acwright/6502/Software/Programs/VH Bricks/README.md

VH Bricks
=========

Displays brick pattern on VERA Layer 0 using the VERA Helper.

Inspired By / Modifed From: [https://www.8bitcoding.com/p/tiles-in-assembly-i-basics.html](https://www.8bitcoding.com/p/tiles-in-assembly-i-basics.html)

Install:

    brew install cc65

Build:

    make

View:

    make view
