acwright/6502/Software/Carts/SC Echo Flow Control/README.md

SC Echo Interrupt
=================

Serial Card echo example using interrupts.

Install:

    brew install cc65

Build:

    make

View:

    make view

Burn EEPROM:

    make eeprom
