acwright/6502/Software/Carts/IB SNES Transmit/README.md

IB SNES Transmit
================

Transmits raw SNES controller data from Input Board to Serial Card.

Adapted from: [https://www.pagetable.com/?p=1365](https://www.pagetable.com/?p=1365)

Install:

    brew install cc65

Build:

    make

View:

    make view

Burn EEPROM:

    make eeprom
