acwright/6502/Software/Carts/IB Mouse Transmit/README.md

IB Mouse Transmit
=================

Transmits raw PS/2 mouse data from Input Board to Serial Card.

Install:

    brew install cc65

Build:

    make

View:

    make view

Burn EEPROM:

    make eeprom
