acwright/6502/Software/Carts/IB Keyboard Transmit/README.md

IB Keyboard Transmit
====================

Transmits raw PS/2 keyboard scancodes from Input Board to Serial Card.

Install:

    brew install cc65

Build:

    make

View:

    make view

Burn EEPROM:

    make eeprom
