acwright/6502/Assets/Documents/Keypad Mapping/Keypad Mapping.pdf

## 6502 KeyPAD MAPPING

| PA4 | PA3 | PA2 | PA1 | PA0 | Key
$00 | 0 | 0 | 0 | 0 | 0 | ◀
$01 | 0 | 0 | 0 | 0 | 1 | 1
$02 | 0 | 0 | 0 | 1 | 0 | 2
$03 | O | 0 | 0 | 1 | 1 | 3
$04 | 0 | 0 | 1 | 0 | 0 | 4
$05 | 0 | 0 | 1 | 0 | 1 | 5
$06 | 0 | 0 | 1 | 1 | 0 | 6
$07 | 0 | 0 | 1 | 1 | 1 | 7
$08 | 0 | 1 | 0 | 0 | 0 | 8
$09 | 0 | 1 | 0 | 0 | 1 | 9
$0A | 0 | 1 | 0 | 1 | 0 | 0
$0B | 0 | 1 | 0 | 1 | 1 | ▶
$0C | 0 | 1 | 1 | 0 | 0 | F
$0D | 0 | 1 | 1 | 0 | 1 | E
$0E | 0 | 1 | 1 | 1 | 0 | D
$0F | 0 | 1 | 1 | 1 | 1 | C
$10 | 1 | 0 | 0 | 0 | 0 | Esc
$11 | 1 | 0 | 0 | 0 | 1 | Ins
$12 | 1 | 0 | 0 | 1 | 0 | pgup
$13 | 1 | 0 | 0 | 1 | 1 | A
$14 | 1 | 0 | 1 | 0 | 0 | ▲
$15 | 1 | 0 | 1 | 0 | 1 | Del
$16 | 1 | 0 | 1 | 1 | 0 | pgdn
$17 | 1 | 0 | 1 | 1 | 1 | B
