acwright/6502/Assets/Documents/Characters/Character Map.pdf

## 6502 CHARACTER MAP

| 0 | 1 | 2 | 3 | 4 | 5 | 6 | 7 | 8 | 9 | A | B | C | D | E | F

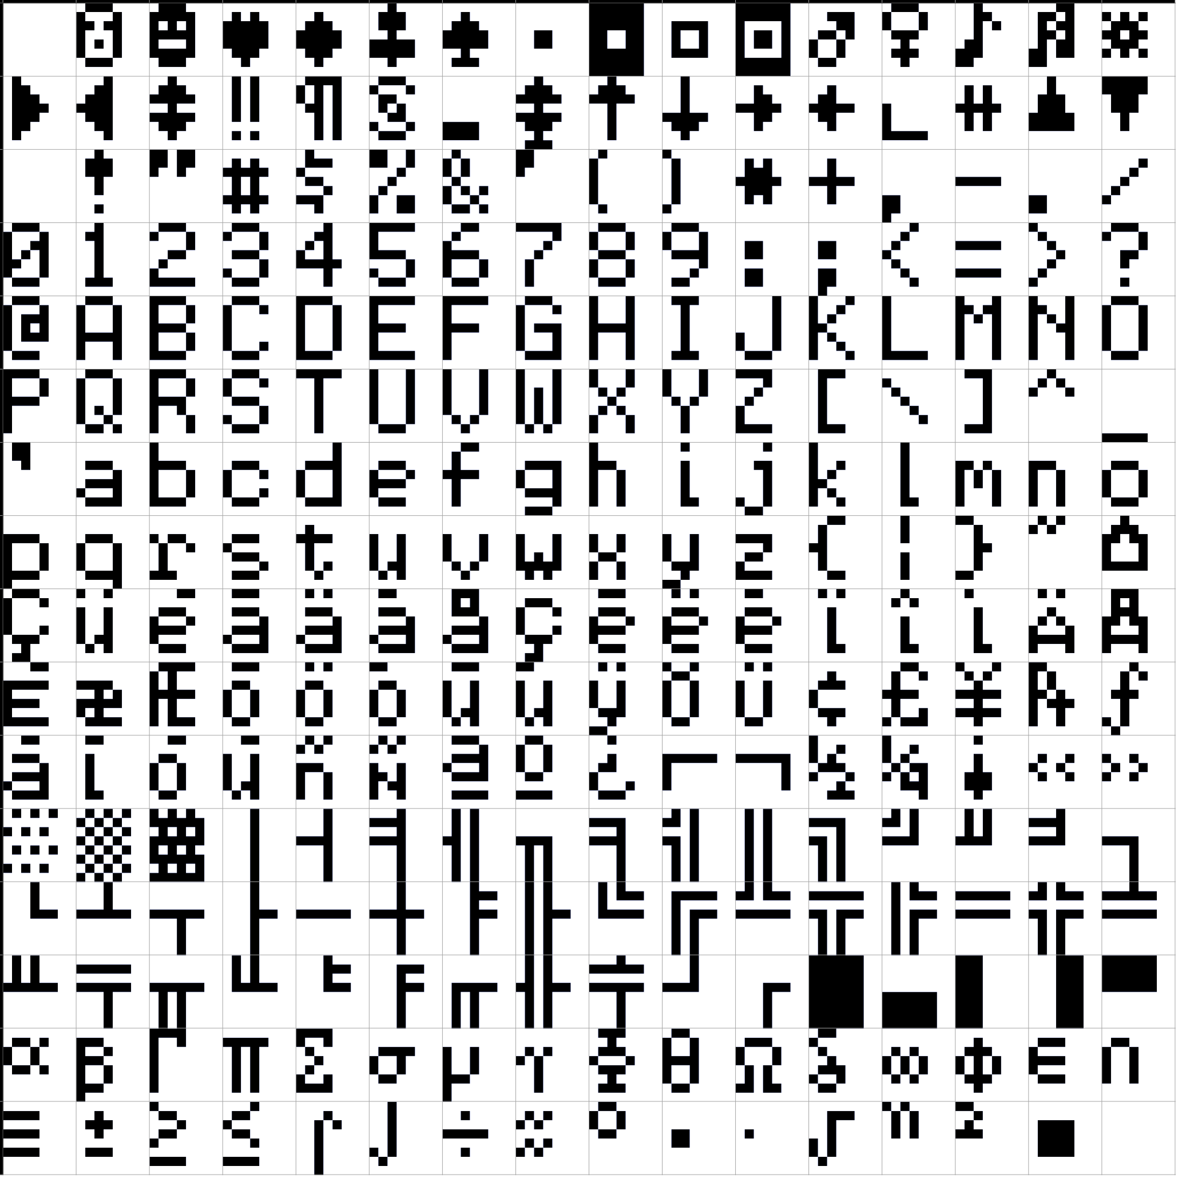
[picture p2: figure]

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
