acwright/6502/Assets/Documents/Characters/Character Set 4x.png

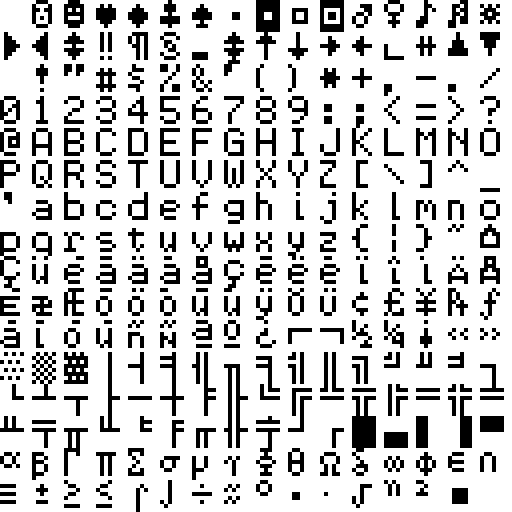
Assets/Documents/Characters/Character Set 4x.png
