acwright/6502/Assets/Documents/Connectors/Connectors.png

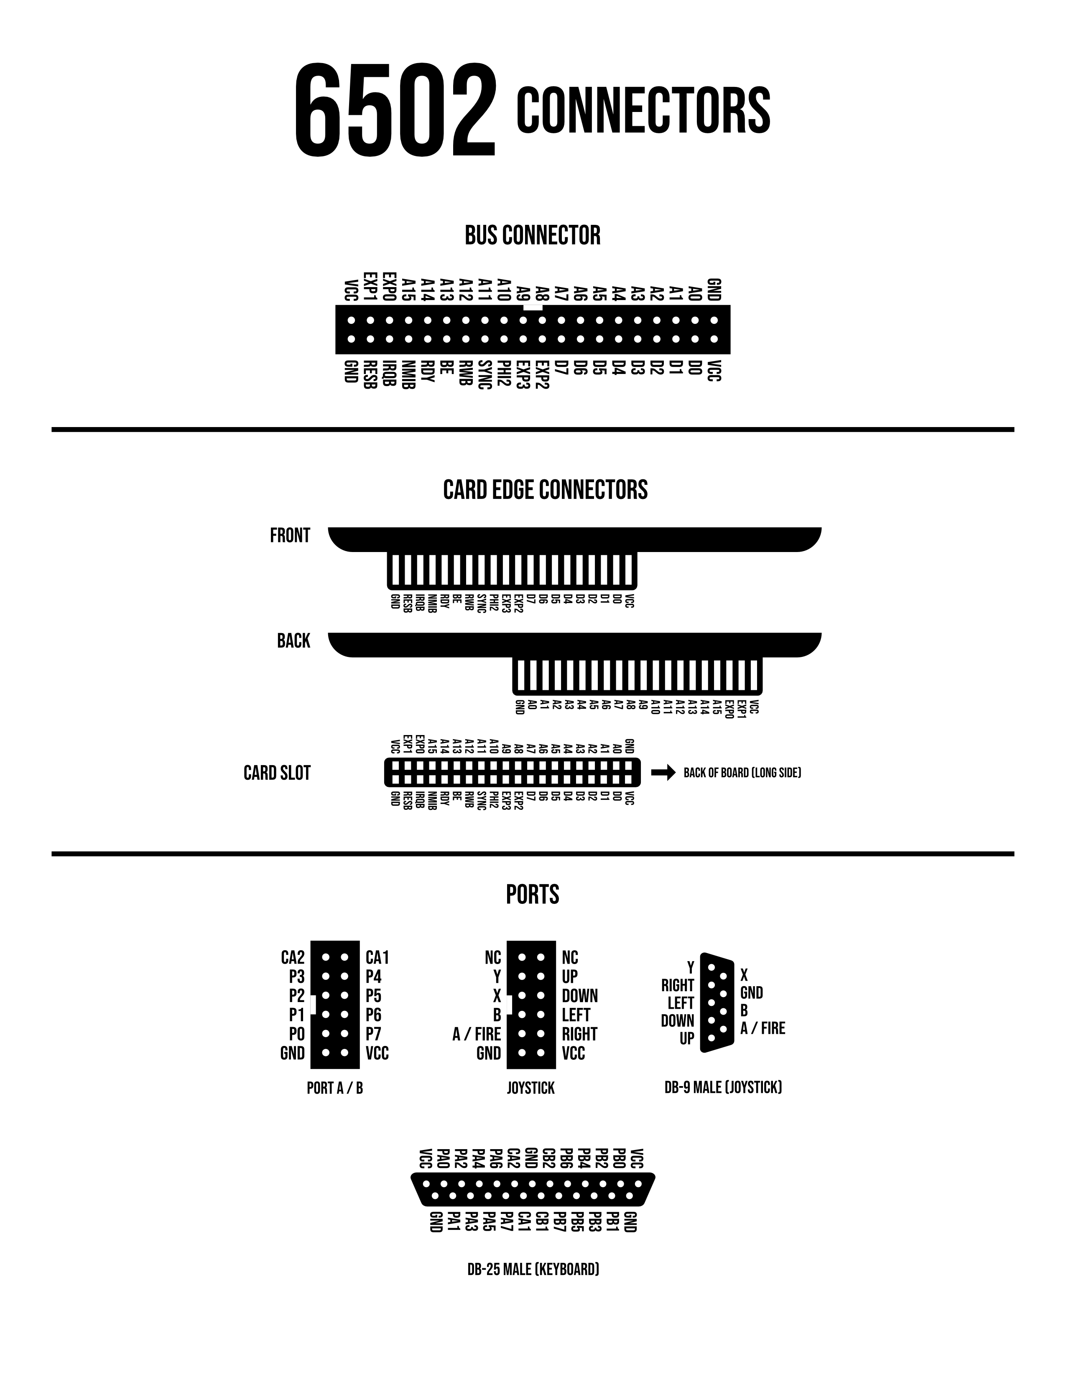
Assets/Documents/Connectors/Connectors.png
