acwright/6502/Assets/Documents/Keyboard Layout/Keyboard Layout.png

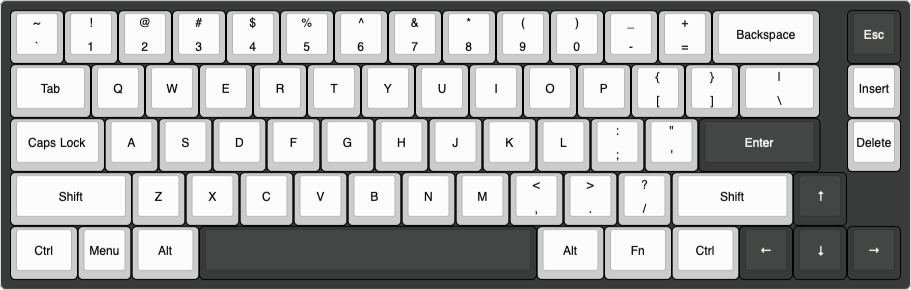
Assets/Documents/Keyboard Layout/Keyboard Layout.png
