acwright/6502/Assets/Documents/Keyboard Matrix/Keyboard Matrix.png

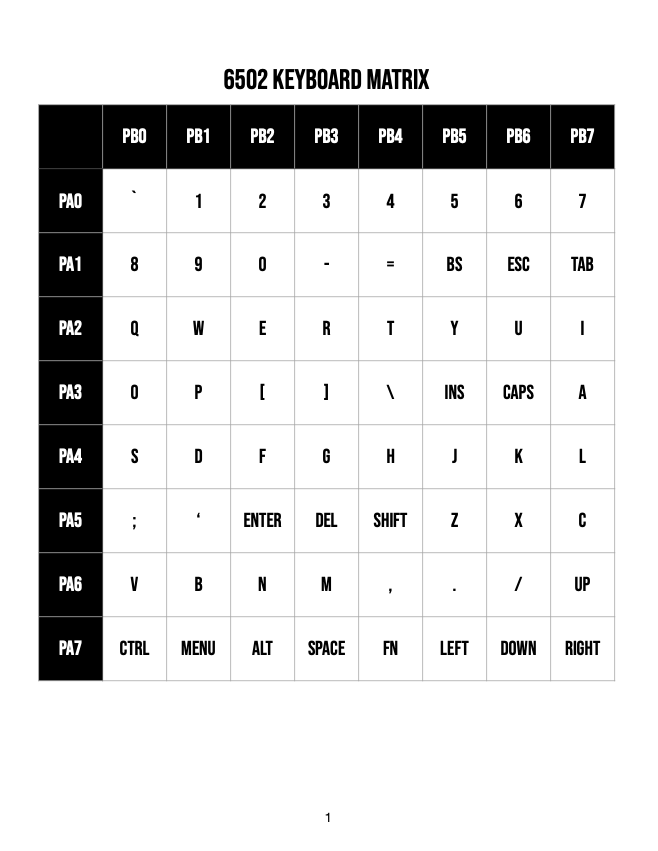
Assets/Documents/Keyboard Matrix/Keyboard Matrix.png
