acwright/6502/Assets/Documents/Keypad Mapping/Keypad Mapping.png

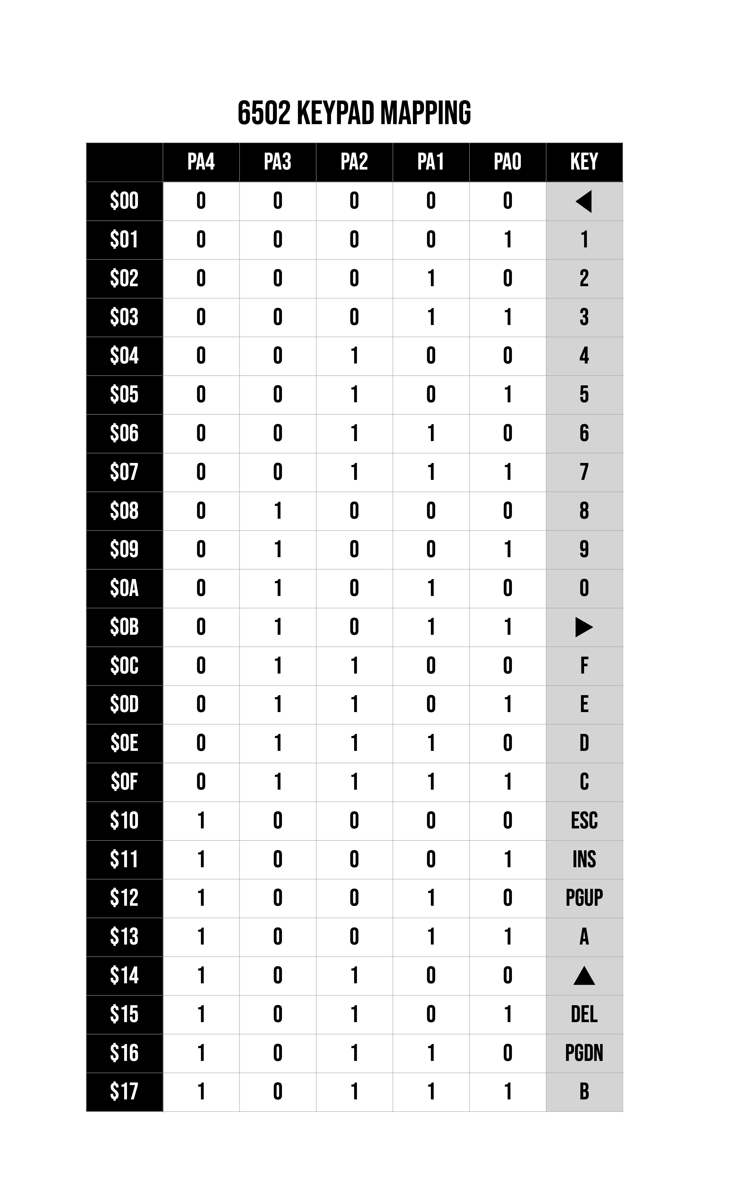
Assets/Documents/Keypad Mapping/Keypad Mapping.png
