acwright/6502/Assets/Documents/Memory Map/Memory Map.png

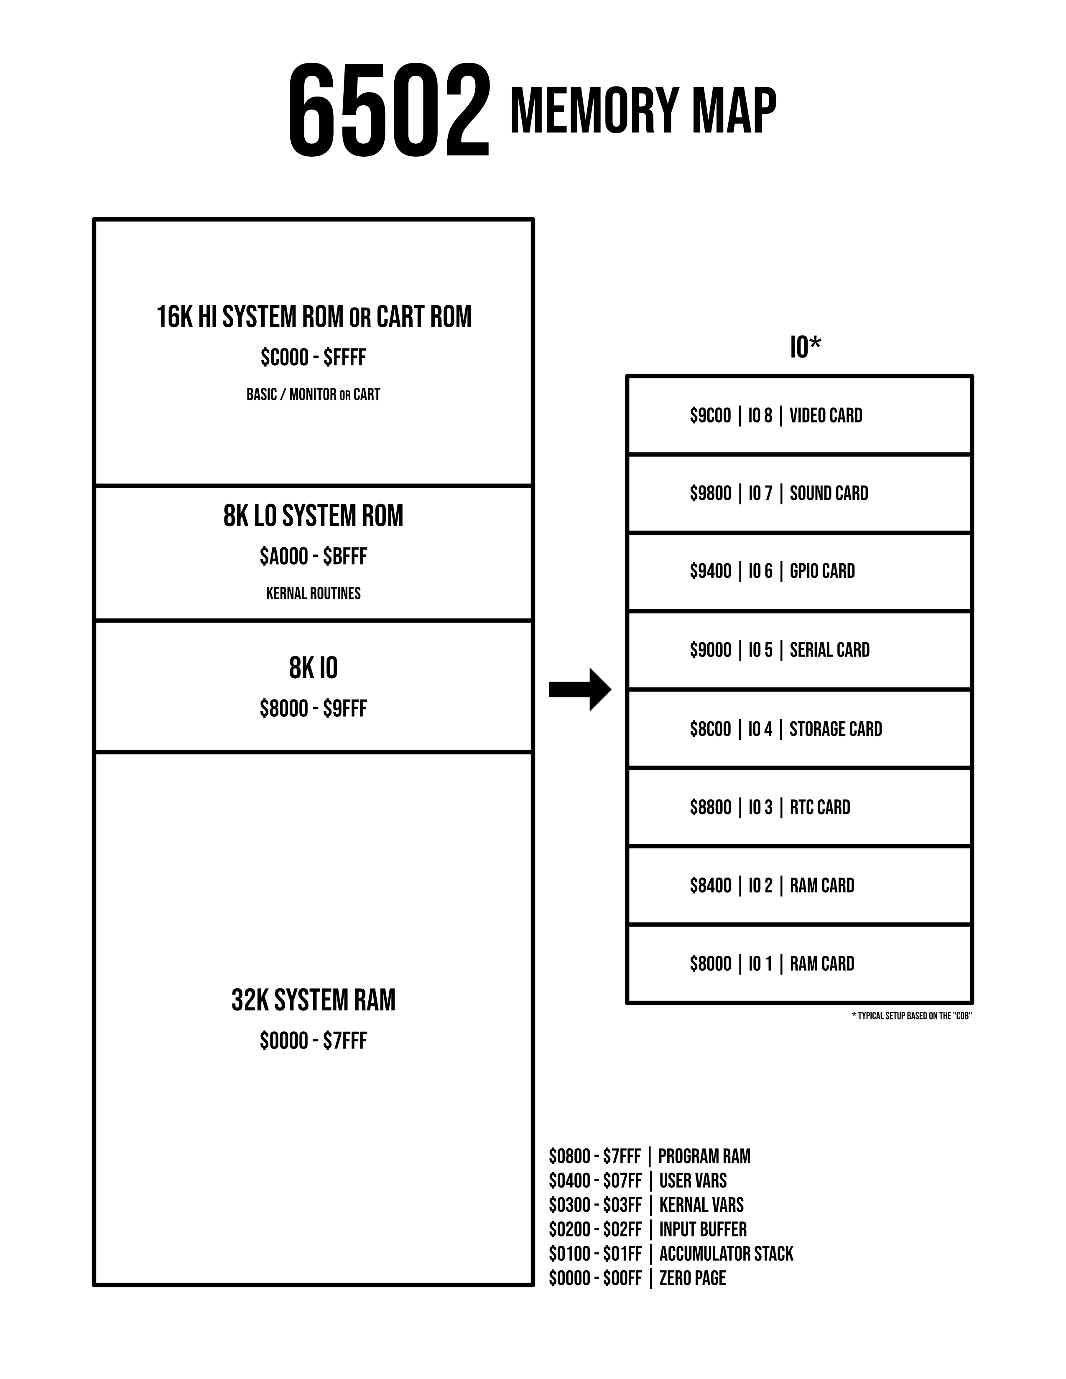
Assets/Documents/Memory Map/Memory Map.png
