acwright/6502/Assets/PCB Images/Clock Helper/Rev 1.0/Front.png

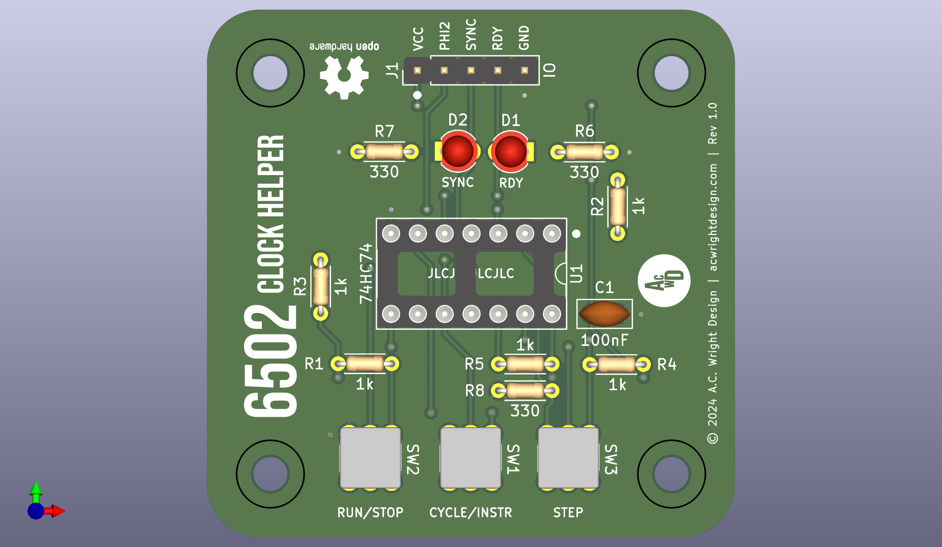
Assets/PCB Images/Clock Helper/Rev 1.0/Front.png
