acwright/6502/Assets/PCB Images/CPU Card/Rev 1.0/Front.png

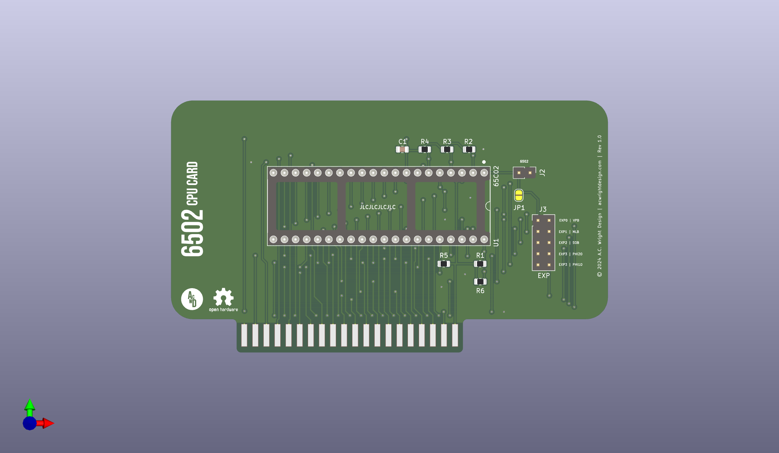
Assets/PCB Images/CPU Card/Rev 1.0/Front.png
