acwright/6502/Assets/PCB Images/DB25 Helper/Rev 1.0/Front.png

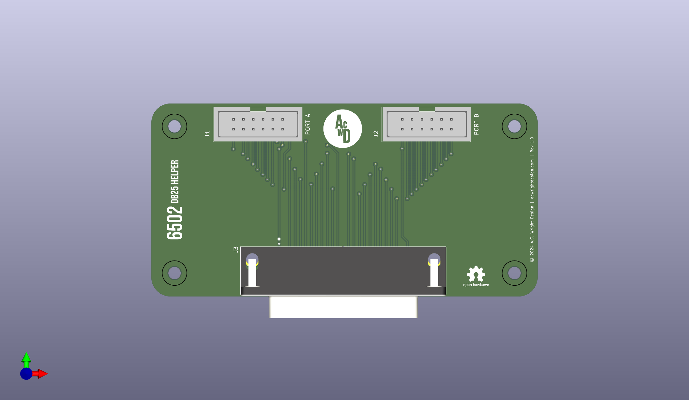
Assets/PCB Images/DB25 Helper/Rev 1.0/Front.png
