acwright/6502/Assets/PCB Images/Dev Output Board/Rev 1.0/Back.png

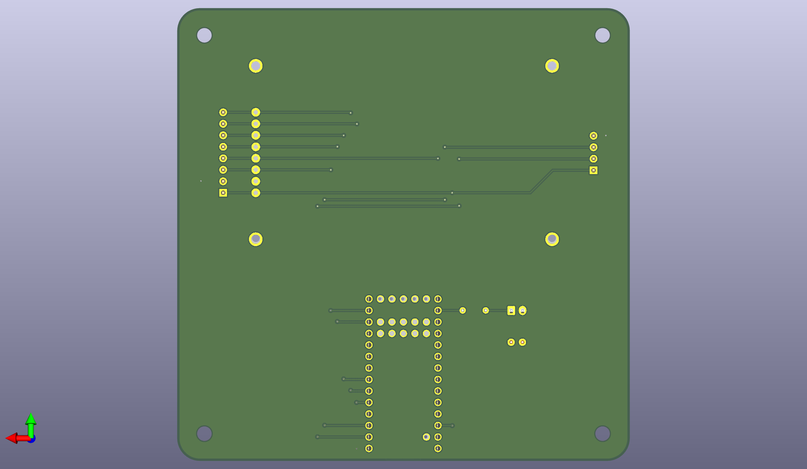
Assets/PCB Images/Dev Output Board/Rev 1.0/Back.png
