acwright/6502/Assets/PCB Images/GPIO Helper/Rev 1.0/Back.png

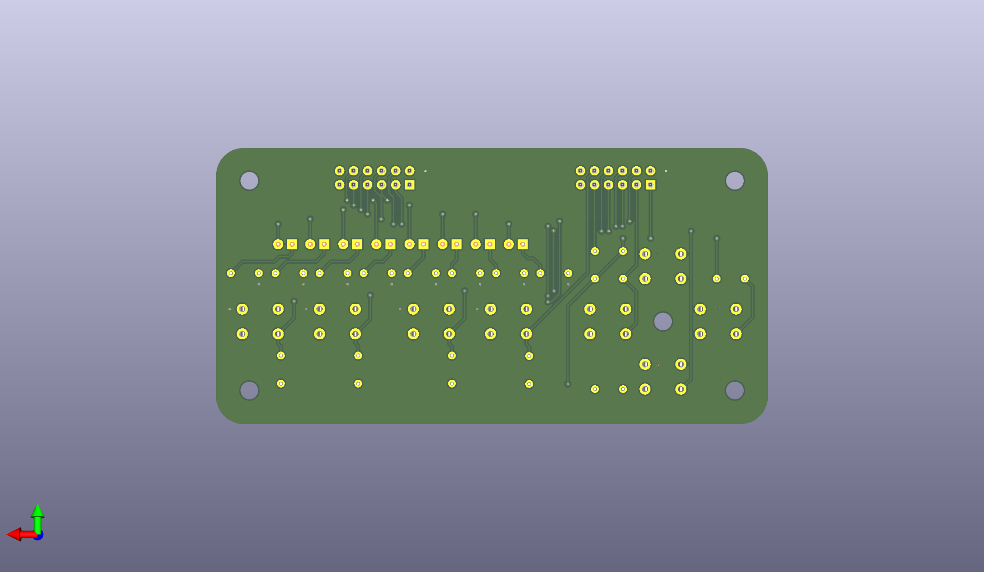
Assets/PCB Images/GPIO Helper/Rev 1.0/Back.png
