acwright/6502/Assets/PCB Images/Input Board/Rev 1.0/Front.png

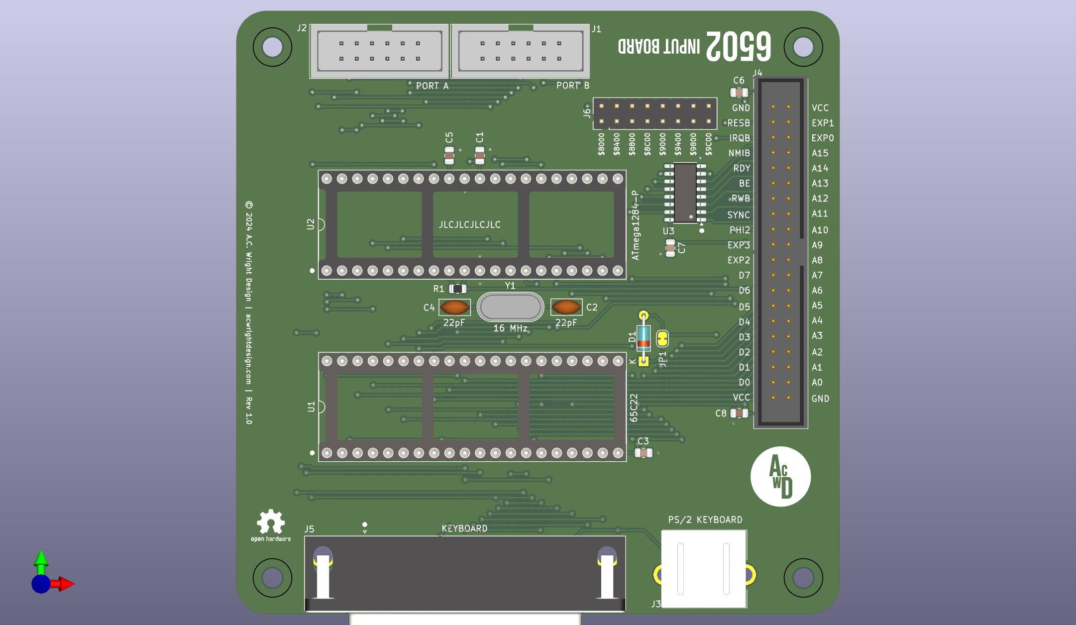
Assets/PCB Images/Input Board/Rev 1.0/Front.png
