acwright/6502/Assets/PCB Images/Joystick Helper/Rev 1.0/Back.png

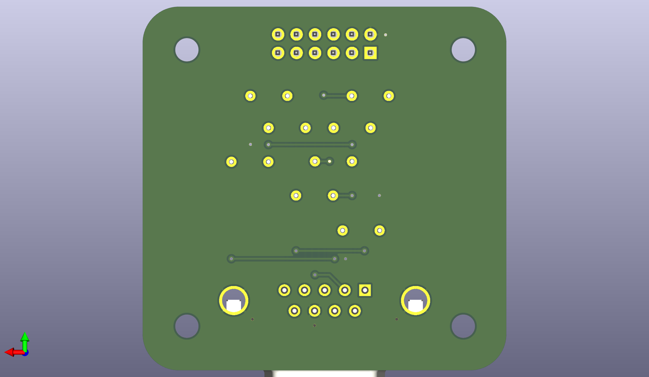
Assets/PCB Images/Joystick Helper/Rev 1.0/Back.png
