acwright/6502/Assets/PCB Images/Keyboard Encoder Helper/Rev 1.0/Back.png

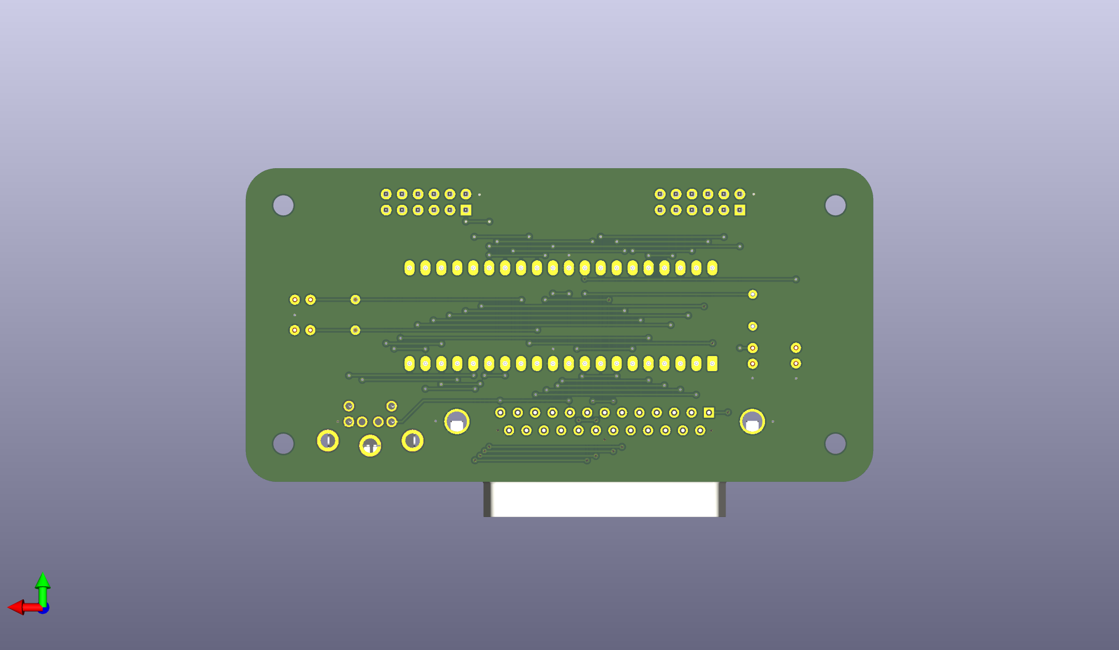
Assets/PCB Images/Keyboard Encoder Helper/Rev 1.0/Back.png
