acwright/6502/Assets/PCB Images/LCD Board/Rev 1.0/Back.png

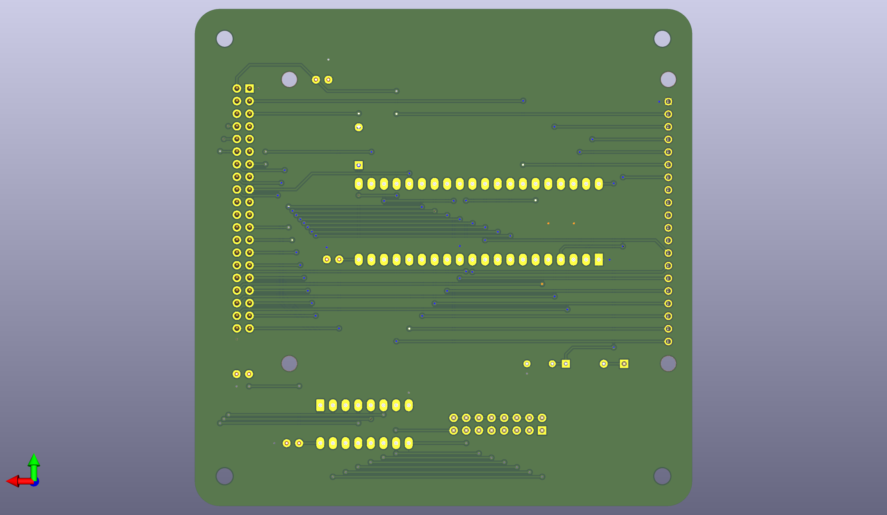
Assets/PCB Images/LCD Board/Rev 1.0/Back.png
