acwright/6502/Assets/PCB Images/Mega Helper/Rev 1.0/Front.png

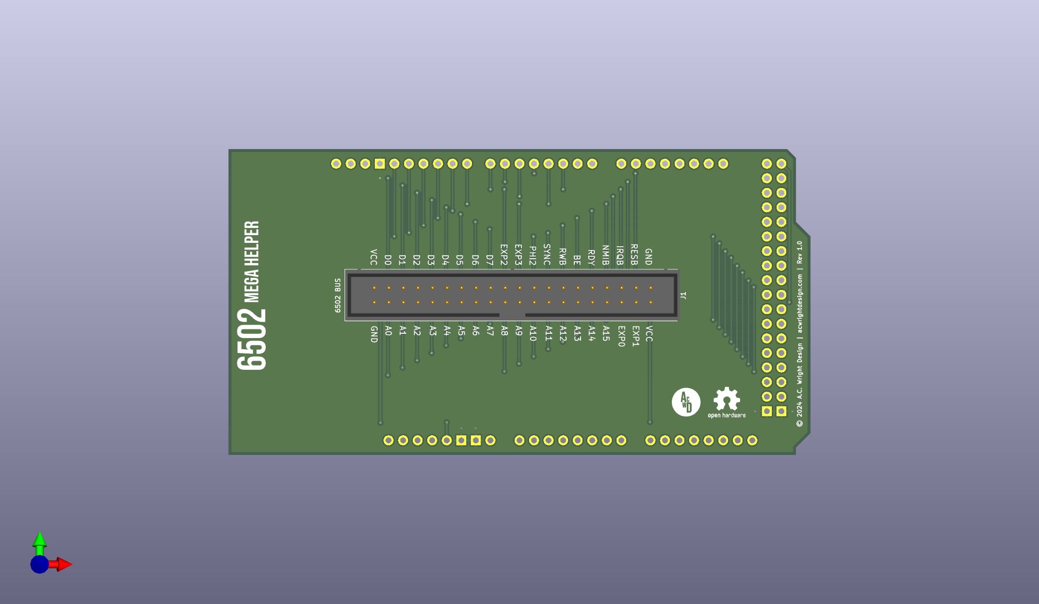
Assets/PCB Images/Mega Helper/Rev 1.0/Front.png
