acwright/6502/Assets/PCB Images/Output Board/Rev 1.0/Front.png

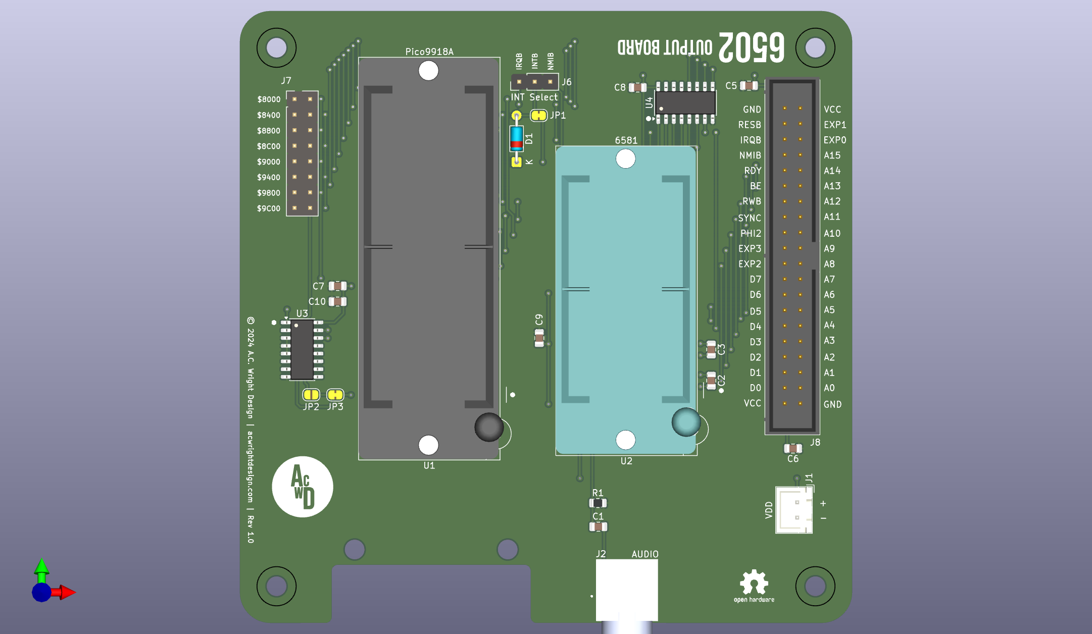
Assets/PCB Images/Output Board/Rev 1.0/Front.png
