acwright/6502/Assets/PCB Images/PS2 Helper/Rev 1.0/Back.png

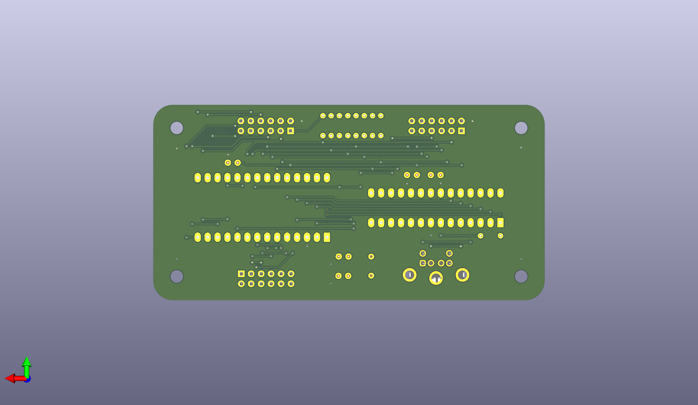
Assets/PCB Images/PS2 Helper/Rev 1.0/Back.png
