acwright/6502/Assets/PCB Images/ROM Cart/Rev 1.0a/Back.png

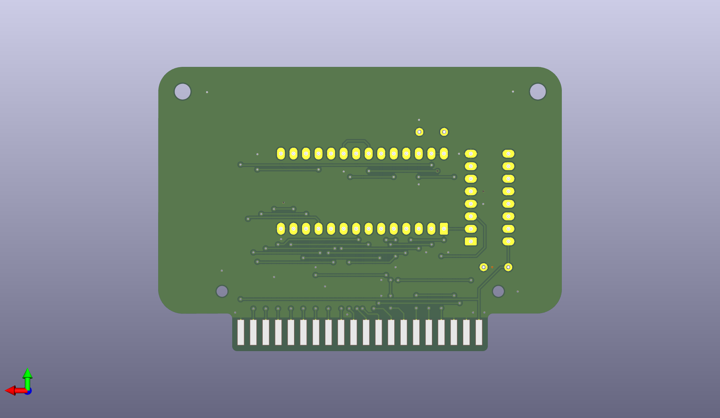
Assets/PCB Images/ROM Cart/Rev 1.0a/Back.png
