acwright/6502/Assets/PCB Images/ROM Cart/Rev 1.0a/Front.png

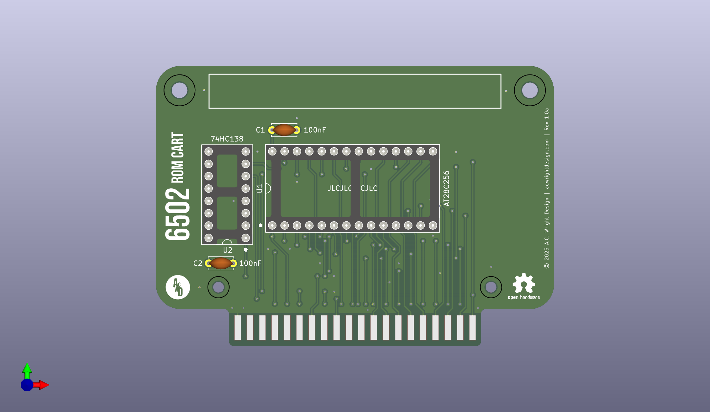
Assets/PCB Images/ROM Cart/Rev 1.0a/Front.png
