acwright/6502/Assets/PCB Images/Sound Card/Rev 1.0/Back.png

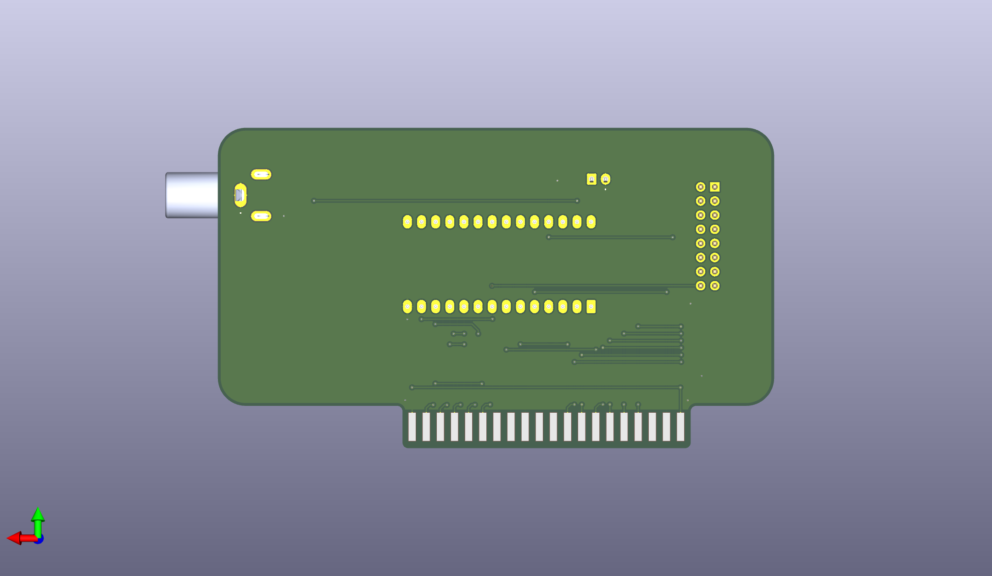
Assets/PCB Images/Sound Card/Rev 1.0/Back.png
