acwright/6502/Assets/PCB Images/Storage Card Pro/Rev 1.0/Back.png

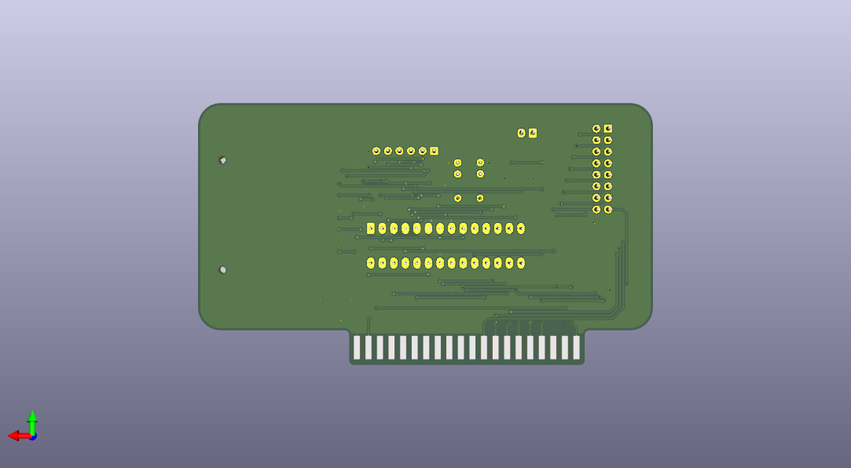
Assets/PCB Images/Storage Card Pro/Rev 1.0/Back.png
