acwright/6502/Assets/PCB Images/Storage Card Pro/Rev 1.0/Front.png

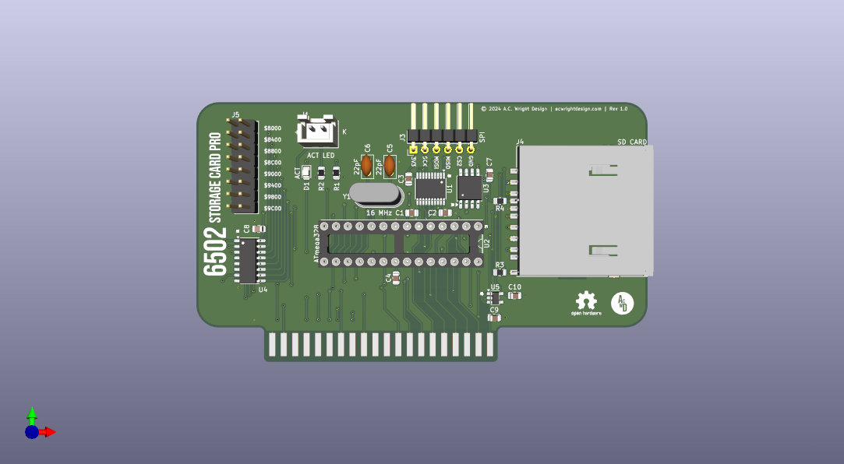
Assets/PCB Images/Storage Card Pro/Rev 1.0/Front.png
