acwright/6502/Assets/PCB Images/VERA Helper/Rev 1.0/Back.png

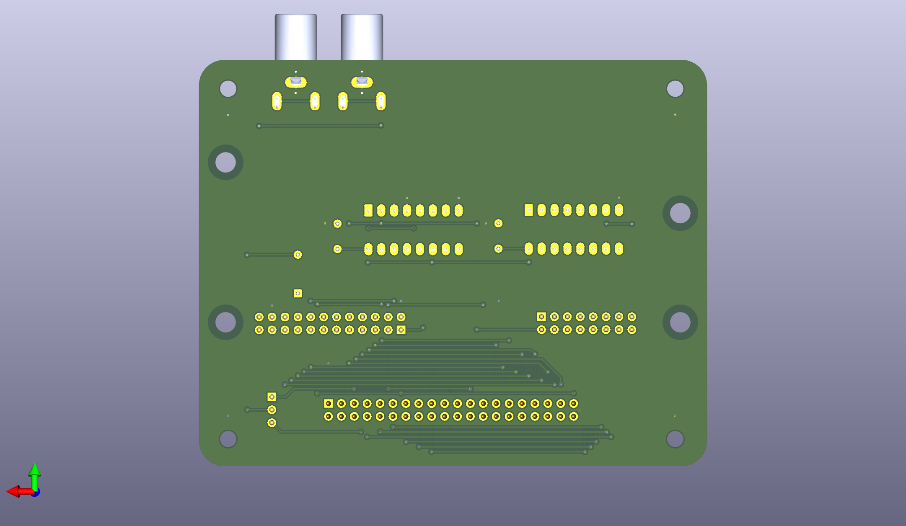
Assets/PCB Images/VERA Helper/Rev 1.0/Back.png
