acwright/6502/Assets/PCB Images/VGA Card/Rev 1.0/Back.png

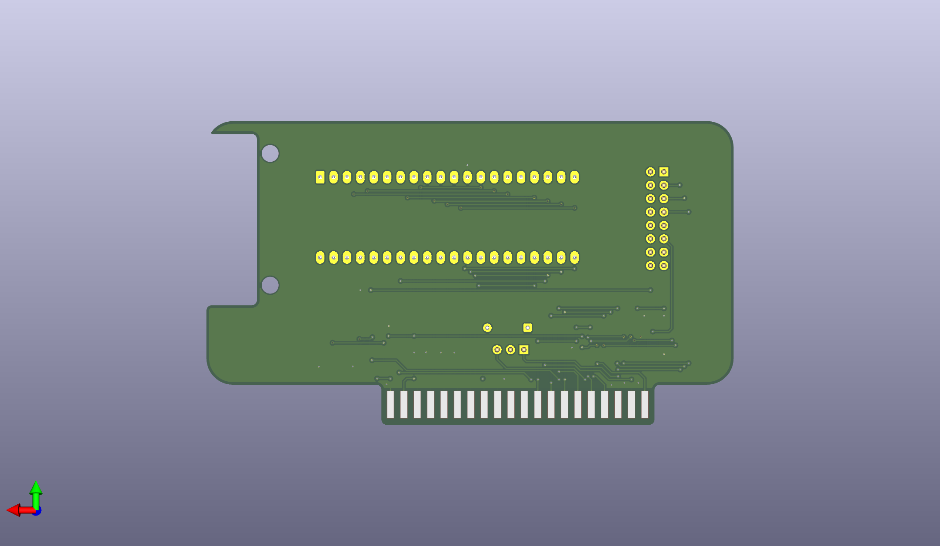
Assets/PCB Images/VGA Card/Rev 1.0/Back.png
