acwright/6502/Assets/PCB Images/Video Card Pro/Rev 1.0/Back.png

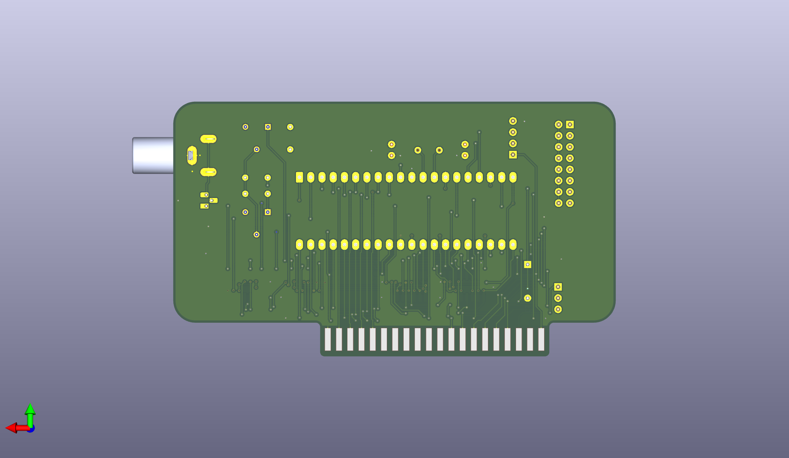
Assets/PCB Images/Video Card Pro/Rev 1.0/Back.png
