acwright/6502/CAD/Enclosures/Clock Helper/Clock Helper Enclosure.png

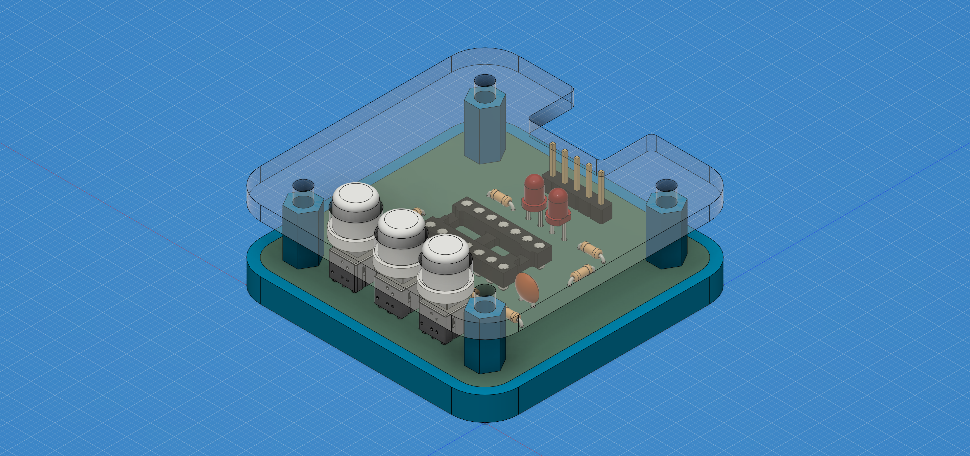
CAD/Enclosures/Clock Helper/Clock Helper Enclosure.png
