acwright/6502/CAD/Enclosures/DB25 Helper/DB25 Helper Enclosure.png

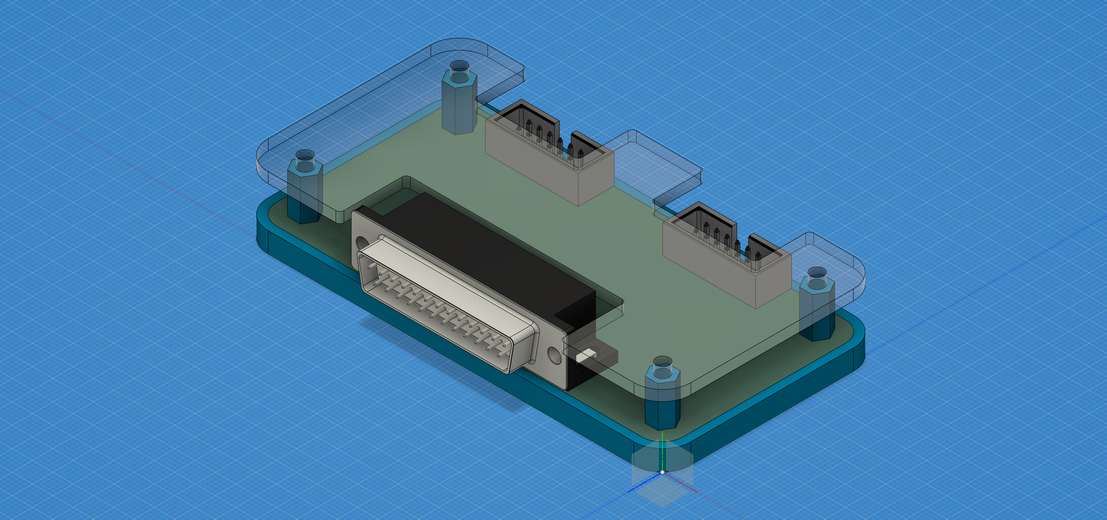
CAD/Enclosures/DB25 Helper/DB25 Helper Enclosure.png
