acwright/6502/CAD/Enclosures/GPIO Helper/GPIO Helper Enclosure.png

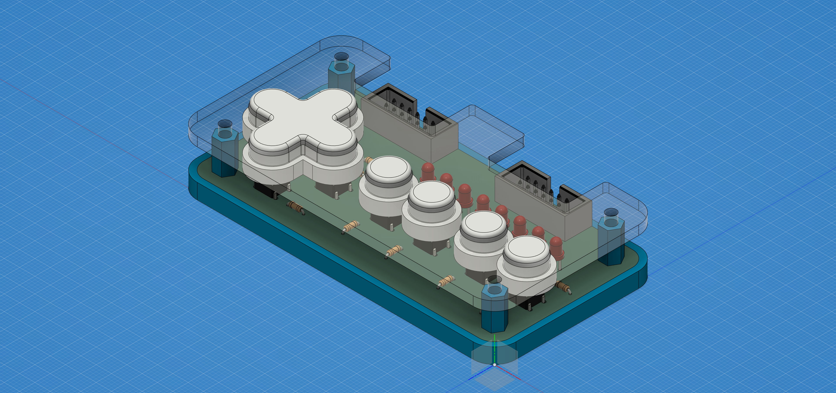
CAD/Enclosures/GPIO Helper/GPIO Helper Enclosure.png
