acwright/6502/CAD/Enclosures/Joystick Helper/Joystick Helper Enclosure.png

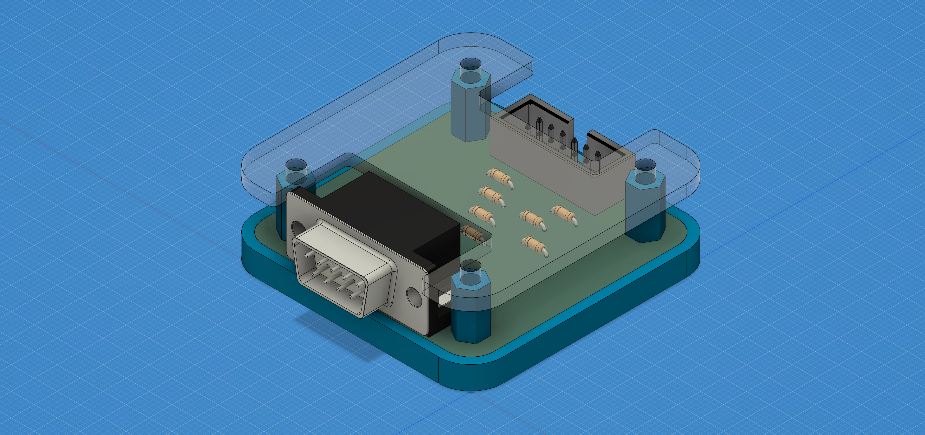
CAD/Enclosures/Joystick Helper/Joystick Helper Enclosure.png
