acwright/6502/CAD/Enclosures/Keyboard Helper/Keyboard Helper Enclosure.png

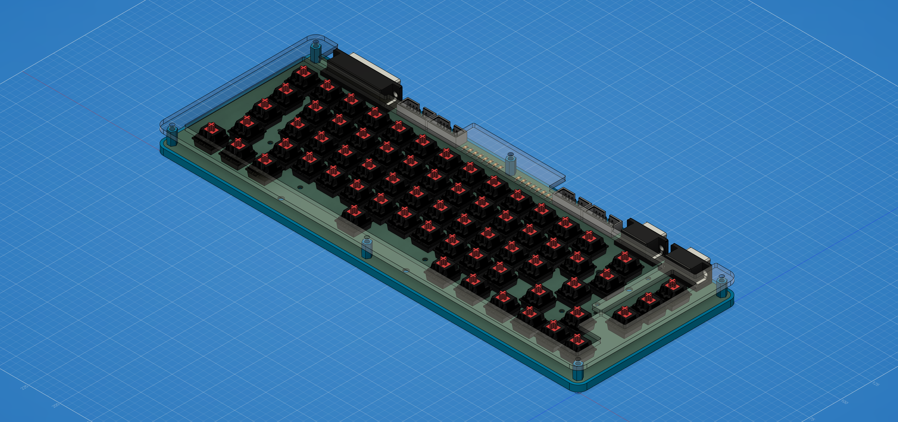
CAD/Enclosures/Keyboard Helper/Keyboard Helper Enclosure.png
