acwright/6502/CAD/Enclosures/Keypad Helper/Keypad Helper Enclosure.png

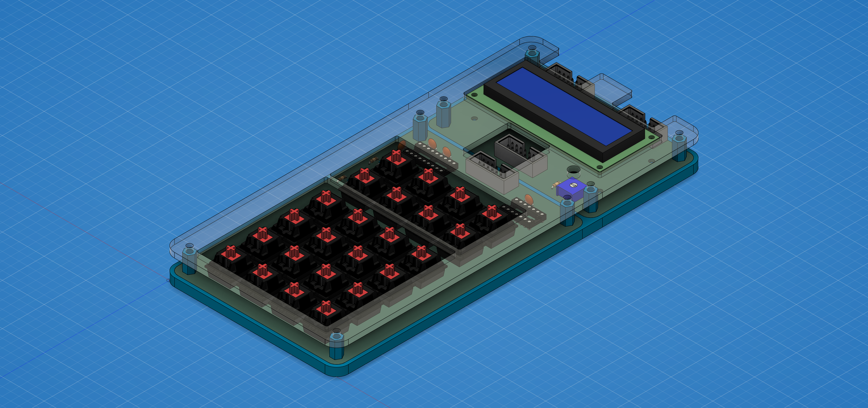
CAD/Enclosures/Keypad Helper/Keypad Helper Enclosure.png
