acwright/6502/CAD/Enclosures/PS2 Helper/PS2 Helper Enclosure.png

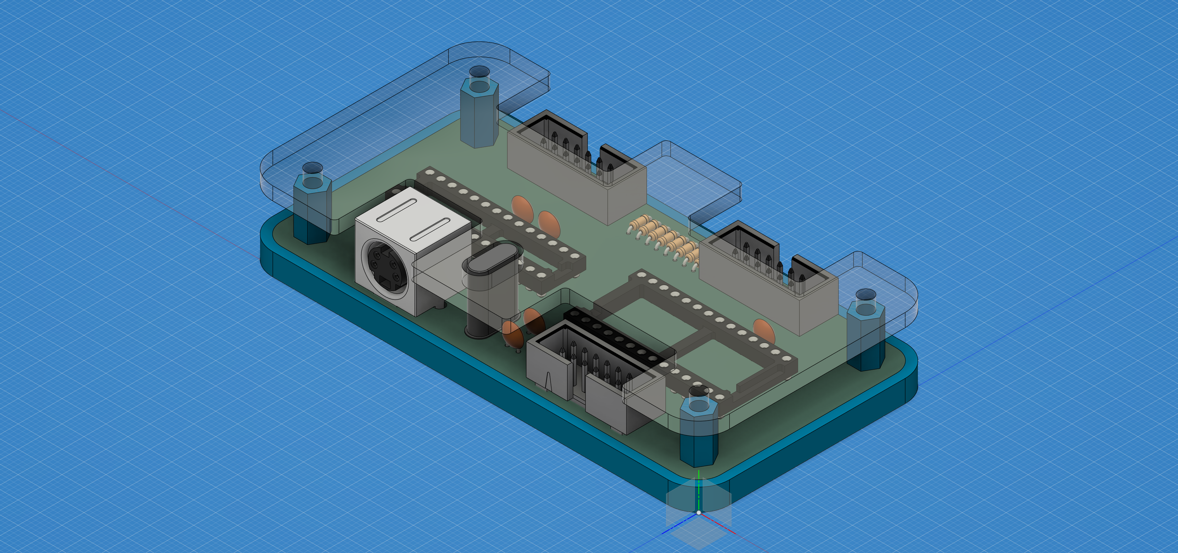
CAD/Enclosures/PS2 Helper/PS2 Helper Enclosure.png
