acwright/6502/Assets/PCB Models/Keyboard Encoder Helper/Rev 1.0/Keyboard Encoder Helper.step

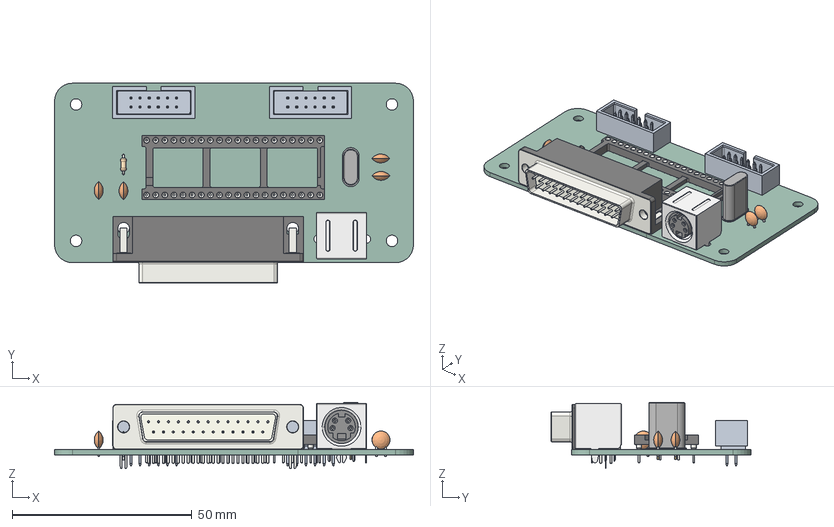
[picture p69: CAD file, 2026-01-31]
Assets/PCB Models/Keyboard Encoder Helper/Rev 1.0/Keyboard Encoder Helper.step
100.0 x 55.6 x 18.5 mm
R_Axial_DIN0204_L3.6mm_D1.6mm_P5.08mm_Horizontal
Crystal_HC49-U_Vertical
DIP-40_W15.24mm_Socket
C_Disc_D5.0mm_W2.5mm_P2.50mm x 4
DSUB-25_Pins_Horizontal_P2.77x2.84mm_EdgePinOffset7.70mm_Housed_ MountingHolesOffset9.12mm
KMDGX-6S-BS
Keyboard Encoder Helper_PCB
