acwright/6502/Assets/PCB Models/Keyboard Helper/Rev 1.0/Keyboard Helper.step

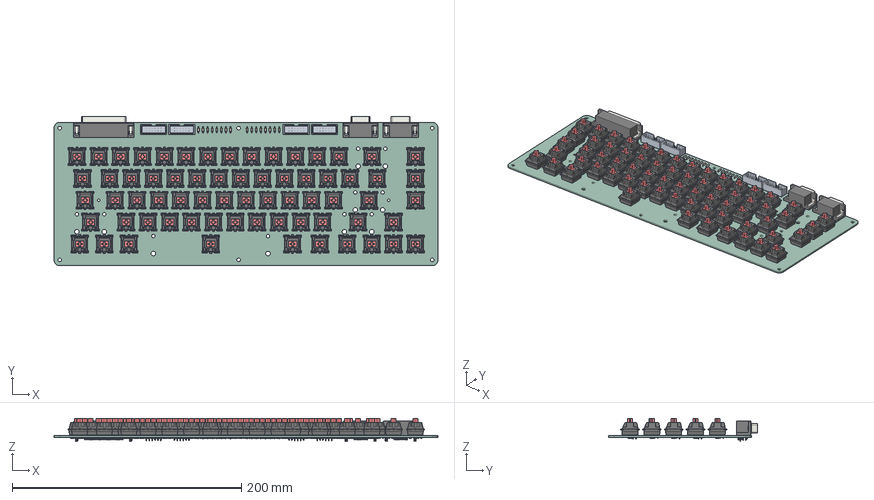
[picture p70: CAD file, 2025-10-27]
Assets/PCB Models/Keyboard Helper/Rev 1.0/Keyboard Helper.step
335.0 x 130.2 x 20.3 mm
R_Axial_DIN0204_L3.6mm_D1.6mm_P5.08mm_Horizontal x 16
DSUB-25_Pins_Horizontal_P2.77x2.84mm_EdgePinOffset7.70mm_Housed_ MountingHolesOffset9.12mm
DSUB-9_Pins_Horizontal_P2.77x2.84mm_EdgePinOffset7.70mm_Housed_ MountingHolesOffset9.12mm x 2
Keyboard Helper_PCB
