acwright/6502/Assets/PCB Models/Keypad Helper/Rev 1.0/Keypad Helper.step

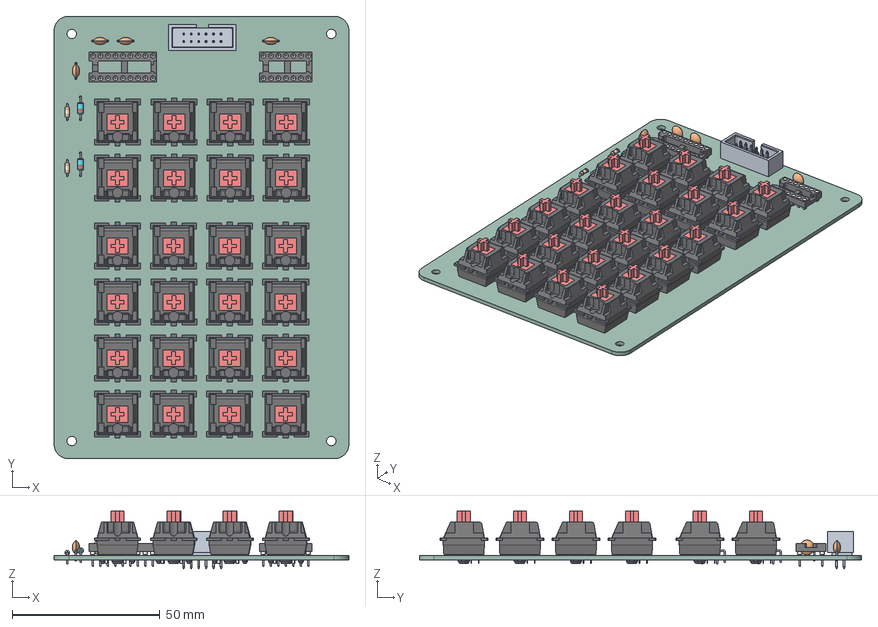
[picture p71: CAD file, 2025-09-09]
Assets/PCB Models/Keypad Helper/Rev 1.0/Keypad Helper.step
100.0 x 150.0 x 19.6 mm
DIP-14_W7.62mm_Socket
D_DO-35_SOD27_P7.62mm_Horizontal x 2
R_Axial_DIN0204_L3.6mm_D1.6mm_P5.08mm_Horizontal x 2
C_Disc_D5.0mm_W2.5mm_P5.00mm x 4
DIP-18_W7.62mm_Socket
Keypad Helper_PCB
