acwright/6502/Assets/PCB Models/Keypad LCD Helper/Rev 1.0/Keypad LCD Helper.step

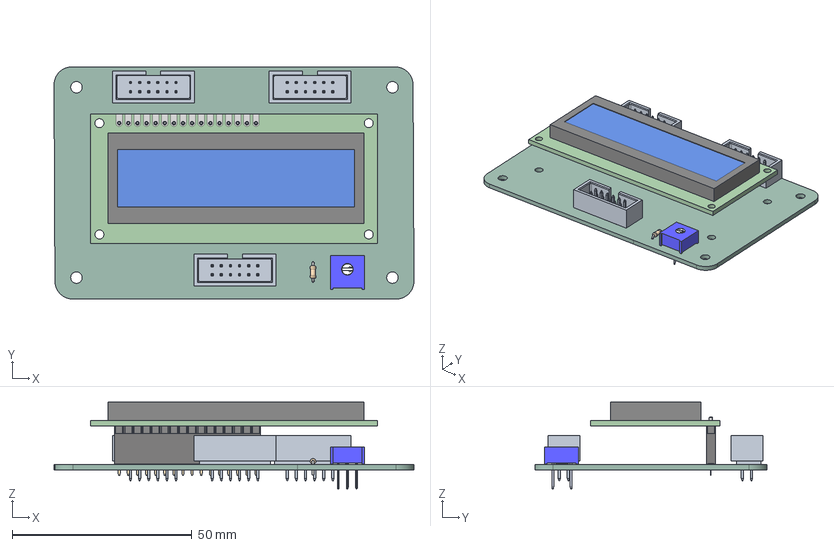
[picture p72: CAD file, 2025-10-06]
Assets/PCB Models/Keypad LCD Helper/Rev 1.0/Keypad LCD Helper.step
100.3 x 64.7 x 24.2 mm
lcd 16_2 HD44780
dupont_pin_16
PinSocket_1x16_P2.54mm_Vertical
R_Axial_DIN0204_L3.6mm_D1.6mm_P5.08mm_Horizontal
3386F-1-103LF
Keypad LCD Helper_PCB
