acwright/6502/Assets/PCB Models/Mega Helper/Rev 1.0/Mega Helper.step

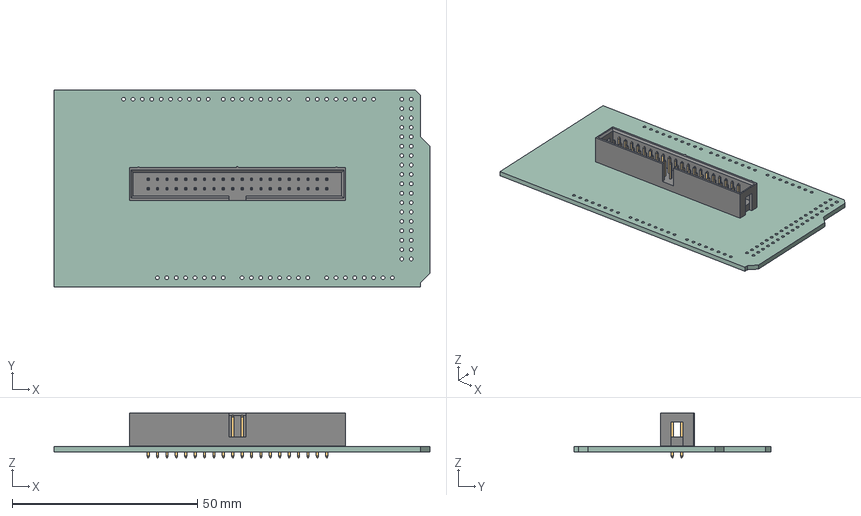
[picture p74: CAD file, 2026-01-11]
Assets/PCB Models/Mega Helper/Rev 1.0/Mega Helper.step
101.6 x 53.3 x 12.1 mm
6120xx21621_PIN x 40
Mega Helper_PCB
