acwright/6502/Assets/PCB Models/Output Board/Rev 1.0/Output Board.step

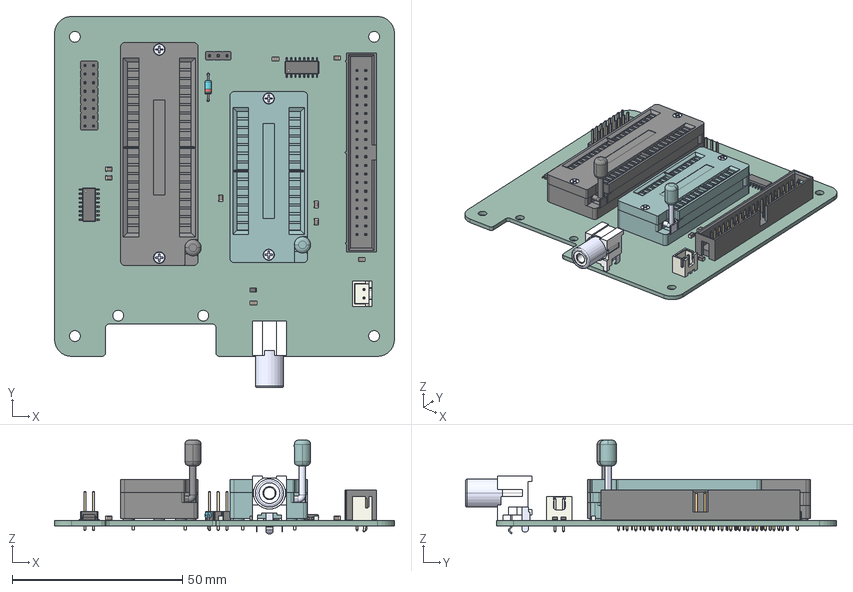
[picture p75: CAD file, 2026-01-14]
Assets/PCB Models/Output Board/Rev 1.0/Output Board.step
100.0 x 109.1 x 27.6 mm
C_0805_2012Metric x 9
SOIC-16_3.9x9.9mm_P1.27mm x 2
R_0805_2012Metric
JST_XH_B2B-XH-A_1x02_P2.50mm_Vertical
PJRAN1X1U04X-edit
PinHeader_1x03_P2.54mm_Vertical
240-1280-00-0602J
PinHeader_2x08_P2.54mm_Vertical
228-1277-00-0602J
6120xx21621_PIN x 40
D_DO-35_SOD27_P7.62mm_Horizontal
Output Board_PCB
