acwright/6502/Assets/PCB Models/RAM Card/Rev 1.0/RAM Card.step

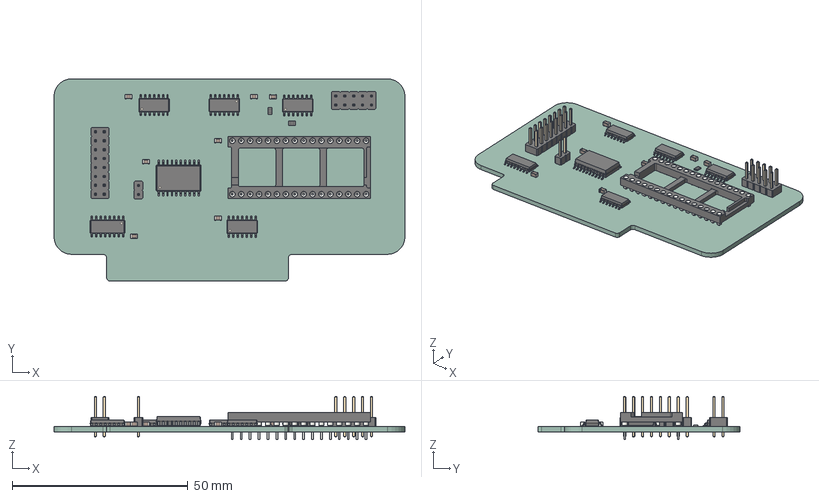
[picture p77: CAD file, 2025-10-28]
Assets/PCB Models/RAM Card/Rev 1.0/RAM Card.step
100.0 x 57.6 x 12.3 mm
C_0805_2012Metric x 7
SOIC-14_3.9x8.7mm_P1.27mm x 4
PinHeader_2x08_P2.54mm_Vertical
R_0805_2012Metric x 2
SOIC-20W_7.5x12.8mm_P1.27mm
DIP-32_W15.24mm_Socket
PinHeader_1x02_P2.54mm_Vertical
SOIC-16_3.9x9.9mm_P1.27mm
PinHeader_2x05_P2.54mm_Vertical
RAM Card_PCB
