acwright/6502/Assets/PCB Models/ROM Cart/Rev 0.0/ROM Cart.step

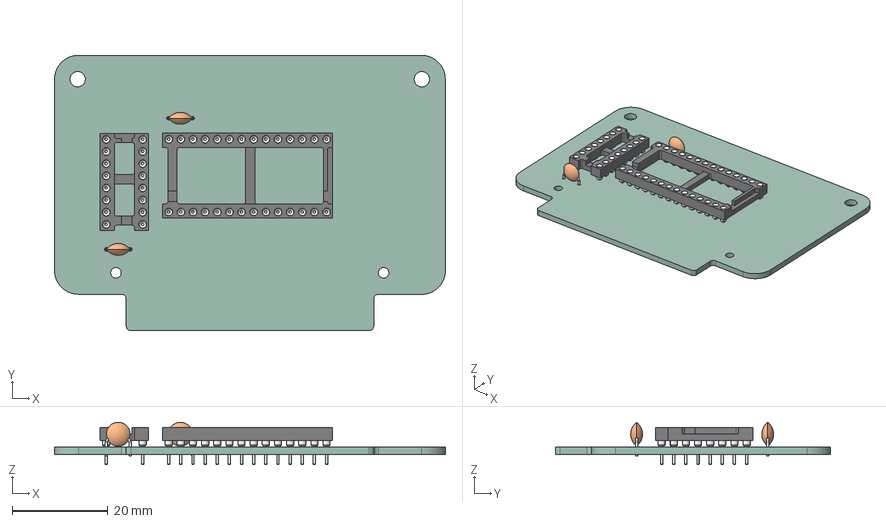
[picture p78: CAD file, 2025-09-26]
Assets/PCB Models/ROM Cart/Rev 0.0/ROM Cart.step
81.8 x 57.6 x 8.88 mm
DIP-16_W7.62mm_Socket
C_Disc_D5.0mm_W2.5mm_P5.00mm x 2
DIP-28_W15.24mm_Socket
ROM Cart_PCB
