acwright/6502/CAD/Bases/The COB/Button.3mf

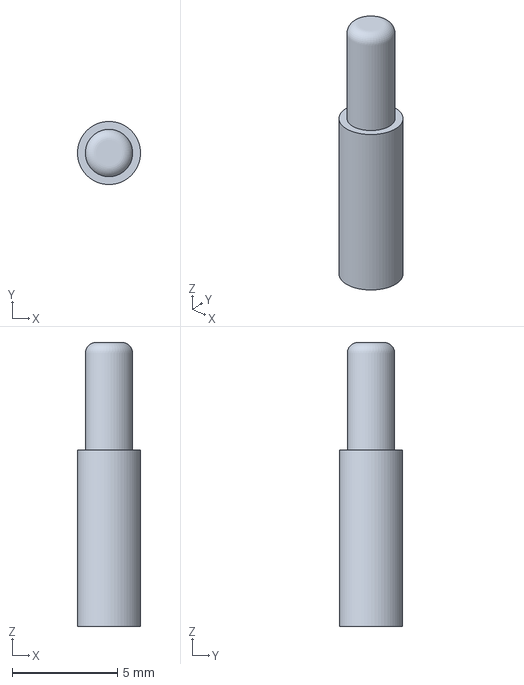
[picture p86: CAD file, 2026-02-03]
CAD/Bases/The COB/Button.3mf
3.00 x 3.00 x 13.5 mm
