acwright/6502/CAD/Bases/The DEV/Buttons.3mf

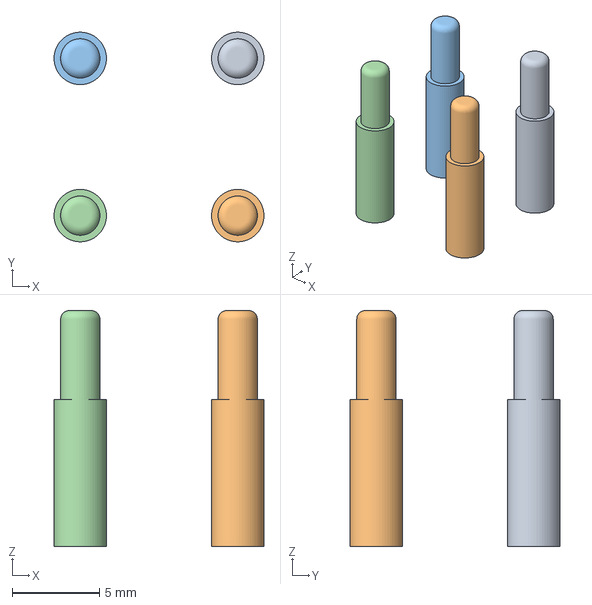
[picture p87: CAD file, 2026-02-03]
CAD/Bases/The DEV/Buttons.3mf
12.0 x 12.0 x 13.5 mm
