acwright/6502/CAD/Bases/The KIM/Hanger Retainer.stl

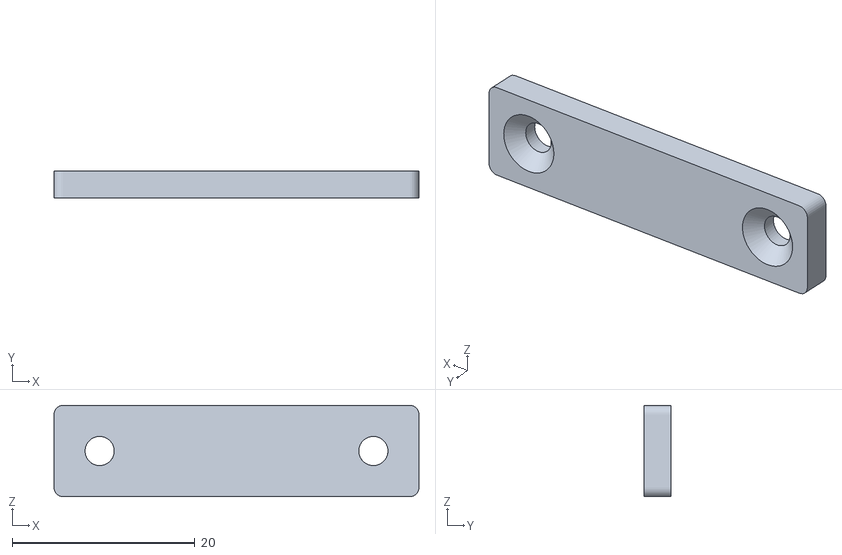
[picture p88: CAD file, 2026-02-03]
CAD/Bases/The KIM/Hanger Retainer.stl
40.0 x 3.00 x 10.0
