acwright/6502/CAD/Card/Card.stl

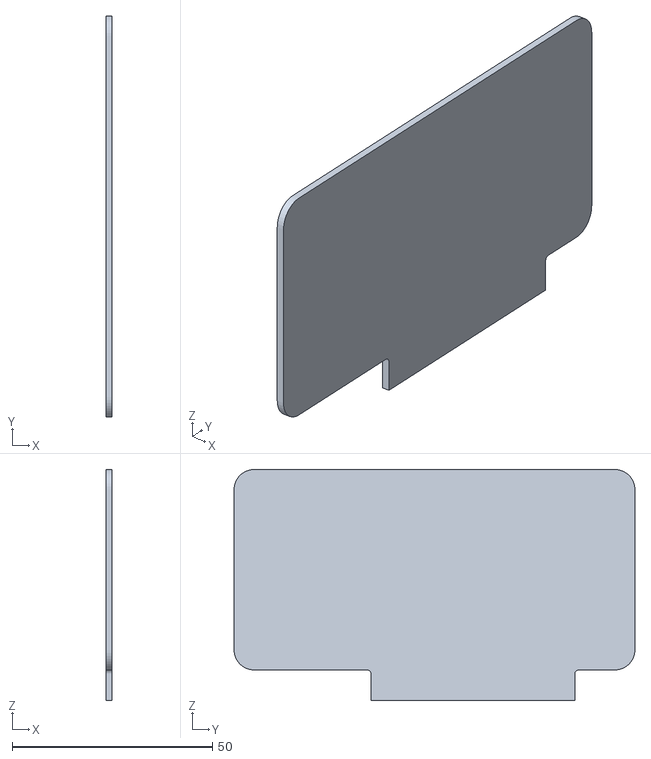
[picture p89: CAD file, 2021-03-25]
CAD/Card/Card.stl
1.60 x 100.0 x 57.6
