acwright/6502/CAD/Enclosures/Clock Helper/Base.3mf

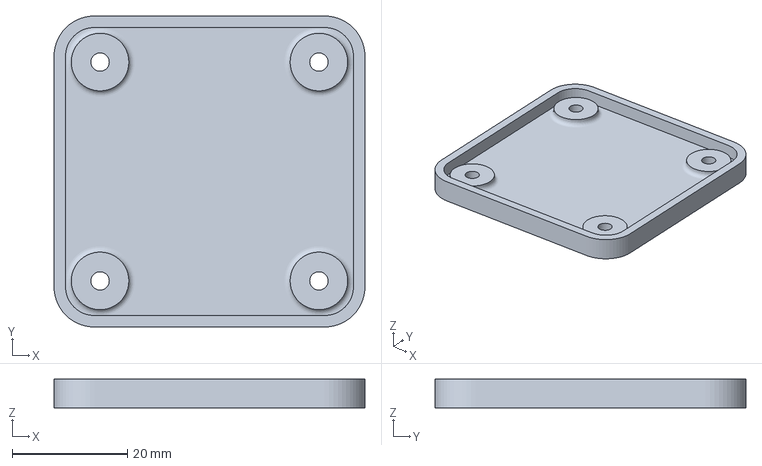
[picture p90: CAD file, 2026-02-07]
CAD/Enclosures/Clock Helper/Base.3mf
54.0 x 54.0 x 5.00 mm
