acwright/6502/CAD/Enclosures/DB25 Helper/Base.3mf

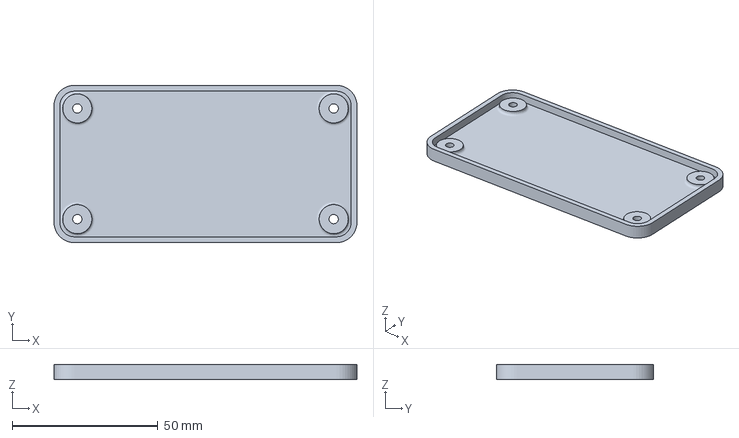
[picture p91: CAD file, 2026-02-07]
CAD/Enclosures/DB25 Helper/Base.3mf
104.0 x 54.0 x 5.00 mm
