acwright/6502/CAD/Enclosures/Keyboard Helper/Base Right.3mf

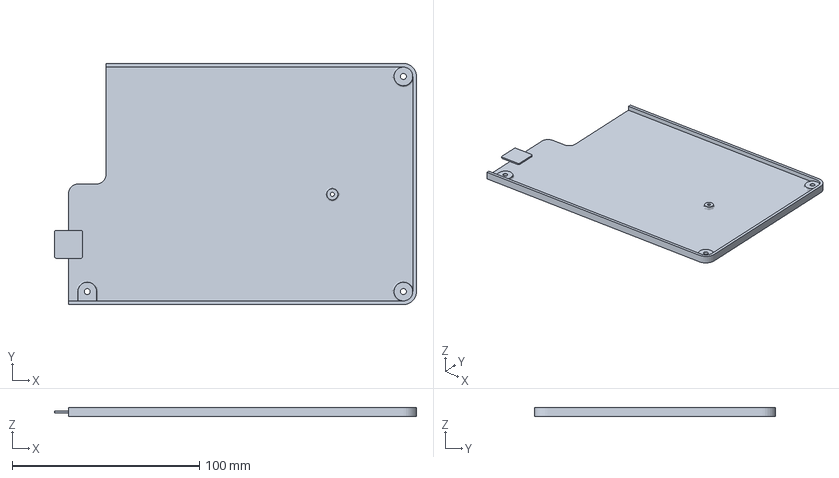
[picture p92: CAD file, 2026-01-03]
CAD/Enclosures/Keyboard Helper/Base Right.3mf
193.5 x 129.0 x 5.00 mm
