acwright/6502/CAD/Enclosures/Keypad Helper/Base.3mf

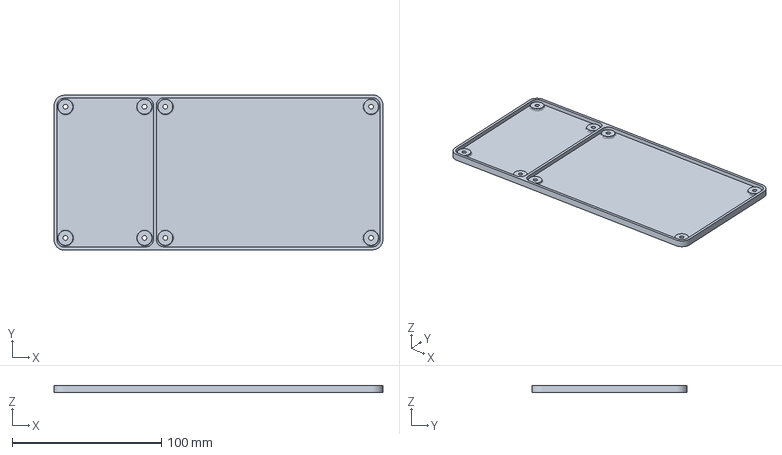
[picture p93: CAD file, 2025-10-03]
CAD/Enclosures/Keypad Helper/Base.3mf
220.7 x 104.3 x 5.00 mm
