acwright/6502/CAD/Bases/The COB/Center Support Retainer.stl

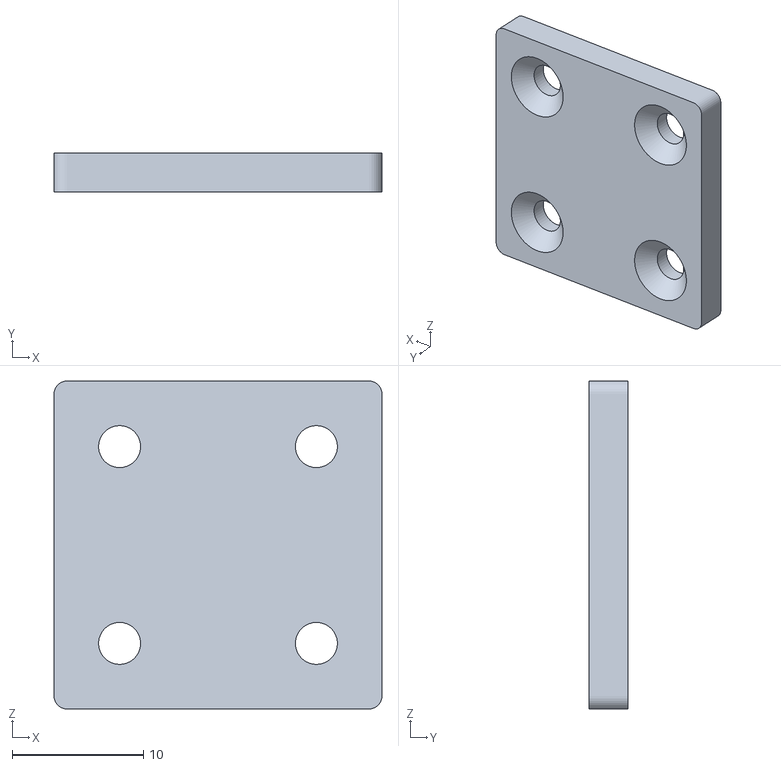
[picture p94: CAD file, 2026-01-31]
CAD/Bases/The COB/Center Support Retainer.stl
25.0 x 3.00 x 25.0
