acwright/6502/CAD/Bases/The KIM/The KIM.3mf

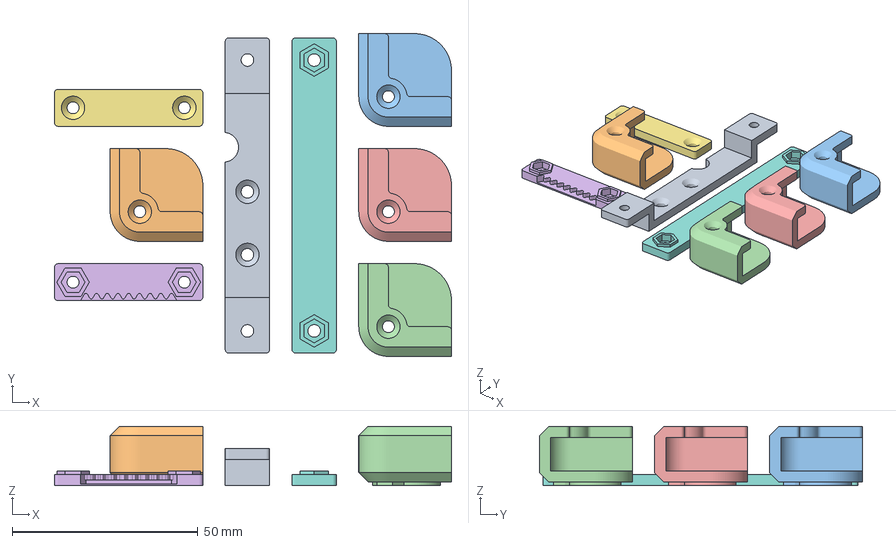
[picture p95: CAD file, 2026-02-03]
CAD/Bases/The KIM/The KIM.3mf
107.0 x 87.0 x 16.0 mm
Cable Bridge.stl
Corner.stl
Hanger.stl
Hanger Retainer.stl
Cable Bridge Retainer.stl
