acwright/6502/CAD/Bases/The VCS/Plate.stl

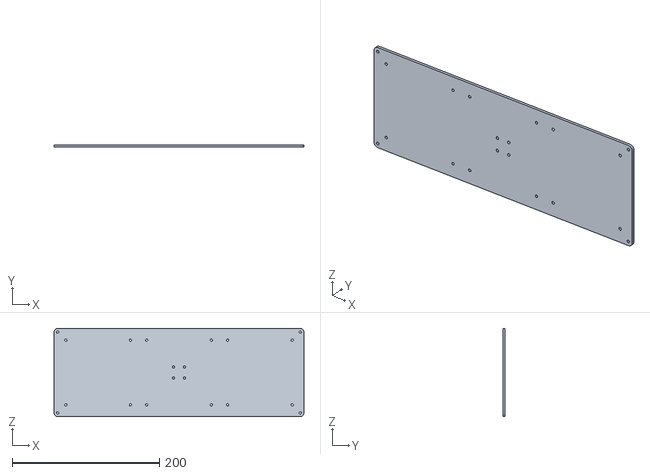
[picture p96: CAD file, 2026-01-31]
CAD/Bases/The VCS/Plate.stl
340.0 x 3.00 x 120.0
