acwright/6502/CAD/Enclosures/Clock Helper/Top.stl

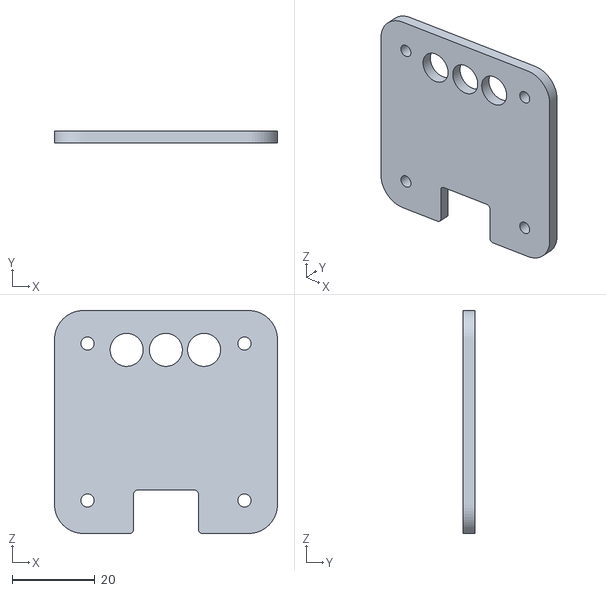
[picture p97: CAD file, 2026-02-07]
CAD/Enclosures/Clock Helper/Top.stl
54.0 x 3.00 x 54.0
