acwright/6502/CAD/Enclosures/DB25 Helper/Top.stl

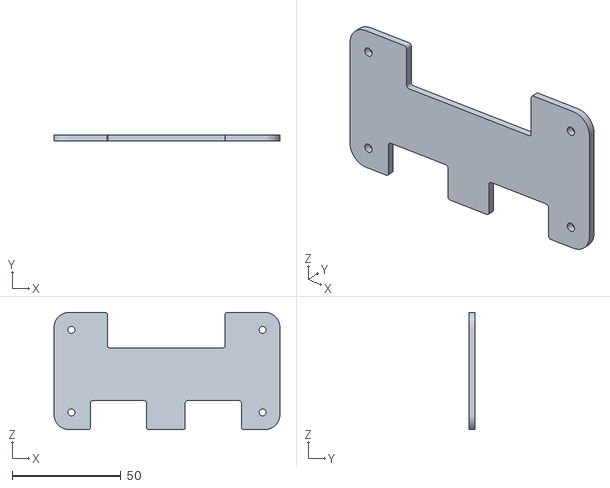
[picture p98: CAD file, 2026-02-07]
CAD/Enclosures/DB25 Helper/Top.stl
104.0 x 2.58 x 54.0
