acwright/6502/CAD/Enclosures/GPIO Helper/Top.stl

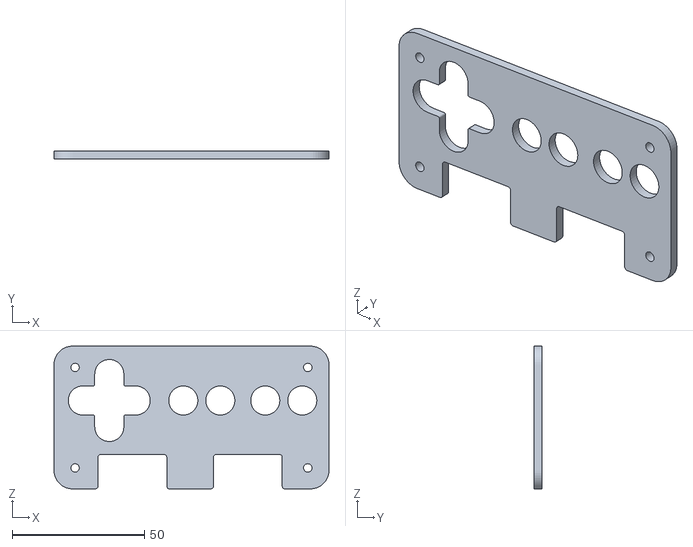
[picture p99: CAD file, 2026-02-07]
CAD/Enclosures/GPIO Helper/Top.stl
104.0 x 3.00 x 54.0
