acwright/6502/CAD/Enclosures/Joystick Helper/Top.stl

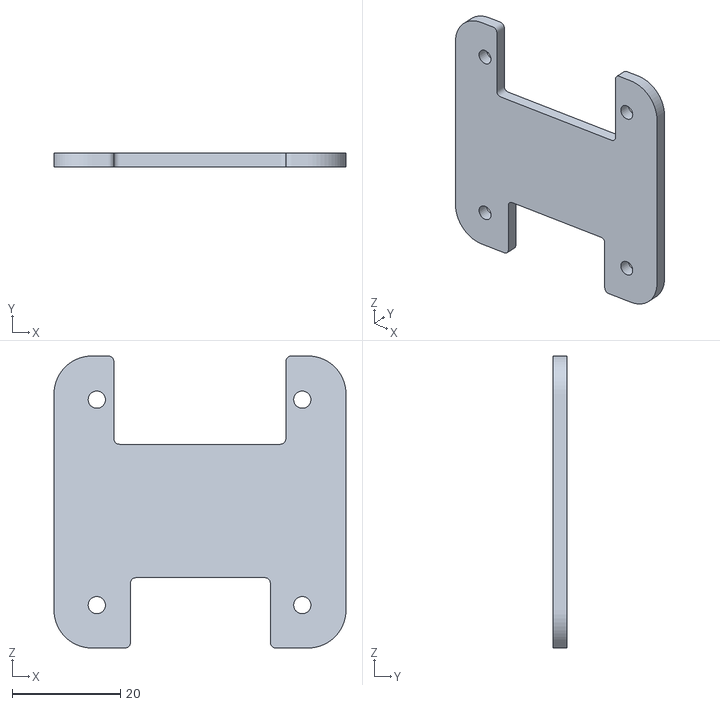
[picture p100: CAD file, 2026-02-07]
CAD/Enclosures/Joystick Helper/Top.stl
54.0 x 2.58 x 54.0
