acwright/6502/CAD/Enclosures/Keyboard Helper/Base Left.3mf

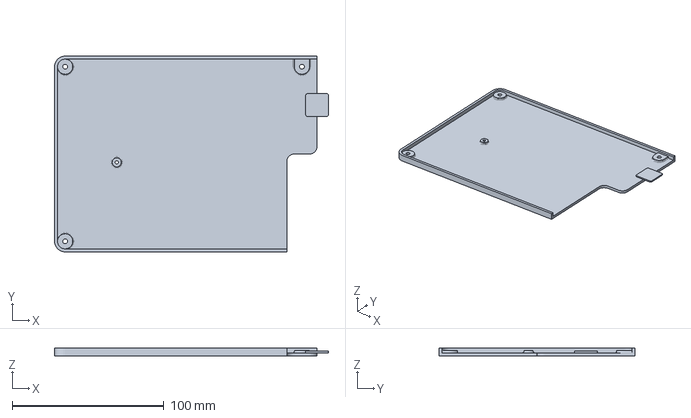
[picture p102: CAD file, 2026-01-03]
CAD/Enclosures/Keyboard Helper/Base Left.3mf
180.5 x 129.0 x 5.00 mm
