acwright/6502/CAD/Enclosures/Keypad Helper/Top.stl

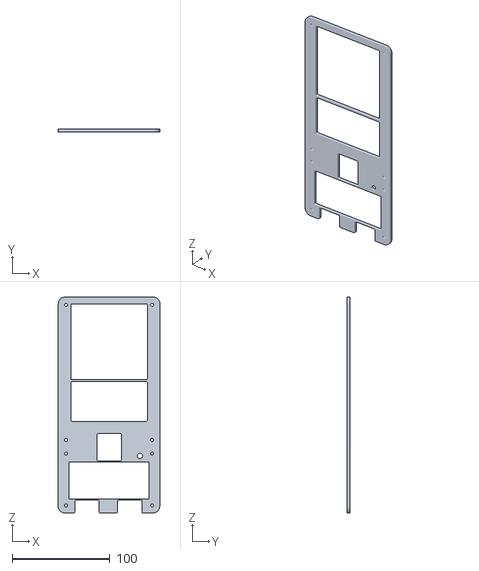
[picture p103: CAD file, 2025-10-03]
CAD/Enclosures/Keypad Helper/Top.stl
104.3 x 3.00 x 220.7
