acwright/6502/CAD/Enclosures/PS2 Helper/Top.stl

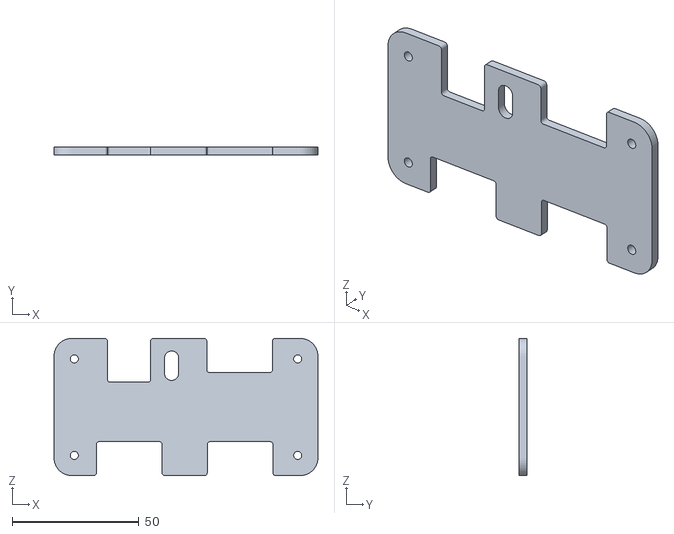
[picture p104: CAD file, 2026-02-07]
CAD/Enclosures/PS2 Helper/Top.stl
104.0 x 3.00 x 54.0
