acwright/6502/CAD/Bases/The COB/Center Support.3mf

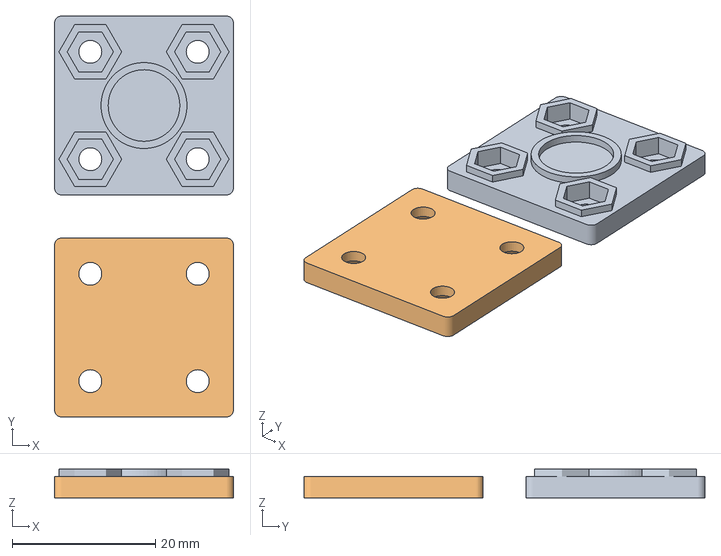
[picture p105: CAD file, 2026-01-31]
CAD/Bases/The COB/Center Support.3mf
25.0 x 56.0 x 4.00 mm
Center Support.stl
Center Support Retainer.stl
