acwright/6502/CAD/Bases/The DEV/Plate.stl

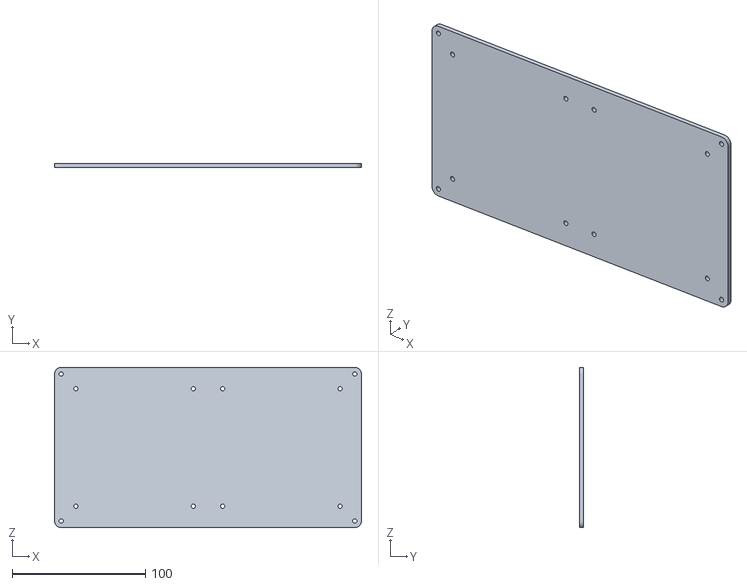
[picture p106: CAD file, 2026-01-31]
CAD/Bases/The DEV/Plate.stl
230.0 x 3.00 x 120.0
