acwright/6502/CAD/Enclosures/Clock Helper/Button.stl

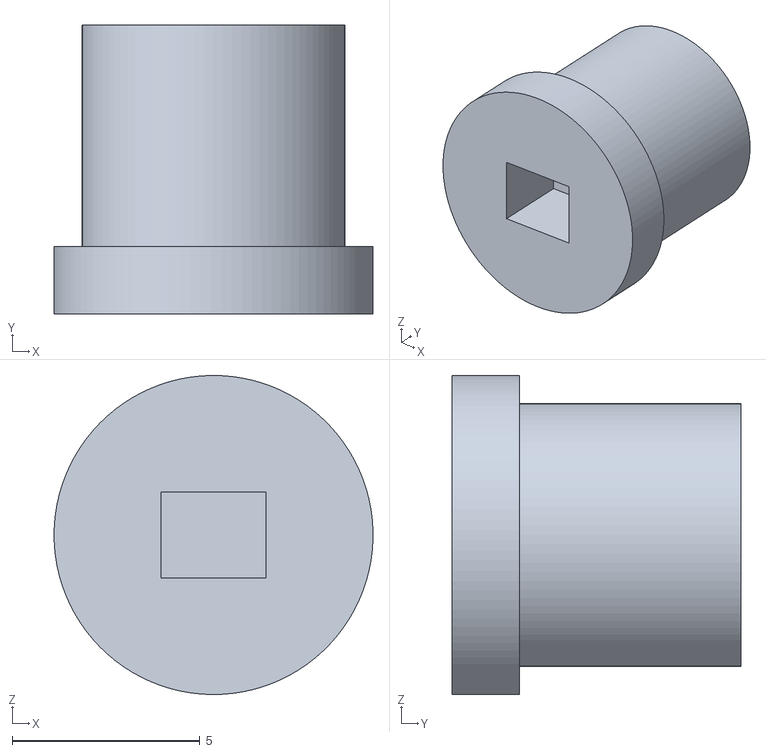
[picture p107: CAD file, 2025-12-29]
CAD/Enclosures/Clock Helper/Button.stl
8.50 x 7.70 x 8.50
