acwright/6502/CAD/Enclosures/GPIO Helper/D-Pad.stl

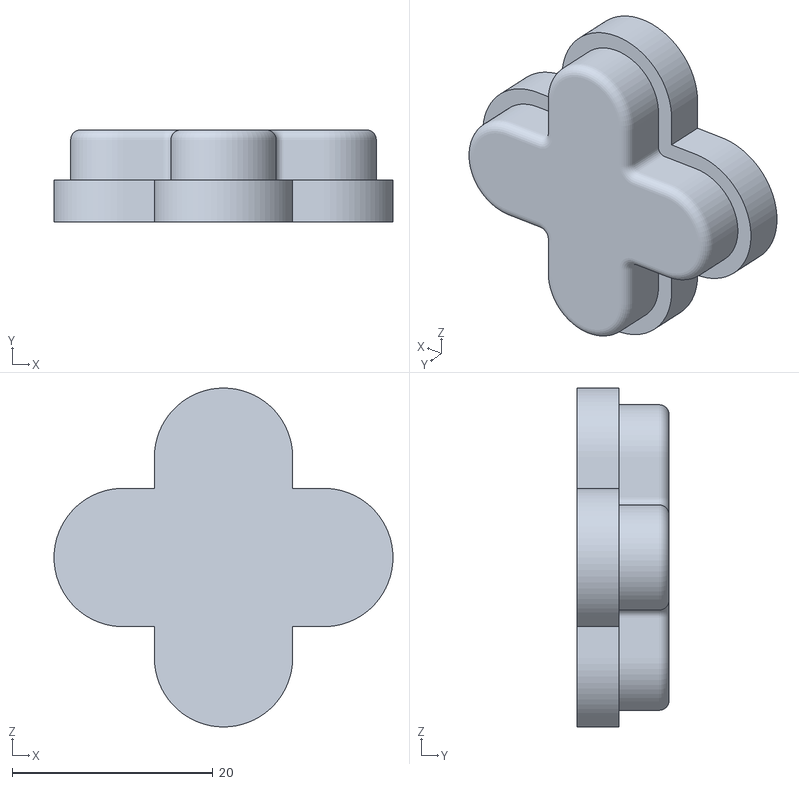
[picture p108: CAD file, 2025-10-14]
CAD/Enclosures/GPIO Helper/D-Pad.stl
33.8 x 9.20 x 33.8
