acwright/6502/CAD/Enclosures/Keyboard Helper/Top.stl

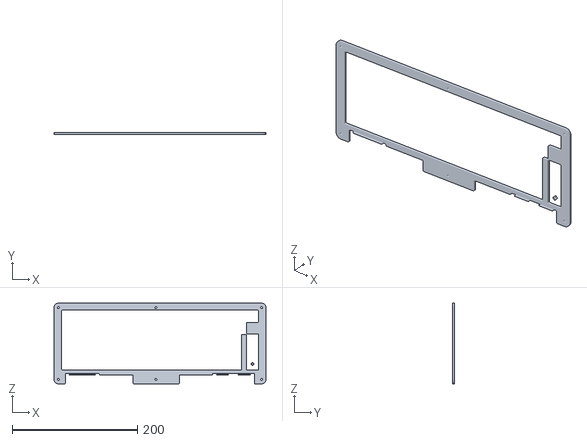
[picture p109: CAD file, 2025-12-29]
CAD/Enclosures/Keyboard Helper/Top.stl
339.0 x 3.00 x 129.0
