acwright/6502/CAD/Bases/The COB/Plate.stl

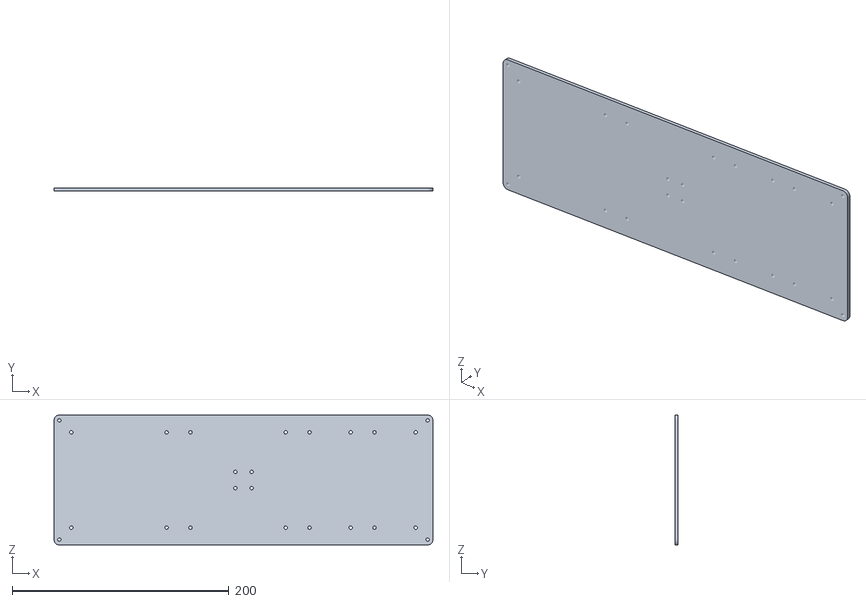
[picture p110: CAD file, 2026-01-31]
CAD/Bases/The COB/Plate.stl
350.0 x 3.00 x 120.0
