acwright/6502/CAD/Bases/The DEV/Corner.3mf

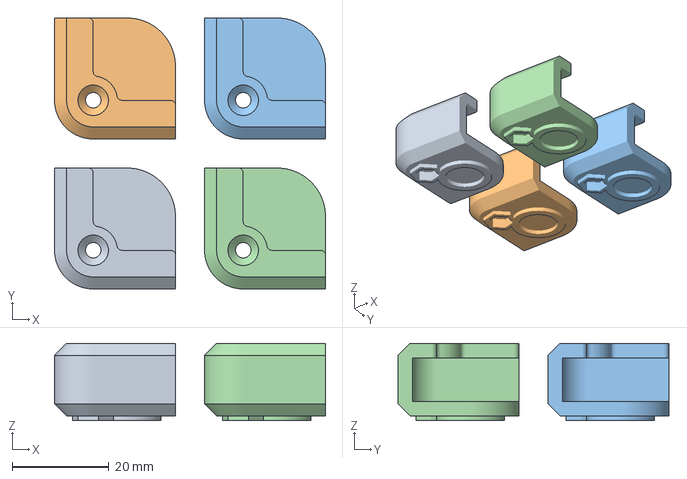
[picture p111: CAD file, 2026-01-31]
CAD/Bases/The DEV/Corner.3mf
56.0 x 56.0 x 16.0 mm
