acwright/6502/CAD/Bases/The KIM/Corner.stl

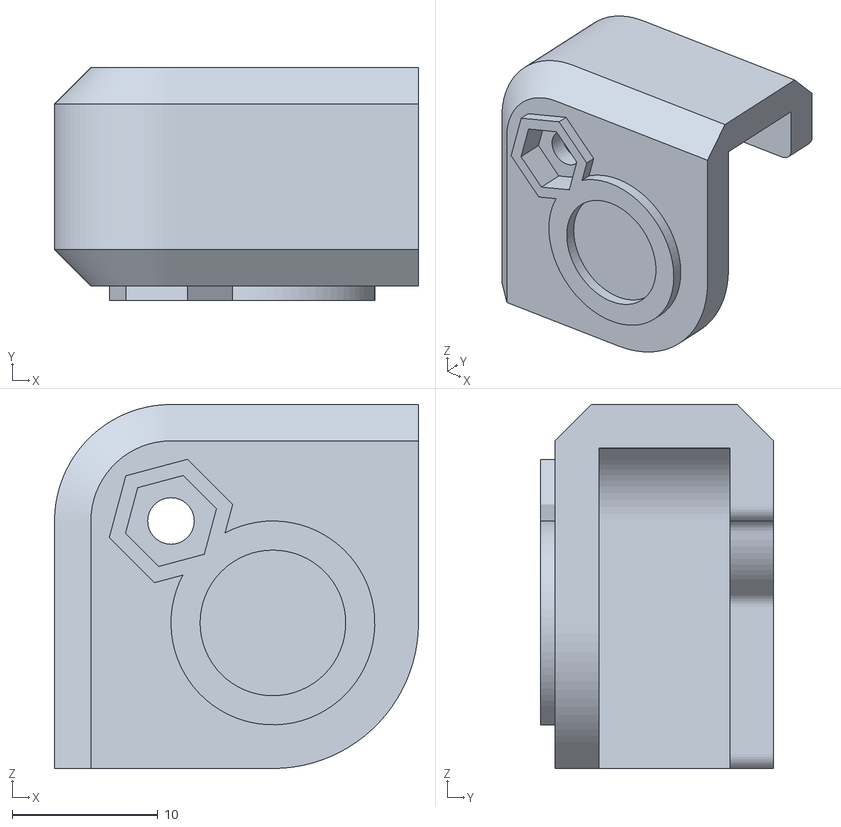
[picture p112: CAD file, 2026-01-31]
CAD/Bases/The KIM/Corner.stl
25.0 x 16.0 x 25.0
