acwright/6502/CAD/Enclosures/Clock Helper/Buttons.3mf

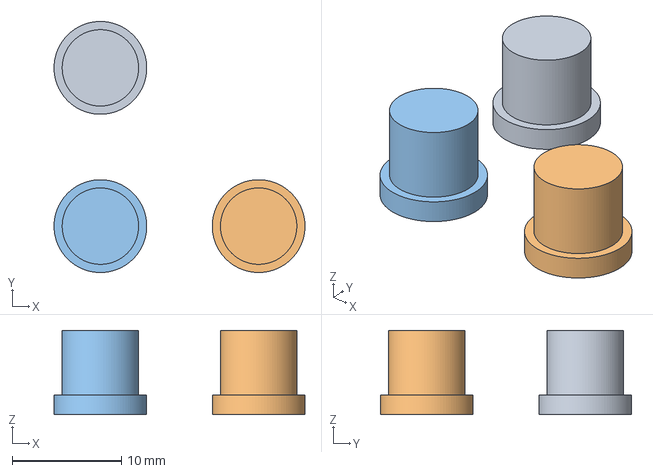
[picture p113: CAD file, 2025-12-29]
CAD/Enclosures/Clock Helper/Buttons.3mf
23.0 x 23.0 x 7.70 mm
