acwright/6502/CAD/Enclosures/GPIO Helper/Buttons.3mf

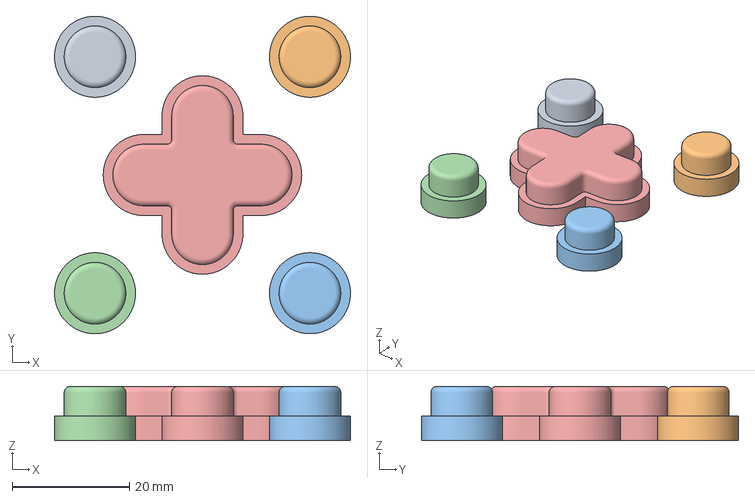
[picture p114: CAD file, 2025-10-14]
CAD/Enclosures/GPIO Helper/Buttons.3mf
50.4 x 54.0 x 9.20 mm
Button.stl
D-Pad.stl
