acwright/6502/CAD/Enclosures/Keyboard Helper/Base.stl

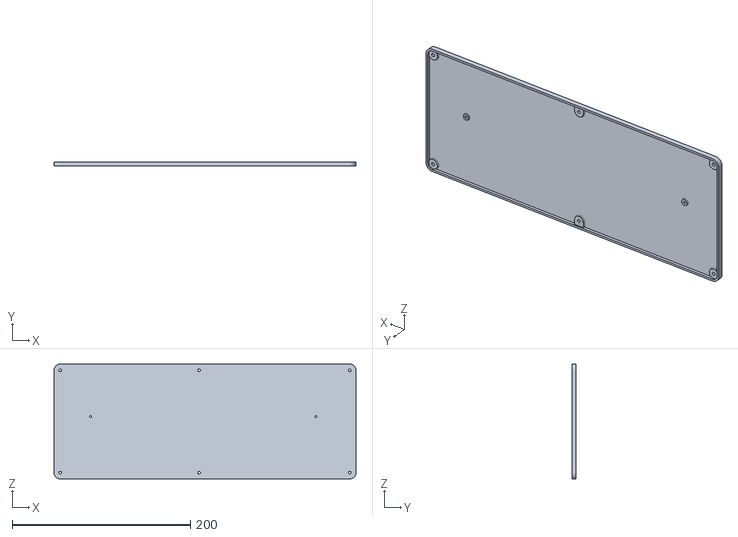
[picture p115: CAD file, 2025-12-29]
CAD/Enclosures/Keyboard Helper/Base.stl
339.0 x 5.00 x 129.0
