acwright/6502/CAD/Bases/The KIM/Keypad Helper Top.stl

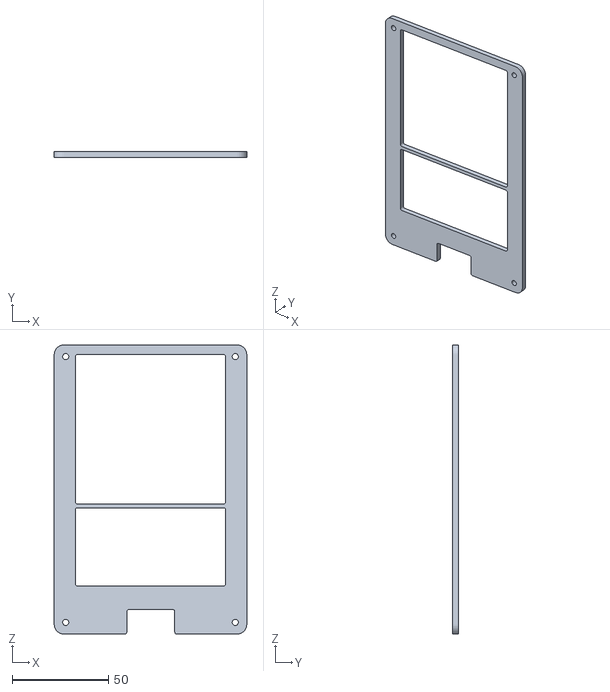
[picture p116: CAD file, 2026-01-31]
CAD/Bases/The KIM/Keypad Helper Top.stl
100.0 x 3.00 x 150.0
