acwright/6502/CAD/Enclosures/GPIO Helper/Button.stl

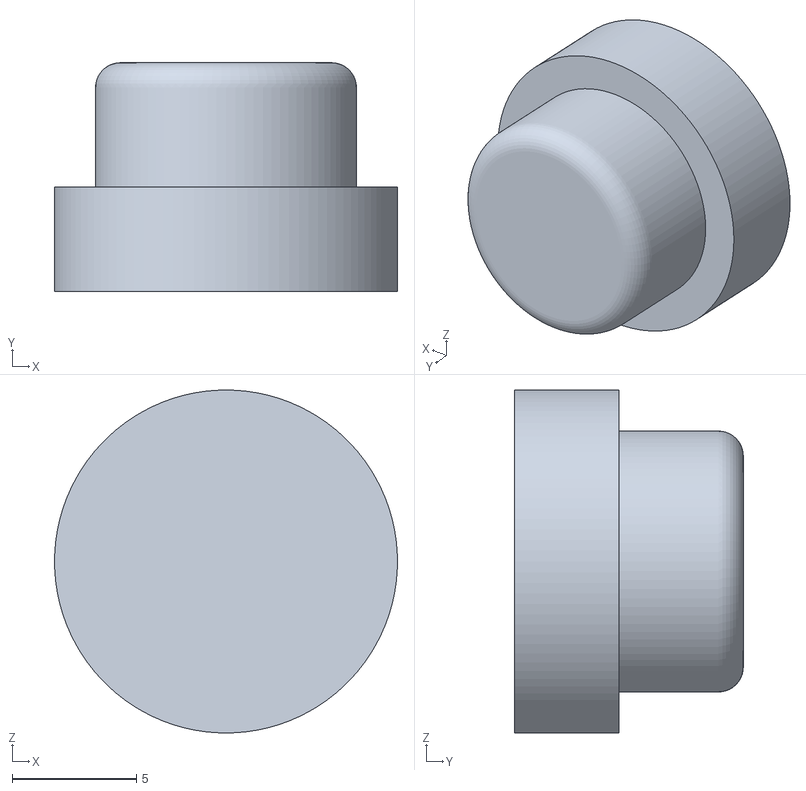
[picture p117: CAD file, 2025-10-03]
CAD/Enclosures/GPIO Helper/Button.stl
13.8 x 9.20 x 13.8
