acwright/6502/CAD/Bases/The KIM/Plate.stl

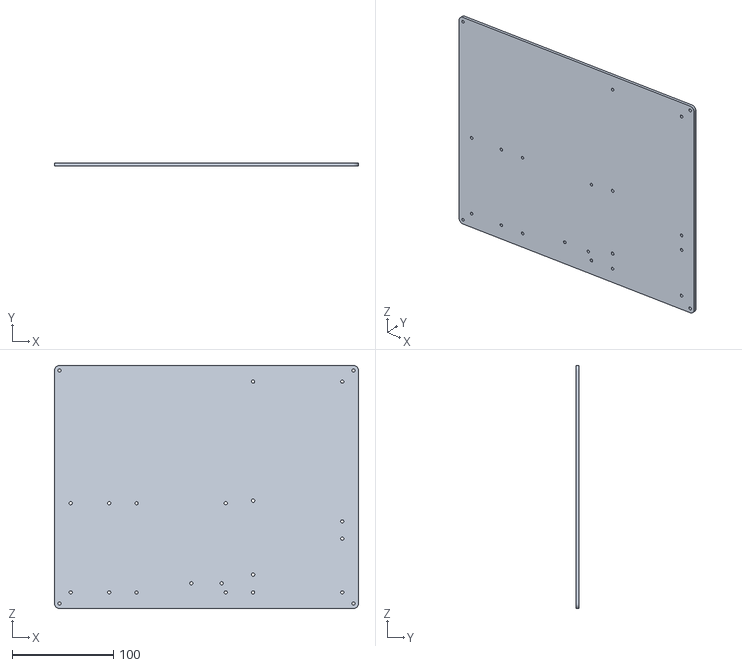
[picture p118: CAD file, 2026-01-31]
CAD/Bases/The KIM/Plate.stl
300.0 x 3.00 x 240.0
