acwright/6502/CAD/Bases/The KIM/Cable Bridge Retainer.stl

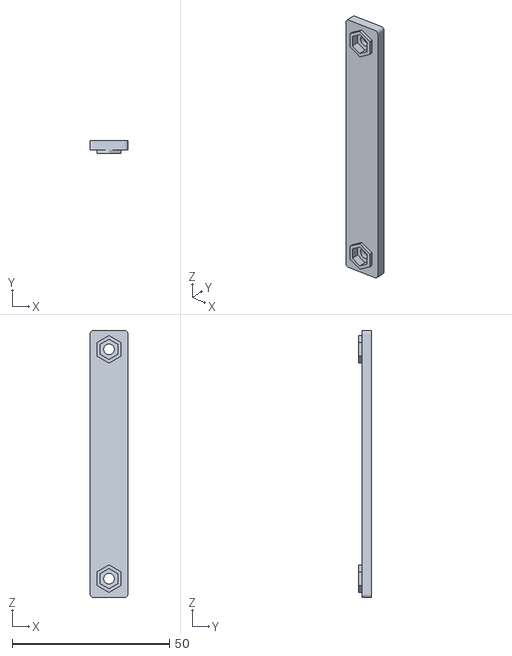
[picture p119: CAD file, 2026-01-31]
CAD/Bases/The KIM/Cable Bridge Retainer.stl
12.0 x 4.00 x 85.0
