acwright/6502/CAD/Bases/The KIM/Keypad LCD Helper Top.stl

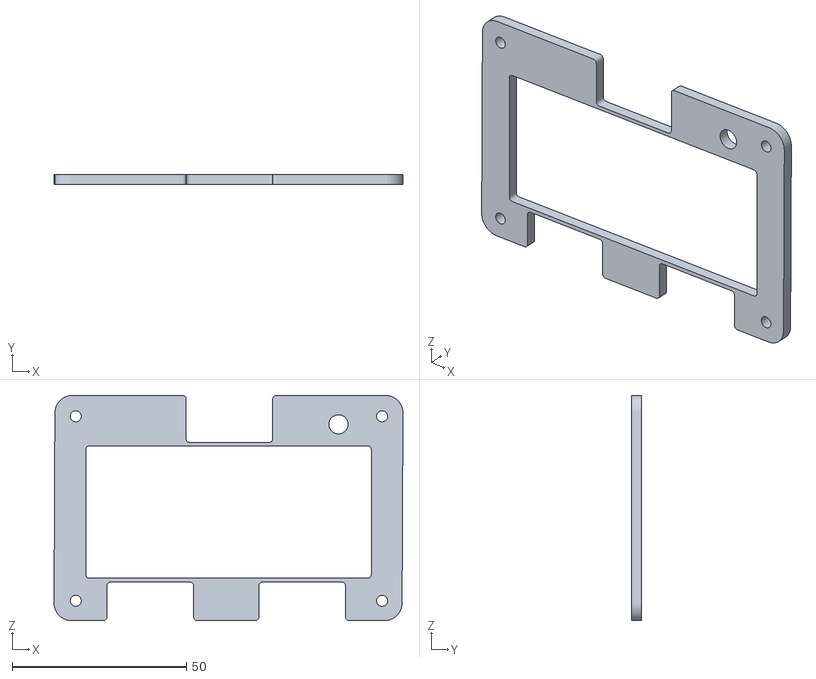
[picture p120: CAD file, 2026-01-31]
CAD/Bases/The KIM/Keypad LCD Helper Top.stl
100.3 x 3.00 x 64.7
