acwright/6502/CAD/Bases/The KIM/Cable Bridge.stl

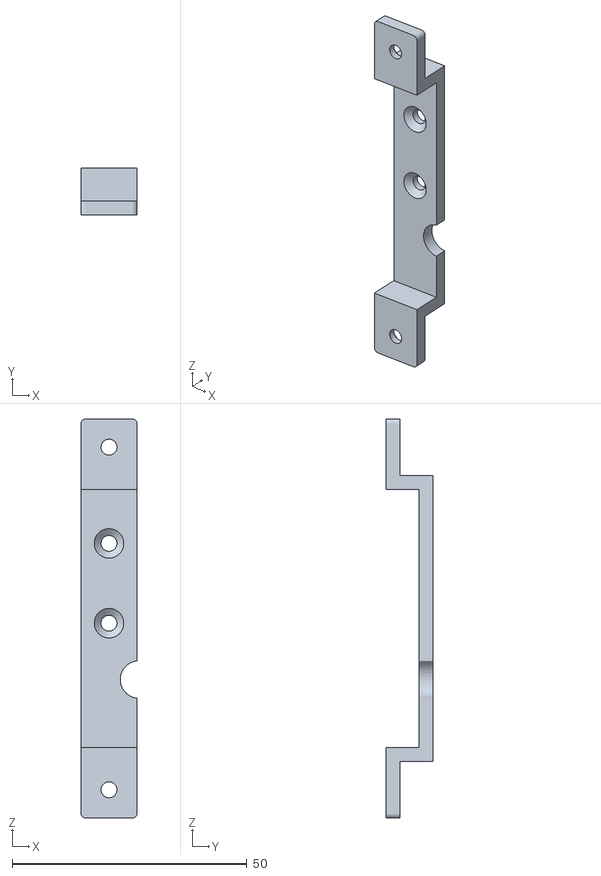
[picture p121: CAD file, 2026-01-30]
CAD/Bases/The KIM/Cable Bridge.stl
12.0 x 10.0 x 85.0
