acwright/6502/Schematics/Output Board/Rev 1.0/Output Board.pdf

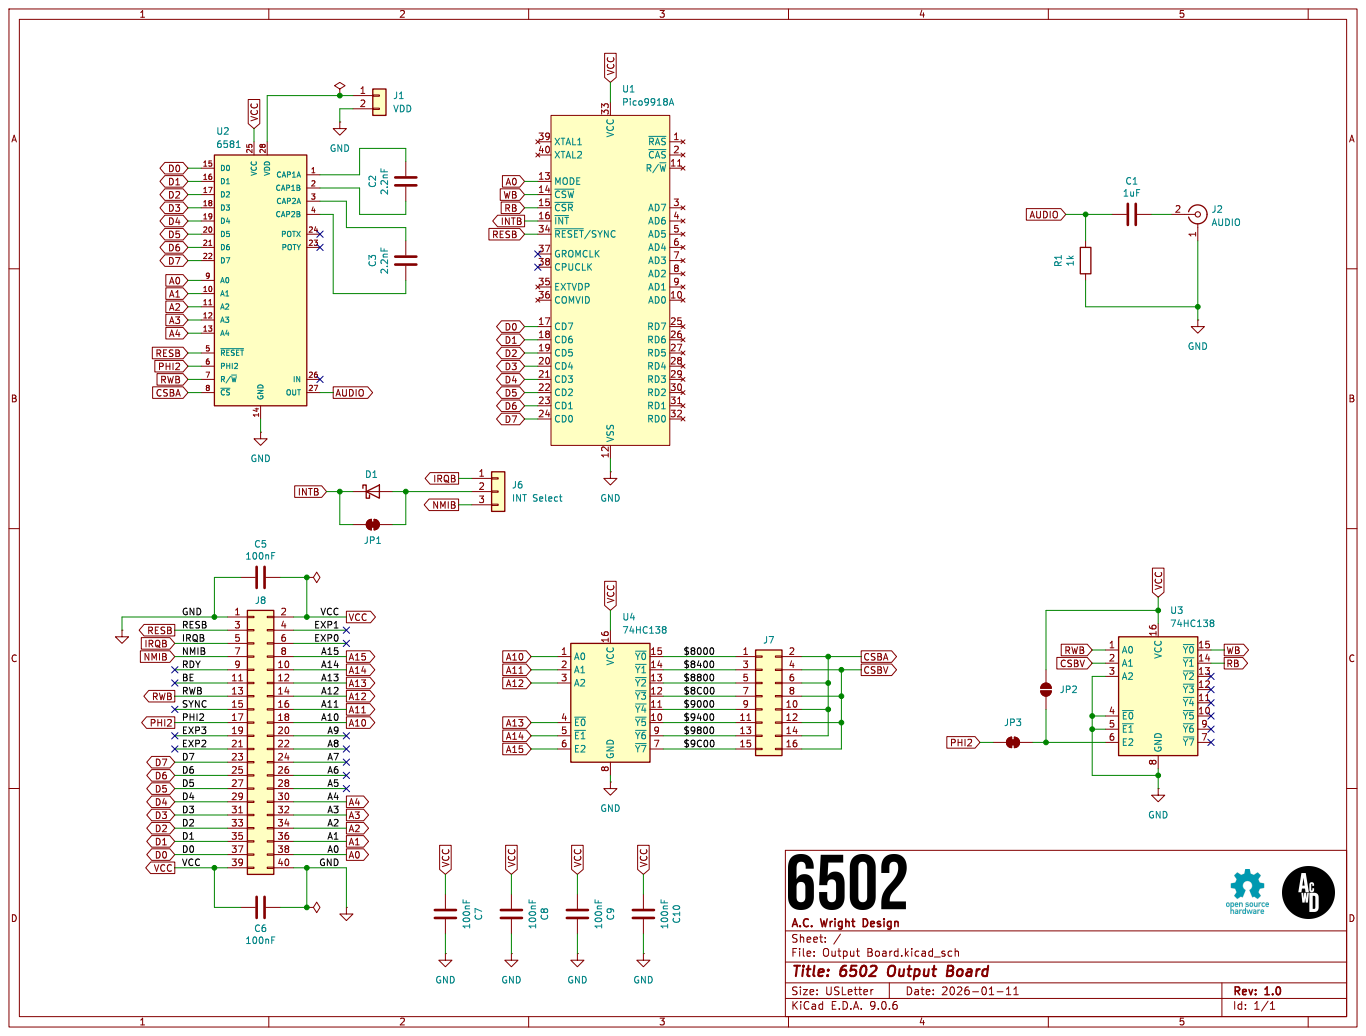
[picture p126: page 1]

Id: 1/1 Title: 6502 Output Board
