acwright/6502/Schematics/LCD Board/Rev 1.0/LCD Board.pdf

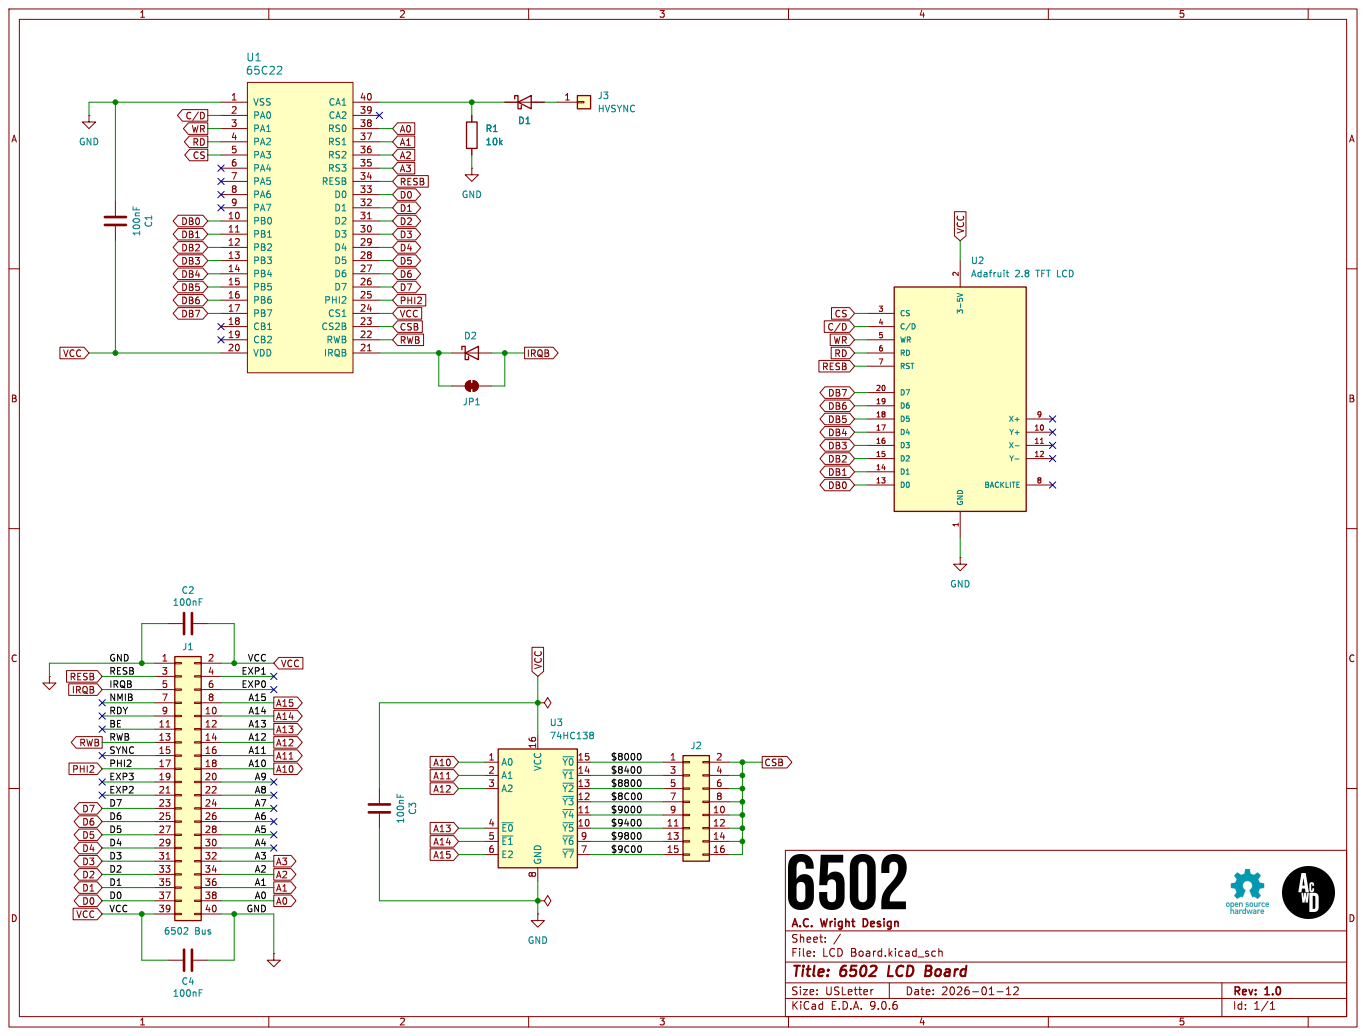
[picture p127: page 1]

Id: 1/1 Title: 6502 LCD Board
