acwright/6502/Schematics/Dev Board/Rev 1.0/Dev Board.pdf

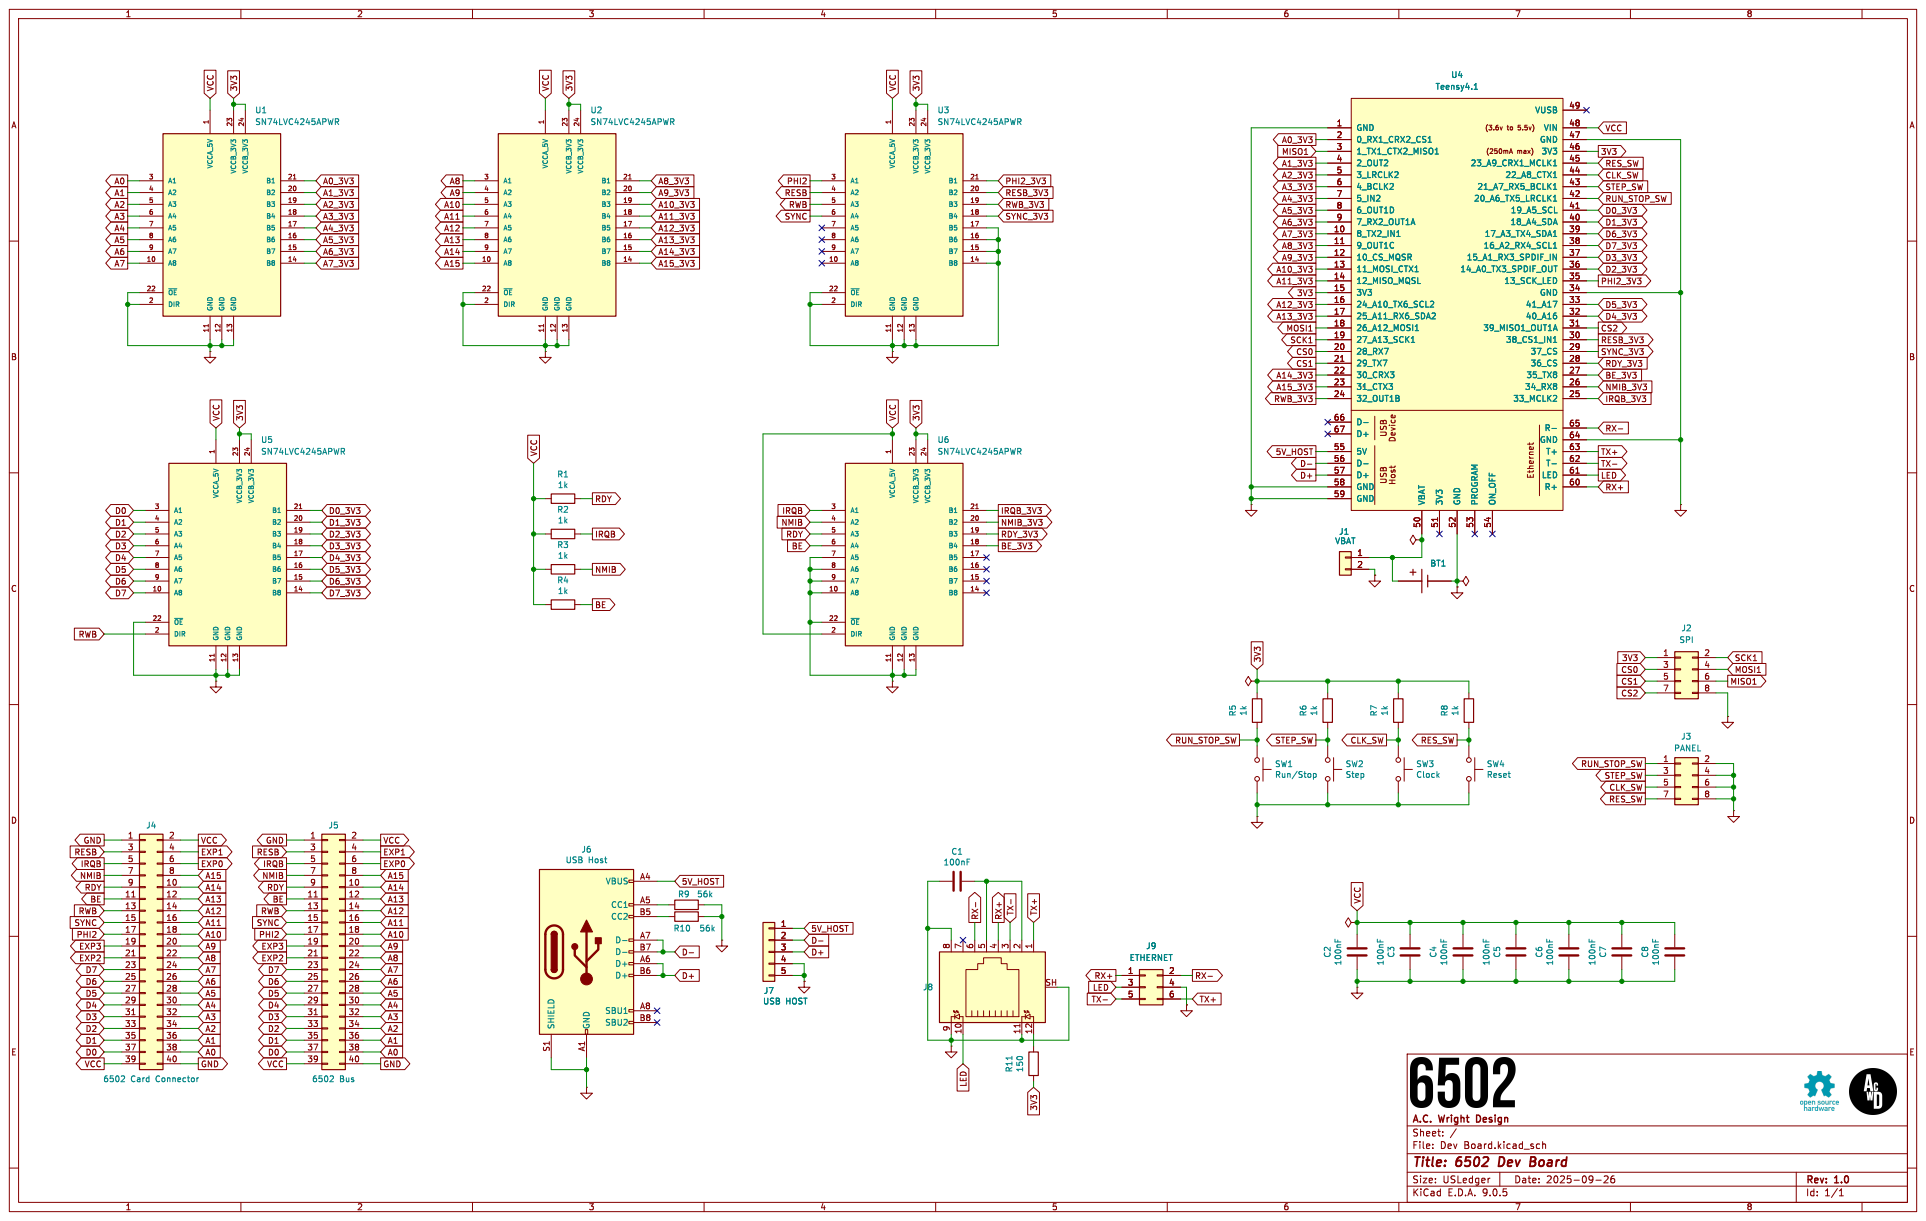
[picture p128: page 1]

RX+ TX+ TX- LED

Id: 1/1 Title: 6502 Dev Board
