acwright/6502/Schematics/Prototype Card/Rev 1.0/Prototype Card.pdf

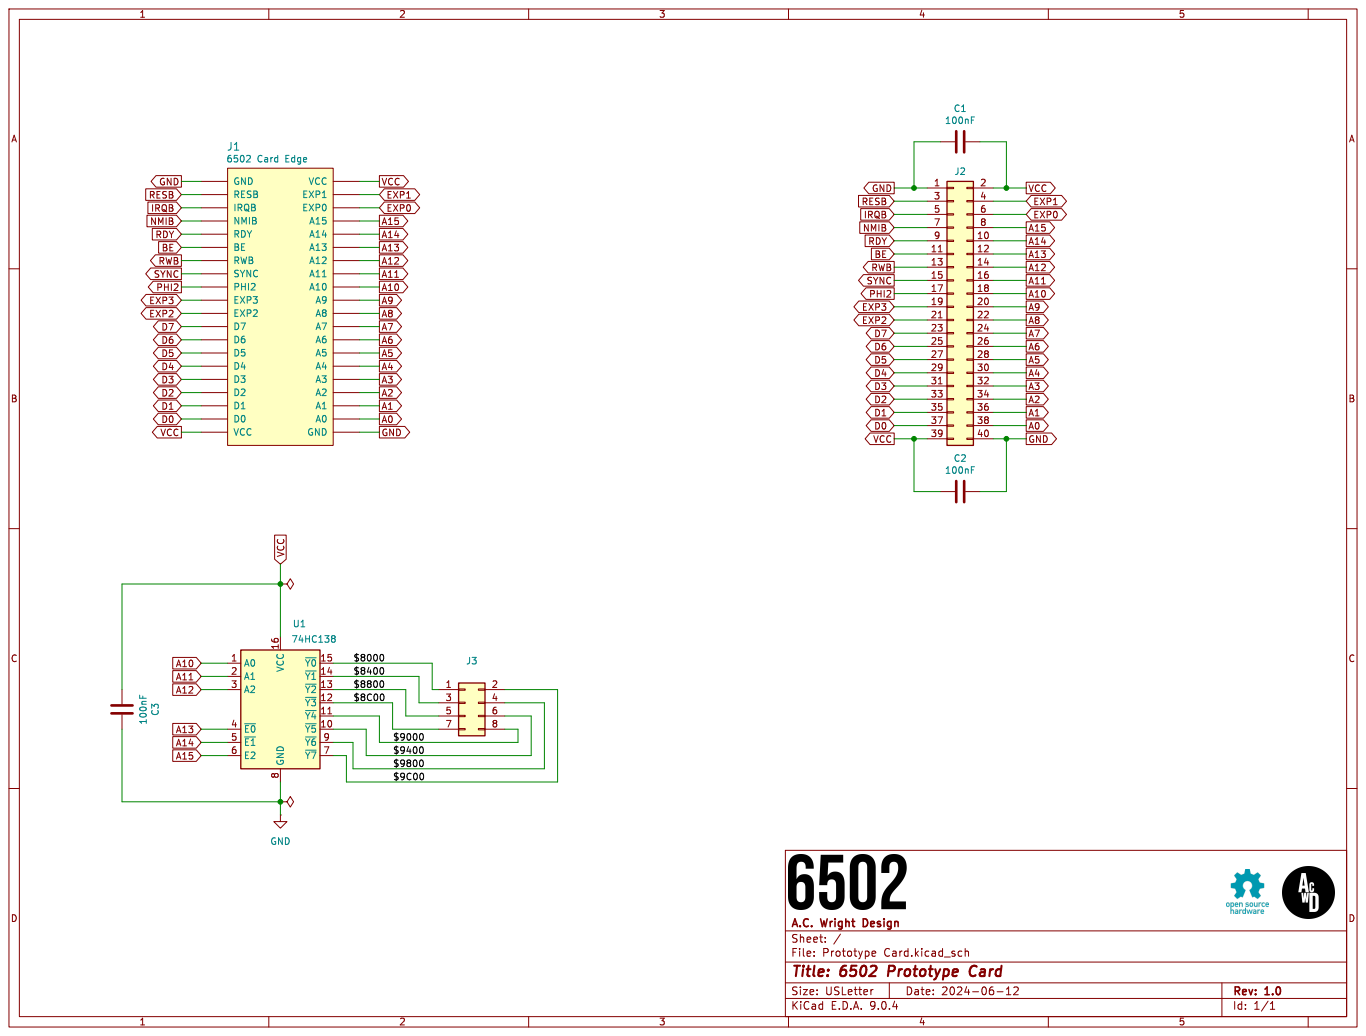
[picture p129: page 1]

Id: 1/1 Title: 6502 Prototype Card
