acwright/6502/Assets/Documents/Connectors/Connectors.pdf

# BUS CONNECTOR

# CONNECTORS

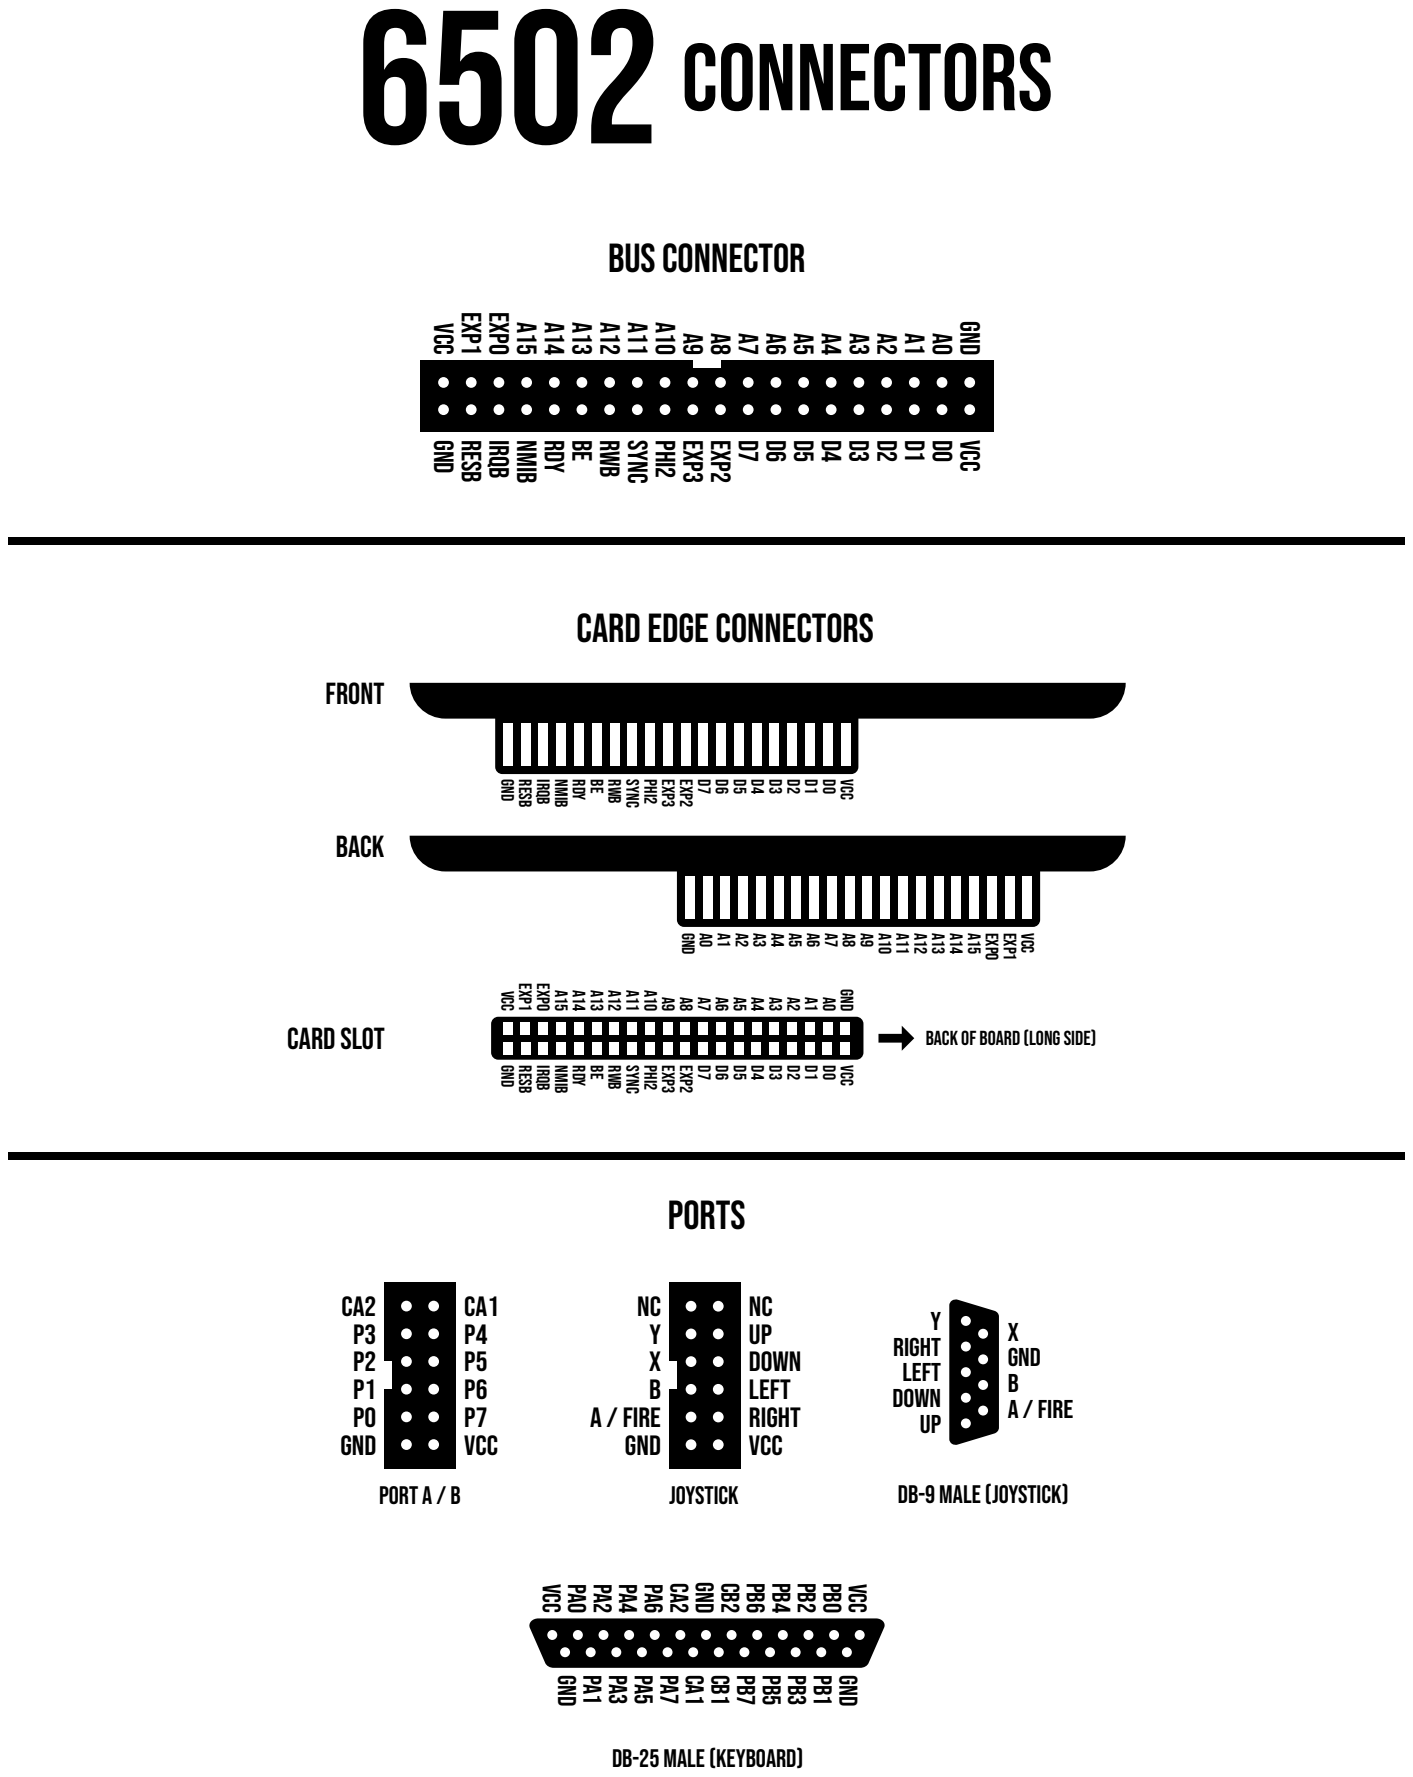
[picture p130: page 1]
VCC; GND CB2; PB0 VCC; GND; x gnd b a / fire; y right left down UP; CA1 P4 P5 P6 P7 VCC; CA2 P3 P2 p1 p0 gnd; PORT A / B; NC UP DOWN LEFT RIGHT VCC; NC Y X B A / FIRE gnd; JOYSTICK; PORTS gnd a0a1a2; exp0; exp1; vcc; BACK; gnd; resb; irqb; nmib; rdy; rwb; sync; phi2; exp3; exp2; FRONT; VCC GND; EXP1; EXP0; CARD slot

CARD EDGE CONNECTORS

BACK OF BOARD (LONG SIDE)

DB-9 MALE (JOYSTICK)

DB-25 MALE (KEYBOARD)
