acwright/6502/Schematics/CPU Card Pro/Rev 1.0/CPU Card Pro.pdf

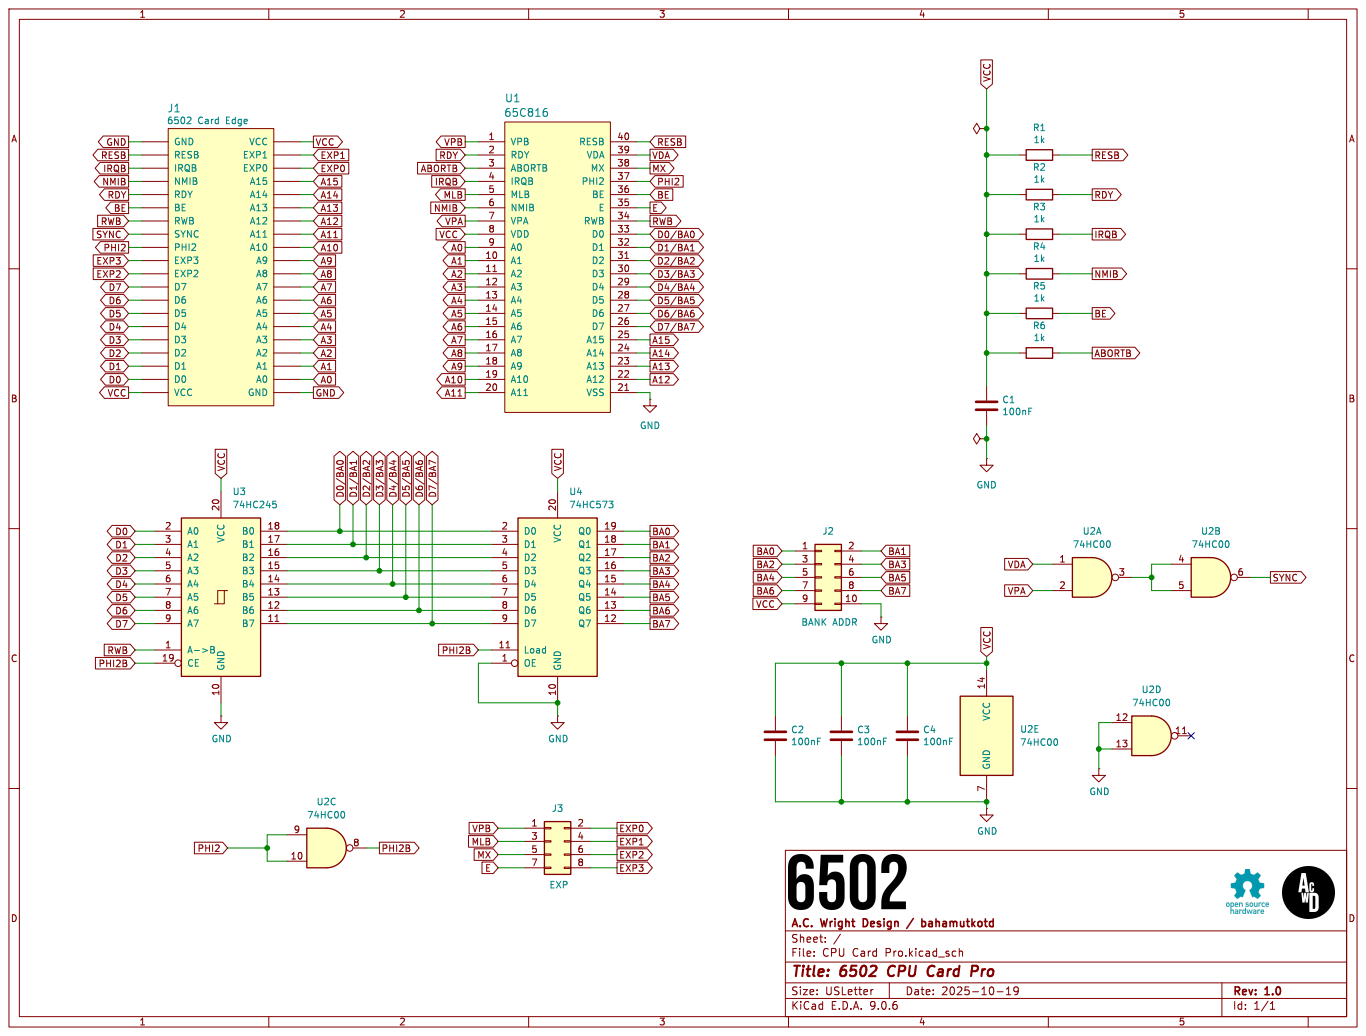
[picture p139: page 1]

IRQB RDY NMIB RESB

Id: 1/1 Title: 6502 CPU Card Pro
