acwright/6502/Schematics/CPU Card/Rev 1.0/CPU Card.pdf

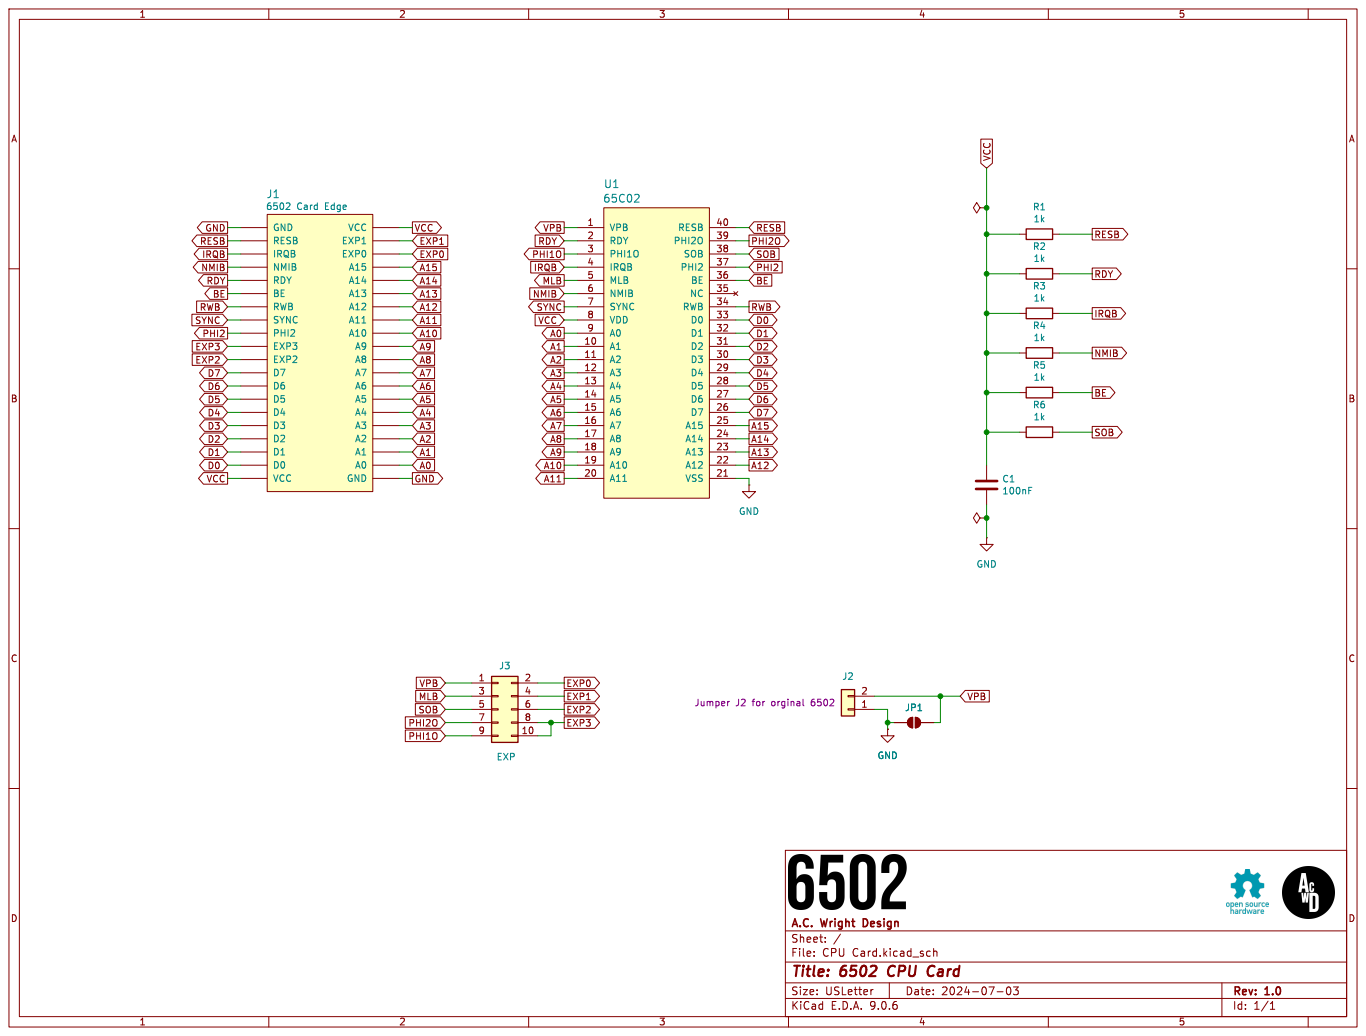
[picture p140: page 1]

Id: 1/1 Title: 6502 CPU Card
