acwright/6502/Schematics/Sound Card/Rev 1.0/Sound Card.pdf

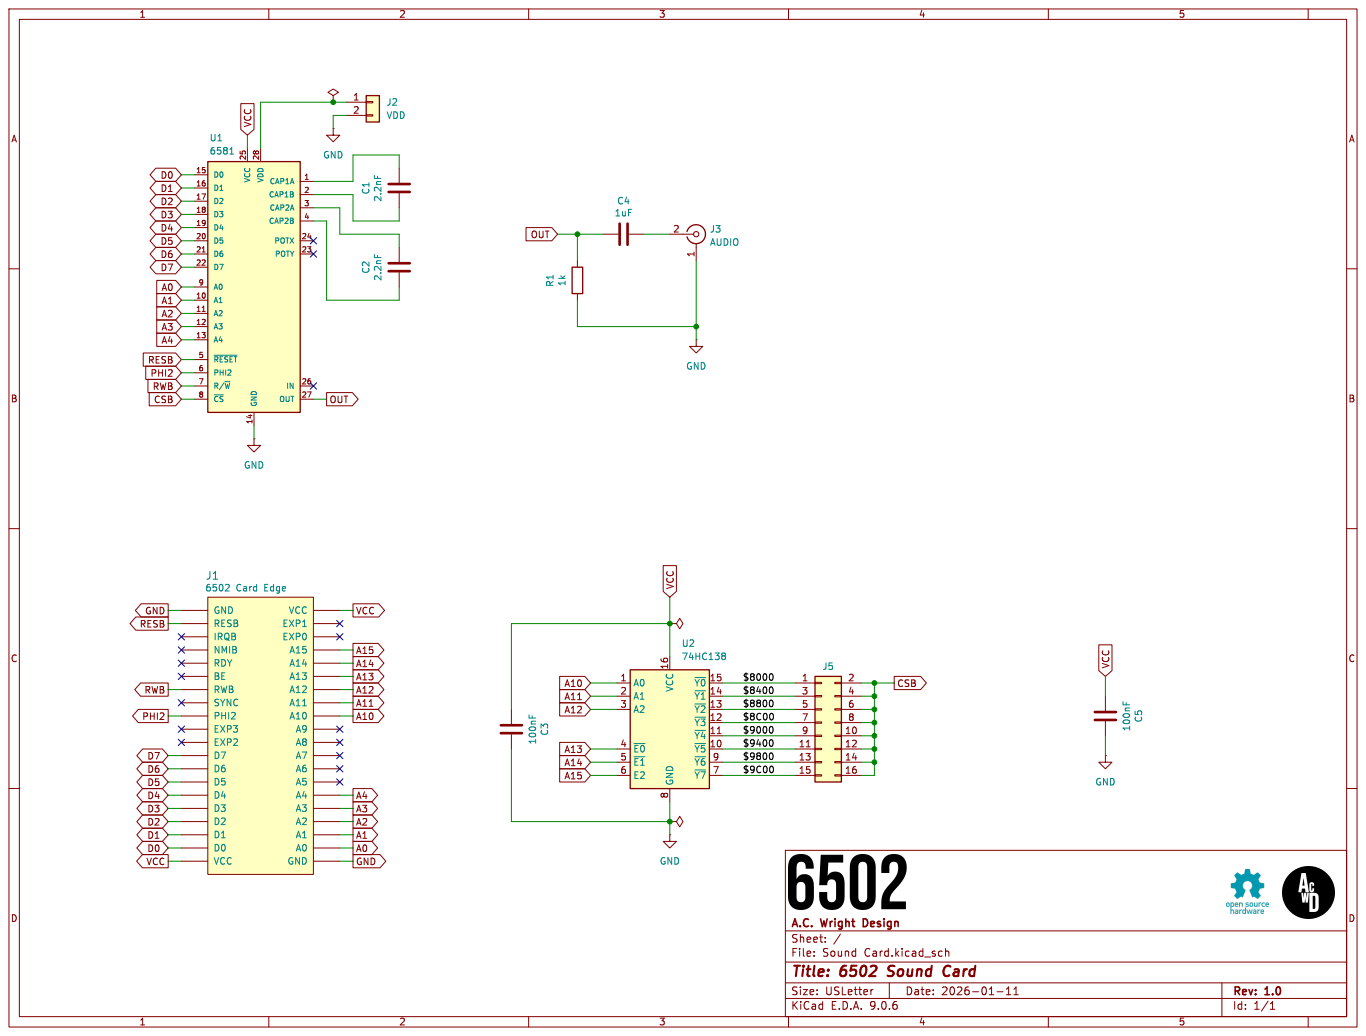
[picture p141: page 1]

Id: 1/1 Title: 6502 Sound Card
