acwright/6502/Schematics/Mega Helper/Rev 1.0/Mega Helper.pdf

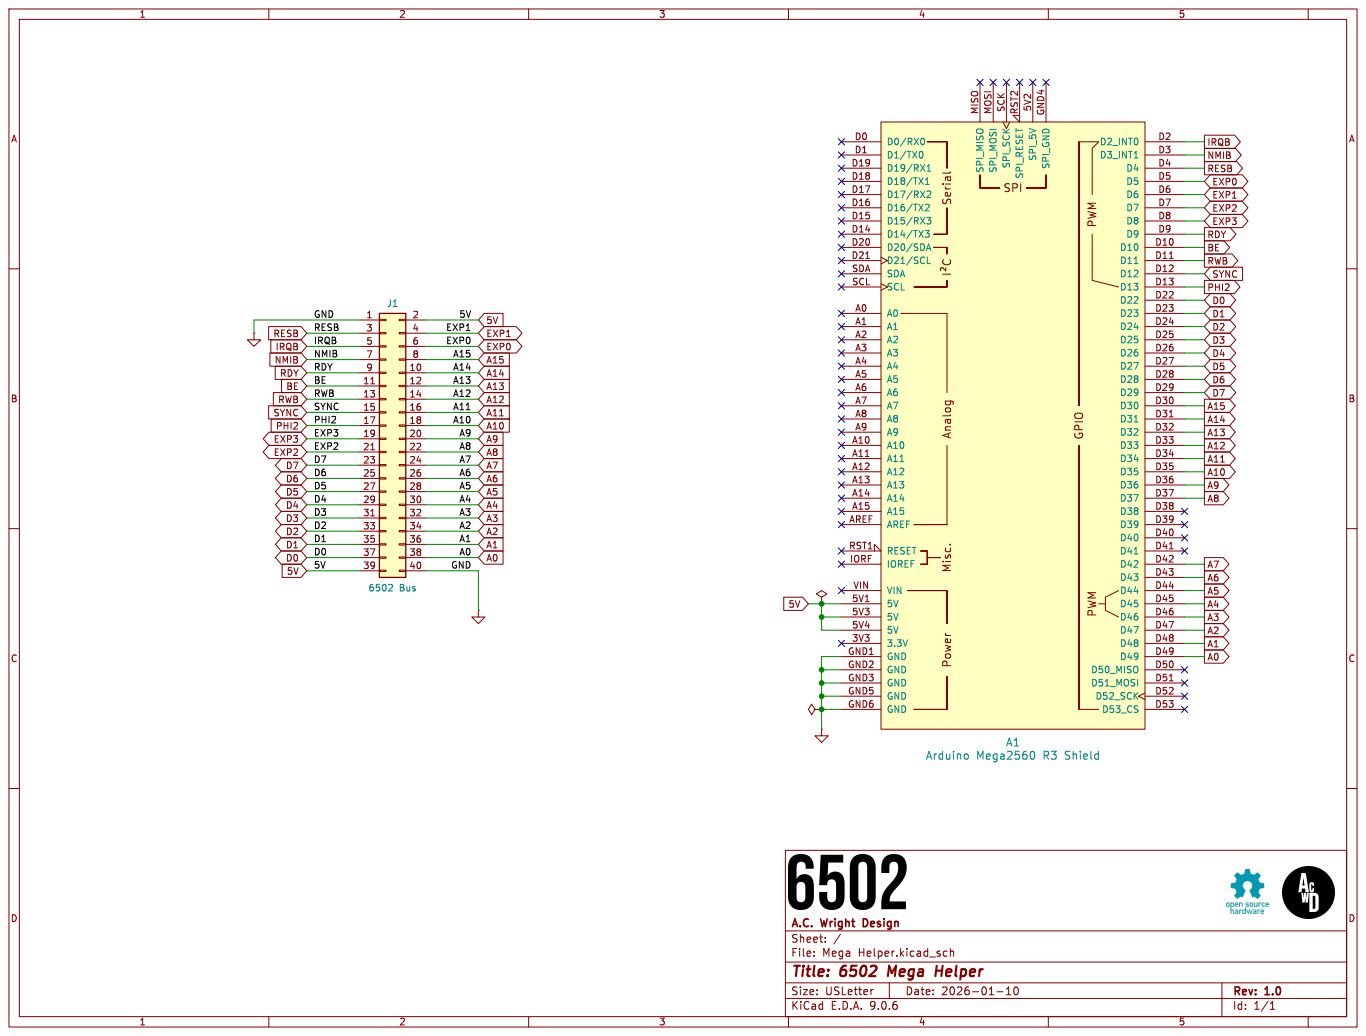
[picture p142: page 1]
