acwright/6502/Schematics/Video Card Pro/Rev 1.0/Video Card Pro.pdf

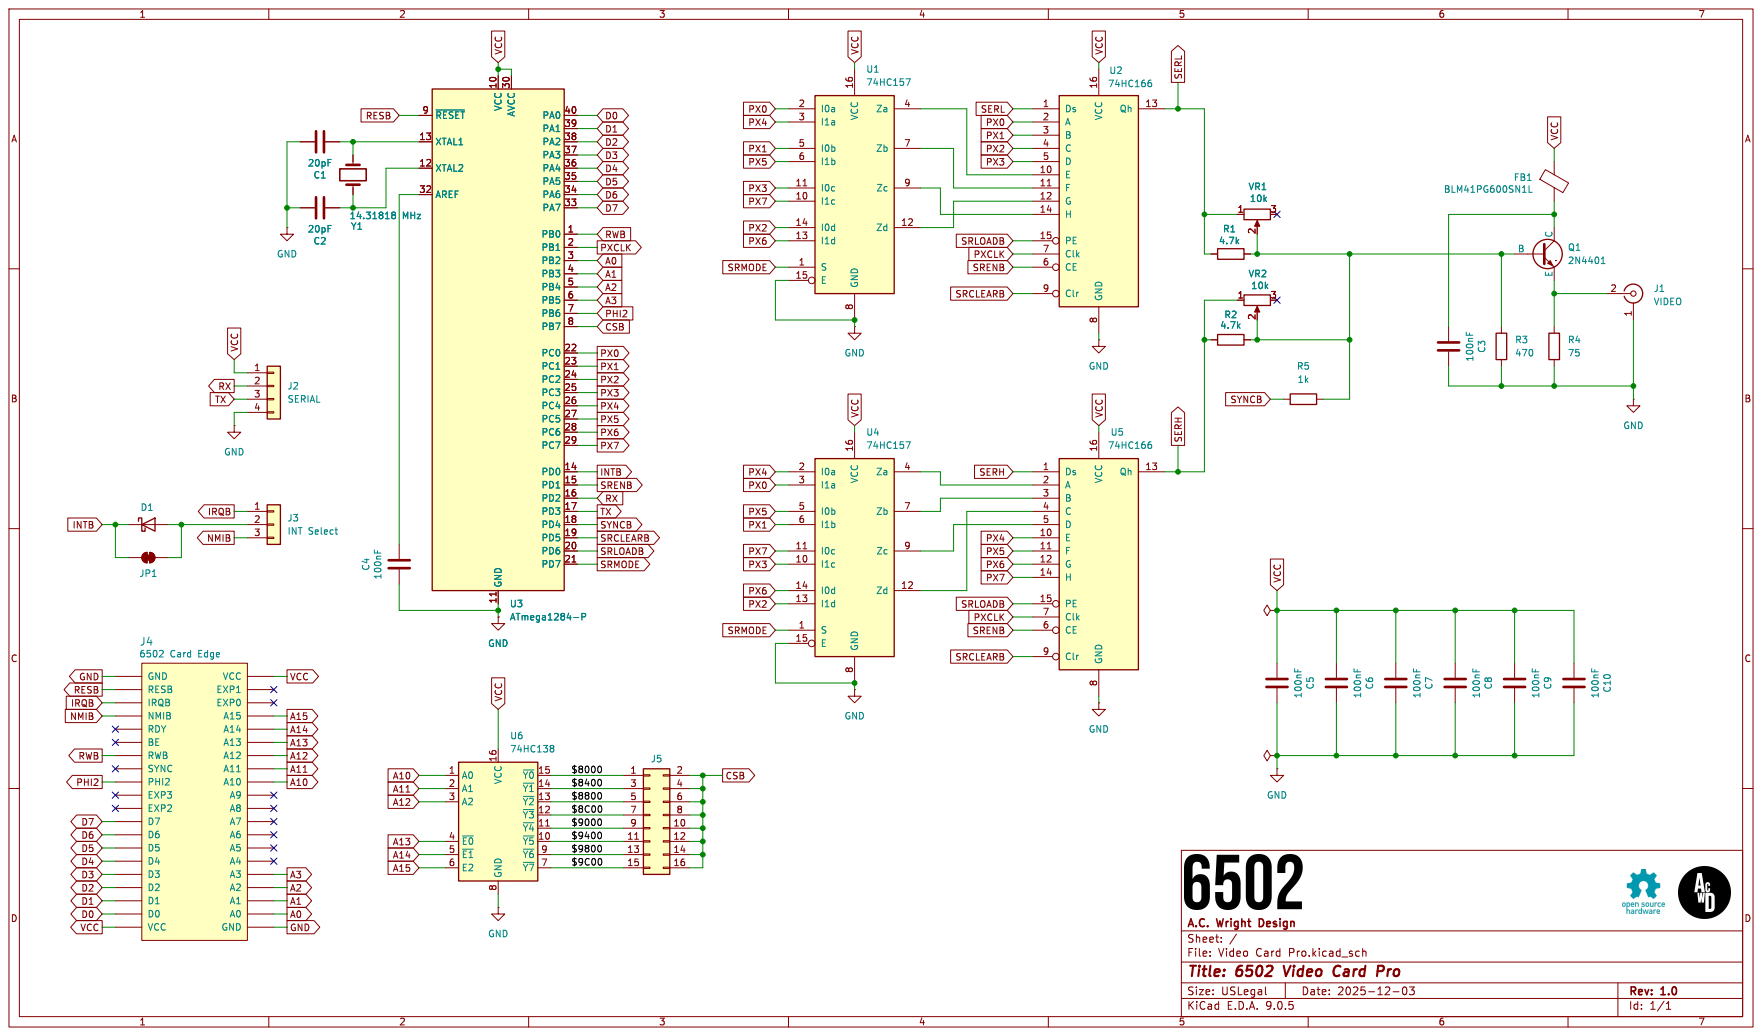
[picture p143: page 1]

Id: 1/1 Title: 6502 Video Card Pro
