acwright/6502/Schematics/Backplane Helper/Rev 1.0/Backplane Helper.pdf

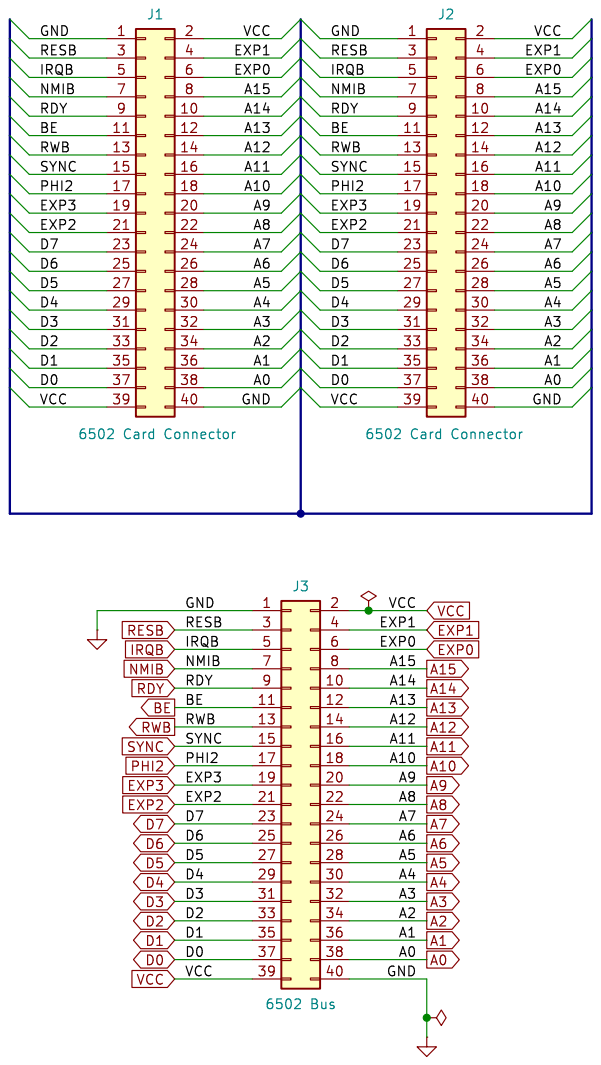
[picture p144: page 1]
