acwright/6502/Schematics/Clock Helper/Rev 1.0/Clock Helper.pdf

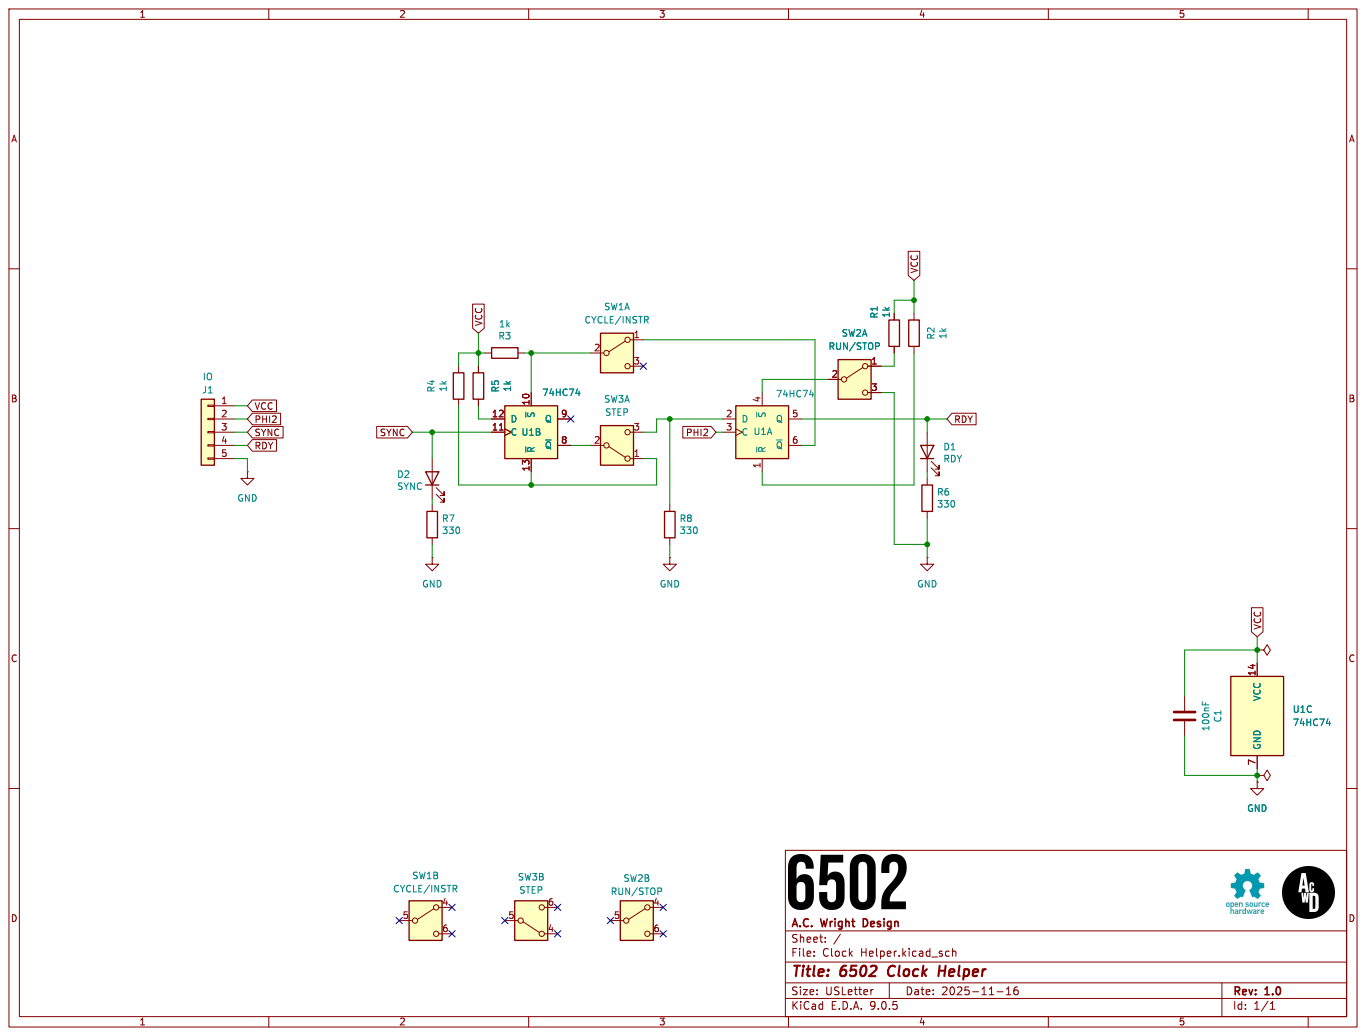
[picture p145: page 1]
