acwright/6502/Schematics/DB25 Helper/Rev 1.0/DB25 Helper.pdf

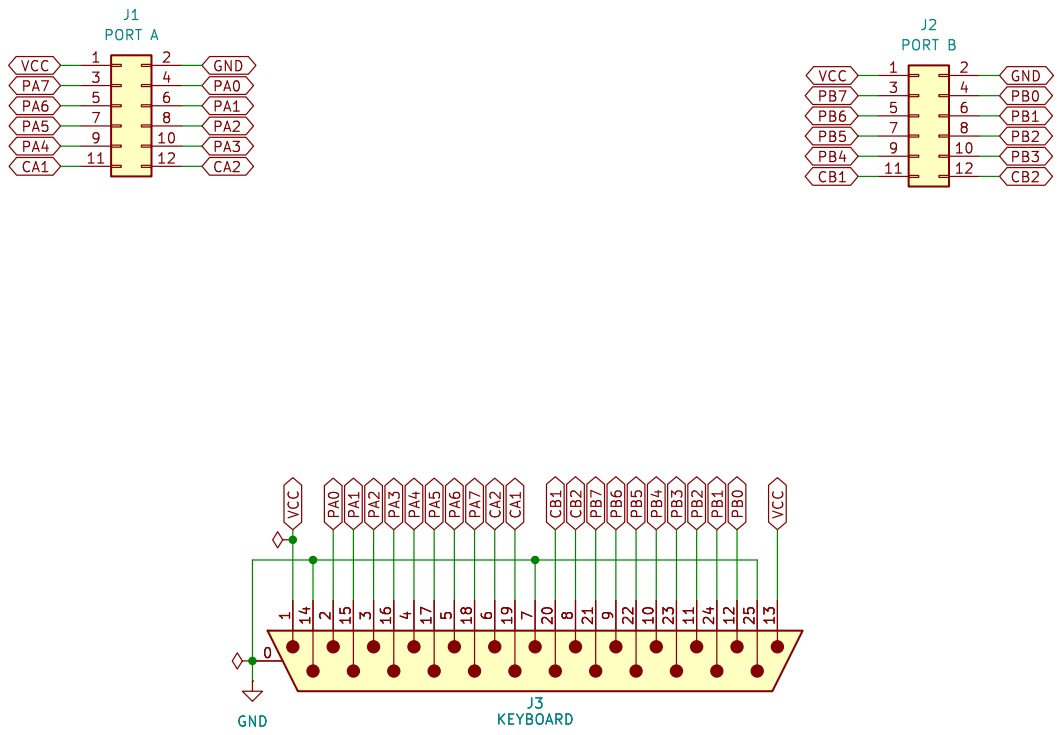
[picture p146: page 1]
