acwright/6502/Schematics/VERA Helper/Rev 1.0/VERA Helper.pdf

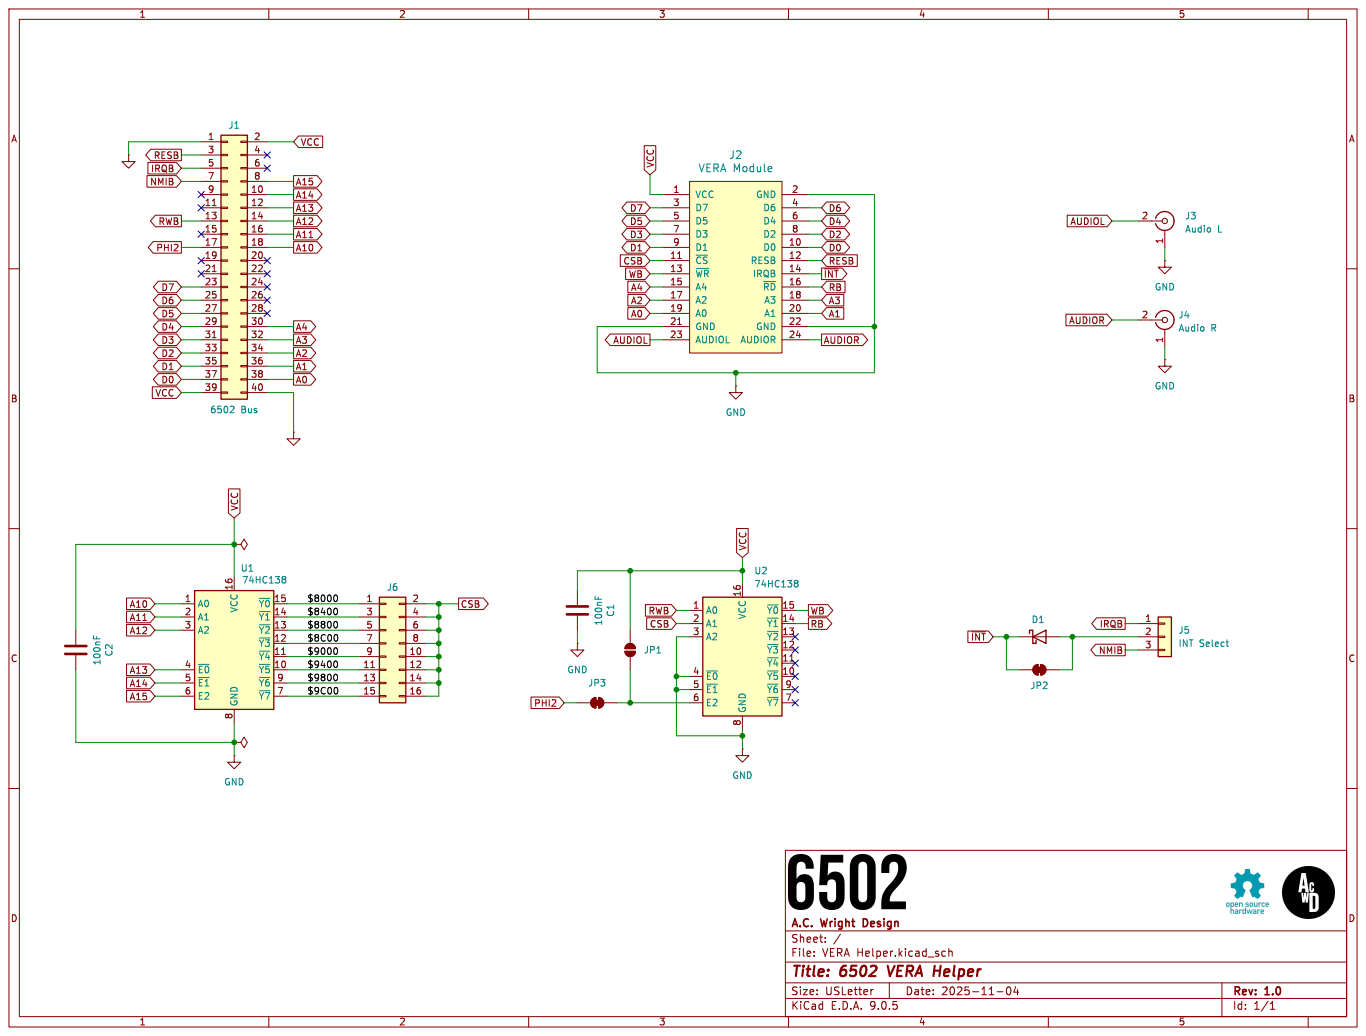
[picture p147: page 1]
