acwright/6502/Schematics/RAM Card/Rev 1.0/RAM Card.pdf

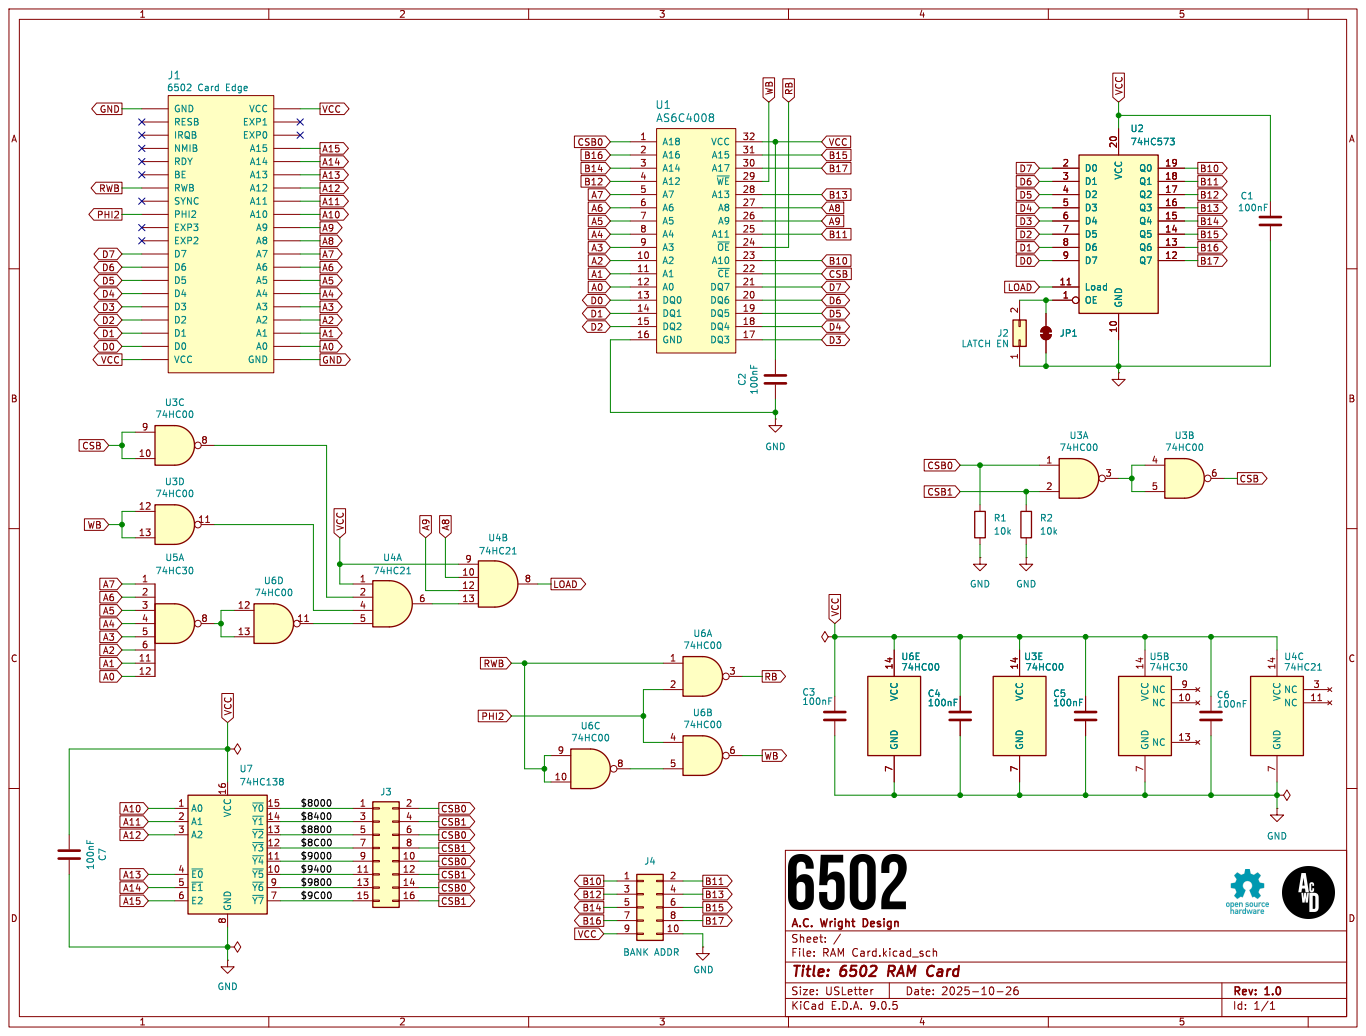
[picture p148: page 1]

Id: 1/1 Title: 6502 RAM Card
