acwright/6502/Schematics/Keyboard Helper/Rev 1.0/Keyboard Helper.pdf

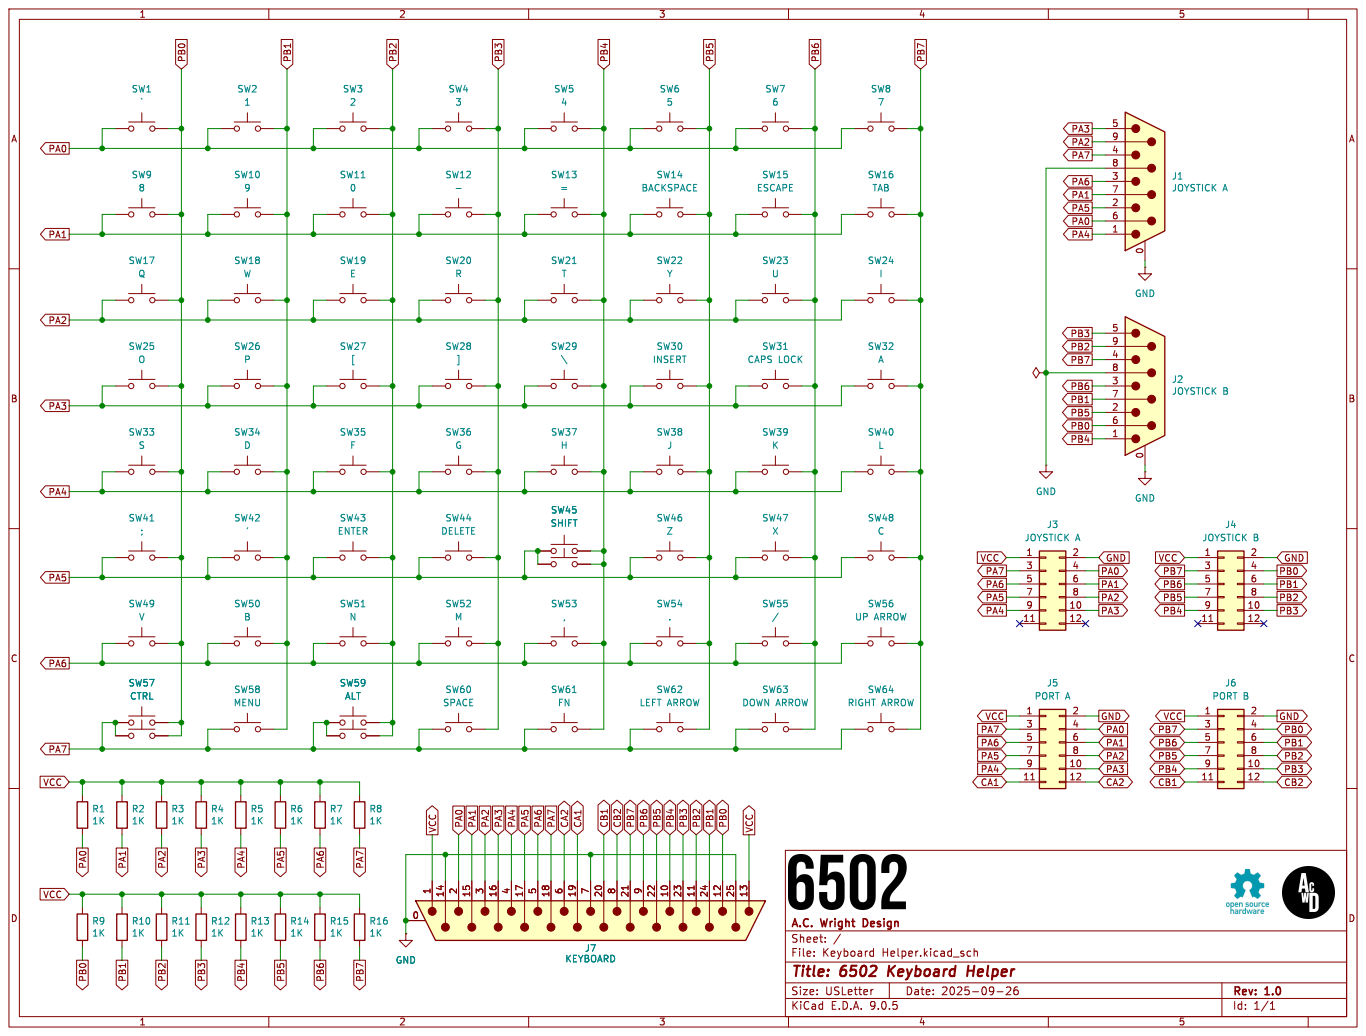
[picture p149: page 1]
