acwright/6502/Schematics/Joystick Helper/Rev 1.0/Joystick Helper.pdf

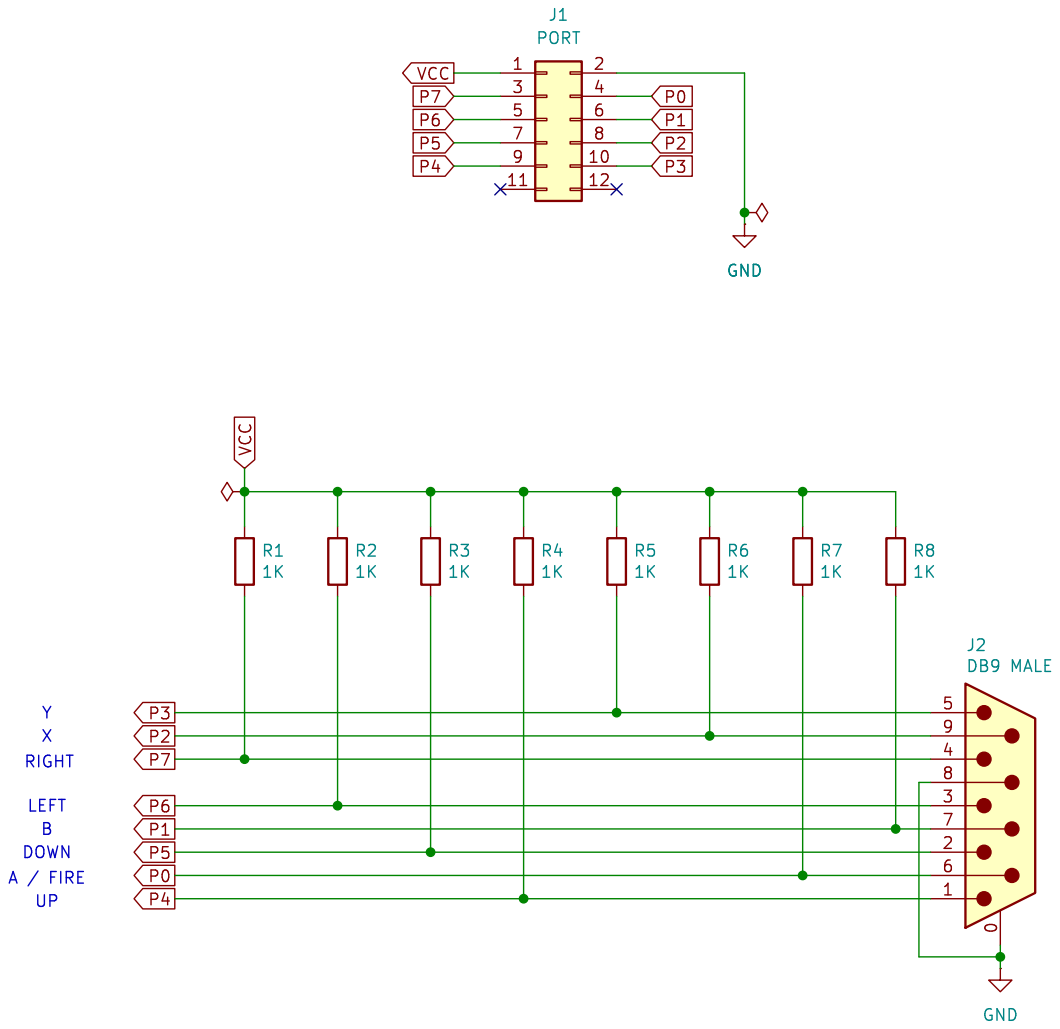
[picture p150: page 1]
