acwright/6502/Schematics/Serial Card Pro/Rev 1.0/Serial Card Pro.pdf

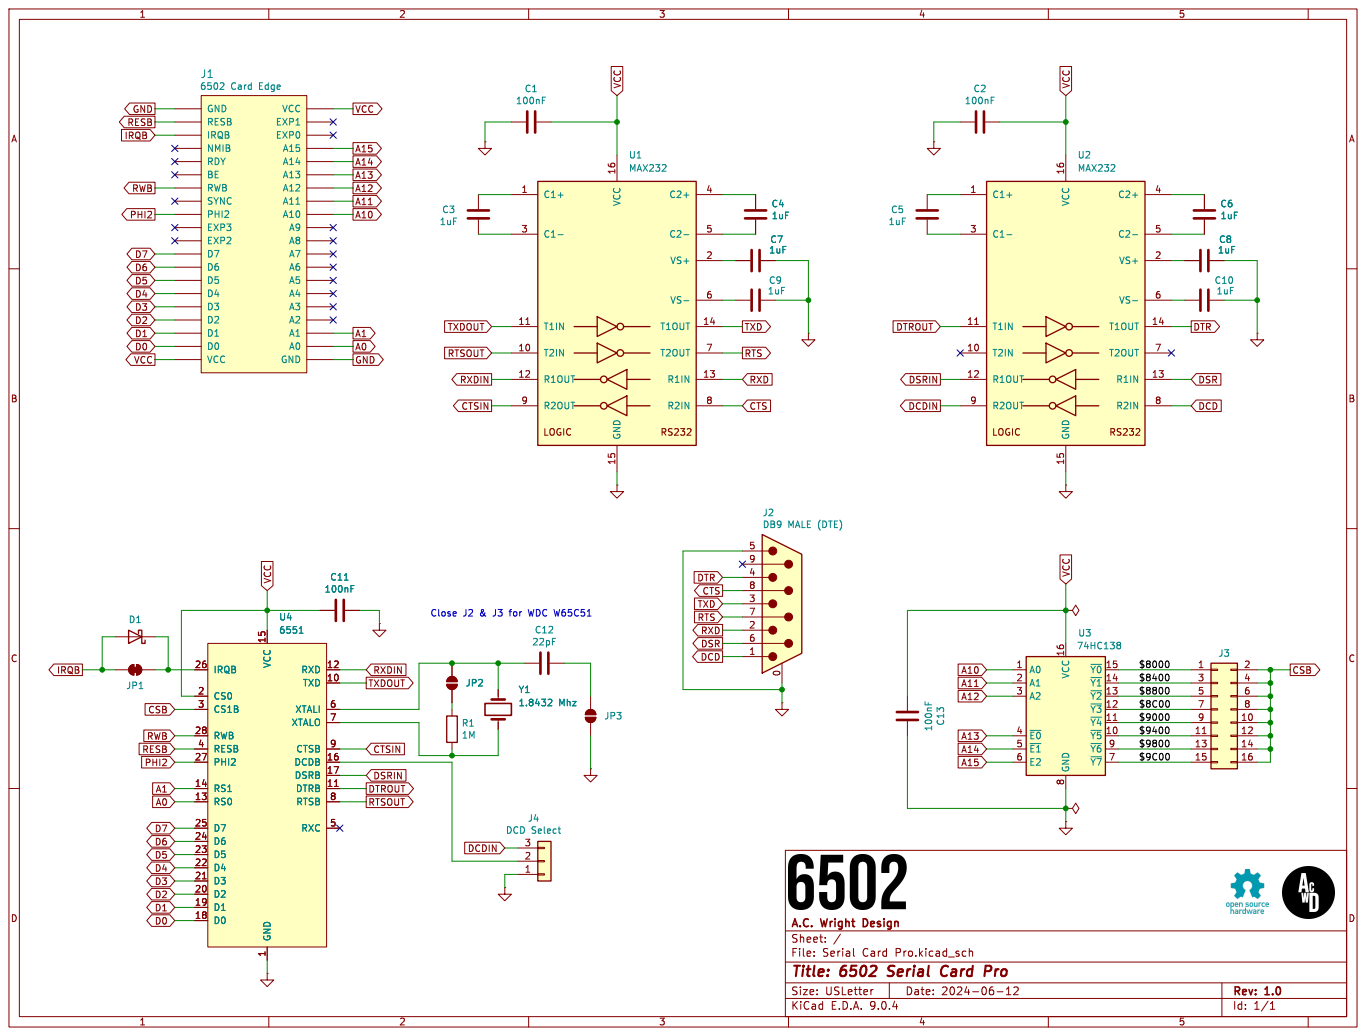
[picture p151: page 1]

1 RXD 12 TXD 10 XTALI 6 XTALO 7 CTSB 9 DCDB 16 DSRB 17 DTRB 11 RTSB 8 RXC 5 U4

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

Id: 1/1 Title: 6502 Serial Card Pro
