acwright/6502/Schematics/Serial Card/Rev 1.0/Serial Card.pdf

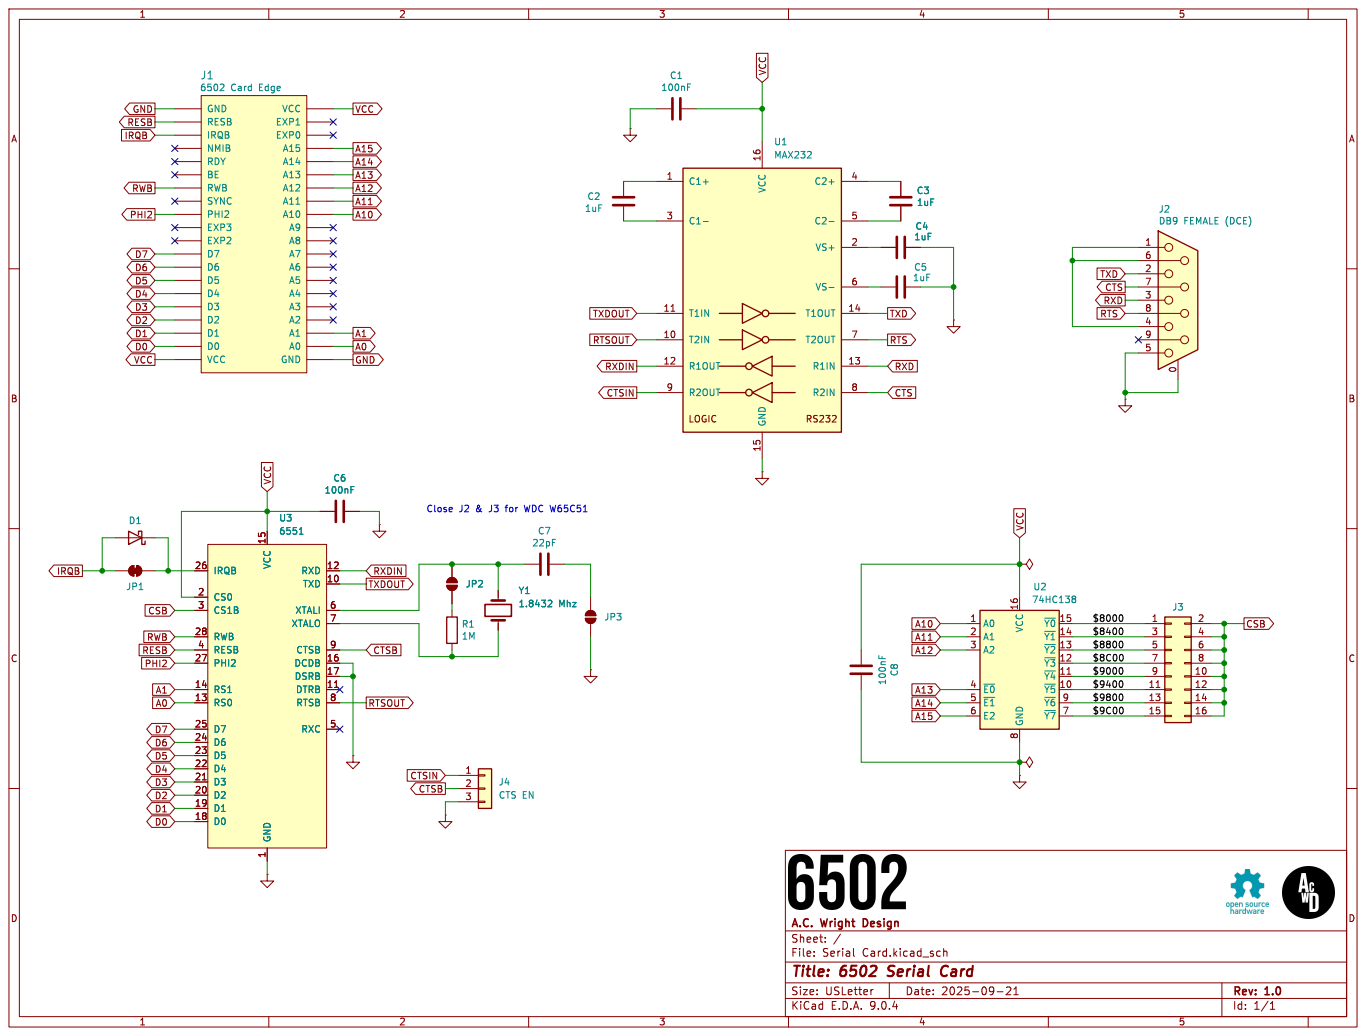
[picture p152: page 1]

CSB CTS RTS RXD

Id: 1/1 Title: 6502 Serial Card
