acwright/6502/Schematics/Keypad LCD Helper/Rev 1.0/Keypad LCD Helper.pdf

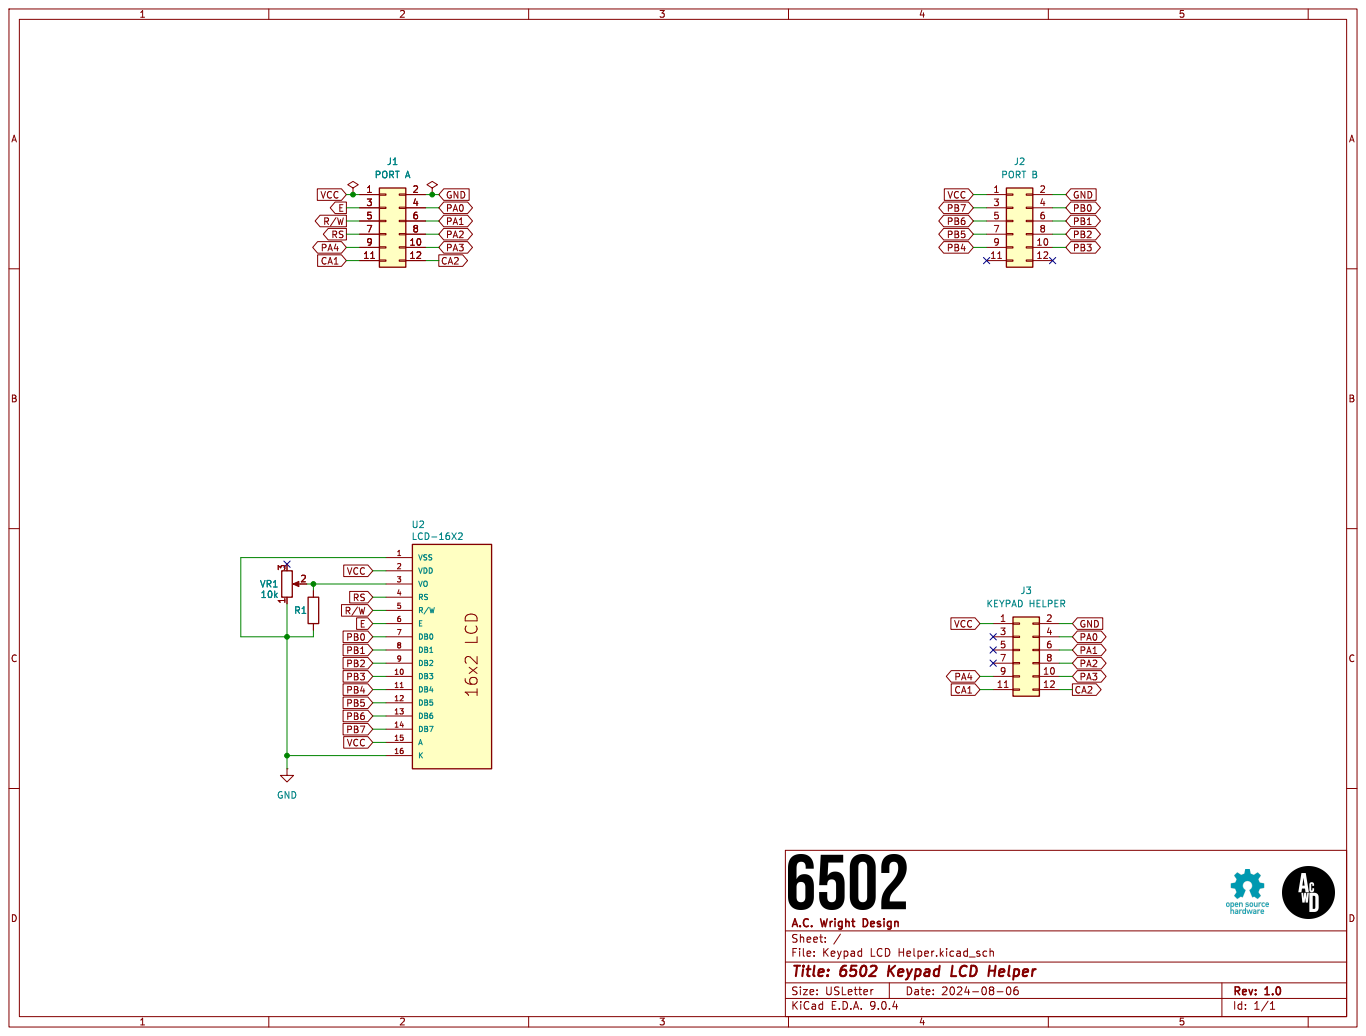
[picture p153: page 1]
