acwright/6502/Schematics/PS2 Helper/Rev 1.0/PS2 Helper.pdf

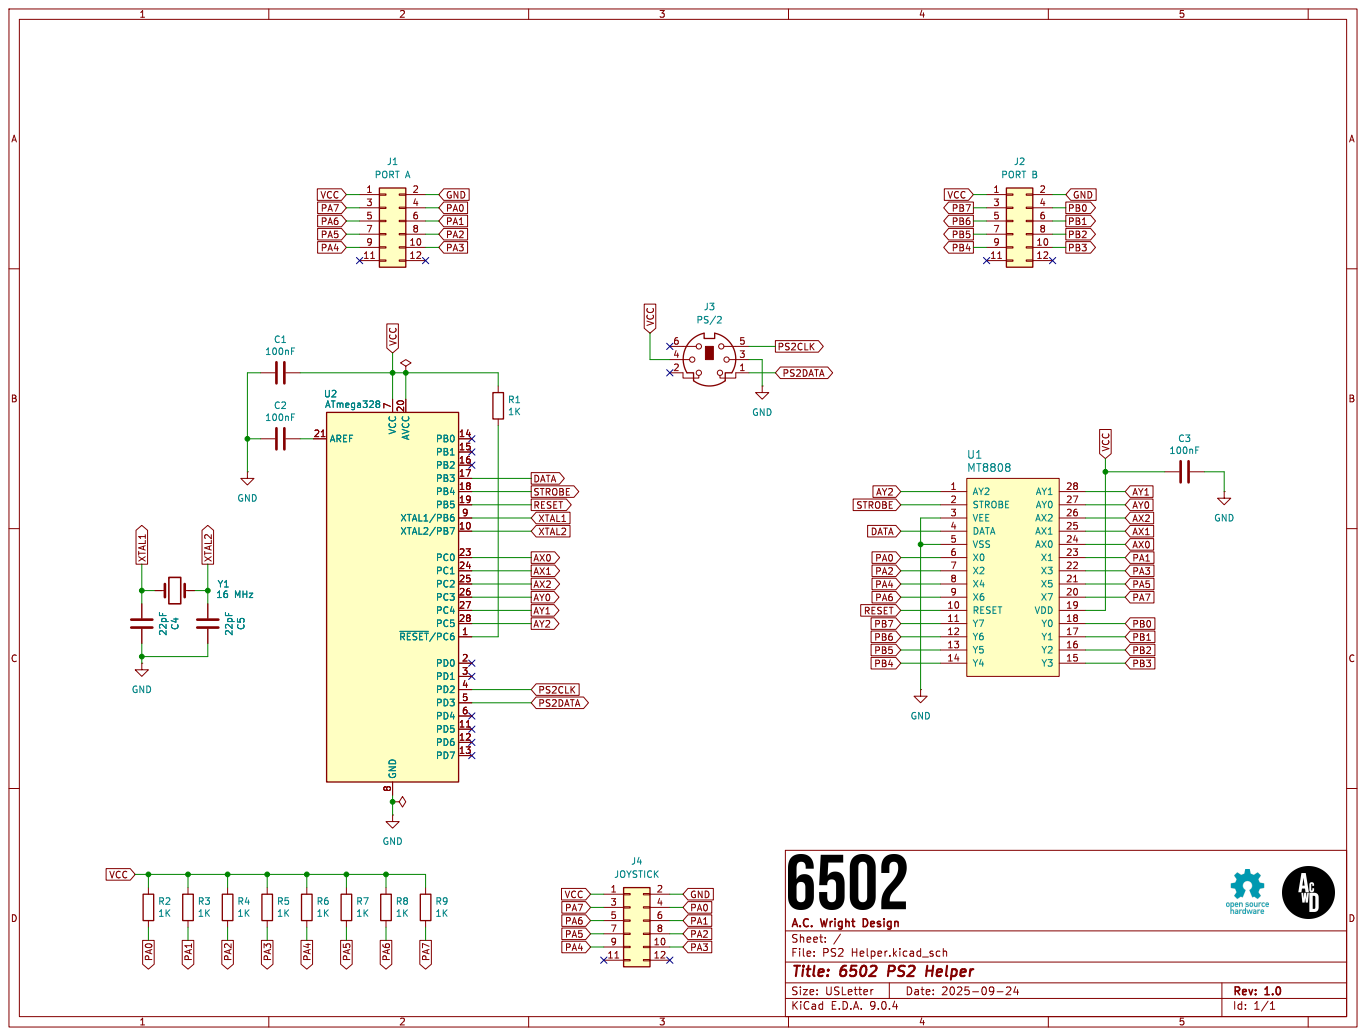
[picture p154: page 1]
