acwright/6502/Schematics/Backplane Pro/Rev 1.0/Backplane Pro.pdf

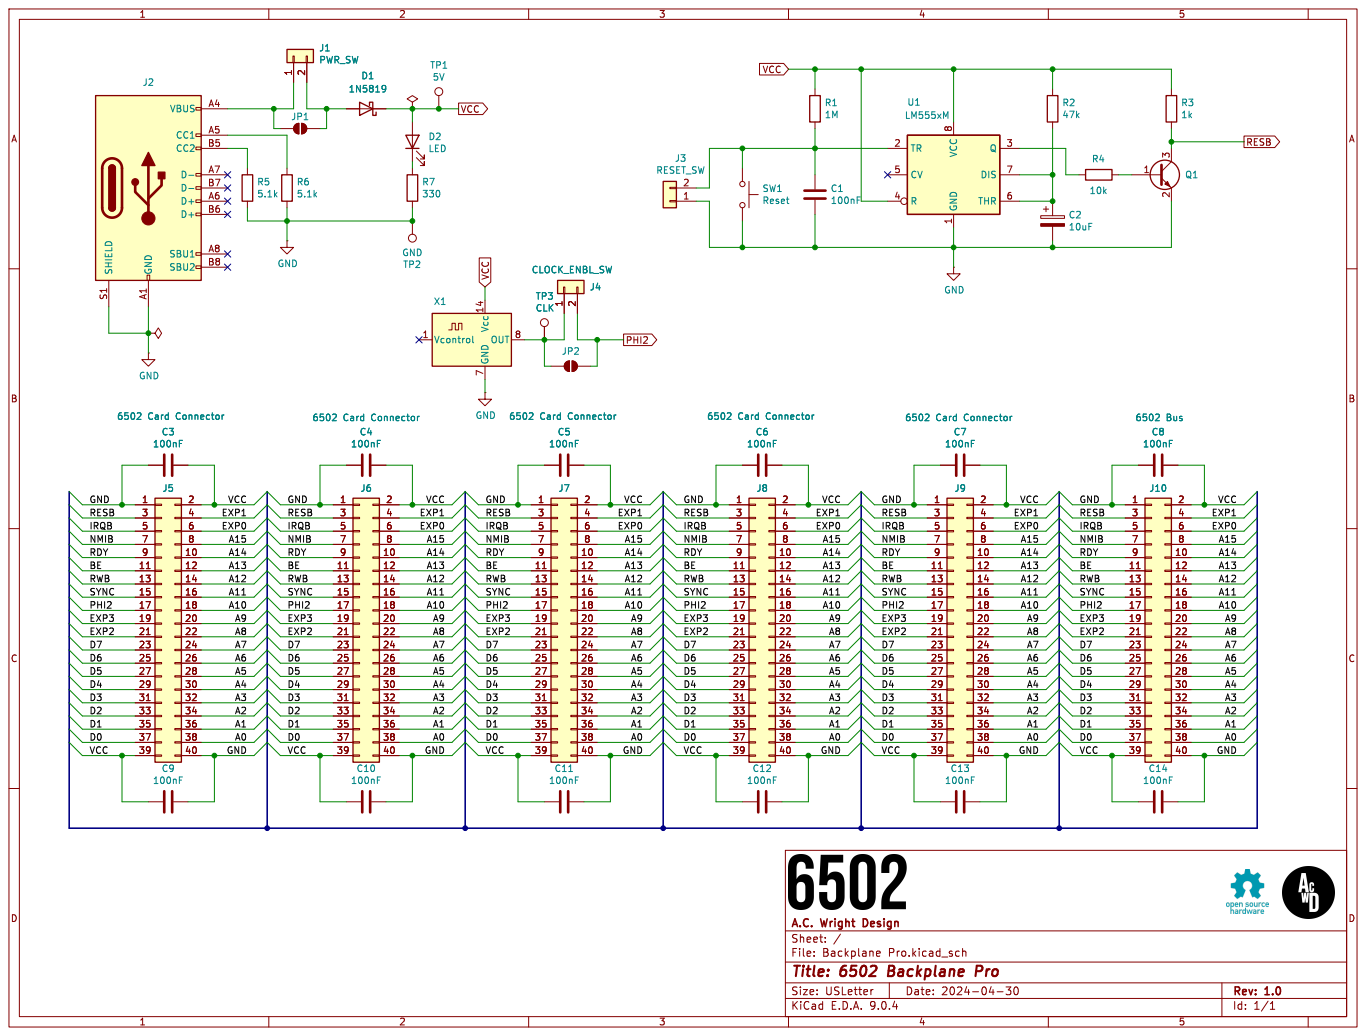
[picture p155: page 1]

Id: 1/1 Title: 6502 Backplane Pro
