acwright/6502/Schematics/Backplane/Rev 1.0/Backplane.pdf

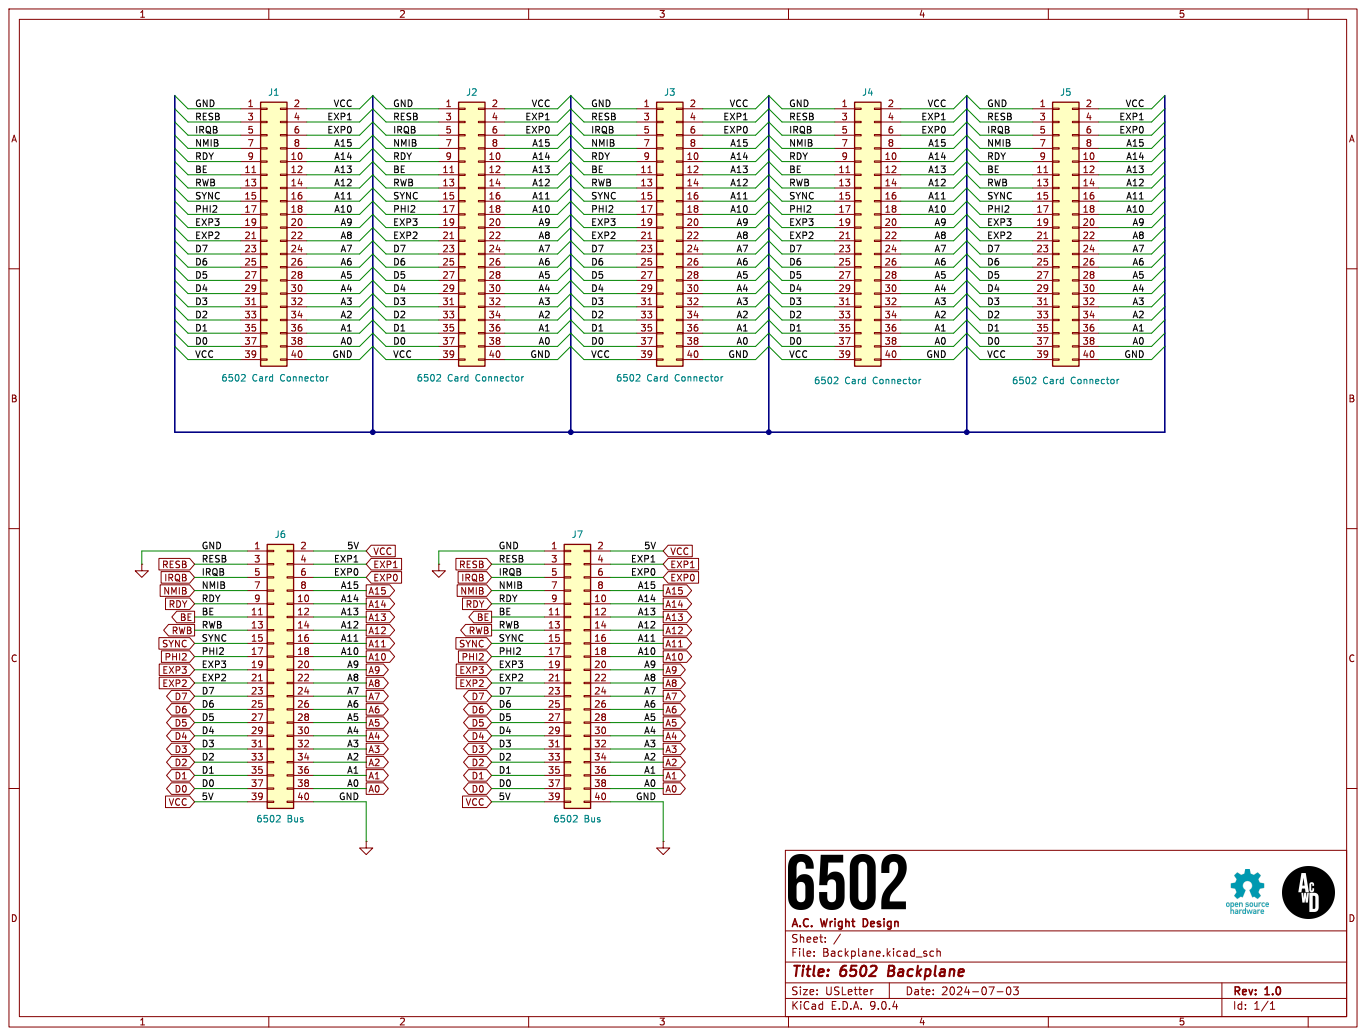
[picture p156: page 1]
