acwright/6502/Schematics/GPIO Helper/Rev 1.0/GPIO Helper.pdf

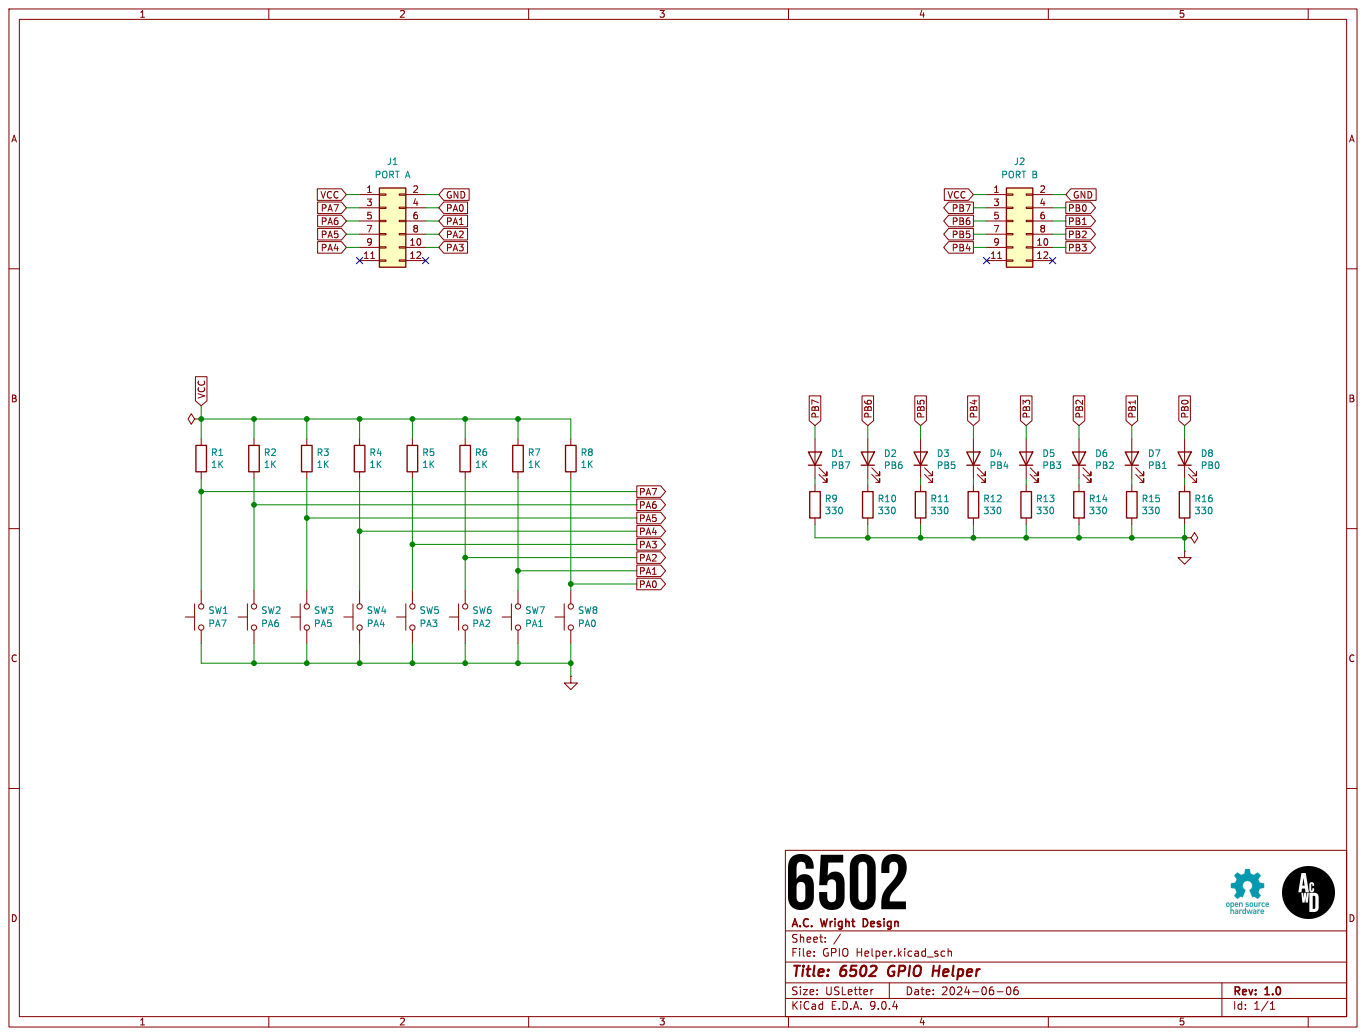
[picture p157: page 1]
