acwright/6502/Schematics/Storage Card/Rev 1.0/Storage Card.pdf

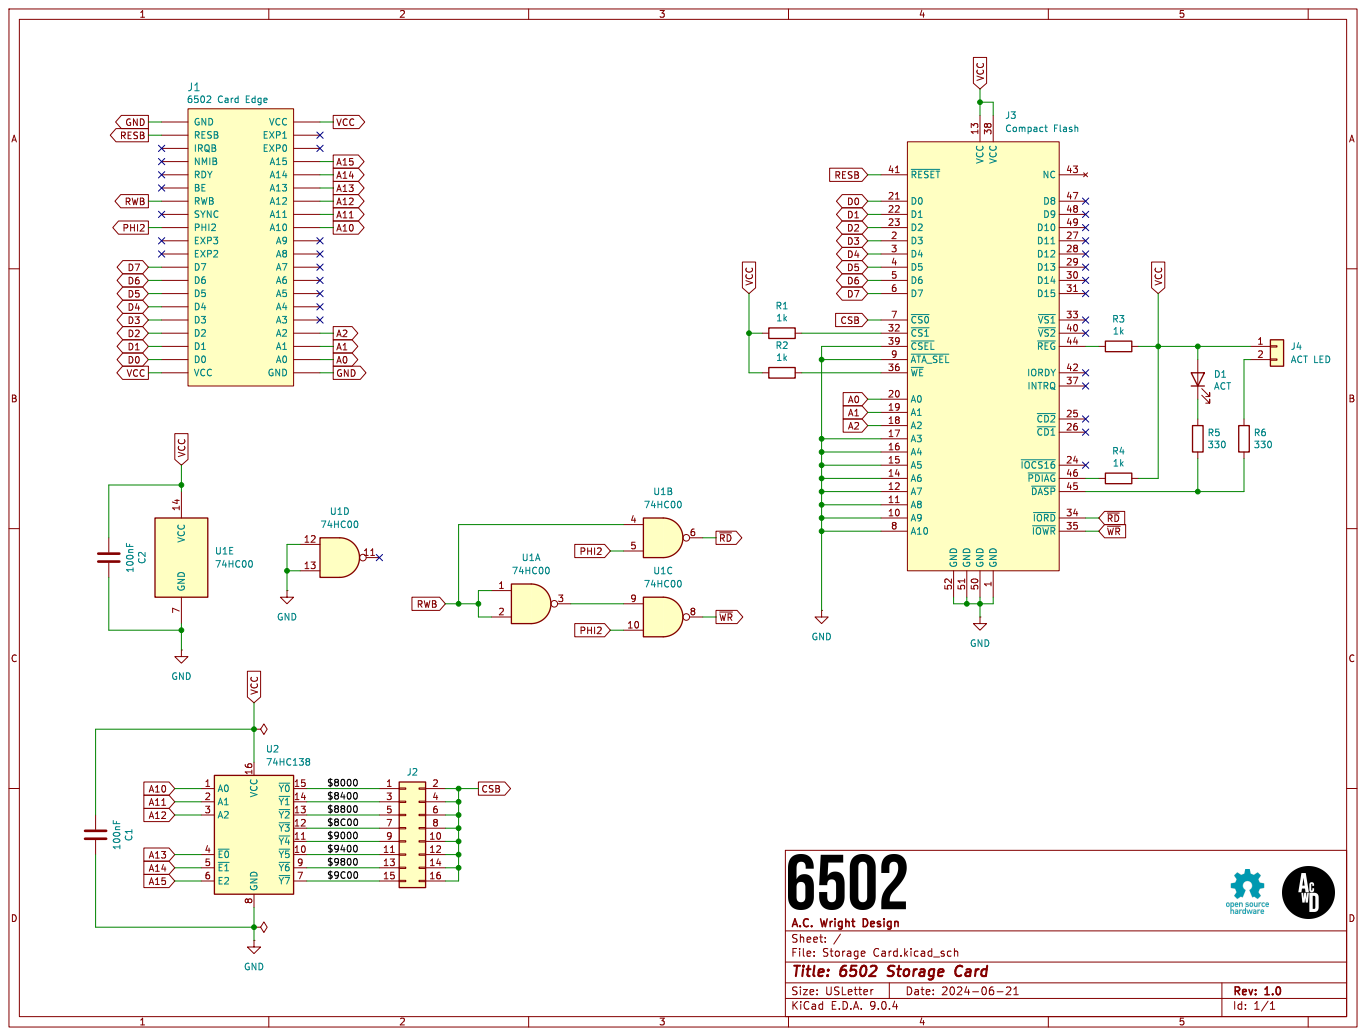
[picture p158: page 1]

Id: 1/1 Title: 6502 Storage Card
