acwright/6502/Schematics/RTC Card/Rev 1.0/RTC Card.pdf

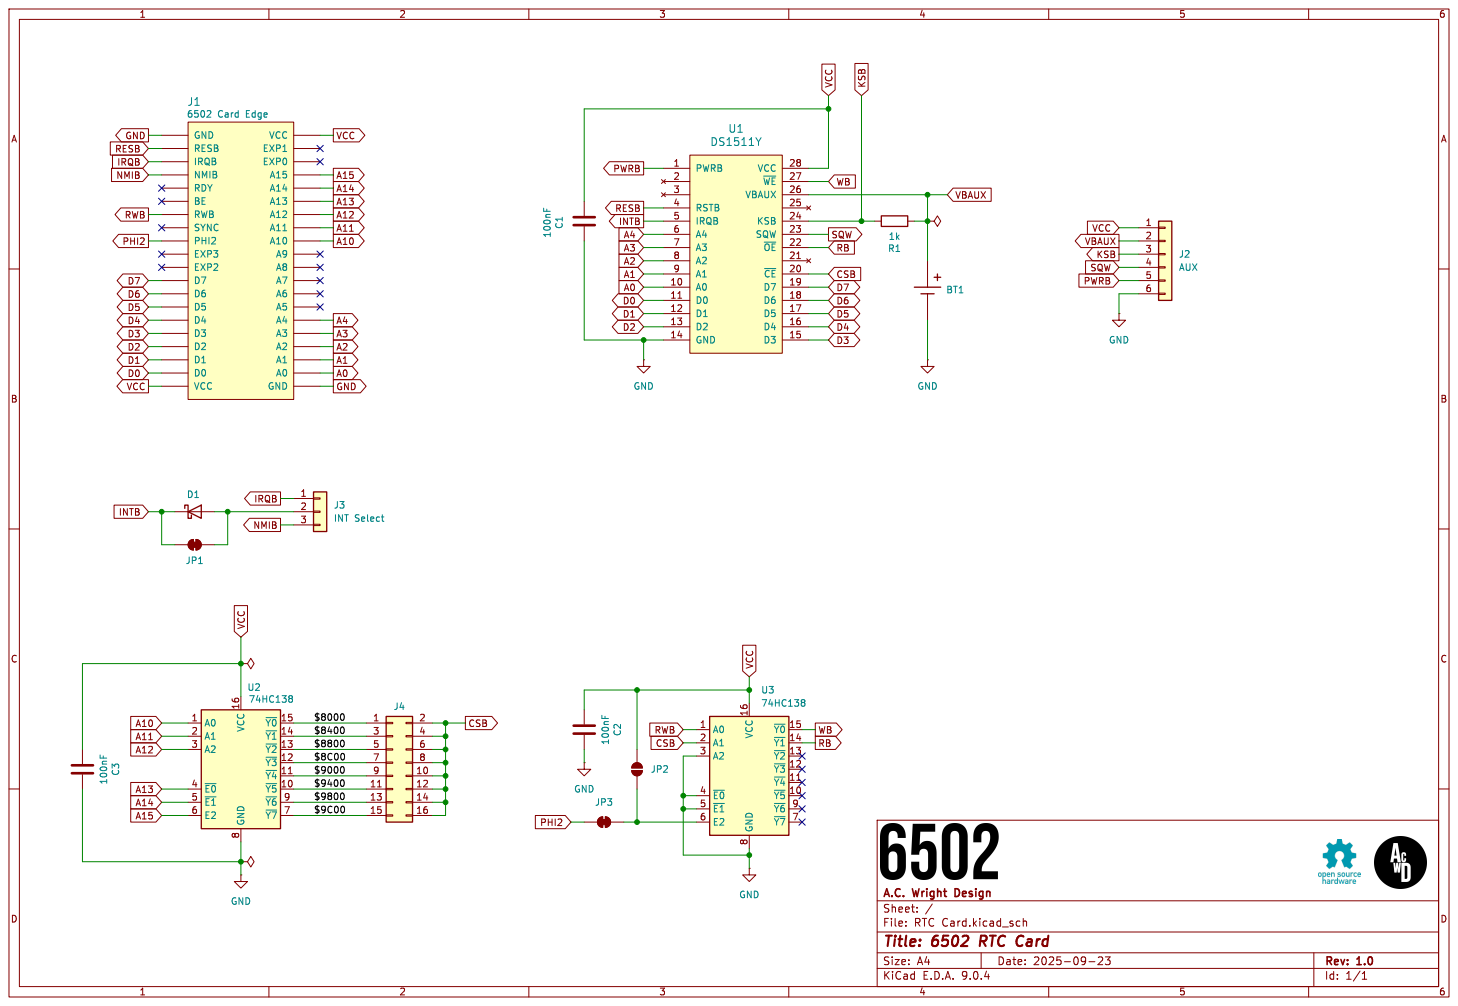
[picture p159: page 1]

Id: 1/1 Title: 6502 RTC Card
