acwright/6502/Schematics/GPIO Breadboard Helper/Rev 1.0/GPIO Breadboard Helper.pdf

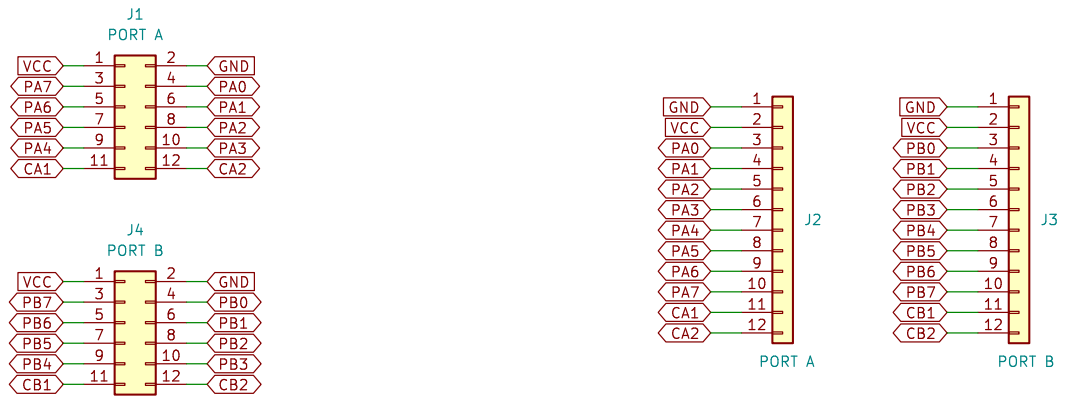
[picture p160: page 1]
