acwright/6502/Schematics/GPIO Card/Rev 1.0/GPIO Card.pdf

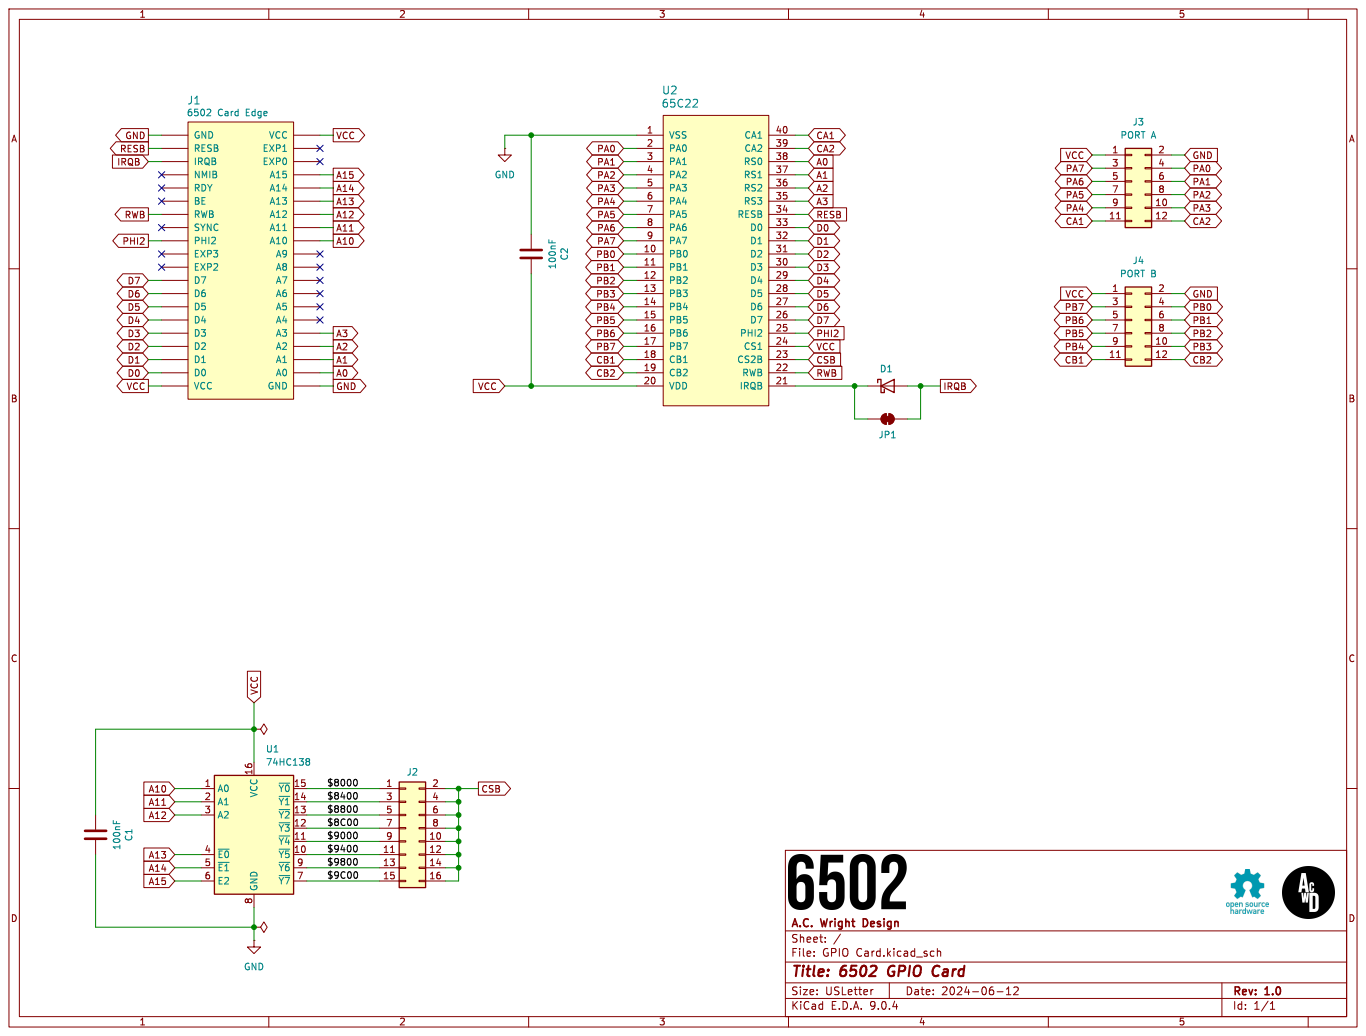
[picture p161: page 1]

Id: 1/1 Title: 6502 GPIO Card
