acwright/6502/Schematics/LCD Card/Rev 1.0/LCD Card.pdf

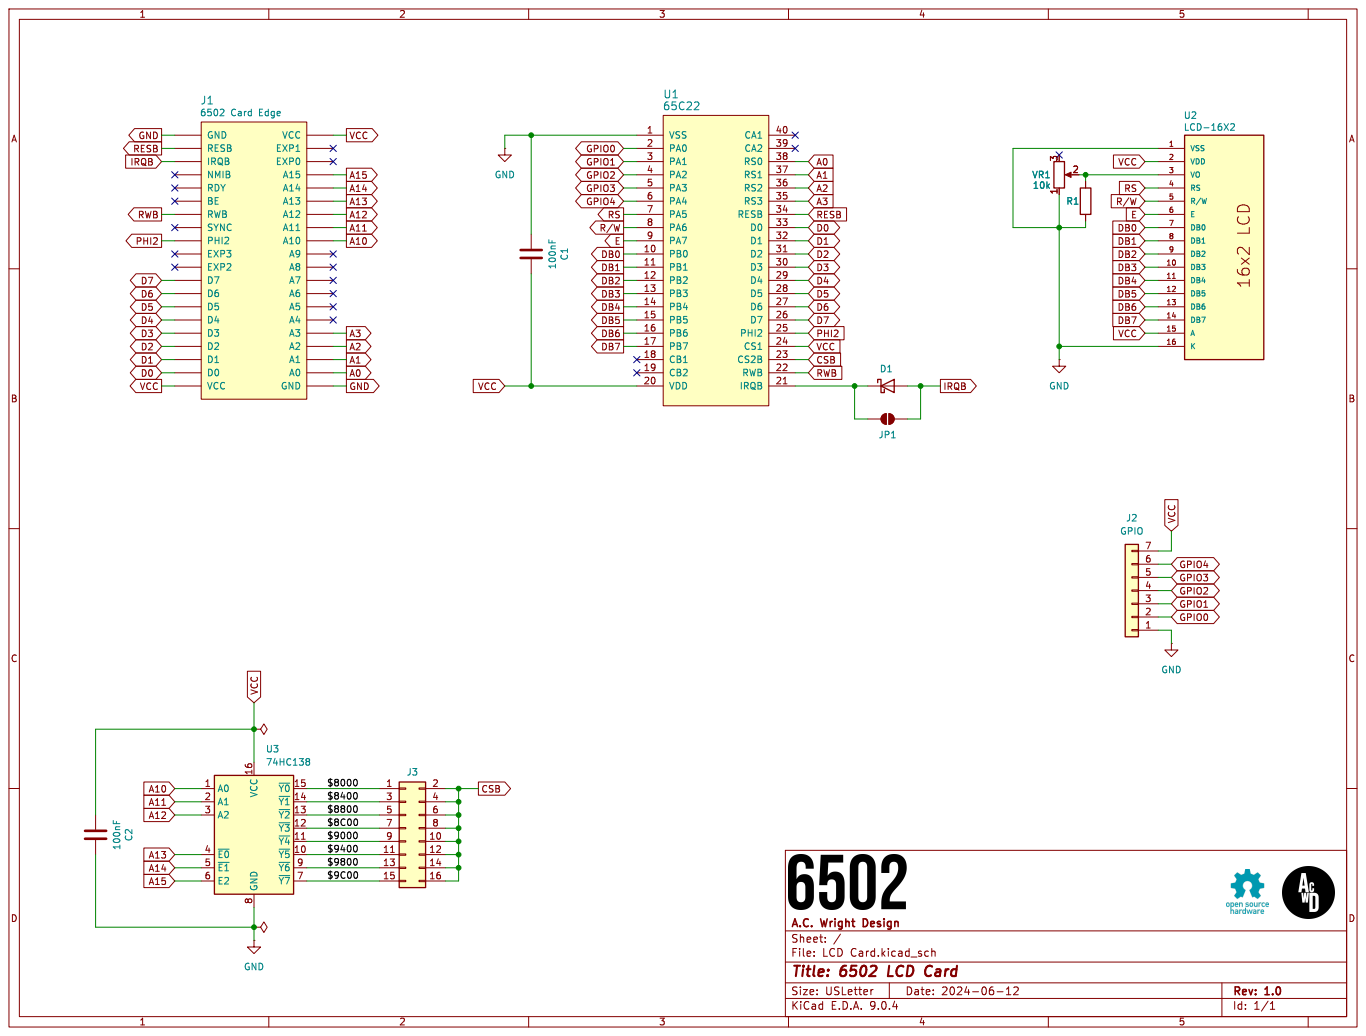
[picture p162: page 1]

Id: 1/1 Title: 6502 LCD Card
