acwright/6502/Schematics/Memory Card/Rev 1.0/Memory Card.pdf

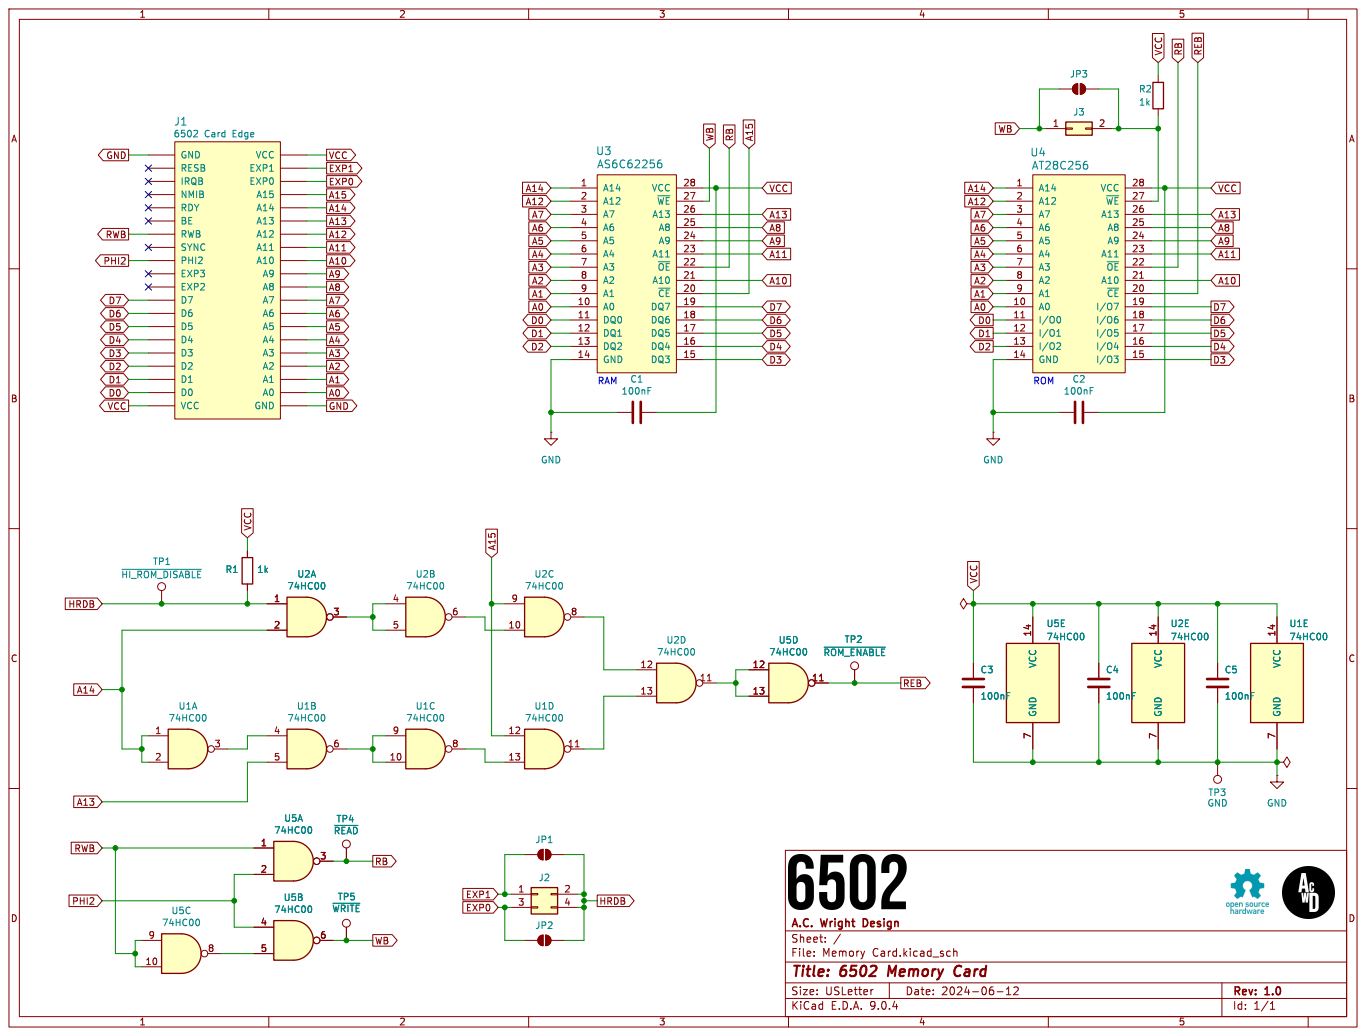
[picture p163: page 1]

Id: 1/1 Title: 6502 Memory Card
