acwright/6502/Schematics/Blinkenlights Card/Rev 1.0/Blinkenlights Card.pdf

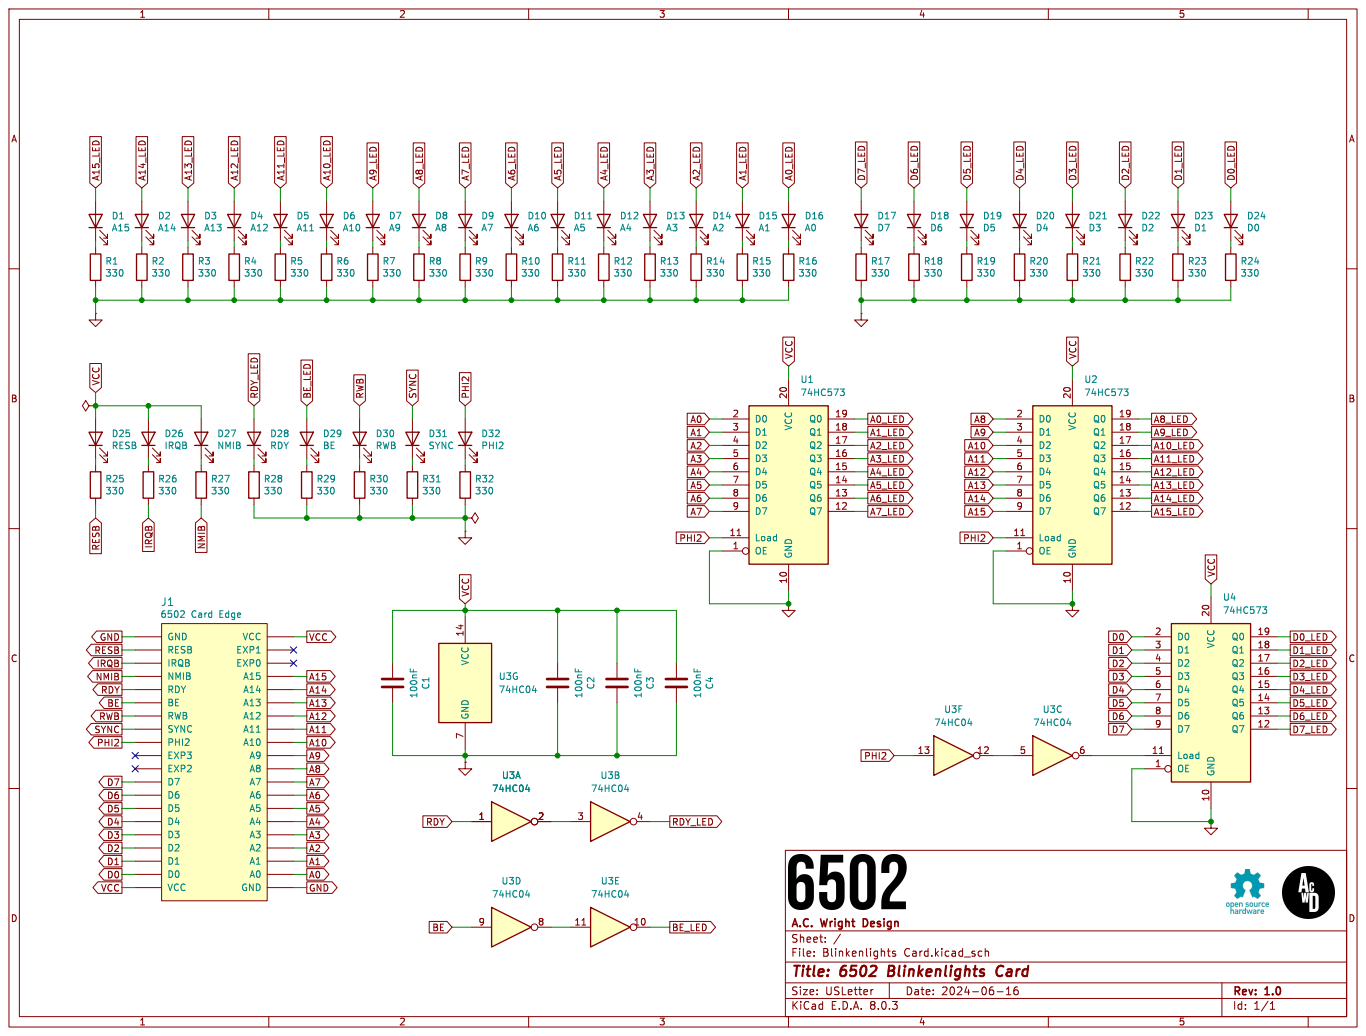
[picture p164: page 1]
