acwright/6502/Schematics/Breadboard Helper/Rev 1.0/Breadboard Helper.pdf

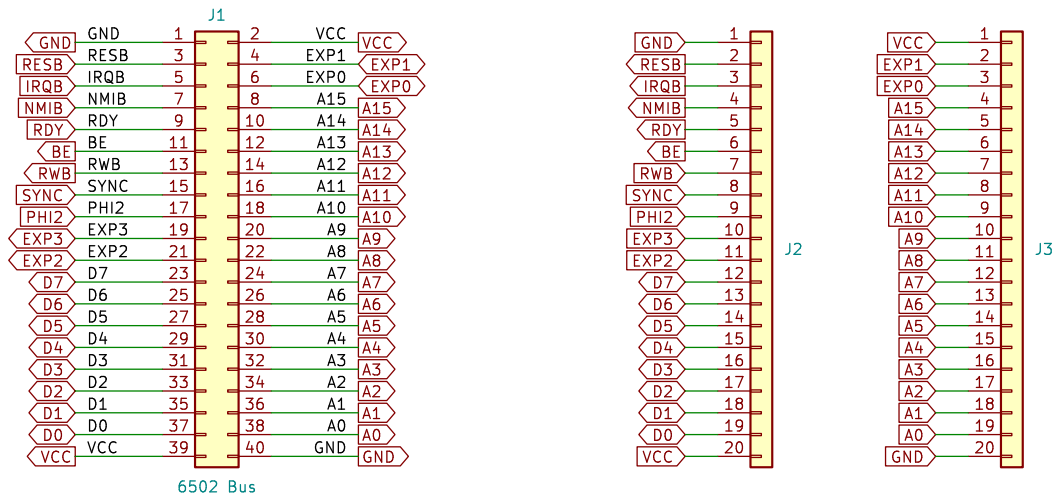
[picture p165: page 1]
