acwright/6502/Hardware/Keyboard Encoder Helper/Rev 1.0/Keyboard Encoder Helper.kicad_pcb

## KiCad design Hardware/Keyboard Encoder Helper/Rev 1.0/Keyboard Encoder Helper.kicad_pcb (2026-01-31)

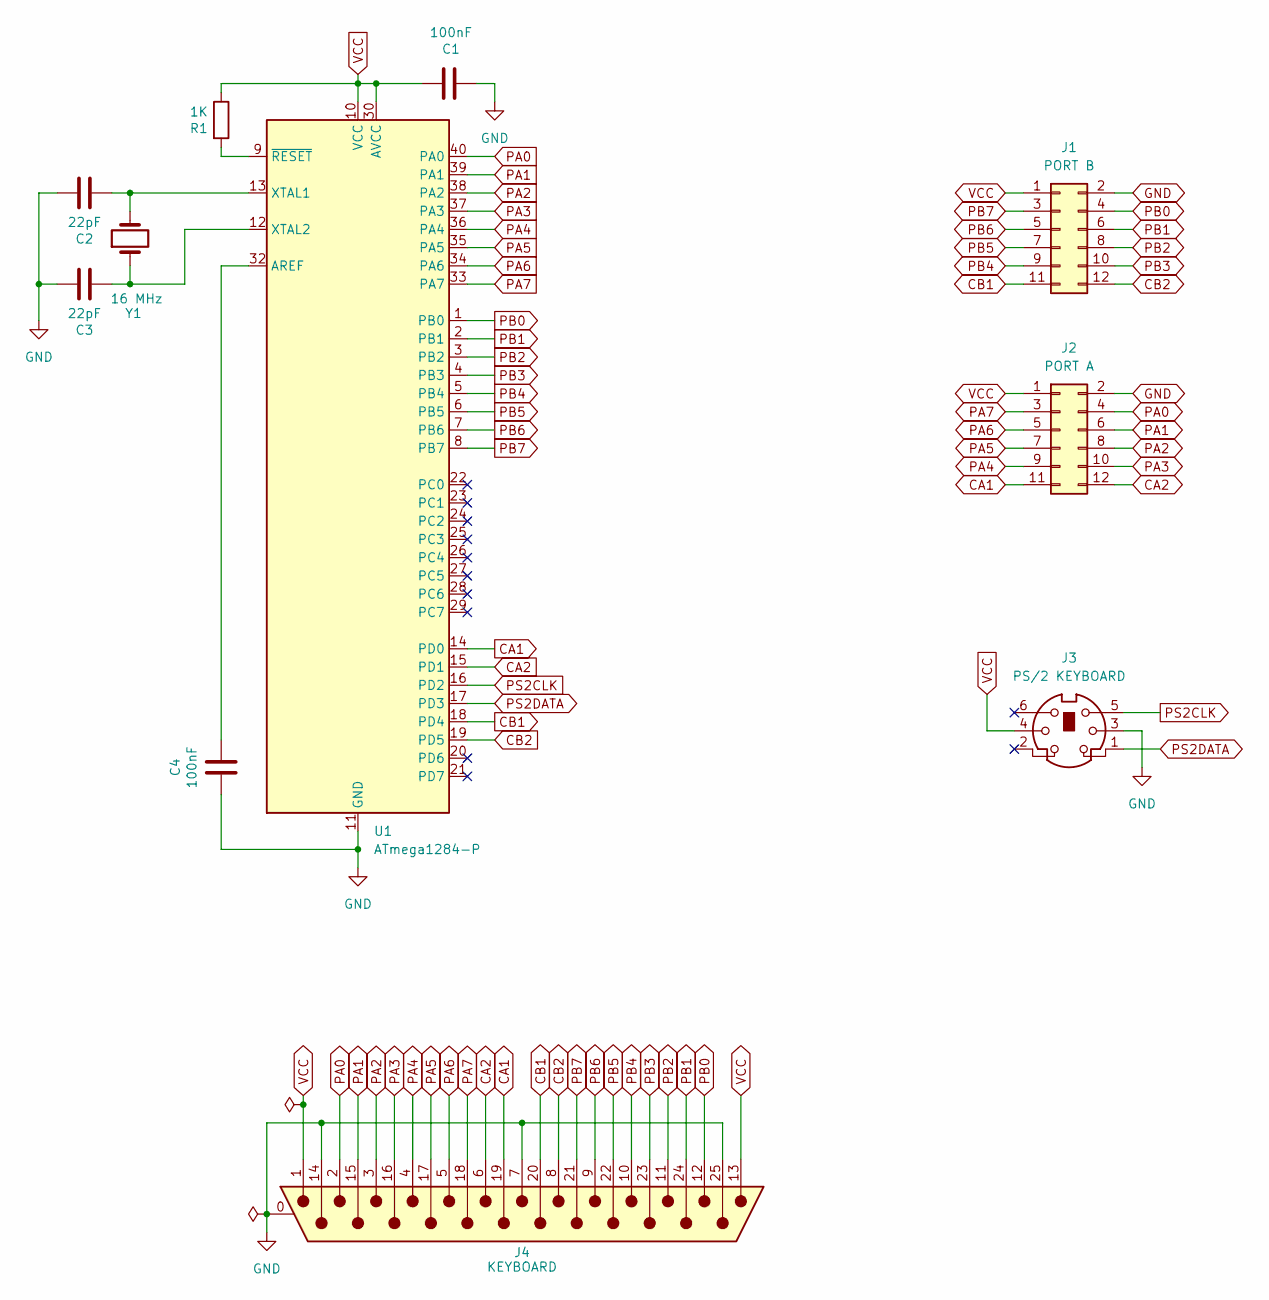
[picture p184: schematic Keyboard Encoder Helper.kicad_sch, 6502 Keyboard Encoder Helper]

Parts:
C1, C4: 100nF; C_Disc_D5.0mm_W2.5mm_P2.50mm; LCSC C107114
C2, C3: 22pF; C_Disc_D5.0mm_W2.5mm_P2.50mm; LCSC C107114
J1: PORT B; 6502 GPIO Connector
J2: PORT A; 6502 GPIO Connector
J3: PS/2 KEYBOARD; KMDGX-6S-BS
J4: KEYBOARD; DSUB-25_Pins_Horizontal_P2.77x2.84mm_EdgePinOffset7.70mm_Ho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; MPN D25P33E4GX00LF; Digikey 609-1505-ND
R1: 1K; R_Axial_DIN0204_L3.6mm_D1.6mm_P5.08mm_Horizontal
U1: ATmega1284-P; DIP-40_W15.24mm_Socket_LongPads
Y1: 16 MHz; Crystal_HC49-U_Vertical; Digikey 3155-16M20P2/49US-ND

Connections:
CA1: J2.11, J4.19, U1.14 (PD0)
CA2: J2.12, J4.6, U1.15 (PD1)
CB1: J1.11, J4.20, U1.18 (PD4)
CB2: J1.12, J4.8, U1.19 (PD5)
GND: C1.1, C2.2, C3.2, C4.1, J1.2, J2.2, J3.3, J4.0 (PAD), J4.7, J4.14, J4.25, U1.11 (GND), U1.31 (GND)
unnamed: C4.2, U1.32 (AREF)
unnamed: C2.1, U1.13 (XTAL1), Y1.2
unnamed: C3.1, U1.12 (XTAL2), Y1.1
unnamed: R1.2, U1.9 (~RESET)
PA0: J2.4, J4.2, U1.40 (PA0)
PA1: J2.6, J4.15, U1.39 (PA1)
PA2: J2.8, J4.3, U1.38 (PA2)
PA3: J2.10, J4.16, U1.37 (PA3)
PA4: J2.9, J4.4, U1.36 (PA4)
PA5: J2.7, J4.17, U1.35 (PA5)
PA6: J2.5, J4.5, U1.34 (PA6)
PA7: J2.3, J4.18, U1.33 (PA7)
PB0: J1.4, J4.12, U1.1 (PB0)
PB1: J1.6, J4.24, U1.2 (PB1)
PB2: J1.8, J4.11, U1.3 (PB2)
PB3: J1.10, J4.23, U1.4 (PB3)
PB4: J1.9, J4.10, U1.5 (PB4)
PB5: J1.7, J4.22, U1.6 (PB5)
PB6: J1.5, J4.9, U1.7 (PB6)
PB7: J1.3, J4.21, U1.8 (PB7)
PS2CLK: J3.5, U1.16 (PD2)
PS2DATA: J3.1, U1.17 (PD3)
VCC: C1.2, J1.1, J2.1, J3.4, J4.1, J4.13, R1.1, U1.10 (VCC), U1.30 (AVCC)

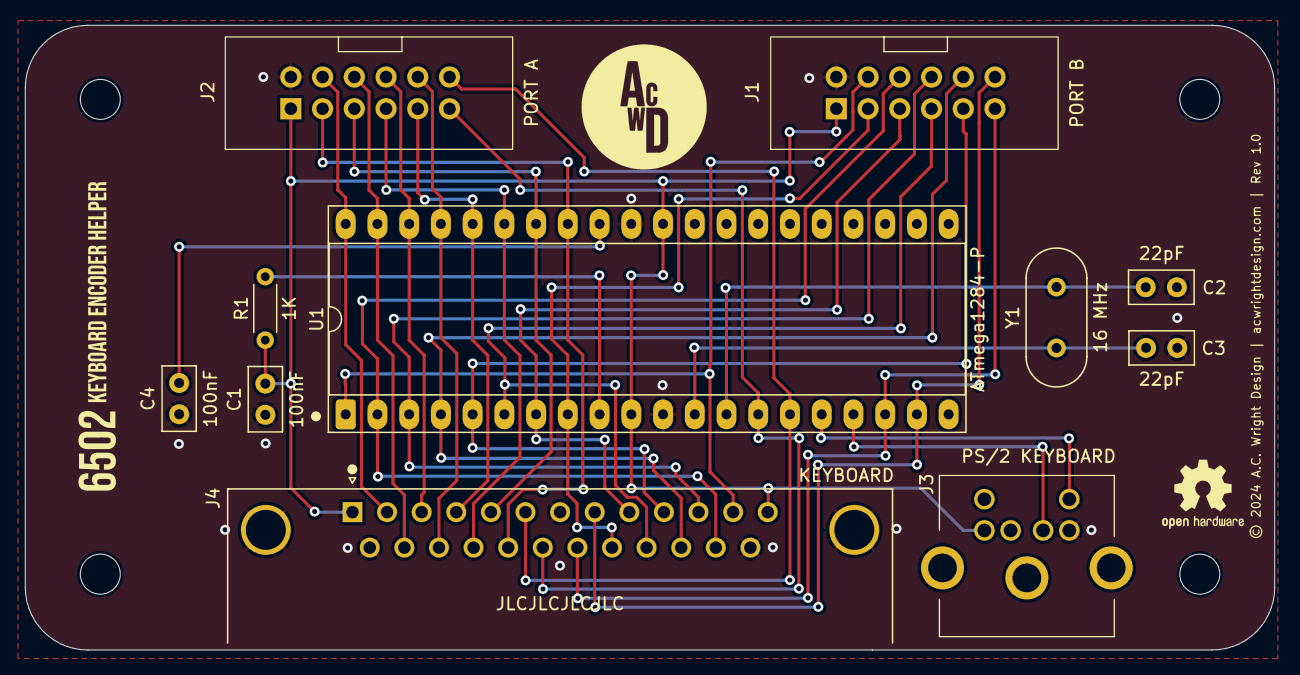
[picture p185: board Keyboard Encoder Helper.kicad_pcb from above]

Board: 2 copper layers, 100.0 x 50.0 mm, 15 parts (0 on the bottom side), 28 nets.

Other parts of the board:
H1, H2, H3, H4: MountingHole; MountingHole_3.2mm_M3
