acwright/6502/Hardware/Joystick Helper/Rev 1.0/Joystick Helper.kicad_pcb

## KiCad design Hardware/Joystick Helper/Rev 1.0/Joystick Helper.kicad_pcb (2026-01-31)

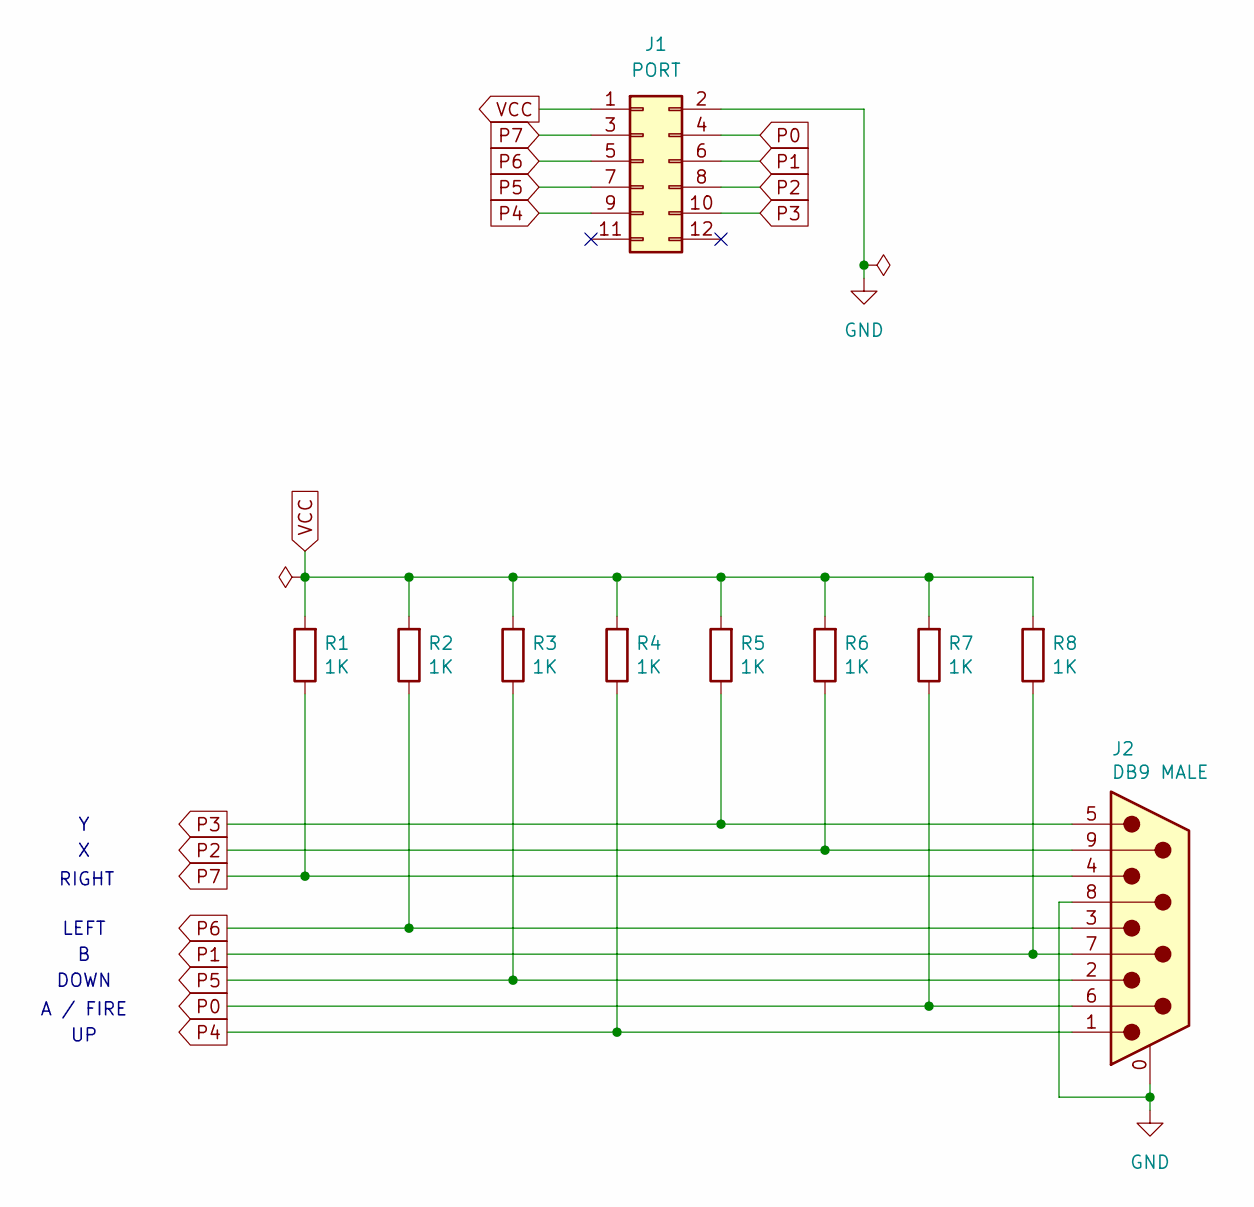
[picture p186: schematic Joystick Helper.kicad_sch, 6502 Joystick Helper]

Parts:
J1: PORT; 6502 GPIO Connector
J2: DB9 MALE; DSUB-9_Pins_Horizontal_P2.77x2.84mm_EdgePinOffset7.70mm_Hou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; MPN D09P33E4GX00LF; Digikey 609-1481-ND
R1, R2, R3, R4, R5, R6, R7, R8: 1K; R_Axial_DIN0204_L3.6mm_D1.6mm_P5.08mm_Horizontal

Connections:
GND: J1.2, J2.0 (PAD), J2.8
P0: J1.4, J2.6, R7.1
P1: J1.6, J2.7, R8.1
P2: J1.8, J2.9, R6.1
P3: J1.10, J2.5, R5.1
P4: J1.9, J2.1, R4.1
P5: J1.7, J2.2, R3.1
P6: J1.5, J2.3, R2.1
P7: J1.3, J2.4, R1.1
VCC: J1.1, R1.2, R2.2, R3.2, R4.2, R5.2, R6.2, R7.2, R8.2

Notes on the sheet:
LEFT
DOWN
RIGHT
A / FIRE

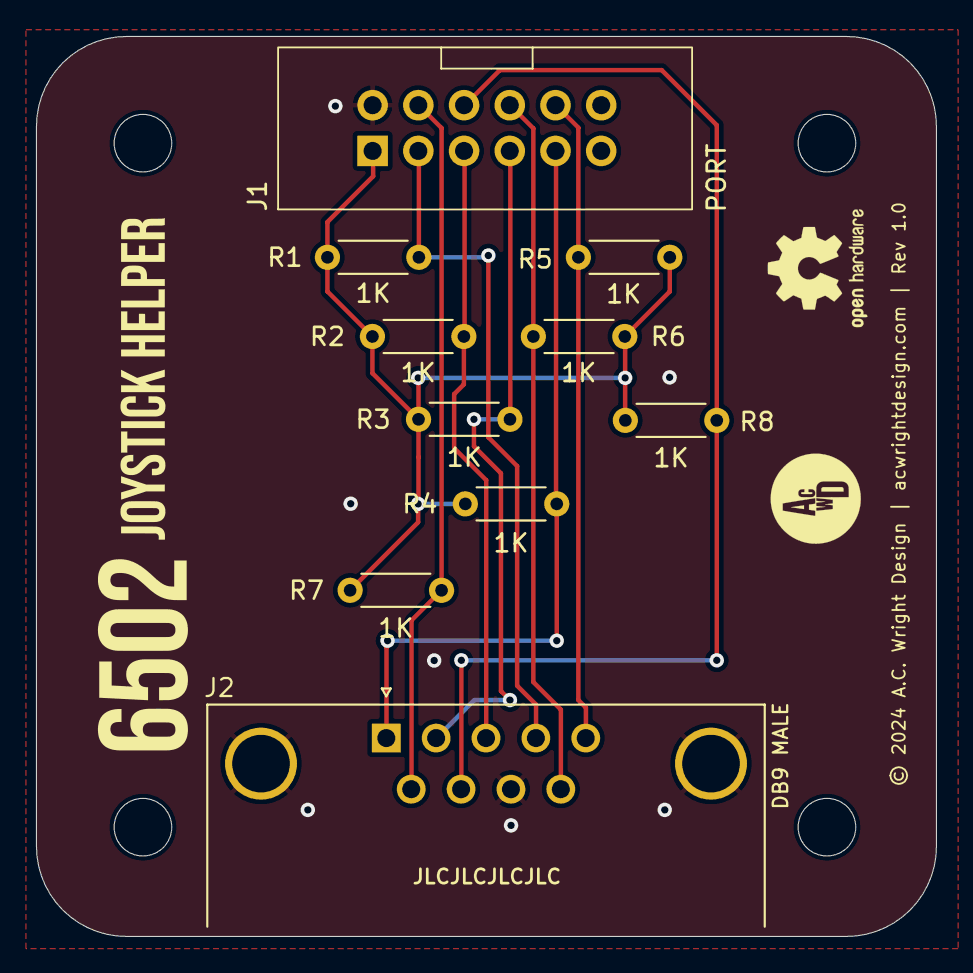
[picture p187: board Joystick Helper.kicad_pcb from above]

Board: 2 copper layers, 50.0 x 50.0 mm, 14 parts (0 on the bottom side), 10 nets.

Other parts of the board:
H1, H2, H3, H4: MountingHole; MountingHole_3.2mm_M3
