acwright/6502/Hardware/PS2 Helper/Rev 1.0/PS2 Helper.kicad_pcb

## KiCad design Hardware/PS2 Helper/Rev 1.0/PS2 Helper.kicad_pcb (2026-01-31)

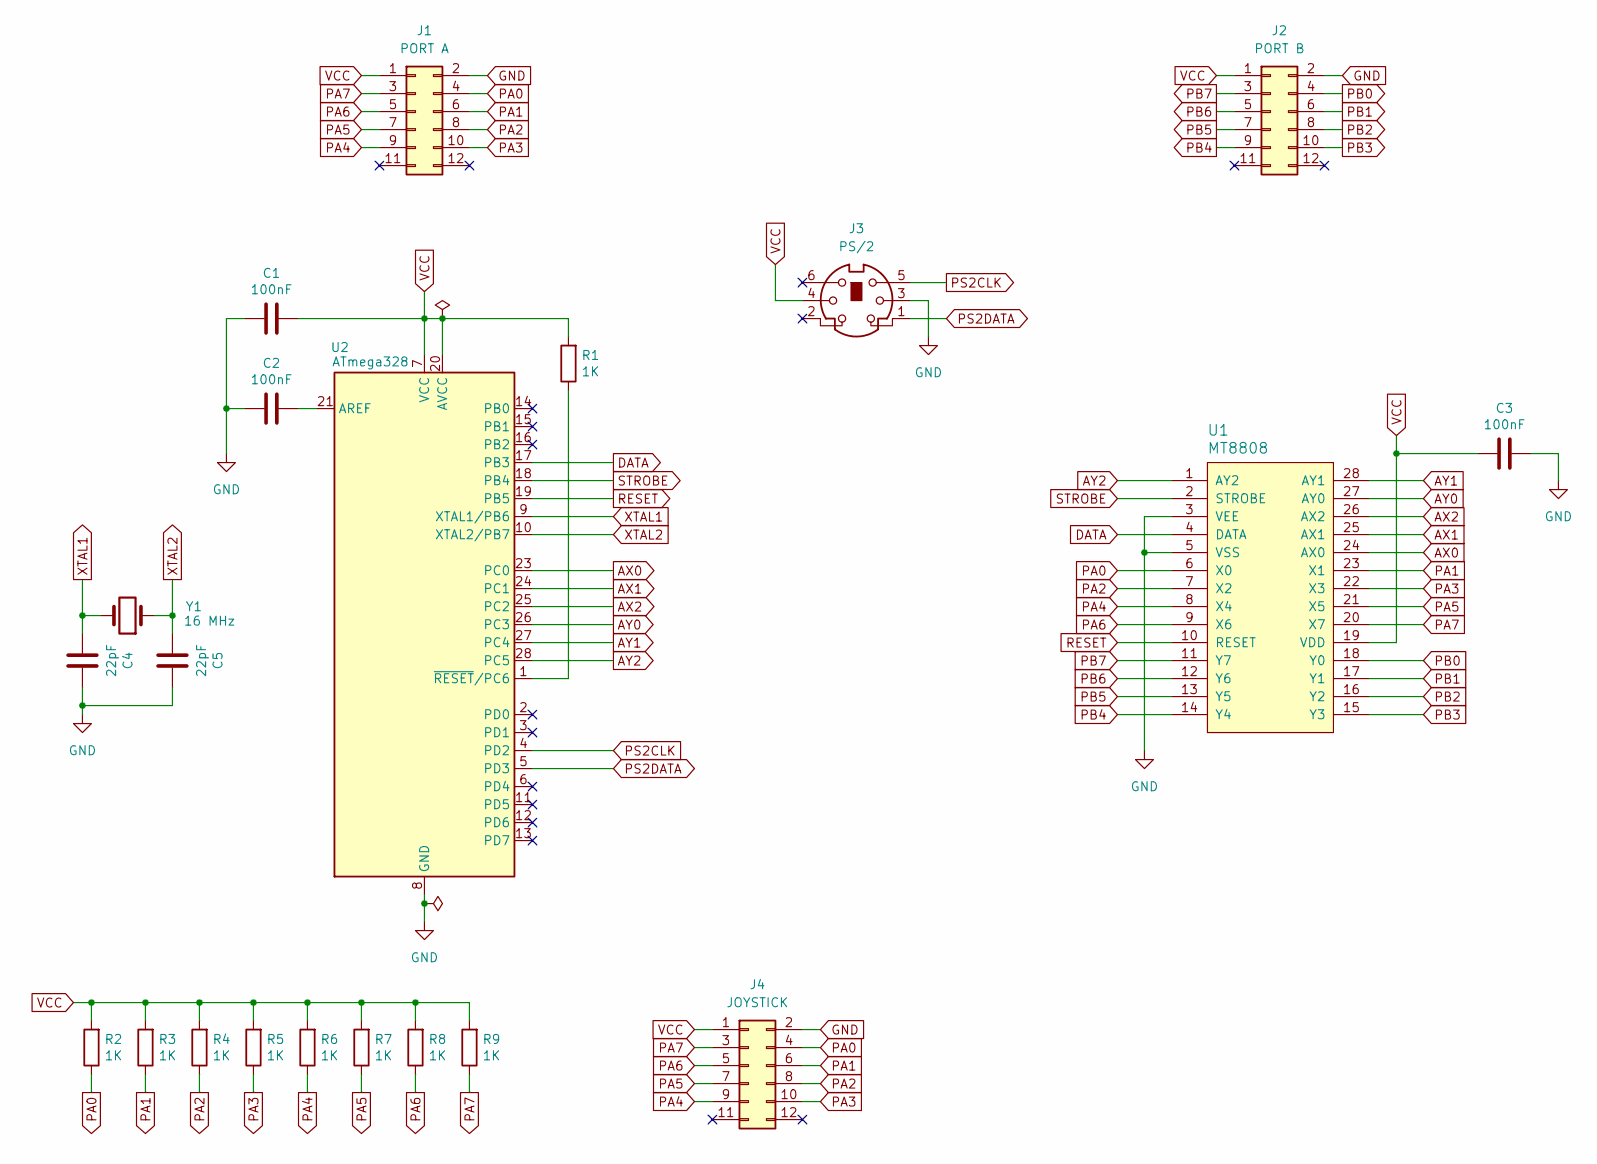
[picture p188: schematic PS2 Helper.kicad_sch, 6502 PS2 Helper]

Parts:
C1, C2, C3: 100nF; C_Disc_D5.0mm_W2.5mm_P2.50mm; LCSC C107114
C4, C5: 22pF; C_Disc_D5.0mm_W2.5mm_P2.50mm; LCSC C107114
J1: PORT A; 6502 GPIO Connector
J2: PORT B; 6502 GPIO Connector
J3: PS/2; KMDGX-6S-BS
J4: JOYSTICK; 6502 GPIO Connector
R1, R2, R3, R4, R5, R6, R7, R8, R9: 1K; R_Axial_DIN0204_L3.6mm_D1.6mm_P5.08mm_Horizontal
U1: MT8808; DIP-28_W15.24mm_Socket_LongPads
U2: ATmega328; DIP-28_W7.62mm_Socket_LongPads
Y1: 16 MHz; Crystal_HC49-U_Vertical; Digikey 3155-16M20P2/49US-ND

Connections:
AX0: U1.24 (AX0), U2.23 (PC0)
AX1: U1.25 (AX1), U2.24 (PC1)
AX2: U1.26 (AX2), U2.25 (PC2)
AY0: U1.27 (AY0), U2.26 (PC3)
AY1: U1.28 (AY1), U2.27 (PC4)
AY2: U1.1 (AY2), U2.28 (PC5)
DATA: U1.4 (DATA), U2.17 (PB3)
GND: C1.1, C2.1, C3.2, C4.2, C5.2, J1.2, J2.2, J3.3, J4.2, U1.3 (VEE), U1.5 (VSS), U2.8 (GND), U2.22 (GND)
unnamed: C2.2, U2.21 (AREF)
unnamed: R1.1, U2.1 (~RESET/PC6)
PA0: J1.4, J4.4, R2.1, U1.6 (X0)
PA1: J1.6, J4.6, R3.1, U1.23 (X1)
PA2: J1.8, J4.8, R4.1, U1.7 (X2)
PA3: J1.10, J4.10, R5.1, U1.22 (X3)
PA4: J1.9, J4.9, R6.1, U1.8 (X4)
PA5: J1.7, J4.7, R7.1, U1.21 (X5)
PA6: J1.5, J4.5, R8.1, U1.9 (X6)
PA7: J1.3, J4.3, R9.1, U1.20 (X7)
PB0: J2.4, U1.18 (Y0)
PB1: J2.6, U1.17 (Y1)
PB2: J2.8, U1.16 (Y2)
PB3: J2.10, U1.15 (Y3)
PB4: J2.9, U1.14 (Y4)
PB5: J2.7, U1.13 (Y5)
PB6: J2.5, U1.12 (Y6)
PB7: J2.3, U1.11 (Y7)
PS2CLK: J3.5, U2.4 (PD2)
PS2DATA: J3.1, U2.5 (PD3)
RESET: U1.10 (RESET), U2.19 (PB5)
STROBE: U1.2 (STROBE), U2.18 (PB4)
VCC: C1.2, C3.1, J1.1, J2.1, J3.4, J4.1, R1.2, R2.2, R3.2, R4.2, R5.2, R6.2, R7.2, R8.2, R9.2, U1.19 (VDD), U2.7 (VCC), U2.20 (AVCC)
XTAL1: C4.1, U2.9 (XTAL1/PB6), Y1.2
XTAL2: C5.1, U2.10 (XTAL2/PB7), Y1.1

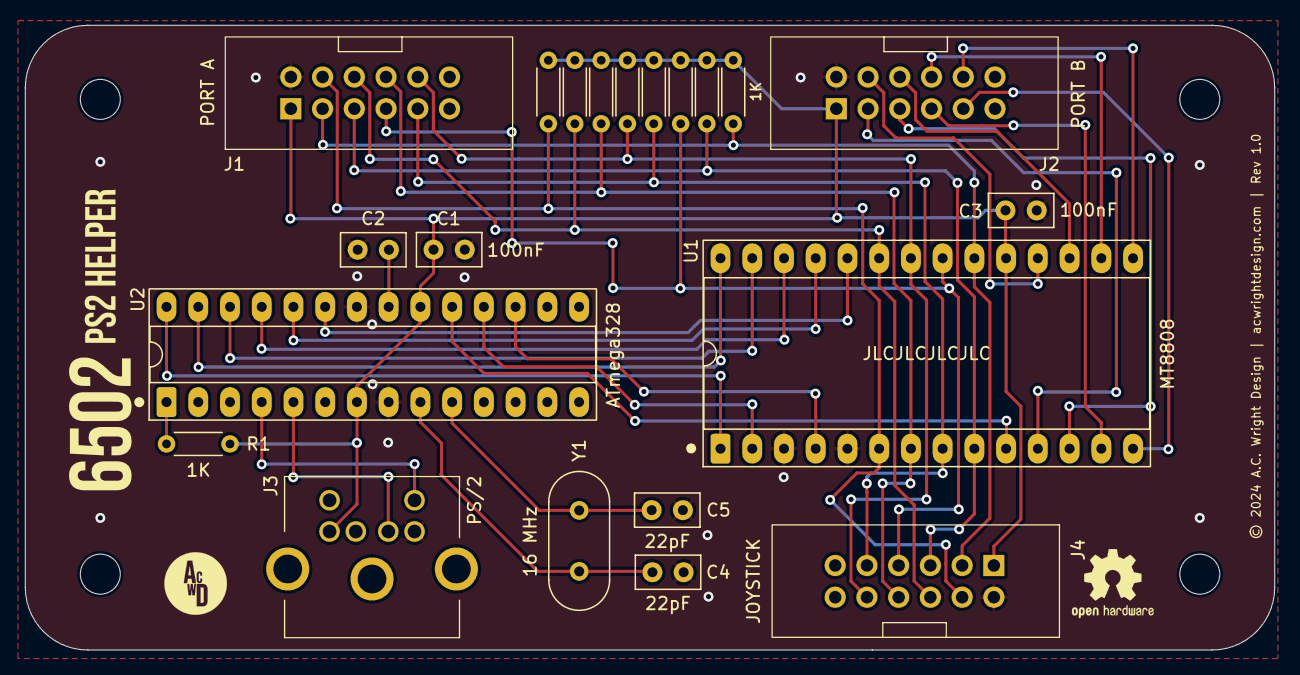
[picture p189: board PS2 Helper.kicad_pcb from above]

Board: 2 copper layers, 100.0 x 50.0 mm, 25 parts (0 on the bottom side), 33 nets.

Other parts of the board:
H1, H2, H3, H4: MountingHole; MountingHole_3.2mm_M3
