acwright/6502/Hardware/Output Board/Rev 1.0/Output Board.kicad_pcb

## KiCad design Hardware/Output Board/Rev 1.0/Output Board.kicad_pcb (2026-01-15)

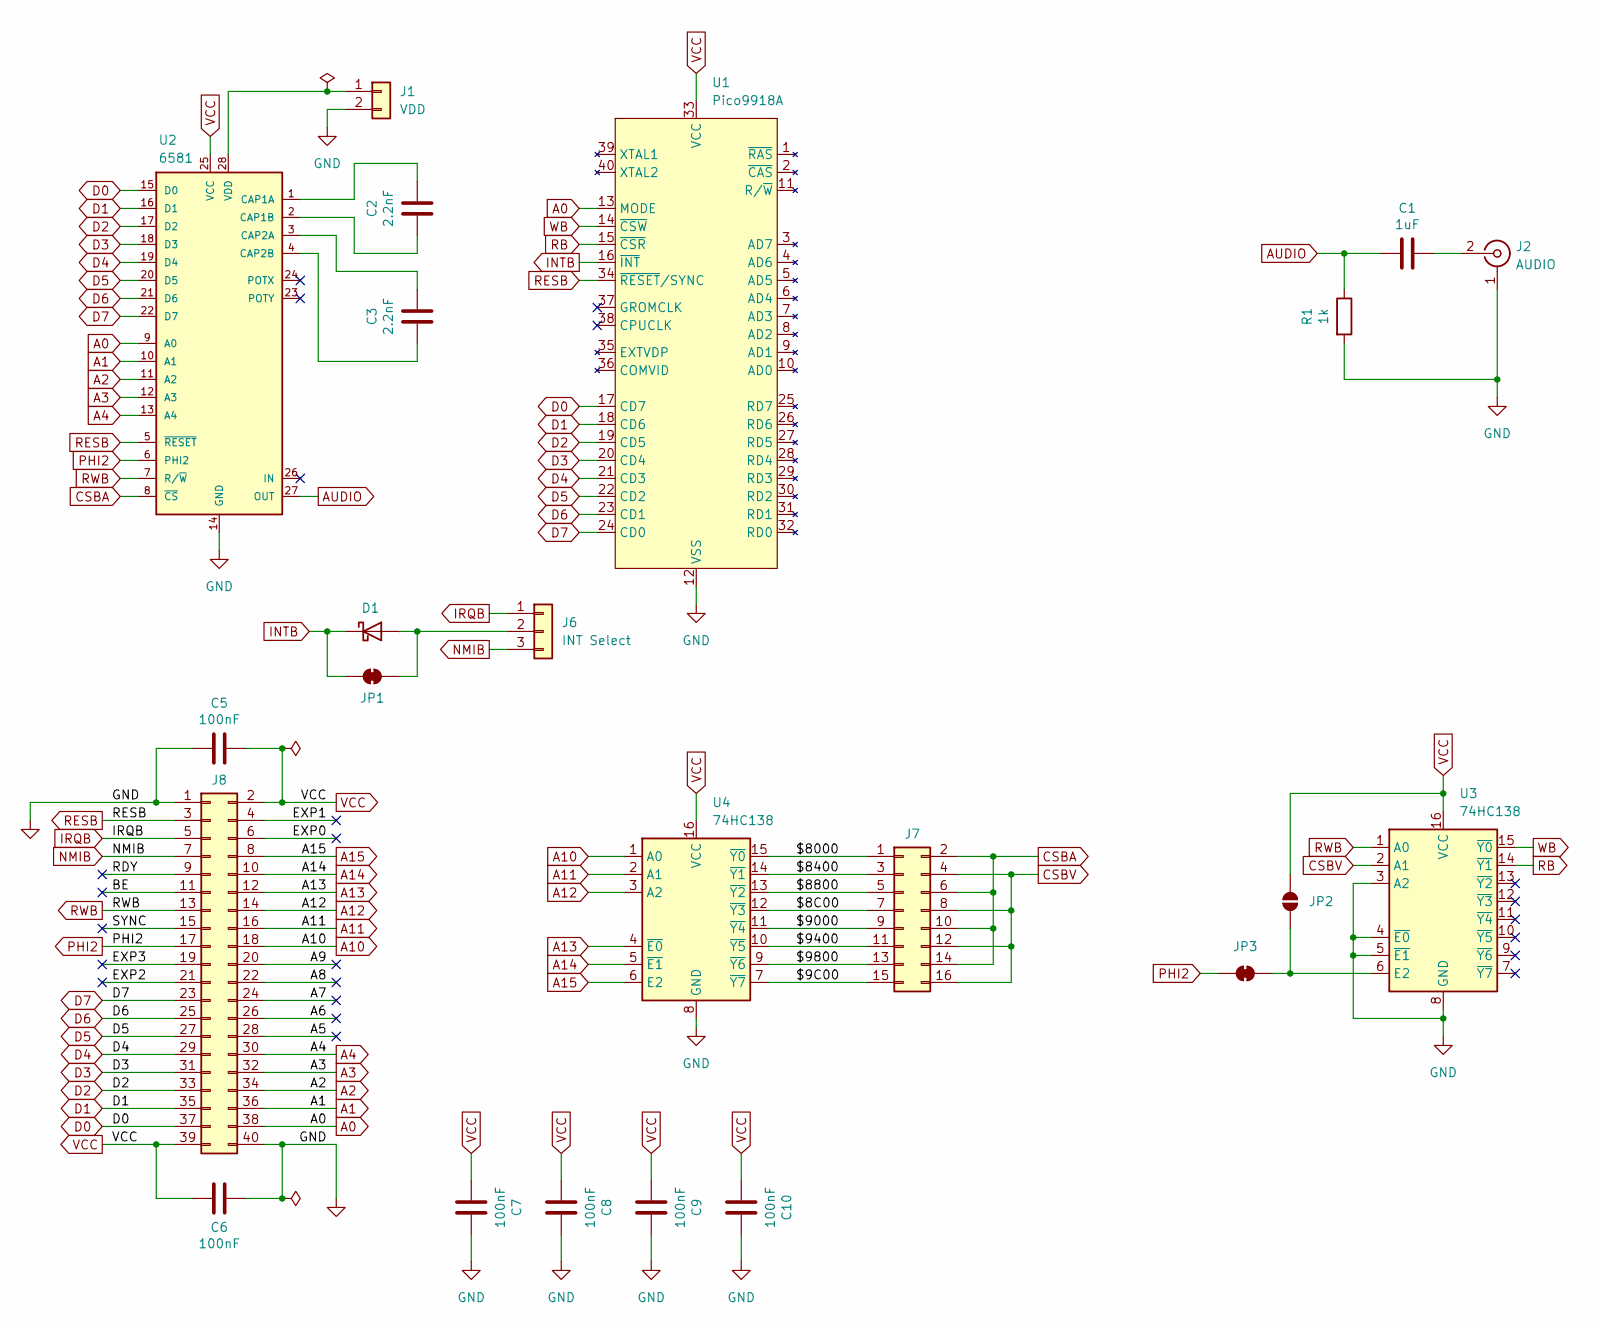
[picture p194: schematic Output Board.kicad_sch, 6502 Output Board]

Parts:
C1: 1uF; C_0805_2012Metric; LCSC C28323
C2, C3: 2.2nF; C_0805_2012Metric; LCSC C28260
C5, C6, C7, C8, C9, C10: 100nF; C_0805_2012Metric; LCSC C49678
D1: D_Schottky; D_DO-35_SOD27_P7.62mm_Horizontal
J1: VDD; JST_XH_B2B-XH-A_1x02_P2.50mm_Vertical
J2: AUDIO; SWITCHCRAFT_PJRAN1X1U02X
J6: INT Select; PinHeader_1x03_P2.54mm_Vertical
J7: Conn_02x08_Odd_Even; PinHeader_2x08_P2.54mm_Vertical
J8: 6502 Bus; 6502 Bus Connector
JP1, JP3: SolderJumper_2_Bridged; SolderJumper-2_P1.3mm_Bridged_RoundedPad1.0x1.5mm
JP2: SolderJumper_2_Open; SolderJumper-2_P1.3mm_Open_RoundedPad1.0x1.5mm
R1: 1k; R_0805_2012Metric; LCSC C17513
U1: Pico9918A; DIP-40_W15.24mm_LongPads
U2: 6581; DIP_Socket-28_W11.9mm_W12.7mm_W15.24mm_W17.78mm_W18.5mm_3M_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
U3, U4: 74HC138; SOIC-16_3.9x9.9mm_P1.27mm; LCSC C5602

Connections:
/$8C00: J7.7, U4.12 (~Y3)
/$9C00: J7.15, U4.7 (~Y7)
/$8000: J7.1, U4.15 (~Y0)
/$8400: J7.3, U4.14 (~Y1)
/$8800: J7.5, U4.13 (~Y2)
/$9000: J7.9, U4.11 (~Y4)
/$9400: J7.11, U4.10 (~Y5)
/$9800: J7.13, U4.9 (~Y6)
/A5: J8.28
/A6: J8.26
/A7: J8.24
/A8: J8.22
/A9: J8.20
/BE: J8.11
/EXP0: J8.6
/EXP1: J8.4
/EXP2: J8.21
/EXP3: J8.19
/RDY: J8.9
/SYNC: J8.15
A0: J8.38, U1.13 (MODE), U2.9 (A0)
A1: J8.36, U2.10 (A1)
A2: J8.34, U2.11 (A2)
A3: J8.32, U2.12 (A3)
A4: J8.30, U2.13 (A4)
A10: J8.18, U4.1 (A0)
A11: J8.16, U4.2 (A1)
A12: J8.14, U4.3 (A2)
A13: J8.12, U4.4 (~E0)
A14: J8.10, U4.5 (~E1)
A15: J8.8, U4.6 (E2)
AUDIO: C1.1, R1.1, U2.27 (OUT)
CSBA: J7.2, J7.6, J7.10, J7.14, U2.8 (~CS)
CSBV: J7.4, J7.8, J7.12, J7.16, U3.2 (A1)
D0: J8.37, U1.17 (CD7), U2.15 (D0)
D1: J8.35, U1.18 (CD6), U2.16 (D1)
D2: J8.33, U1.19 (CD5), U2.17 (D2)
D3: J8.31, U1.20 (CD4), U2.18 (D3)
D4: J8.29, U1.21 (CD3), U2.19 (D4)
D5: J8.27, U1.22 (CD2), U2.20 (D5)
D6: J8.25, U1.23 (CD1), U2.21 (D6)
D7: J8.23, U1.24 (CD0), U2.22 (D7)
GND: C5.2, C6.1, C7.2, C8.2, C9.2, C10.2, J1.2, J2.1 (Ext), J8.1, J8.40, R1.2, U1.12 (VSS), U2.14 (GND), U3.3 (A2), U3.4 (~E0), U3.5 (~E1), U3.8 (GND), U4.8 (GND)
INTB: D1.1 (K), JP1.1 (A), U1.16 (~INT)
IRQB: J6.1, J8.5
NMIB: J6.3, J8.7
unnamed: D1.2 (A), J6.2, JP1.2 (B)
unnamed: J1.1, U2.28 (VDD)
unnamed: C1.2, J2.2 (In)
unnamed: JP2.2 (B), JP3.1 (A), U3.6 (E2)
unnamed: C2.2, U2.1 (CAP1A)
unnamed: C2.1, U2.2 (CAP1B)
unnamed: C3.2, U2.3 (CAP2A)
unnamed: C3.1, U2.4 (CAP2B)
PHI2: J8.17, JP3.2 (B), U2.6 (PHI2)
RB: U1.15 (~CSR), U3.14 (~Y1)
RESB: J8.3, U1.34 (~RESET/SYNC), U2.5 (~RESET)
RWB: J8.13, U2.7 (R/~W), U3.1 (A0)
VCC: C5.1, C6.2, C7.1, C8.1, C9.1, C10.1, J8.2, J8.39, JP2.1 (A), U1.33 (VCC), U2.25 (VCC), U3.16 (VCC), U4.16 (VCC)
WB: U1.14 (~CSW), U3.15 (~Y0)

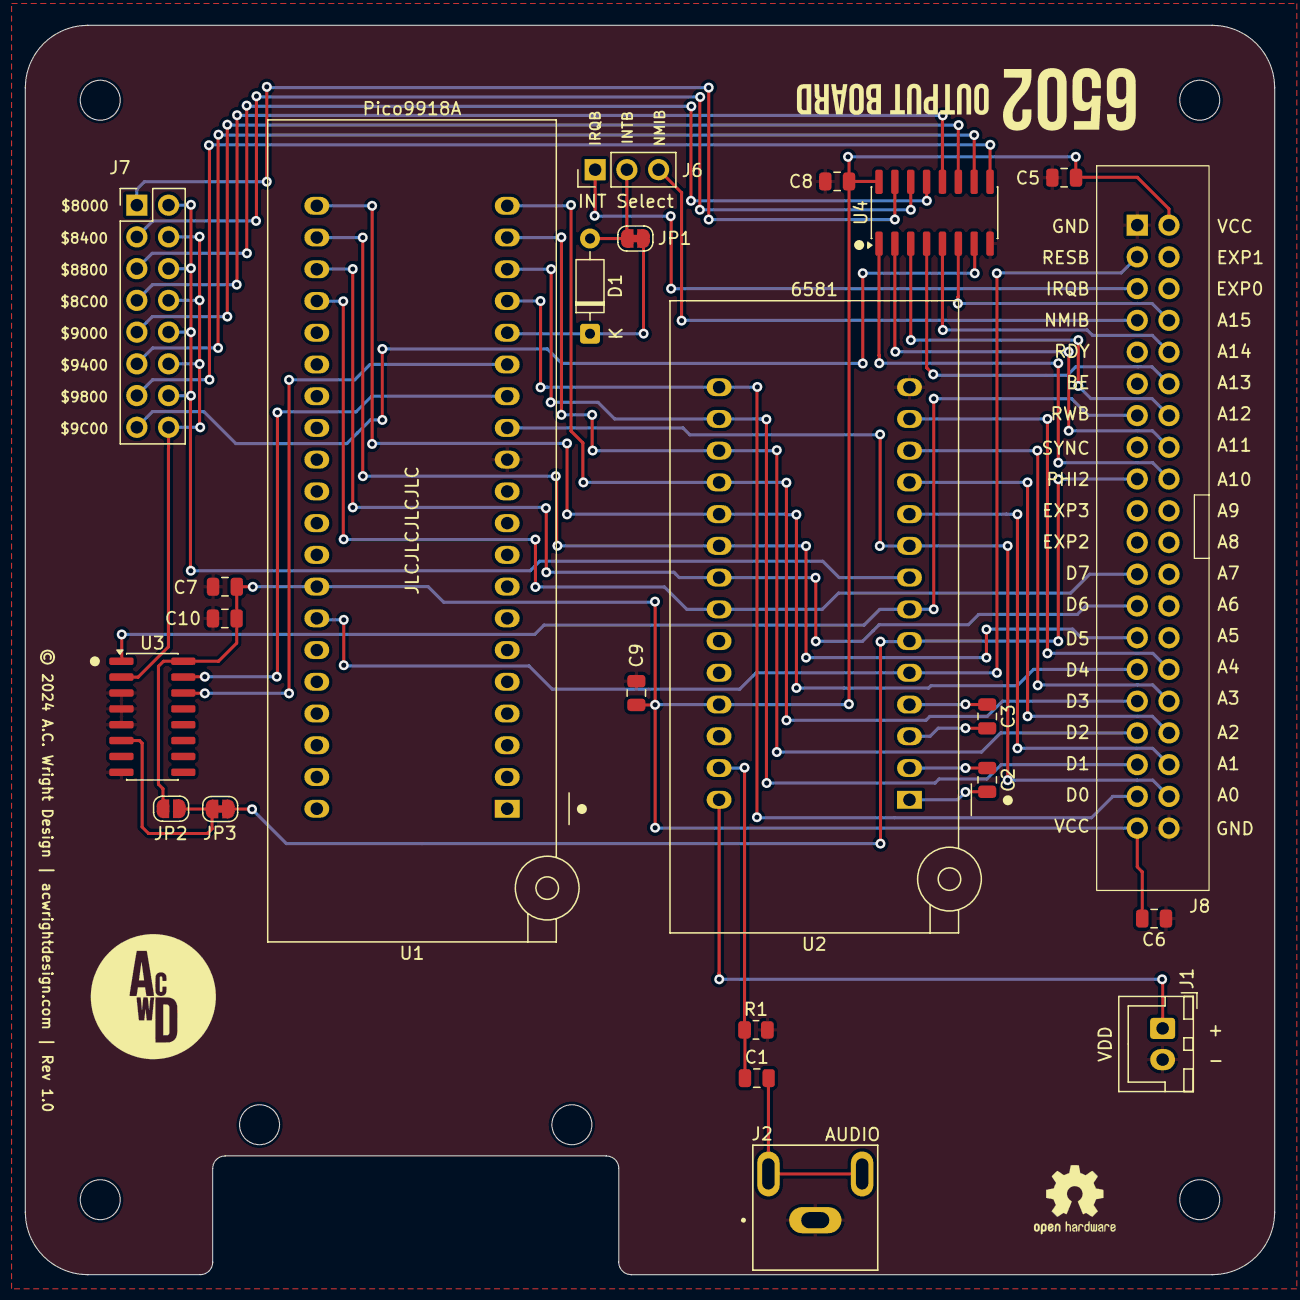
[picture p195: board Output Board.kicad_pcb from above]

Board: 2 copper layers, 100.0 x 100.0 mm, 27 parts (0 on the bottom side), 48 nets.

Other parts of the board:
H1, H2, H3, H4: MountingHole; MountingHole_3.2mm_M3
