acwright/6502/Hardware/CPU Card/Rev 1.0/CPU Card.kicad_pcb

## KiCad design Hardware/CPU Card/Rev 1.0/CPU Card.kicad_pcb (2026-01-14)

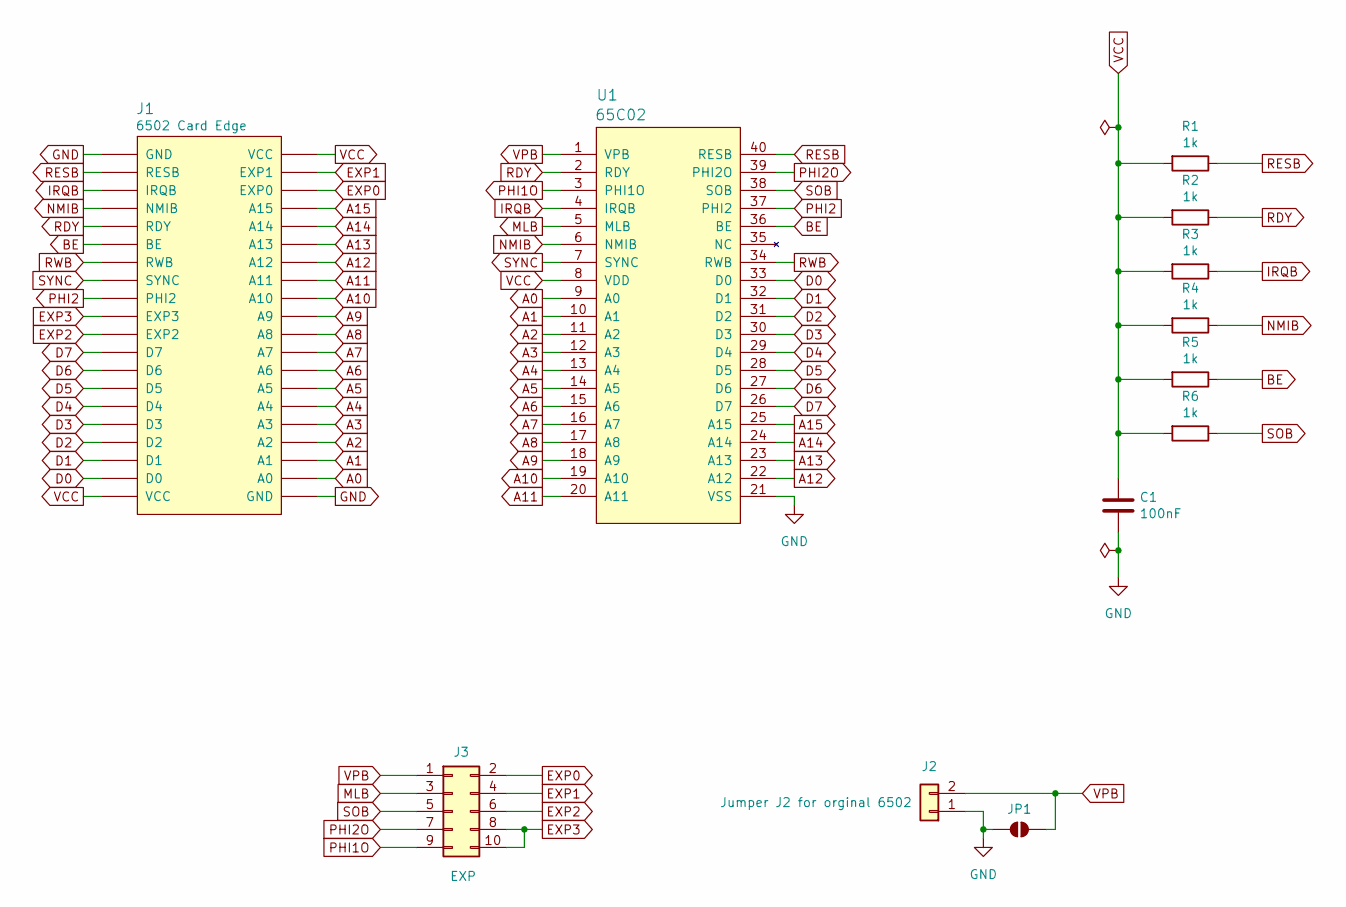
[picture p196: schematic CPU Card.kicad_sch, 6502 CPU Card]

Parts:
C1: 100nF; C_0805_2012Metric; LCSC C49678
J1: 6502 Card Edge
J2: Conn_01x02; PinHeader_1x02_P2.54mm_Vertical
J3: EXP; PinHeader_2x05_P2.54mm_Vertical
JP1: SolderJumper_2_Open; SolderJumper-2_P1.3mm_Open_RoundedPad1.0x1.5mm
R1, R2, R3, R4, R5, R6: 1k; R_0805_2012Metric; LCSC C17513
U1: 65C02; DIP-40_W15.24mm_Socket_LongPads

Connections:
A0: J1.A0, U1.9 (A0)
A1: J1.A1, U1.10 (A1)
A2: J1.A2, U1.11 (A2)
A3: J1.A3, U1.12 (A3)
A4: J1.A4, U1.13 (A4)
A5: J1.A5, U1.14 (A5)
A6: J1.A6, U1.15 (A6)
A7: J1.A7, U1.16 (A7)
A8: J1.A8, U1.17 (A8)
A9: J1.A9, U1.18 (A9)
A10: J1.A10, U1.19 (A10)
A11: J1.A11, U1.20 (A11)
A12: J1.A12, U1.22 (A12)
A13: J1.A13, U1.23 (A13)
A14: J1.A14, U1.24 (A14)
A15: J1.A15, U1.25 (A15)
BE: J1.BE, R5.1, U1.36 (BE)
D0: J1.D0, U1.33 (D0)
D1: J1.D1, U1.32 (D1)
D2: J1.D2, U1.31 (D2)
D3: J1.D3, U1.30 (D3)
D4: J1.D4, U1.29 (D4)
D5: J1.D5, U1.28 (D5)
D6: J1.D6, U1.27 (D6)
D7: J1.D7, U1.26 (D7)
EXP0: J1.EXP0, J3.2
EXP1: J1.EXP1, J3.4
EXP2: J1.EXP2, J3.6
EXP3: J1.EXP3, J3.8, J3.10
GND: C1.2, J1.GND, J2.1, JP1.1 (A), U1.21 (VSS)
IRQB: J1.IRQB, R3.1, U1.4 (IRQB)
MLB: J3.3, U1.5 (MLB)
NMIB: J1.NMIB, R4.1, U1.6 (NMIB)
PHI1O: J3.9, U1.3 (PHI1O)
PHI2: J1.PHI2, U1.37 (PHI2)
PHI2O: J3.7, U1.39 (PHI2O)
RDY: J1.RDY, R2.1, U1.2 (RDY)
RESB: J1.RESB, R1.1, U1.40 (RESB)
RWB: J1.RWB, U1.34 (RWB)
SOB: J3.5, R6.1, U1.38 (SOB)
SYNC: J1.SYNC, U1.7 (SYNC)
VCC: C1.1, J1.VCC, R1.2, R2.2, R3.2, R4.2, R5.2, R6.2, U1.8 (VDD)
VPB: J2.2, J3.1, JP1.2 (B), U1.1 (VPB)

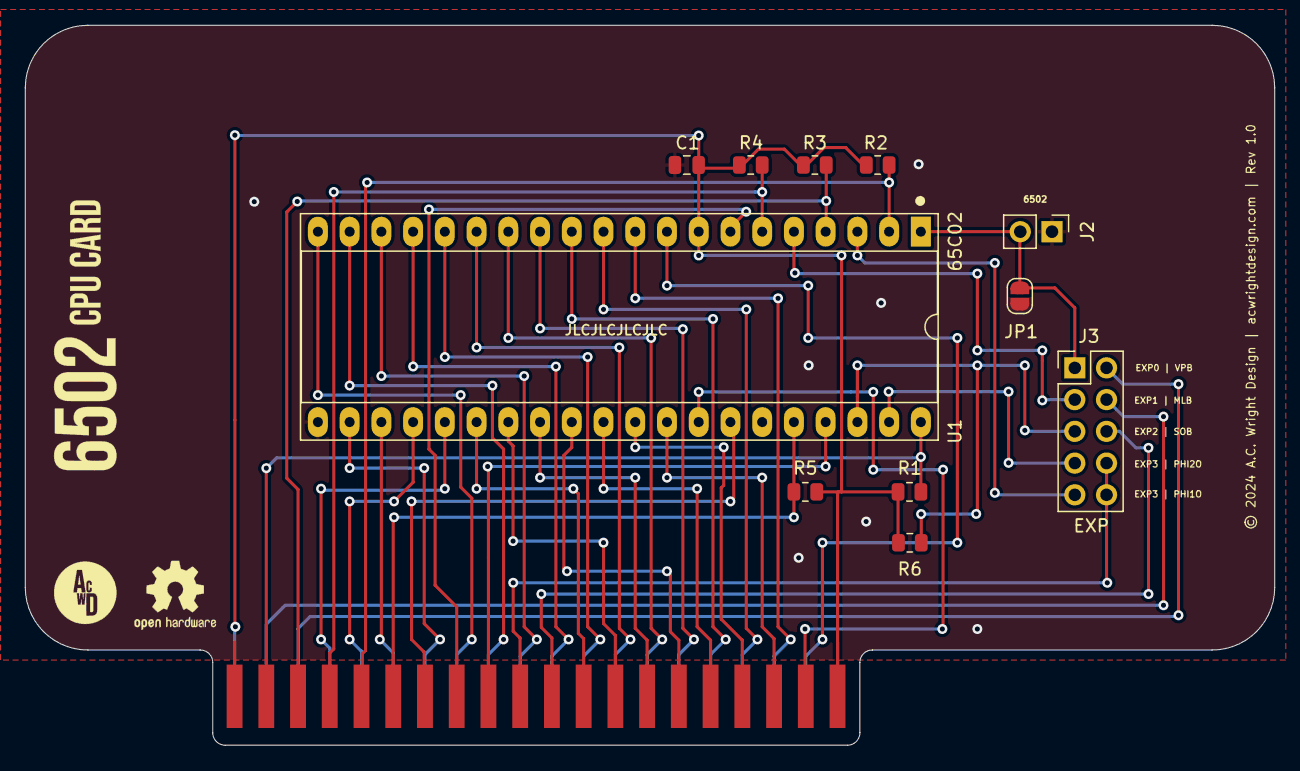
[picture p197: board CPU Card.kicad_pcb from above]

Board: 2 copper layers, 100.0 x 57.6 mm, 12 parts (0 on the bottom side), 43 nets.
