acwright/6502/Hardware/LCD Board/Rev 1.0/LCD Board.kicad_pcb

## KiCad design Hardware/LCD Board/Rev 1.0/LCD Board.kicad_pcb (2026-01-13)

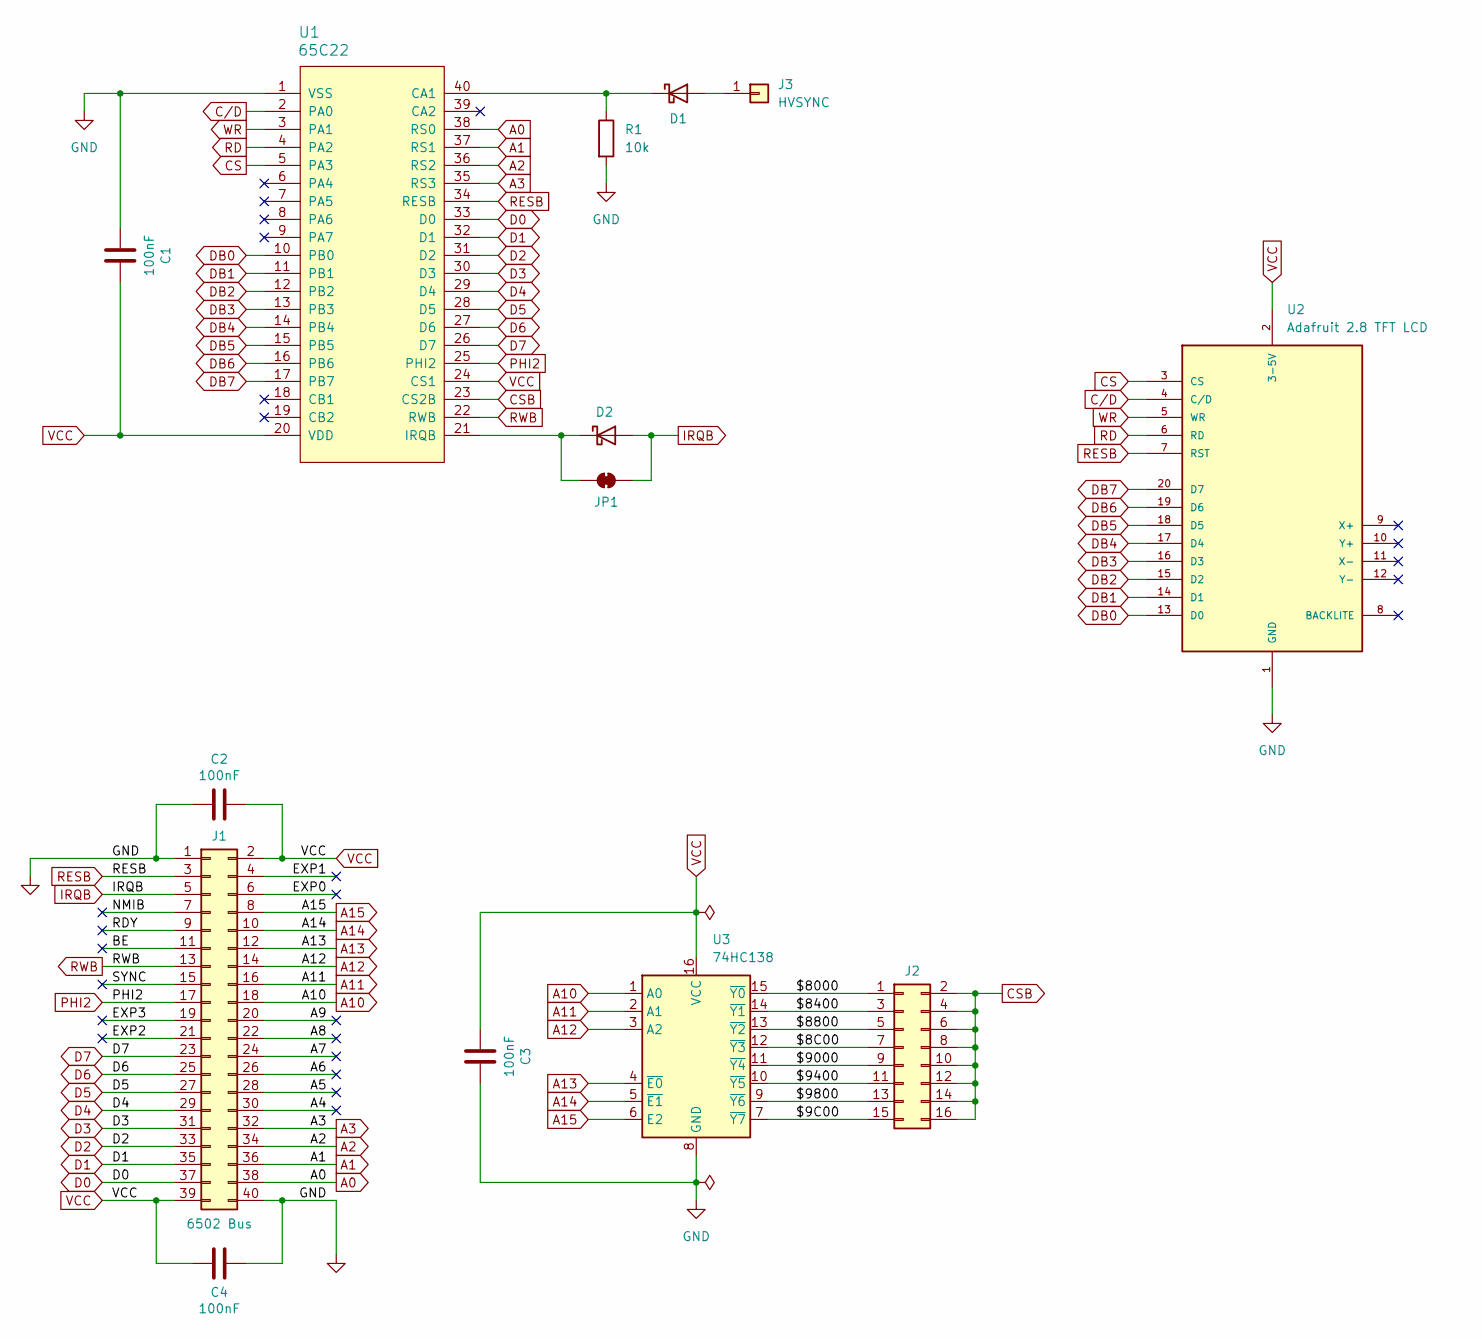
[picture p198: schematic LCD Board.kicad_sch, 6502 LCD Board]

Parts:
C1, C2, C3, C4: 100nF; C_Disc_D5.0mm_W2.5mm_P2.50mm
D1, D2: D_Schottky; D_DO-35_SOD27_P7.62mm_Horizontal
J1: 6502 Bus; 6502 Bus Connector
J2: Conn_02x08_Odd_Even; PinHeader_2x08_P2.54mm_Vertical
J3: HVSYNC; PinHeader_1x01_P2.54mm_Vertical
JP1: SolderJumper_2_Bridged; SolderJumper-2_P1.3mm_Bridged_RoundedPad1.0x1.5mm
R1: 10k; R_Axial_DIN0204_L3.6mm_D1.6mm_P5.08mm_Horizontal
U1: 65C22; DIP-40_W15.24mm_Socket_LongPads
U2: Adafruit 2.8 TFT LCD; PARTREV 2025-02-10
U3: 74HC138; DIP-16_W7.62mm_Socket_LongPads

Connections:
/$8C00: J2.7, U3.12 (~Y3)
/$9C00: J2.15, U3.7 (~Y7)
/$8000: J2.1, U3.15 (~Y0)
/$8400: J2.3, U3.14 (~Y1)
/$8800: J2.5, U3.13 (~Y2)
/$9000: J2.9, U3.11 (~Y4)
/$9400: J2.11, U3.10 (~Y5)
/$9800: J2.13, U3.9 (~Y6)
/A4: J1.30
/A5: J1.28
/A6: J1.26
/A7: J1.24
/A8: J1.22
/A9: J1.20
/BE: J1.11
/EXP0: J1.6
/EXP1: J1.4
/EXP2: J1.21
/EXP3: J1.19
/NMIB: J1.7
/RDY: J1.9
/SYNC: J1.15
A0: J1.38, U1.38 (RS0)
A1: J1.36, U1.37 (RS1)
A2: J1.34, U1.36 (RS2)
A3: J1.32, U1.35 (RS3)
A10: J1.18, U3.1 (A0)
A11: J1.16, U3.2 (A1)
A12: J1.14, U3.3 (A2)
A13: J1.12, U3.4 (~E0)
A14: J1.10, U3.5 (~E1)
A15: J1.8, U3.6 (E2)
CS: U1.5 (PA3), U2.3 (CS)
CSB: J2.2, J2.4, J2.6, J2.8, J2.10, J2.12, J2.14, J2.16, U1.23 (CS2B)
C/D: U1.2 (PA0), U2.4 (C/D)
D0: J1.37, U1.33 (D0)
D1: J1.35, U1.32 (D1)
D2: J1.33, U1.31 (D2)
D3: J1.31, U1.30 (D3)
D4: J1.29, U1.29 (D4)
D5: J1.27, U1.28 (D5)
D6: J1.25, U1.27 (D6)
D7: J1.23, U1.26 (D7)
DB0: U1.10 (PB0), U2.13 (D0)
DB1: U1.11 (PB1), U2.14 (D1)
DB2: U1.12 (PB2), U2.15 (D2)
DB3: U1.13 (PB3), U2.16 (D3)
DB4: U1.14 (PB4), U2.17 (D4)
DB5: U1.15 (PB5), U2.18 (D5)
DB6: U1.16 (PB6), U2.19 (D6)
DB7: U1.17 (PB7), U2.20 (D7)
GND: C1.1, C2.2, C3.2, C4.1, J1.1, J1.40, R1.2, U1.1 (VSS), U2.1 (GND), U3.8 (GND)
IRQB: D2.2 (A), J1.5, JP1.2 (B)
unnamed: D1.2 (A), J3.1
unnamed: D1.1 (K), R1.1, U1.40 (CA1)
unnamed: D2.1 (K), JP1.1 (A), U1.21 (IRQB)
PHI2: J1.17, U1.25 (PHI2)
RD: U1.4 (PA2), U2.6 (RD)
RESB: J1.3, U1.34 (RESB), U2.7 (RST)
RWB: J1.13, U1.22 (RWB)
VCC: C1.2, C2.1, C3.1, C4.2, J1.2, J1.39, U1.20 (VDD), U1.24 (CS1), U2.2 (3-5V), U3.16 (VCC)
WR: U1.3 (PA1), U2.5 (WR)
