acwright/6502/Hardware/LCD Board/Rev 1.0/LCD Board.kicad_pcb

## KiCad design Hardware/LCD Board/Rev 1.0/LCD Board.kicad_pcb (continued)

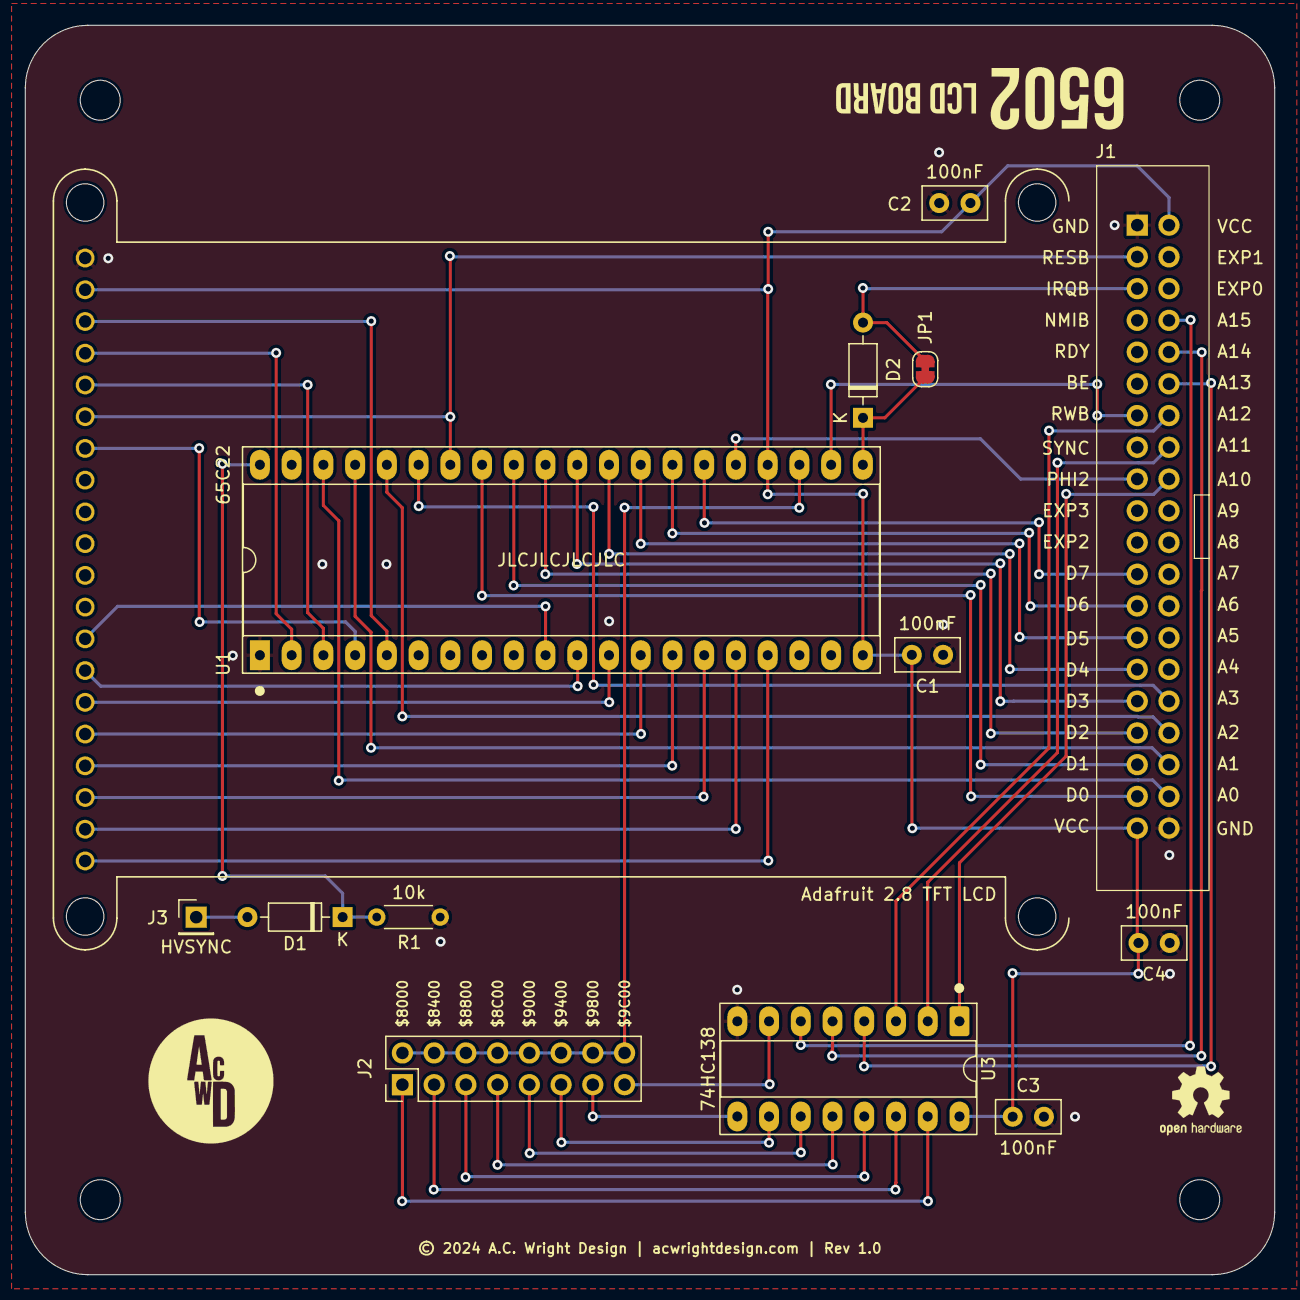
[picture p199: board LCD Board.kicad_pcb from above]

Board: 2 copper layers, 100.0 x 100.0 mm, 18 parts (0 on the bottom side), 48 nets.

Other parts of the board:
H1, H2, H3, H4: MountingHole; MountingHole_3.2mm_M3
