acwright/6502/Hardware/Storage Card Pro/Rev 1.0/Storage Card Pro.kicad_pcb

## KiCad design Hardware/Storage Card Pro/Rev 1.0/Storage Card Pro.kicad_pcb (2025-12-12)

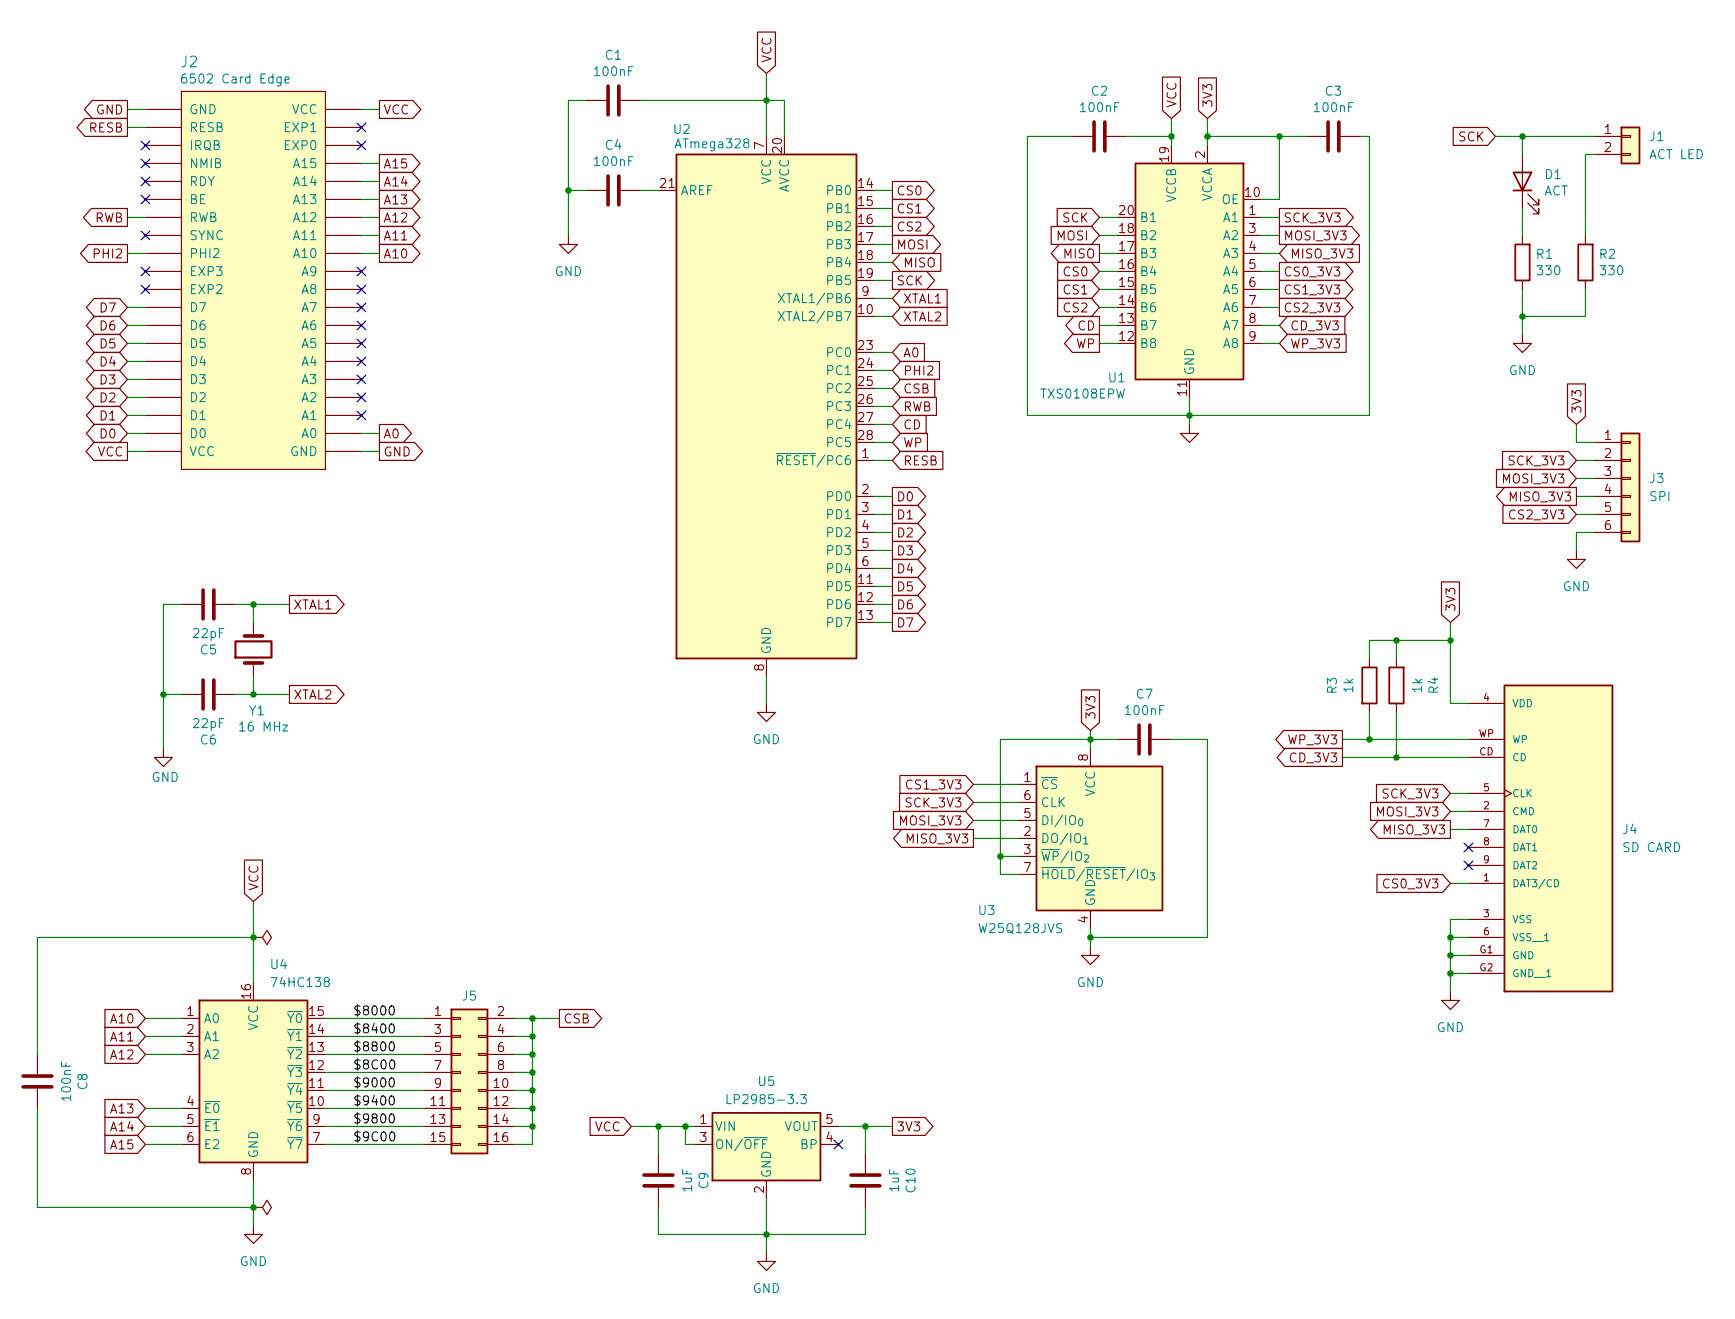
[picture p200: schematic Storage Card Pro.kicad_sch, 6502 Storage Card Pro]

Parts:
C1, C2, C3, C7, C8: 100nF; C_0805_2012Metric; LCSC C49678
C4: 100nF; C_0805_2012Metric
C5, C6: 22pF; C_Disc_D5.0mm_W2.5mm_P2.50mm; LCSC C107114
C9, C10: 1uF; C_0805_2012Metric; LCSC C28323
D1: ACT; LED_0805_2012Metric; LCSC C2297
J1: ACT LED; JST_XH_B2B-XH-A_1x02_P2.50mm_Vertical
J2: 6502 Card Edge
J3: SPI; PinHeader_1x06_P2.54mm_Horizontal
J4: SD CARD; 10067847-001RLF; PARTREV K; LCSC C569097
J5: Conn_02x08_Odd_Even; PinHeader_2x08_P2.54mm_Vertical
R1, R2: 330; R_0805_2012Metric; LCSC C17630
R3, R4: 1k; R_0805_2012Metric; LCSC C17513
U1: TXS0108EPW; TSSOP-20_4.4x6.5mm_P0.65mm; LCSC C17206
U2: ATmega328; DIP-28_W7.62mm_Socket_LongPads
U3: W25Q128JVS; SOIC-8_5.3x5.3mm_P1.27mm; LCSC C97521
U4: 74HC138; SOIC-16_3.9x9.9mm_P1.27mm; LCSC C5602
U5: LP2985-3.3; SOT-23-5; LCSC C95414
Y1: 16 MHz; Crystal_HC49-U_Vertical; Digikey 3155-16M20P2/49US-ND

Connections:
3V3: C3.1, C7.1, C10.1, J3.1, J4.4 (VDD), R3.1, R4.2, U1.2 (VCCA), U1.10 (OE), U3.3 (~WP/IO_{2}), U3.7 (~HOLD/~RESET/IO_{3}), U3.8 (VCC), U5.5 (VOUT)
/$8C00: J5.7, U4.12 (~Y3)
/$9C00: J5.15, U4.7 (~Y7)
/$8000: J5.1, U4.15 (~Y0)
/$8400: J5.3, U4.14 (~Y1)
/$8800: J5.5, U4.13 (~Y2)
/$9000: J5.9, U4.11 (~Y4)
/$9400: J5.11, U4.10 (~Y5)
/$9800: J5.13, U4.9 (~Y6)
A0: J2.A0, U2.23 (PC0)
A10: J2.A10, U4.1 (A0)
A11: J2.A11, U4.2 (A1)
A12: J2.A12, U4.3 (A2)
A13: J2.A13, U4.4 (~E0)
A14: J2.A14, U4.5 (~E1)
A15: J2.A15, U4.6 (E2)
CD: U1.13 (B7), U2.27 (PC4)
CD_3V3: J4.CD, R4.1, U1.8 (A7)
CS0: U1.16 (B4), U2.14 (PB0)
CS0_3V3: J4.1 (DAT3/CD), U1.5 (A4)
CS1: U1.15 (B5), U2.15 (PB1)
CS1_3V3: U1.6 (A5), U3.1 (~CS)
CS2: U1.14 (B6), U2.16 (PB2)
CS2_3V3: J3.5, U1.7 (A6)
CSB: J5.2, J5.4, J5.6, J5.8, J5.10, J5.12, J5.14, J5.16, U2.25 (PC2)
D0: J2.D0, U2.2 (PD0)
D1: J2.D1, U2.3 (PD1)
D2: J2.D2, U2.4 (PD2)
D3: J2.D3, U2.5 (PD3)
D4: J2.D4, U2.6 (PD4)
D5: J2.D5, U2.11 (PD5)
D6: J2.D6, U2.12 (PD6)
D7: J2.D7, U2.13 (PD7)
GND: C1.1, C2.1, C3.2, C4.1, C5.2, C6.2, C7.2, C8.2, C9.2, C10.2, J2.GND, J3.6, J4.3 (VSS), J4.6 (VSS__1), J4.G1 (GND), J4.G2 (GND__1), R1.1, R2.1, U1.11 (GND), U2.8 (GND), U2.22 (GND), U3.4 (GND), U4.8 (GND), U5.2 (GND)
MISO: U1.17 (B3), U2.18 (PB4)
MISO_3V3: J3.4, J4.7 (DAT0), U1.4 (A3), U3.2 (DO/IO_{1})
MOSI: U1.18 (B2), U2.17 (PB3)
MOSI_3V3: J3.3, J4.2 (CMD), U1.3 (A2), U3.5 (DI/IO_{0})
unnamed: D1.1 (K), R1.2
unnamed: J1.2, R2.2
unnamed: C4.2, U2.21 (AREF)
PHI2: J2.PHI2, U2.24 (PC1)
RESB: J2.RESB, U2.1 (~RESET/PC6)
RWB: J2.RWB, U2.26 (PC3)
SCK: D1.2 (A), J1.1, U1.20 (B1), U2.19 (PB5)
SCK_3V3: J3.2, J4.5 (CLK), U1.1 (A1), U3.6 (CLK)
VCC: C1.2, C2.2, C8.1, C9.1, J2.VCC, U1.19 (VCCB), U2.7 (VCC), U2.20 (AVCC), U4.16 (VCC), U5.1 (VIN), U5.3 (ON/~OFF)
WP: U1.12 (B8), U2.28 (PC5)
WP_3V3: J4.WP, R3.2, U1.9 (A8)
XTAL1: C5.1, U2.9 (XTAL1/PB6), Y1.2
XTAL2: C6.1, U2.10 (XTAL2/PB7), Y1.1

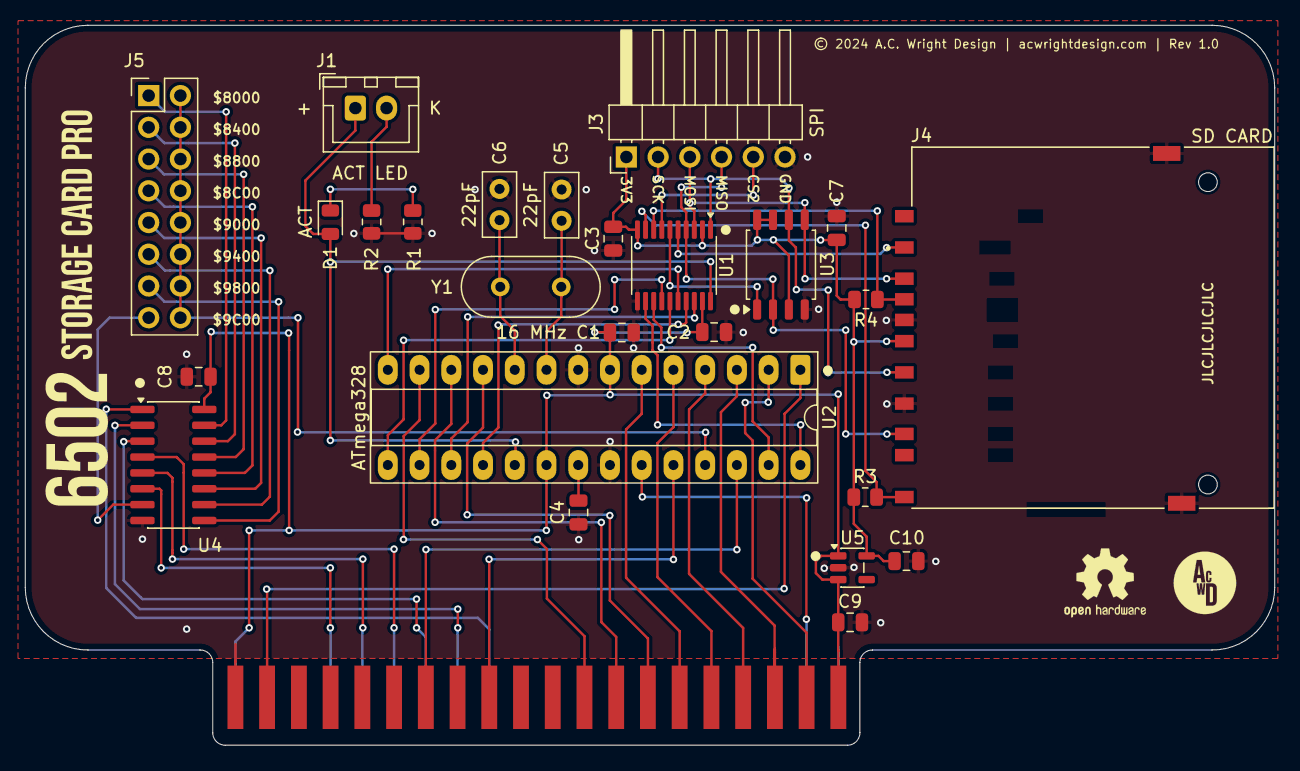
[picture p201: board Storage Card Pro.kicad_pcb from above]

Board: 2 copper layers, 100.0 x 57.6 mm, 26 parts (0 on the bottom side), 51 nets.
