acwright/6502/Hardware/Video Card Pro/Rev 1.0/Video Card Pro.kicad_pcb

## KiCad design Hardware/Video Card Pro/Rev 1.0/Video Card Pro.kicad_pcb (2025-12-09)

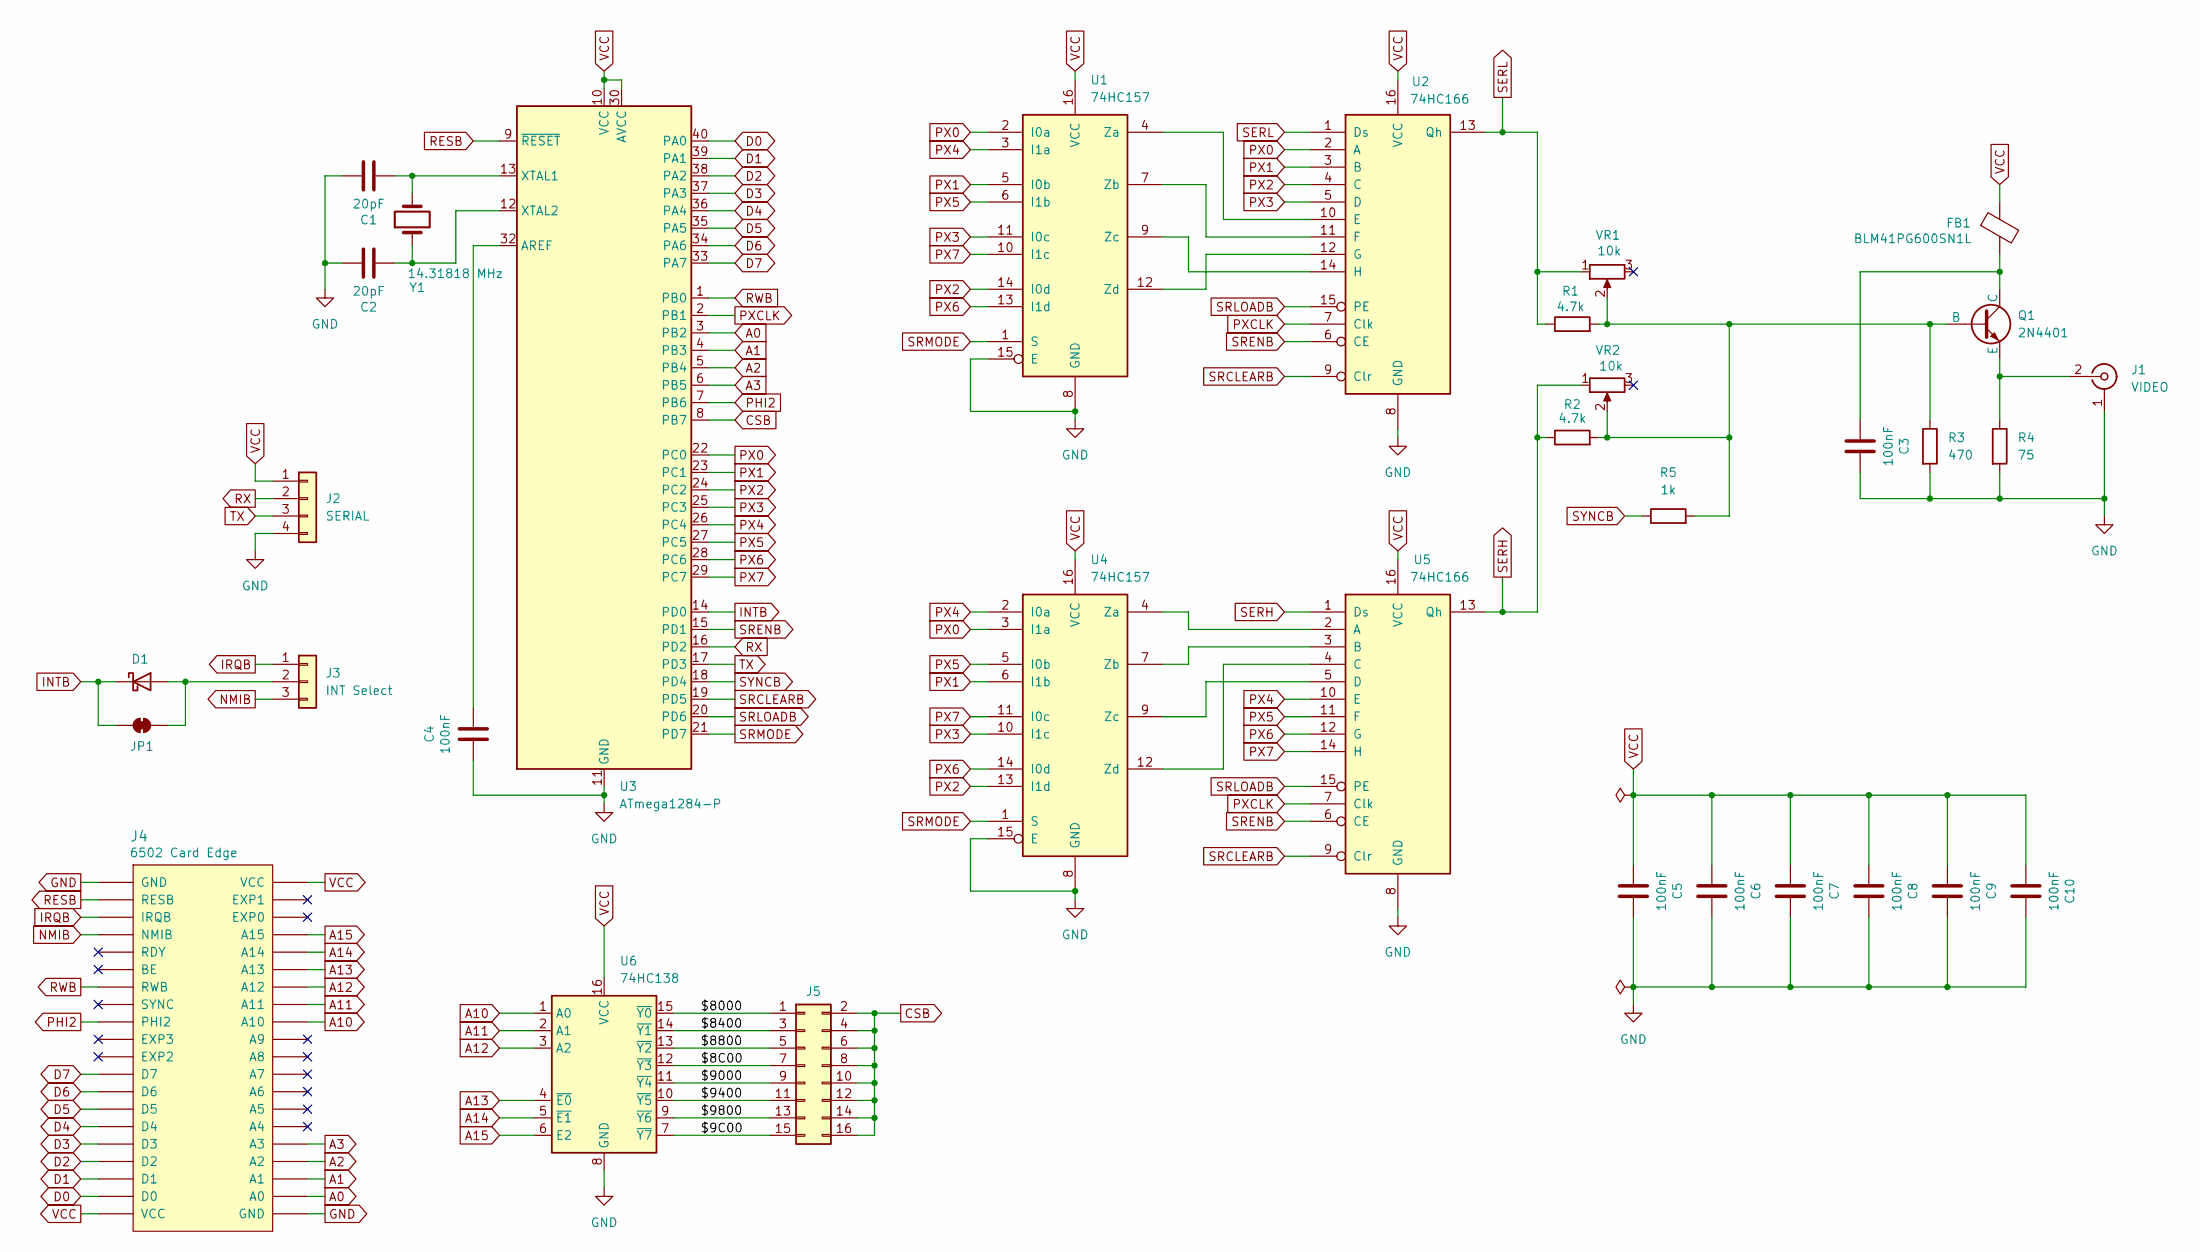
[picture p202: schematic Video Card Pro.kicad_sch, 6502 Video Card Pro]

Parts:
C1, C2: 20pF; C_Disc_D5.0mm_W2.5mm_P2.50mm; LCSC C105173
C3, C4, C5, C6, C7, C8, C9, C10: 100nF; C_0805_2012Metric; LCSC C49678
D1: D_Schottky; D_DO-35_SOD27_P7.62mm_Horizontal
FB1: BLM41PG600SN1L; L_1806_4516Metric; LCSC C85844
J1: VIDEO; SWITCHCRAFT_PJRAN1X1U04X
J2: SERIAL; PinHeader_1x04_P2.54mm_Vertical
J3: INT Select; PinHeader_1x03_P2.54mm_Vertical
J4: 6502 Card Edge
J5: Conn_02x08_Odd_Even; PinHeader_2x08_P2.54mm_Vertical
JP1: SolderJumper_2_Bridged; SolderJumper-2_P1.3mm_Bridged_RoundedPad1.0x1.5mm
Q1: 2N4401; TO-92_HandSolder
R1, R2: 4.7k; R_Axial_DIN0204_L3.6mm_D1.6mm_P5.08mm_Horizontal
R3: 470; R_0805_2012Metric; LCSC C17710
R4: 75; R_0805_2012Metric; LCSC C17820
R5: 1k; R_Axial_DIN0204_L3.6mm_D1.6mm_P5.08mm_Horizontal
U1, U4: 74HC157; SOIC-16_3.9x9.9mm_P1.27mm; LCSC C6823
U2, U5: 74HC166; SOIC-16_3.9x9.9mm_P1.27mm; LCSC C473363
U3: ATmega1284-P; DIP-40_W15.24mm_Socket_LongPads
U6: 74HC138; SOIC-16_3.9x9.9mm_P1.27mm; LCSC C5602
VR1, VR2: 10k; 3386F-1-103LF
Y1: 14.31818 MHz; Crystal_HC49-U_Vertical; Mouser 774-MP107-E

Connections:
/$8C00: J5.7, U6.12 (~Y3)
/$9C00: J5.15, U6.7 (~Y7)
/$8000: J5.1, U6.15 (~Y0)
/$8400: J5.3, U6.14 (~Y1)
/$8800: J5.5, U6.13 (~Y2)
/$9000: J5.9, U6.11 (~Y4)
/$9400: J5.11, U6.10 (~Y5)
/$9800: J5.13, U6.9 (~Y6)
A0: J4.A0, U3.3 (PB2)
A1: J4.A1, U3.4 (PB3)
A2: J4.A2, U3.5 (PB4)
A3: J4.A3, U3.6 (PB5)
A10: J4.A10, U6.1 (A0)
A11: J4.A11, U6.2 (A1)
A12: J4.A12, U6.3 (A2)
A13: J4.A13, U6.4 (~E0)
A14: J4.A14, U6.5 (~E1)
A15: J4.A15, U6.6 (E2)
CSB: J5.2, J5.4, J5.6, J5.8, J5.10, J5.12, J5.14, J5.16, U3.8 (PB7)
D0: J4.D0, U3.40 (PA0)
D1: J4.D1, U3.39 (PA1)
D2: J4.D2, U3.38 (PA2)
D3: J4.D3, U3.37 (PA3)
D4: J4.D4, U3.36 (PA4)
D5: J4.D5, U3.35 (PA5)
D6: J4.D6, U3.34 (PA6)
D7: J4.D7, U3.33 (PA7)
GND: C1.2, C2.2, C3.2, C4.1, C5.2, C6.2, C7.2, C8.2, C9.2, C10.2, J1.1 (Ext), J2.4, J4.GND, R3.2, R4.2, U1.8 (GND), U1.15 (E), U2.8 (GND), U3.11 (GND), U3.31 (GND), U4.8 (GND), U4.15 (E), U5.8 (GND), U6.8 (GND)
INTB: D1.1 (K), JP1.1 (A), U3.14 (PD0)
IRQB: J3.1, J4.IRQB
NMIB: J3.3, J4.NMIB
unnamed: D1.2 (A), J3.2, JP1.2 (B)
unnamed: J1.2 (In), Q1.3 (E), R4.1
unnamed: Q1.2 (B), R1.2, R2.2, R3.1, R5.2, VR1.2, VR2.2
unnamed: C3.1, FB1.2, Q1.1 (C)
unnamed: U1.4 (Za), U2.10 (E)
unnamed: U1.7 (Zb), U2.11 (F)
unnamed: U1.9 (Zc), U2.14 (H)
unnamed: U1.12 (Zd), U2.12 (G)
unnamed: C4.2, U3.32 (AREF)
unnamed: C1.1, U3.13 (XTAL1), Y1.2
unnamed: C2.1, U3.12 (XTAL2), Y1.1
unnamed: U4.4 (Za), U5.2 (A)
unnamed: U4.7 (Zb), U5.3 (B)
unnamed: U4.9 (Zc), U5.5 (D)
unnamed: U4.12 (Zd), U5.4 (C)
PHI2: J4.PHI2, U3.7 (PB6)
PX0: U1.2 (I0a), U2.2 (A), U3.22 (PC0), U4.3 (I1a)
PX1: U1.5 (I0b), U2.3 (B), U3.23 (PC1), U4.6 (I1b)
PX2: U1.14 (I0d), U2.4 (C), U3.24 (PC2), U4.13 (I1d)
PX3: U1.11 (I0c), U2.5 (D), U3.25 (PC3), U4.10 (I1c)
PX4: U1.3 (I1a), U3.26 (PC4), U4.2 (I0a), U5.10 (E)
PX5: U1.6 (I1b), U3.27 (PC5), U4.5 (I0b), U5.11 (F)
PX6: U1.13 (I1d), U3.28 (PC6), U4.14 (I0d), U5.12 (G)
PX7: U1.10 (I1c), U3.29 (PC7), U4.11 (I0c), U5.14 (H)
PXCLK: U2.7 (Clk), U3.2 (PB1), U5.7 (Clk)
RESB: J4.RESB, U3.9 (~RESET)
RWB: J4.RWB, U3.1 (PB0)
RX: J2.2, U3.16 (PD2)
SERH: R2.1, U5.1 (Ds), U5.13 (Qh), VR2.1
SERL: R1.1, U2.1 (Ds), U2.13 (Qh), VR1.1
SRCLEARB: U2.9 (Clr), U3.19 (PD5), U5.9 (Clr)
SRENB: U2.6 (CE), U3.15 (PD1), U5.6 (CE)
SRLOADB: U2.15 (PE), U3.20 (PD6), U5.15 (PE)
SRMODE: U1.1 (S), U3.21 (PD7), U4.1 (S)
SYNCB: R5.1, U3.18 (PD4)
TX: J2.3, U3.17 (PD3)
VCC: C5.1, C6.1, C7.1, C8.1, C9.1, C10.1, FB1.1, J2.1, J4.VCC, U1.16 (VCC), U2.16 (VCC), U3.10 (VCC), U3.30 (AVCC), U4.16 (VCC), U5.16 (VCC), U6.16 (VCC)

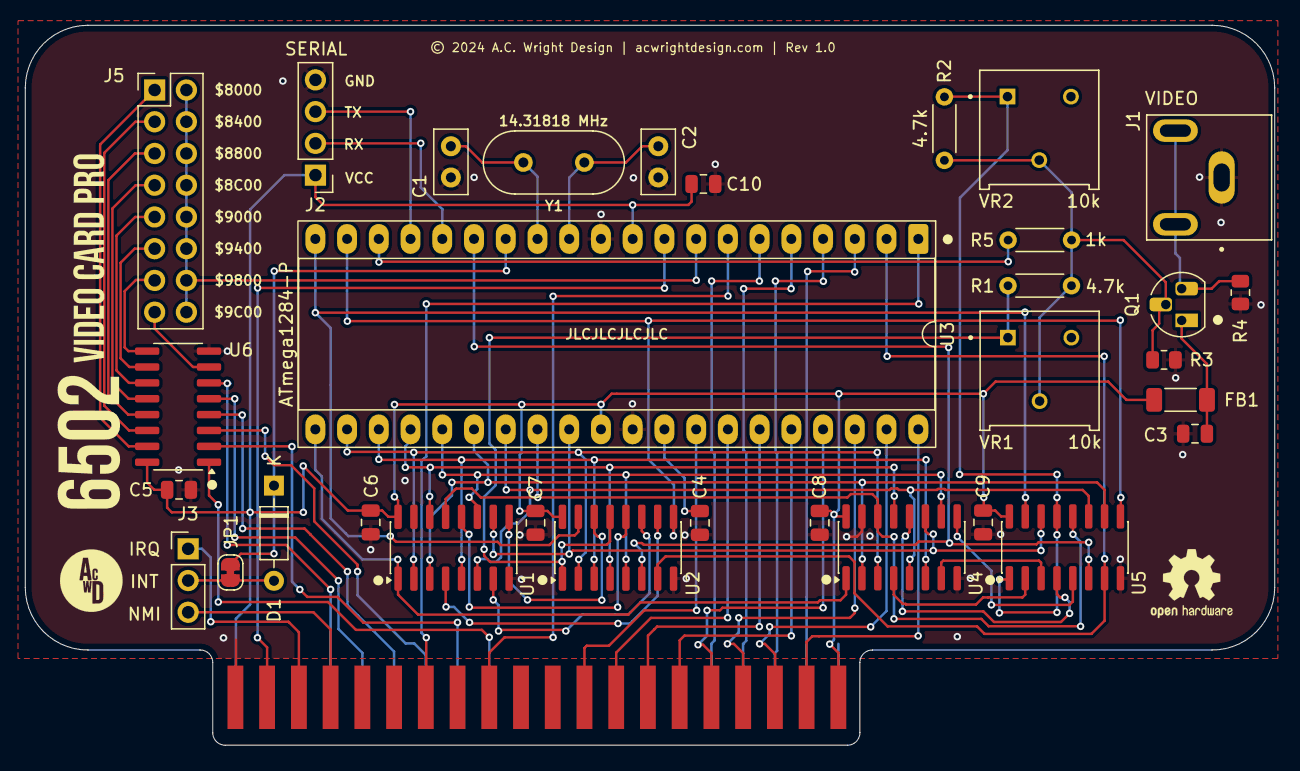
[picture p203: board Video Card Pro.kicad_pcb from above]

Board: 2 copper layers, 100.0 x 57.6 mm, 33 parts (0 on the bottom side), 68 nets.
