acwright/6502/Hardware/Backplane Helper/Rev 1.0/Backplane Helper.kicad_pcb

## KiCad design Hardware/Backplane Helper/Rev 1.0/Backplane Helper.kicad_pcb (2025-12-04)

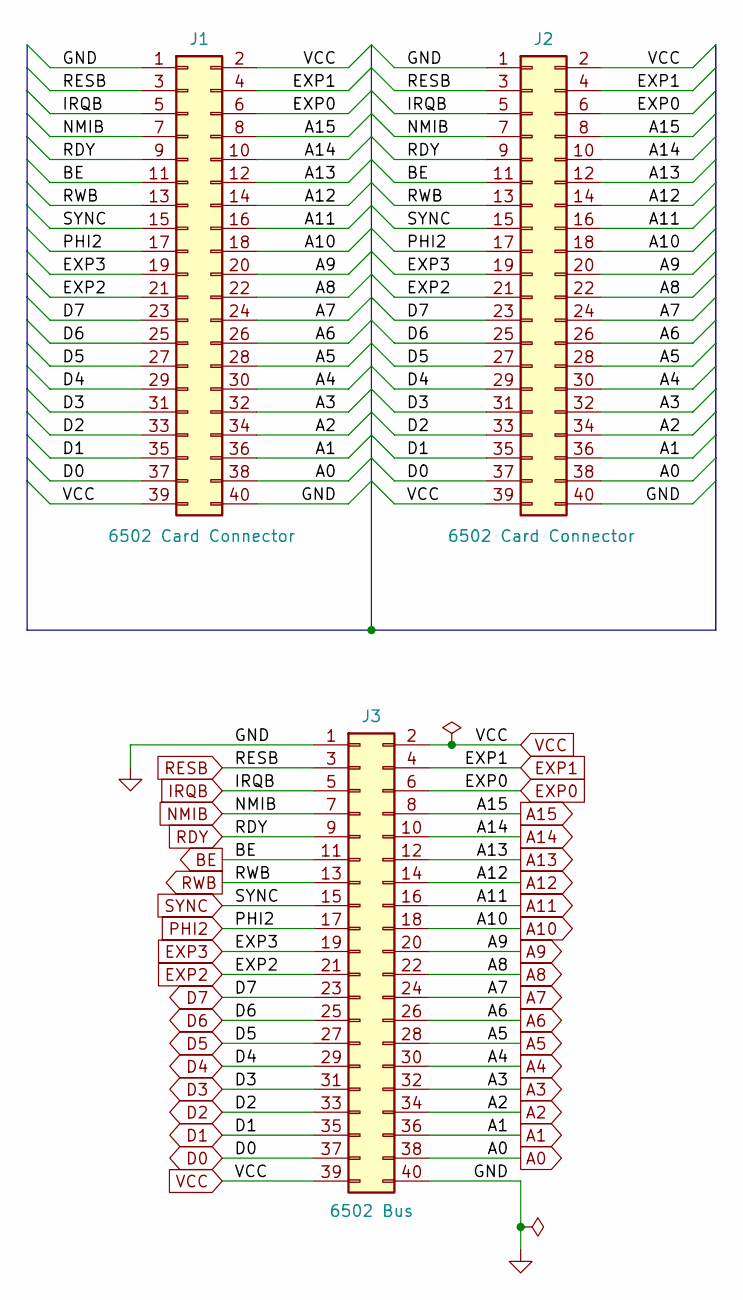
[picture p204: schematic Backplane Helper.kicad_sch, 6502 Backplane Helper]

Parts:
J1, J2: 6502 Card Connector; RHDR40W82P485X254_2X20_5740X93; Mouser 571-5-5530843-4
J3: 6502 Bus; 6502 Bus Connector; Digikey 732-5401-ND

Connections:
A0: J1.38, J2.38, J3.38
A1: J1.36, J2.36, J3.36
A2: J1.34, J2.34, J3.34
A3: J1.32, J2.32, J3.32
A4: J1.30, J2.30, J3.30
A5: J1.28, J2.28, J3.28
A6: J1.26, J2.26, J3.26
A7: J1.24, J2.24, J3.24
A8: J1.22, J2.22, J3.22
A9: J1.20, J2.20, J3.20
A10: J1.18, J2.18, J3.18
A11: J1.16, J2.16, J3.16
A12: J1.14, J2.14, J3.14
A13: J1.12, J2.12, J3.12
A14: J1.10, J2.10, J3.10
A15: J1.8, J2.8, J3.8
BE: J1.11, J2.11, J3.11
D0: J1.37, J2.37, J3.37
D1: J1.35, J2.35, J3.35
D2: J1.33, J2.33, J3.33
D3: J1.31, J2.31, J3.31
D4: J1.29, J2.29, J3.29
D5: J1.27, J2.27, J3.27
D6: J1.25, J2.25, J3.25
D7: J1.23, J2.23, J3.23
EXP0: J1.6, J2.6, J3.6
EXP1: J1.4, J2.4, J3.4
EXP2: J1.21, J2.21, J3.21
EXP3: J1.19, J2.19, J3.19
GND: J1.1, J1.40, J2.1, J2.40, J3.1, J3.40
IRQB: J1.5, J2.5, J3.5
NMIB: J1.7, J2.7, J3.7
PHI2: J1.17, J2.17, J3.17
RDY: J1.9, J2.9, J3.9
RESB: J1.3, J2.3, J3.3
RWB: J1.13, J2.13, J3.13
SYNC: J1.15, J2.15, J3.15
VCC: J1.2, J1.39, J2.2, J2.39, J3.2, J3.39

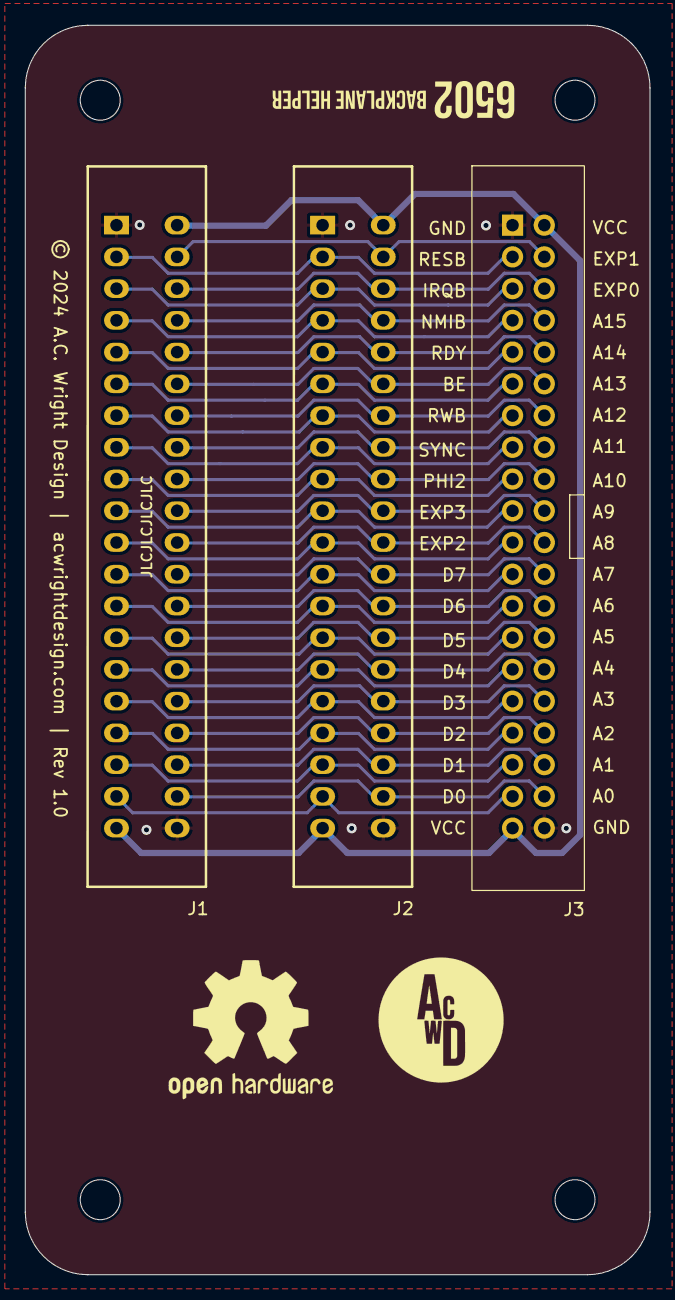
[picture p205: board Backplane Helper.kicad_pcb from above]

Board: 2 copper layers, 50.0 x 100.0 mm, 7 parts (0 on the bottom side), 38 nets.

Other parts of the board:
H1, H2, H3, H4: MountingHole; MountingHole_3.2mm_M3
