acwright/6502/Hardware/Dev Board/Rev 1.0/Dev Board.kicad_pcb

## KiCad design Hardware/Dev Board/Rev 1.0/Dev Board.kicad_pcb (2025-10-29)

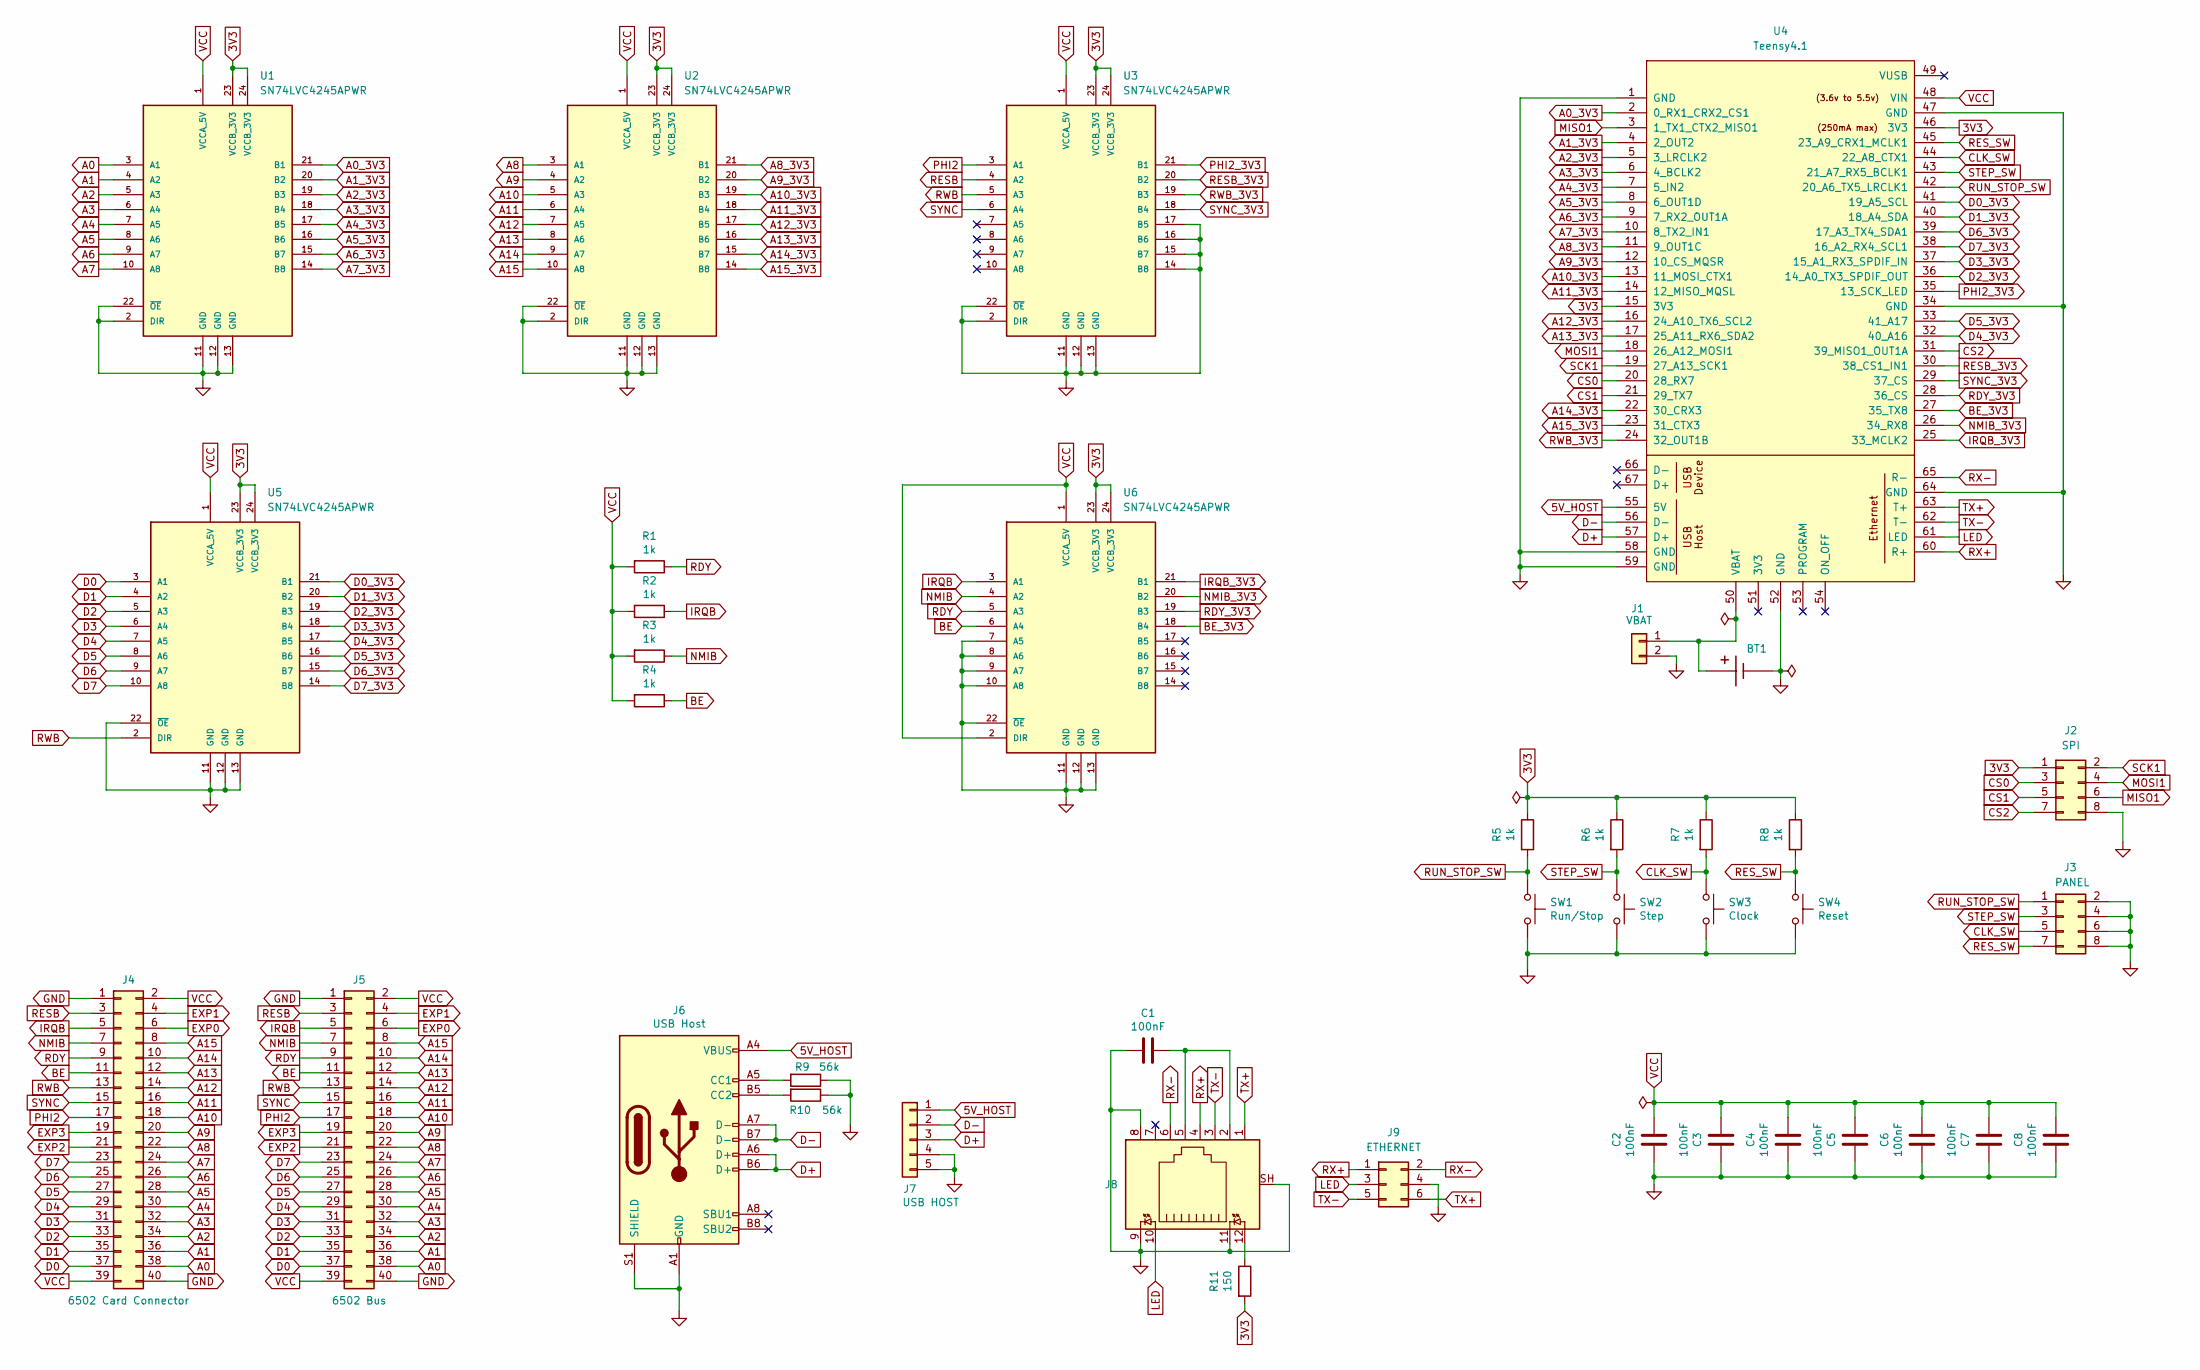
[picture p206: schematic Dev Board.kicad_sch, 6502 Dev Board]

Parts:
BT1: BAT-HLD-001-THM; BAT_BAT-HLD-001-THM
C1, C2, C3, C4, C5, C6, C7, C8: 100nF; C_0805_2012Metric; LCSC C49678
J1: VBAT; PinHeader_1x02_P2.54mm_Vertical
J2: SPI; PinHeader_2x04_P2.54mm_Vertical
J3: PANEL; PinHeader_2x04_P2.54mm_Vertical
J4: 6502 Card Connector; RHDR40W82P485X254_2X20_5740X93
J5: 6502 Bus; 6502 Bus Connector
J6: USB Host; USB_C_Receptacle_HRO_TYPE-C-31-M-12; LCSC C2988369
J7: USB HOST; PinHeader_1x05_P2.54mm_Vertical
J8: RJ45_LED; J1B1211CCD; MPN J1B1211CCD
J9: ETHERNET; PinHeader_2x03_P2.00mm_Vertical
R1, R2, R3, R4, R5, R6, R7, R8: 1k; R_0805_2012Metric; LCSC C17513
R9, R10: 56k; R_0805_2012Metric; LCSC C169923
R11: 150; R_0805_2012Metric; LCSC C17471
SW1: Run/Stop; SW_TS-1187A-B-A-B; LCSC C318884
SW2: Step; SW_TS-1187A-B-A-B; LCSC C318884
SW3: Clock; SW_TS-1187A-B-A-B; LCSC C318884
SW4: Reset; SW_TS-1187A-B-A-B; LCSC C318884
U1, U2, U3, U5, U6: SN74LVC4245APWR; TSSOP-24_4.4x7.8mm_P0.65mm; LCSC C7859
U4: Teensy4.1; Teensy41

Connections:
3V3: J2.1, R5.1, R6.1, R7.1, R8.1, R11.2, U1.23 (VCCB_3V3), U1.24 (VCCB_3V3), U2.23 (VCCB_3V3), U2.24 (VCCB_3V3), U3.23 (VCCB_3V3), U3.24 (VCCB_3V3), U4.15 (3V3), U4.46 (3V3), U5.23 (VCCB_3V3), U5.24 (VCCB_3V3), U6.23 (VCCB_3V3), U6.24 (VCCB_3V3)
5V_HOST: J6.A4 (VBUS), J6.A9 (VBUS), J6.B4 (VBUS), J6.B9 (VBUS), J7.1, U4.55 (5V)
A0: J4.38, J5.38, U1.3 (A1)
A0_3V3: U1.21 (B1), U4.2 (0_RX1_CRX2_CS1)
A1: J4.36, J5.36, U1.4 (A2)
A1_3V3: U1.20 (B2), U4.4 (2_OUT2)
A2: J4.34, J5.34, U1.5 (A3)
A2_3V3: U1.19 (B3), U4.5 (3_LRCLK2)
A3: J4.32, J5.32, U1.6 (A4)
A3_3V3: U1.18 (B4), U4.6 (4_BCLK2)
A4: J4.30, J5.30, U1.7 (A5)
A4_3V3: U1.17 (B5), U4.7 (5_IN2)
A5: J4.28, J5.28, U1.8 (A6)
A5_3V3: U1.16 (B6), U4.8 (6_OUT1D)
A6: J4.26, J5.26, U1.9 (A7)
A6_3V3: U1.15 (B7), U4.9 (7_RX2_OUT1A)
A7: J4.24, J5.24, U1.10 (A8)
A7_3V3: U1.14 (B8), U4.10 (8_TX2_IN1)
A8: J4.22, J5.22, U2.3 (A1)
A8_3V3: U2.21 (B1), U4.11 (9_OUT1C)
A9: J4.20, J5.20, U2.4 (A2)
A9_3V3: U2.20 (B2), U4.12 (10_CS_MQSR)
A10: J4.18, J5.18, U2.5 (A3)
A10_3V3: U2.19 (B3), U4.13 (11_MOSI_CTX1)
A11: J4.16, J5.16, U2.6 (A4)
A11_3V3: U2.18 (B4), U4.14 (12_MISO_MQSL)
A12: J4.14, J5.14, U2.7 (A5)
A12_3V3: U2.17 (B5), U4.16 (24_A10_TX6_SCL2)
A13: J4.12, J5.12, U2.8 (A6)
A13_3V3: U2.16 (B6), U4.17 (25_A11_RX6_SDA2)
A14: J4.10, J5.10, U2.9 (A7)
A14_3V3: U2.15 (B7), U4.22 (30_CRX3)
A15: J4.8, J5.8, U2.10 (A8)
A15_3V3: U2.14 (B8), U4.23 (31_CTX3)
BE: J4.11, J5.11, R4.1, U6.6 (A4)
BE_3V3: U4.27 (35_TX8), U6.18 (B4)
CLK_SW: J3.5, R7.2, SW3.1, U4.44 (22_A8_CTX1)
CS0: J2.3, U4.20 (28_RX7)
CS1: J2.5, U4.21 (29_TX7)
CS2: J2.7, U4.31 (39_MISO1_OUT1A)
D0: J4.37, J5.37, U5.3 (A1)
D0_3V3: U4.41 (19_A5_SCL), U5.21 (B1)
D1: J4.35, J5.35, U5.4 (A2)
D1_3V3: U4.40 (18_A4_SDA), U5.20 (B2)
D2: J4.33, J5.33, U5.5 (A3)
D2_3V3: U4.36 (14_A0_TX3_SPDIF_OUT), U5.19 (B3)
D3: J4.31, J5.31, U5.6 (A4)
D3_3V3: U4.37 (15_A1_RX3_SPDIF_IN), U5.18 (B4)
D4: J4.29, J5.29, U5.7 (A5)
D4_3V3: U4.32 (40_A16), U5.17 (B5)
D5: J4.27, J5.27, U5.8 (A6)
D5_3V3: U4.33 (41_A17), U5.16 (B6)
D6: J4.25, J5.25, U5.9 (A7)
D6_3V3: U4.39 (17_A3_TX4_SDA1), U5.15 (B7)
D7: J4.23, J5.23, U5.10 (A8)
D7_3V3: U4.38 (16_A2_RX4_SCL1), U5.14 (B8)
D+: J6.A6 (D+), J6.B6 (D+), J7.3, U4.57 (D+)
D-: J6.A7 (D-), J6.B7 (D-), J7.2, U4.56 (D-)
EXP0: J4.6, J5.6
EXP1: J4.4, J5.4
EXP2: J4.21, J5.21
EXP3: J4.19, J5.19
GND: BT1.-, C1.2, C2.2, C3.1, C4.2, C5.1, C6.2, C7.1, C8.2, J1.2, J2.8, J3.2, J3.4, J3.6, J3.8, J4.1, J4.40, J5.1, J5.40, J6.A1 (GND), J6.A12 (GND), J6.B1 (GND), J6.B12 (GND), J6.S1 (SHIELD), J7.4, J7.5, J8.8, J8.9, J8.11, J8.SH, J9.4, R9.1, R10.1, SW1.2, SW2.2, SW3.2, SW4.2, U1.2 (DIR), U1.11 (GND), U1.12 (GND), U1.13 (GND), U1.22 (~OE), U2.2 (DIR), U2.11 (GND), U2.12 (GND), U2.13 (GND), U2.22 (~OE), U3.2 (DIR), U3.11 (GND), U3.12 (GND), U3.13 (GND), U3.14 (B8), U3.15 (B7), U3.16 (B6), U3.17 (B5), U3.22 (~OE), U4.1 (GND), U4.34 (GND), U4.47 (GND), U4.52 (GND), U4.58 (GND), U4.59 (GND), U4.64 (GND), U5.11 (GND), U5.12 (GND), U5.13 (GND), U5.22 (~OE), U6.7 (A5), U6.8 (A6), U6.9 (A7), U6.10 (A8), U6.11 (GND), U6.12 (GND), U6.13 (GND), U6.22 (~OE)
IRQB: J4.5, J5.5, R2.1, U6.3 (A1)
IRQB_3V3: U4.25 (33_MCLK2), U6.21 (B1)
LED: J8.10, J9.3, U4.61 (LED)
MISO1: J2.6, U4.3 (1_TX1_CTX2_MISO1)
MOSI1: J2.4, U4.18 (26_A12_MOSI1)
NMIB: J4.7, J5.7, R3.1, U6.4 (A2)
NMIB_3V3: U4.26 (34_RX8), U6.20 (B2)
unnamed: C1.1, J8.2, J8.5
unnamed: BT1.+, J1.1, U4.50 (VBAT)
unnamed: J6.A5 (CC1), R9.2
unnamed: J6.B5 (CC2), R10.2
unnamed: J8.12, R11.1
PHI2: J4.17, J5.17, U3.3 (A1)
PHI2_3V3: U3.21 (B1), U4.35 (13_SCK_LED)
RDY: J4.9, J5.9, R1.1, U6.5 (A3)
RDY_3V3: U4.28 (36_CS), U6.19 (B3)
RESB: J4.3, J5.3, U3.4 (A2)
RESB_3V3: U3.20 (B2), U4.30 (38_CS1_IN1)
RES_SW: J3.7, R8.2, SW4.1, U4.45 (23_A9_CRX1_MCLK1)
RUN_STOP_SW: J3.1, R5.2, SW1.1, U4.42 (20_A6_TX5_LRCLK1)
RWB: J4.13, J5.13, U3.5 (A3), U5.2 (DIR)
RWB_3V3: U3.19 (B3), U4.24 (32_OUT1B)
RX+: J8.4, J9.1, U4.60 (R+)
RX-: J8.6, J9.2, U4.65 (R-)
SCK1: J2.2, U4.19 (27_A13_SCK1)
STEP_SW: J3.3, R6.2, SW2.1, U4.43 (21_A7_RX5_BCLK1)
SYNC: J4.15, J5.15, U3.6 (A4)
SYNC_3V3: U3.18 (B4), U4.29 (37_CS)
TX+: J8.1, J9.6, U4.63 (T+)
TX-: J8.3, J9.5, U4.62 (T-)
VCC: C2.1, C3.2, C4.1, C5.2, C6.1, C7.2, C8.1, J4.2, J4.39, J5.2, J5.39, R1.2, R2.2, R3.2, R4.2, U1.1 (VCCA_5V), U2.1 (VCCA_5V), U3.1 (VCCA_5V), U4.48 (VIN), U5.1 (VCCA_5V), U6.1 (VCCA_5V), U6.2 (DIR)
