acwright/6502/Hardware/RAM Card/Rev 1.0/RAM Card.kicad_pcb

## KiCad design Hardware/RAM Card/Rev 1.0/RAM Card.kicad_pcb (2025-10-29)

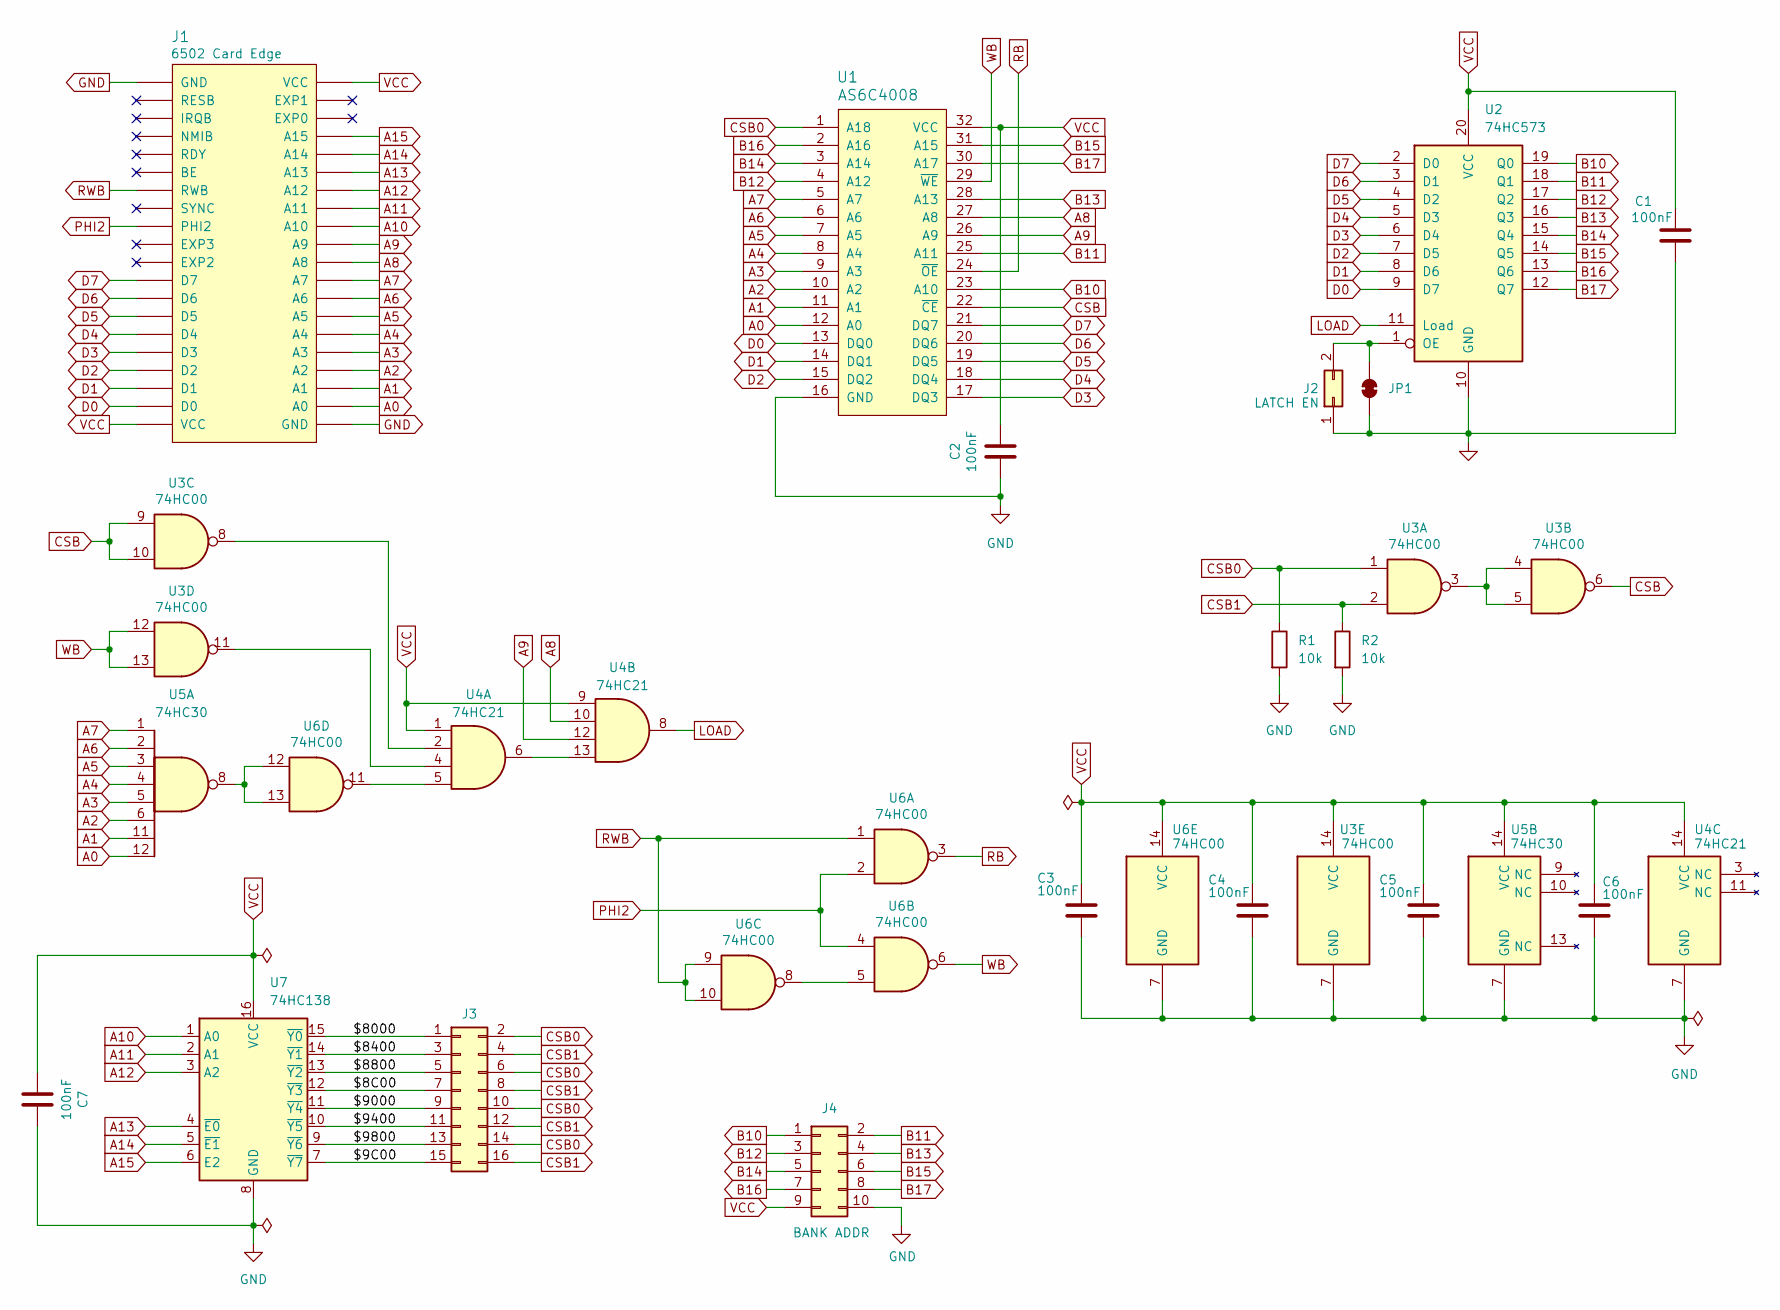
[picture p208: schematic RAM Card.kicad_sch, 6502 RAM Card]

Parts:
C1, C2, C3, C4, C5, C6, C7: 100nF; C_0805_2012Metric; LCSC C49678
J1: 6502 Card Edge
J2: LATCH EN; PinHeader_1x02_P2.54mm_Vertical
J3: Conn_02x08_Odd_Even; PinHeader_2x08_P2.54mm_Vertical
J4: BANK ADDR; PinHeader_2x05_P2.54mm_Vertical
JP1: Latch Enable; SolderJumper-2_P1.3mm_Bridged_RoundedPad1.0x1.5mm
R1, R2: 10k; R_0805_2012Metric; LCSC C17414
U1: AS6C4008; DIP-32_W15.24mm_Socket_LongPads
U2: 74HC573; SOIC-20W_7.5x12.8mm_P1.27mm; LCSC C5608
U3, U6: 74HC00; SOIC-14_3.9x8.7mm_P1.27mm; LCSC C5586
U4: 74HC21; SOIC-14_3.9x8.7mm_P1.27mm; LCSC C75398
U5: 74HC30; SOIC-14_3.9x8.7mm_P1.27mm; LCSC C19818870
U7: 74HC138; SOIC-16_3.9x9.9mm_P1.27mm; LCSC C5602

Connections:
/$8C00: J3.7, U7.12 (~Y3)
/$9C00: J3.15, U7.7 (~Y7)
/$8000: J3.1, U7.15 (~Y0)
/$8400: J3.3, U7.14 (~Y1)
/$8800: J3.5, U7.13 (~Y2)
/$9000: J3.9, U7.11 (~Y4)
/$9400: J3.11, U7.10 (~Y5)
/$9800: J3.13, U7.9 (~Y6)
A0: J1.A0, U1.12 (A0), U5.12
A1: J1.A1, U1.11 (A1), U5.11
A2: J1.A2, U1.10 (A2), U5.6
A3: J1.A3, U1.9 (A3), U5.5
A4: J1.A4, U1.8 (A4), U5.4
A5: J1.A5, U1.7 (A5), U5.3
A6: J1.A6, U1.6 (A6), U5.2
A7: J1.A7, U1.5 (A7), U5.1
A8: J1.A8, U1.27 (A8), U4.10
A9: J1.A9, U1.26 (A9), U4.12
A10: J1.A10, U7.1 (A0)
A11: J1.A11, U7.2 (A1)
A12: J1.A12, U7.3 (A2)
A13: J1.A13, U7.4 (~E0)
A14: J1.A14, U7.5 (~E1)
A15: J1.A15, U7.6 (E2)
B10: J4.1, U1.23 (A10), U2.19 (Q0)
B11: J4.2, U1.25 (A11), U2.18 (Q1)
B12: J4.3, U1.4 (A12), U2.17 (Q2)
B13: J4.4, U1.28 (A13), U2.16 (Q3)
B14: J4.5, U1.3 (A14), U2.15 (Q4)
B15: J4.6, U1.31 (A15), U2.14 (Q5)
B16: J4.7, U1.2 (A16), U2.13 (Q6)
B17: J4.8, U1.30 (A17), U2.12 (Q7)
CSB: U1.22 (~CE), U3.6, U3.9, U3.10
CSB0: J3.2, J3.6, J3.10, J3.14, R1.1, U1.1 (A18), U3.1
CSB1: J3.4, J3.8, J3.12, J3.16, R2.1, U3.2
D0: J1.D0, U1.13 (DQ0), U2.9 (D7)
D1: J1.D1, U1.14 (DQ1), U2.8 (D6)
D2: J1.D2, U1.15 (DQ2), U2.7 (D5)
D3: J1.D3, U1.17 (DQ3), U2.6 (D4)
D4: J1.D4, U1.18 (DQ4), U2.5 (D3)
D5: J1.D5, U1.19 (DQ5), U2.4 (D2)
D6: J1.D6, U1.20 (DQ6), U2.3 (D1)
D7: J1.D7, U1.21 (DQ7), U2.2 (D0)
GND: C1.2, C2.2, C3.2, C4.2, C5.2, C6.2, C7.2, J1.GND, J2.1, J4.10, JP1.1 (A), R1.2, R2.2, U1.16 (GND), U2.10 (GND), U3.7 (GND), U4.7 (GND), U5.7 (GND), U6.7 (GND), U7.8 (GND)
LOAD: U2.11 (Load), U4.8
unnamed: J2.2, JP1.2 (B), U2.1 (OE)
unnamed: U3.3, U3.4, U3.5
unnamed: U3.8, U4.2
unnamed: U3.11, U4.4
unnamed: U4.5, U6.11
unnamed: U4.6, U4.13
unnamed: U5.8, U6.12, U6.13
unnamed: U6.5, U6.8
PHI2: J1.PHI2, U6.2, U6.4
RB: U1.24 (~OE), U6.3
RWB: J1.RWB, U6.1, U6.9, U6.10
VCC: C1.1, C2.1, C3.1, C4.1, C5.1, C6.1, C7.1, J1.VCC, J4.9, U1.32 (VCC), U2.20 (VCC), U3.14 (VCC), U4.1, U4.9, U4.14 (VCC), U5.14 (VCC), U6.14 (VCC), U7.16 (VCC)
WB: U1.29 (~WE), U3.12, U3.13, U6.6

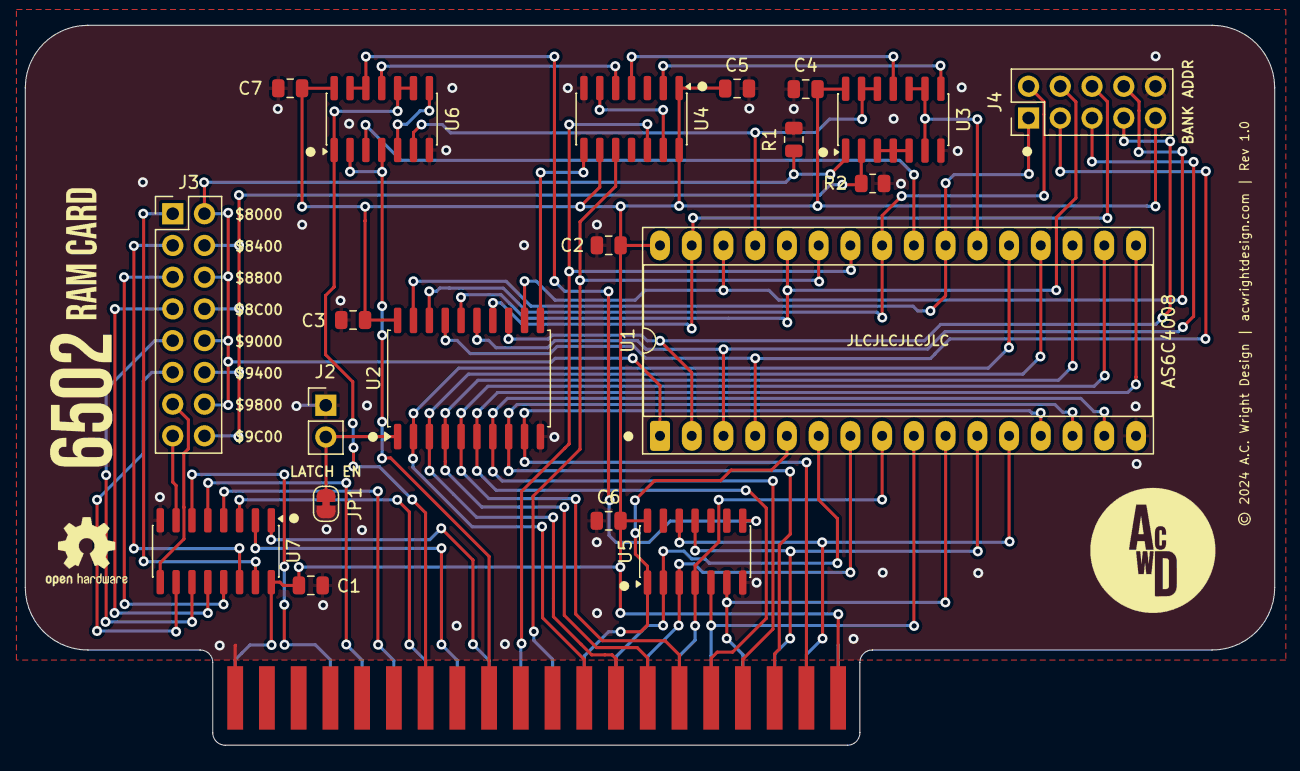
[picture p209: board RAM Card.kicad_pcb from above]

Board: 2 copper layers, 100.0 x 57.6 mm, 21 parts (0 on the bottom side), 58 nets.
