acwright/6502/Hardware/Keyboard Helper/Rev 1.0/Keyboard Helper.kicad_pcb

## KiCad design Hardware/Keyboard Helper/Rev 1.0/Keyboard Helper.kicad_pcb (2025-10-27)

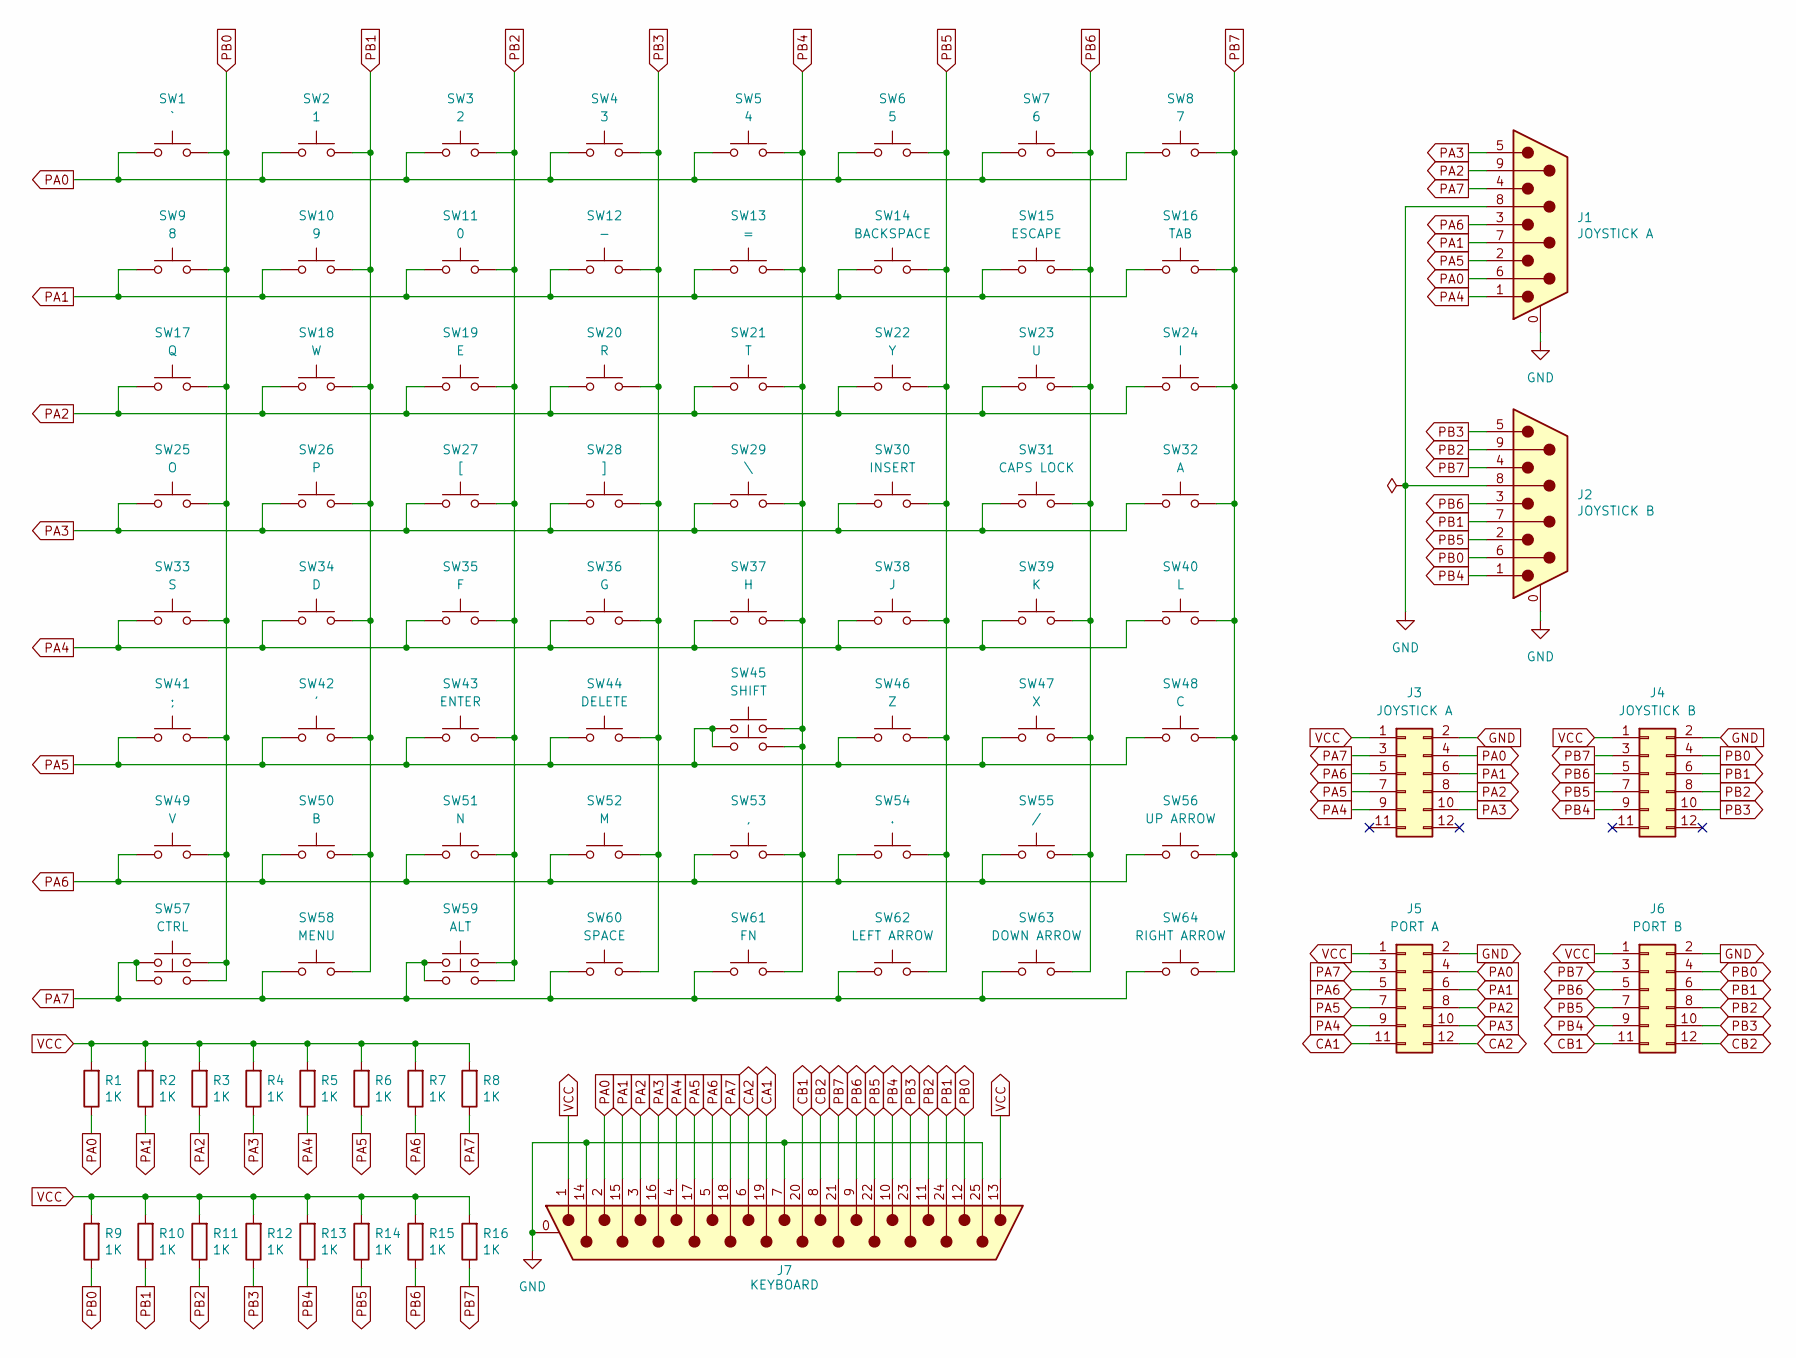
[picture p210: schematic Keyboard Helper.kicad_sch, 6502 Keyboard Helper]

Parts:
J1: JOYSTICK A; DSUB-9_Pins_Horizontal_P2.77x2.84mm_EdgePinOffset7.70mm_Hou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; MPN D09P33E4GX00LF; Digikey 609-1481-ND
J2: JOYSTICK B; DSUB-9_Pins_Horizontal_P2.77x2.84mm_EdgePinOffset7.70mm_Hou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; MPN D09P33E4GX00LF; Digikey 609-1481-ND
J3: JOYSTICK A; 6502 GPIO Connector
J4: JOYSTICK B; 6502 GPIO Connector
J5: PORT A; 6502 GPIO Connector
J6: PORT B; 6502 GPIO Connector
J7: KEYBOARD; DSUB-25_Pins_Horizontal_P2.77x2.84mm_EdgePinOffset7.70mm_Ho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; MPN D25P33E4GX00LF; Digikey 609-1505-ND
R1, R2, R3, R4, R5, R6, R7, R8, R9, R10, R11, R12, R13, R14, R15, R16: 1K; R_Axial_DIN0204_L3.6mm_D1.6mm_P5.08mm_Horizontal
SW1: `; SW_Cherry_MX_1.00u_PCB
SW2: 1; SW_Cherry_MX_1.00u_PCB
SW3: 2; SW_Cherry_MX_1.00u_PCB
SW4: 3; SW_Cherry_MX_1.00u_PCB
SW5: 4; SW_Cherry_MX_1.00u_PCB
SW6: 5; SW_Cherry_MX_1.00u_PCB
SW7: 6; SW_Cherry_MX_1.00u_PCB
SW8: 7; SW_Cherry_MX_1.00u_PCB
SW9: 8; SW_Cherry_MX_1.00u_PCB
SW10: 9; SW_Cherry_MX_1.00u_PCB
SW11: 0; SW_Cherry_MX_1.00u_PCB
SW12: -; SW_Cherry_MX_1.00u_PCB
SW13: =; SW_Cherry_MX_1.00u_PCB
SW14: BACKSPACE; SW_Cherry_MX_2.00u_PCB
SW15: ESCAPE; SW_Cherry_MX_1.00u_PCB
SW16: TAB; SW_Cherry_MX_1.50u_PCB
SW17: Q; SW_Cherry_MX_1.00u_PCB
SW18: W; SW_Cherry_MX_1.00u_PCB
SW19: E; SW_Cherry_MX_1.00u_PCB
SW20: R; SW_Cherry_MX_1.00u_PCB
SW21: T; SW_Cherry_MX_1.00u_PCB
SW22: Y; SW_Cherry_MX_1.00u_PCB
SW23: U; SW_Cherry_MX_1.00u_PCB
SW24: I; SW_Cherry_MX_1.00u_PCB
SW25: O; SW_Cherry_MX_1.00u_PCB
SW26: P; SW_Cherry_MX_1.00u_PCB
SW27: [; SW_Cherry_MX_1.00u_PCB
SW28: ]; SW_Cherry_MX_1.00u_PCB
SW29: \; SW_Cherry_MX_1.50u_PCB
SW30: INSERT; SW_Cherry_MX_1.00u_PCB
SW31: CAPS LOCK; SW_Cherry_MX_1.75u_PCB
SW32: A; SW_Cherry_MX_1.00u_PCB
SW33: S; SW_Cherry_MX_1.00u_PCB
SW34: D; SW_Cherry_MX_1.00u_PCB
SW35: F; SW_Cherry_MX_1.00u_PCB
SW36: G; SW_Cherry_MX_1.00u_PCB
SW37: H; SW_Cherry_MX_1.00u_PCB
SW38: J; SW_Cherry_MX_1.00u_PCB
SW39: K; SW_Cherry_MX_1.00u_PCB
SW40: L; SW_Cherry_MX_1.00u_PCB
SW41: ;; SW_Cherry_MX_1.00u_PCB
SW42: '; SW_Cherry_MX_1.00u_PCB
SW43: ENTER; SW_Cherry_MX_2.25u_PCB
SW44: DELETE; SW_Cherry_MX_1.00u_PCB
SW45: SHIFT; SW_Cherry_MX_2.25u_PCB
SW46: Z; SW_Cherry_MX_1.00u_PCB
SW47: X; SW_Cherry_MX_1.00u_PCB
SW48: C; SW_Cherry_MX_1.00u_PCB
SW49: V; SW_Cherry_MX_1.00u_PCB
SW50: B; SW_Cherry_MX_1.00u_PCB
SW51: N; SW_Cherry_MX_1.00u_PCB
SW52: M; SW_Cherry_MX_1.00u_PCB
SW53: ,; SW_Cherry_MX_1.00u_PCB
SW54: .; SW_Cherry_MX_1.00u_PCB
SW55: /; SW_Cherry_MX_1.00u_PCB
SW56: UP ARROW; SW_Cherry_MX_1.00u_PCB
SW57: CTRL; SW_Cherry_MX_1.25u_PCB
SW58: MENU; SW_Cherry_MX_1.00u_PCB
SW59: ALT; SW_Cherry_MX_1.25u_PCB
SW60: SPACE; SW_Cherry_MX_6.25u_PCB
SW61: FN; SW_Cherry_MX_1.25u_PCB
SW62: LEFT ARROW; SW_Cherry_MX_1.00u_PCB
SW63: DOWN ARROW; SW_Cherry_MX_1.00u_PCB
SW64: RIGHT ARROW; SW_Cherry_MX_1.00u_PCB
SW65: R SHIFT; SW_Cherry_MX_2.25u_PCB
SW66: R ALT; SW_Cherry_MX_1.25u_PCB
SW67: R CTRL; SW_Cherry_MX_1.25u_PCB

Connections:
CA1: J5.11, J7.19
CA2: J5.12, J7.6
CB1: J6.11, J7.20
CB2: J6.12, J7.8
GND: J1.0 (PAD), J1.8, J2.0 (PAD), J2.8, J3.2, J4.2, J5.2, J6.2, J7.0 (PAD), J7.7, J7.14, J7.25
PA0: J1.6, J3.4, J5.4, J7.2, R1.1, SW1.1, SW2.1, SW3.1, SW4.1, SW5.1, SW6.1, SW7.1, SW8.1
PA1: J1.7, J3.6, J5.6, J7.15, R2.1, SW9.1, SW10.1, SW11.1, SW12.1, SW13.1, SW14.1, SW15.1, SW16.1
PA2: J1.9, J3.8, J5.8, J7.3, R3.1, SW17.1, SW18.1, SW19.1, SW20.1, SW21.1, SW22.1, SW23.1, SW24.1
PA3: J1.5, J3.10, J5.10, J7.16, R4.1, SW25.1, SW26.1, SW27.1, SW28.1, SW29.1, SW30.1, SW31.1, SW32.1
PA4: J1.1, J3.9, J5.9, J7.4, R5.1, SW33.1, SW34.1, SW35.1, SW36.1, SW37.1, SW38.1, SW39.1, SW40.1
PA5: J1.2, J3.7, J5.7, J7.17, R6.1, SW41.1, SW42.1, SW43.1, SW44.1, SW45.1, SW46.1, SW47.1, SW48.1, SW65.1
PA6: J1.3, J3.5, J5.5, J7.5, R7.1, SW49.1, SW50.1, SW51.1, SW52.1, SW53.1, SW54.1, SW55.1, SW56.1
PA7: J1.4, J3.3, J5.3, J7.18, R8.1, SW57.1, SW58.1, SW59.1, SW60.1, SW61.1, SW62.1, SW63.1, SW64.1, SW66.1, SW67.1
PB0: J2.6, J4.4, J6.4, J7.12, R9.1, SW1.2, SW9.2, SW17.2, SW25.2, SW33.2, SW41.2, SW49.2, SW57.2, SW67.2
PB1: J2.7, J4.6, J6.6, J7.24, R10.1, SW2.2, SW10.2, SW18.2, SW26.2, SW34.2, SW42.2, SW50.2, SW58.2
PB2: J2.9, J4.8, J6.8, J7.11, R11.1, SW3.2, SW11.2, SW19.2, SW27.2, SW35.2, SW43.2, SW51.2, SW59.2, SW66.2
PB3: J2.5, J4.10, J6.10, J7.23, R12.1, SW4.2, SW12.2, SW20.2, SW28.2, SW36.2, SW44.2, SW52.2, SW60.2
PB4: J2.1, J4.9, J6.9, J7.10, R13.1, SW5.2, SW13.2, SW21.2, SW29.2, SW37.2, SW45.2, SW53.2, SW61.2, SW65.2
PB5: J2.2, J4.7, J6.7, J7.22, R14.1, SW6.2, SW14.2, SW22.2, SW30.2, SW38.2, SW46.2, SW54.2, SW62.2
PB6: J2.3, J4.5, J6.5, J7.9, R15.1, SW7.2, SW15.2, SW23.2, SW31.2, SW39.2, SW47.2, SW55.2, SW63.2
PB7: J2.4, J4.3, J6.3, J7.21, R16.1, SW8.2, SW16.2, SW24.2, SW32.2, SW40.2, SW48.2, SW56.2, SW64.2
VCC: J3.1, J4.1, J5.1, J6.1, J7.1, J7.13, R1.2, R2.2, R3.2, R4.2, R5.2, R6.2, R7.2, R8.2, R9.2, R10.2, R11.2, R12.2, R13.2, R14.2, R15.2, R16.2

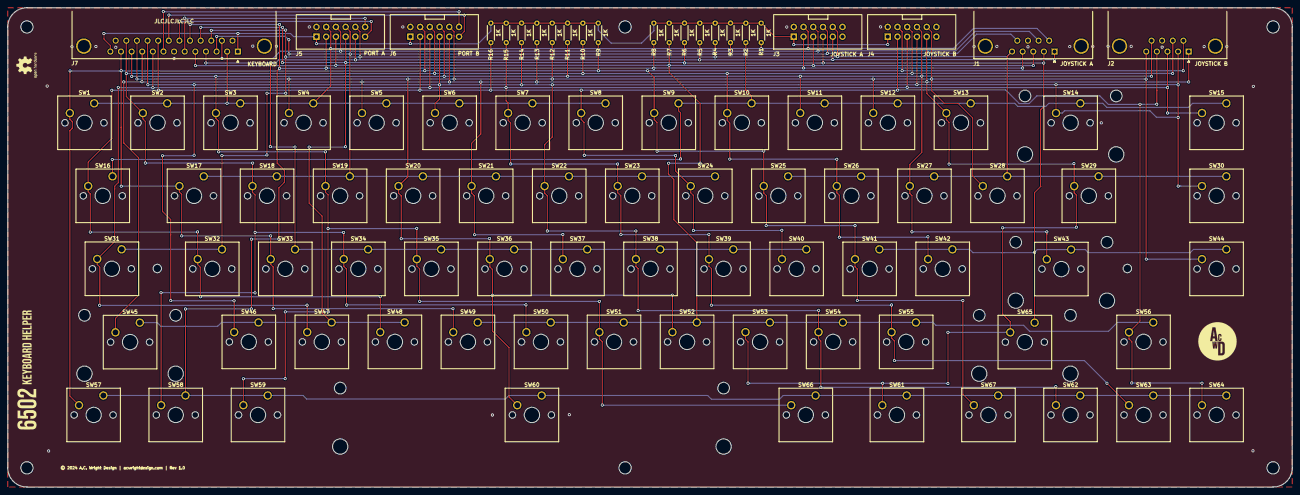
[picture p211: board Keyboard Helper.kicad_pcb from above]

Board: 2 copper layers, 335.0 x 125.0 mm, 98 parts (0 on the bottom side), 22 nets.

Other parts of the board:
H1, H2, H2#2, H2#3, H3#3, H4: MountingHole; MountingHole_3.2mm_M3
H3, H3#2: MountingHole; MountingHole_2.2mm_M2
