acwright/6502/Hardware/Keypad LCD Helper/Rev 1.0/Keypad LCD Helper.kicad_pcb

## KiCad design Hardware/Keypad LCD Helper/Rev 1.0/Keypad LCD Helper.kicad_pcb (2025-10-14)

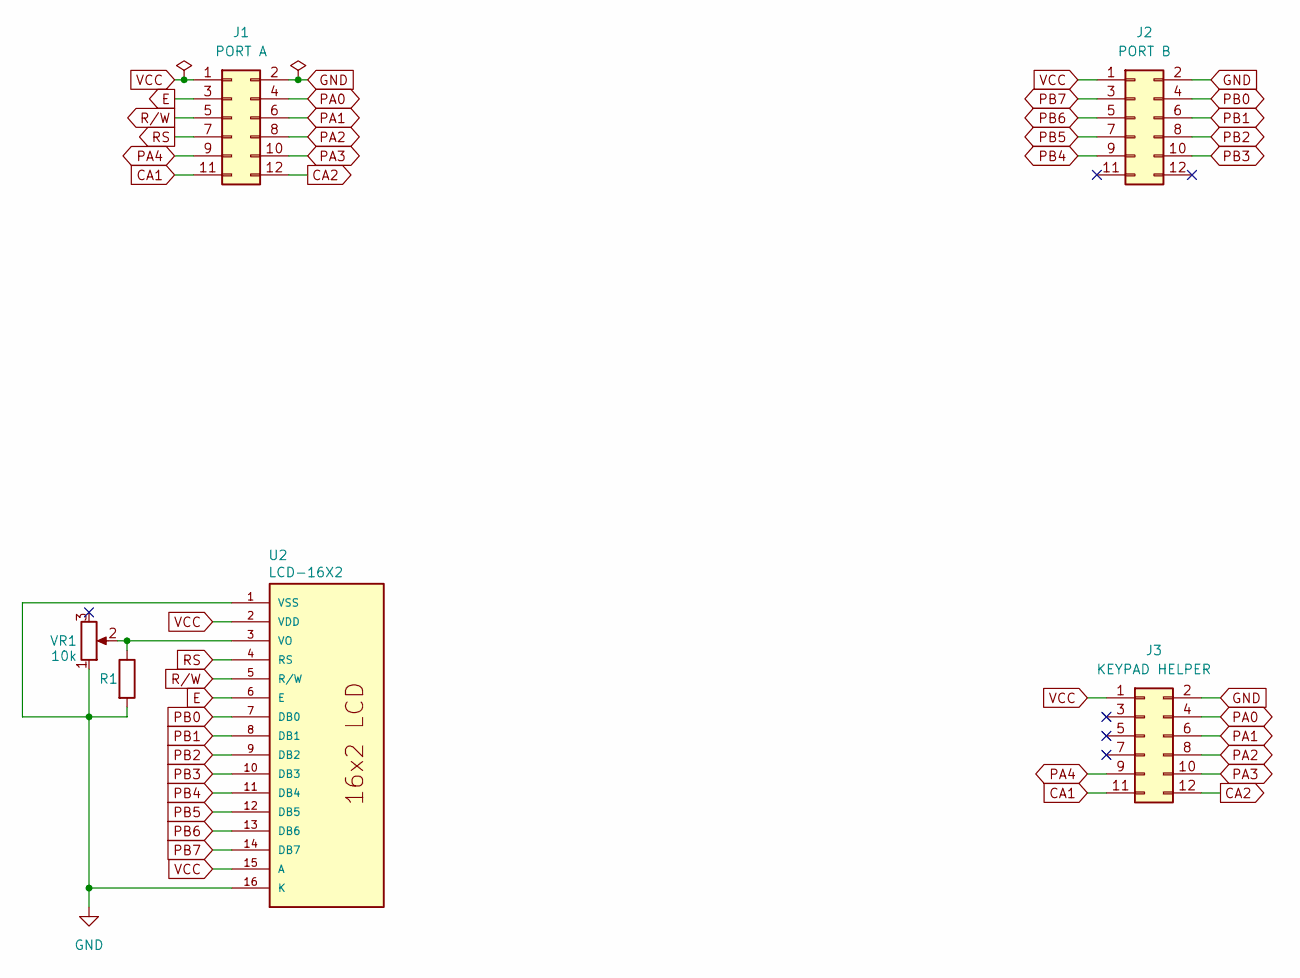
[picture p214: schematic Keypad LCD Helper.kicad_sch, 6502 Keypad LCD Helper]

Parts:
J1: PORT A; 6502 GPIO Connector
J2: PORT B; 6502 GPIO Connector
J3: KEYPAD HELPER; 6502 GPIO Connector
R1: R; R_Axial_DIN0204_L3.6mm_D1.6mm_P5.08mm_Horizontal
U2: LCD-16X2; PARTREV N/A
VR1: 10k; 3386F-1-103LF

Connections:
CA1: J1.11, J3.11
CA2: J1.12, J3.12
E: J1.3, U2.6 (E)
GND: J1.2, J2.2, J3.2, R1.2, U2.1 (VSS), U2.16 (K), VR1.1
unnamed: R1.1, U2.3 (VO), VR1.2
PA0: J1.4, J3.4
PA1: J1.6, J3.6
PA2: J1.8, J3.8
PA3: J1.10, J3.10
PA4: J1.9, J3.9
PB0: J2.4, U2.7 (DB0)
PB1: J2.6, U2.8 (DB1)
PB2: J2.8, U2.9 (DB2)
PB3: J2.10, U2.10 (DB3)
PB4: J2.9, U2.11 (DB4)
PB5: J2.7, U2.12 (DB5)
PB6: J2.5, U2.13 (DB6)
PB7: J2.3, U2.14 (DB7)
RS: J1.7, U2.4 (RS)
R/W: J1.5, U2.5 (R/W)
VCC: J1.1, J2.1, J3.1, U2.2 (VDD), U2.15 (A)

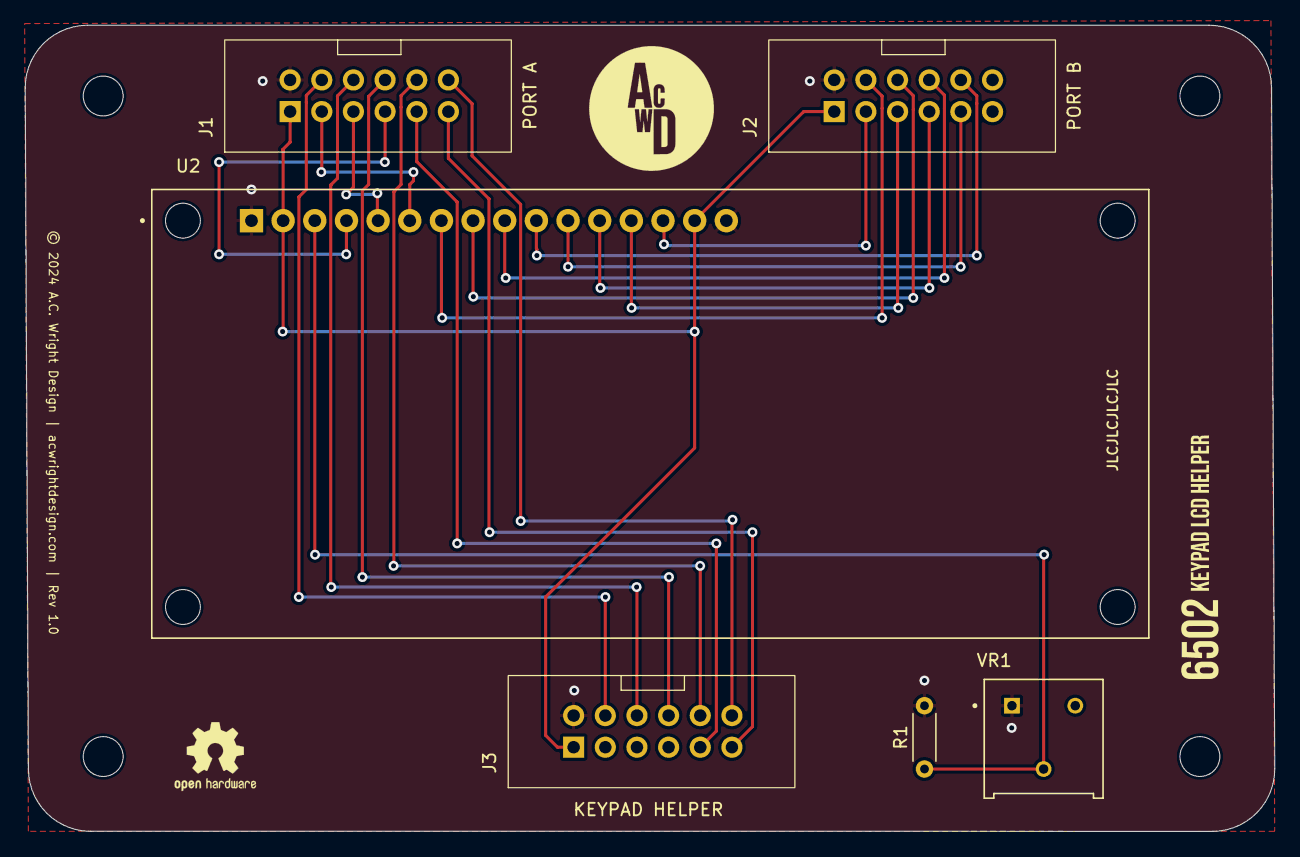
[picture p215: board Keypad LCD Helper.kicad_pcb from above]

Board: 2 copper layers, 100.3 x 64.7 mm, 10 parts (0 on the bottom side), 21 nets.

Other parts of the board:
H1, H2, H3, H4: MountingHole; MountingHole_3.2mm_M3
