acwright/6502/Hardware/GPIO Card/Rev 1.0/GPIO Card.kicad_pcb

## KiCad design Hardware/GPIO Card/Rev 1.0/GPIO Card.kicad_pcb (2025-10-14)

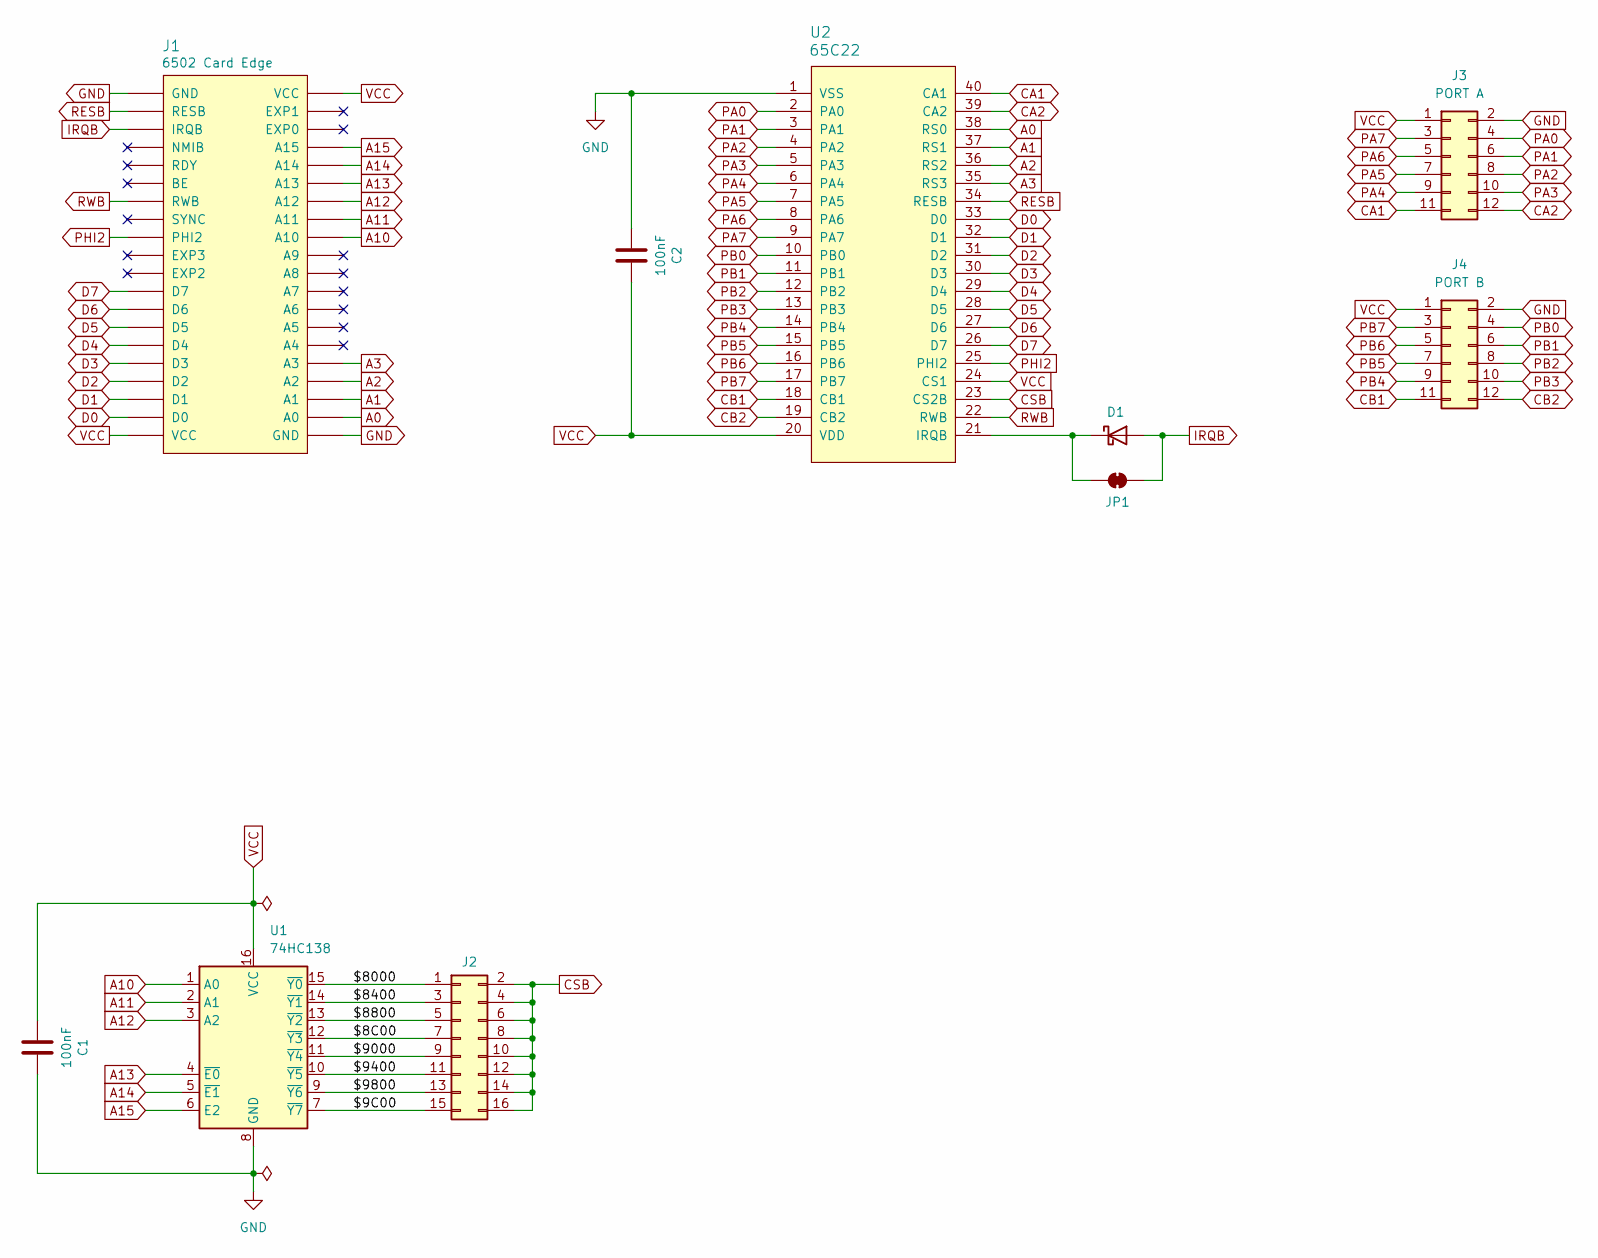
[picture p218: schematic GPIO Card.kicad_sch, 6502 GPIO Card]

Parts:
C1, C2: 100nF; C_0805_2012Metric; LCSC C49678
D1: D_Schottky; D_DO-35_SOD27_P7.62mm_Horizontal
J1: 6502 Card Edge
J2: Conn_02x08_Odd_Even; PinHeader_2x08_P2.54mm_Vertical
J3: PORT A; 6502 GPIO Connector
J4: PORT B; 6502 GPIO Connector
JP1: SolderJumper_2_Bridged; SolderJumper-2_P1.3mm_Bridged_RoundedPad1.0x1.5mm
U1: 74HC138; SOIC-16_3.9x9.9mm_P1.27mm; LCSC C5602
U2: 65C22; DIP-40_W15.24mm_Socket_LongPads

Connections:
/$8C00: J2.7, U1.12 (~Y3)
/$9C00: J2.15, U1.7 (~Y7)
/$8000: J2.1, U1.15 (~Y0)
/$8400: J2.3, U1.14 (~Y1)
/$8800: J2.5, U1.13 (~Y2)
/$9000: J2.9, U1.11 (~Y4)
/$9400: J2.11, U1.10 (~Y5)
/$9800: J2.13, U1.9 (~Y6)
A0: J1.A0, U2.38 (RS0)
A1: J1.A1, U2.37 (RS1)
A2: J1.A2, U2.36 (RS2)
A3: J1.A3, U2.35 (RS3)
A10: J1.A10, U1.1 (A0)
A11: J1.A11, U1.2 (A1)
A12: J1.A12, U1.3 (A2)
A13: J1.A13, U1.4 (~E0)
A14: J1.A14, U1.5 (~E1)
A15: J1.A15, U1.6 (E2)
CA1: J3.11, U2.40 (CA1)
CA2: J3.12, U2.39 (CA2)
CB1: J4.11, U2.18 (CB1)
CB2: J4.12, U2.19 (CB2)
CSB: J2.2, J2.4, J2.6, J2.8, J2.10, J2.12, J2.14, J2.16, U2.23 (CS2B)
D0: J1.D0, U2.33 (D0)
D1: J1.D1, U2.32 (D1)
D2: J1.D2, U2.31 (D2)
D3: J1.D3, U2.30 (D3)
D4: J1.D4, U2.29 (D4)
D5: J1.D5, U2.28 (D5)
D6: J1.D6, U2.27 (D6)
D7: J1.D7, U2.26 (D7)
GND: C1.2, C2.1, J1.GND, J3.2, J4.2, U1.8 (GND), U2.1 (VSS)
IRQB: D1.2 (A), J1.IRQB, JP1.2 (B)
unnamed: D1.1 (K), JP1.1 (A), U2.21 (IRQB)
PA0: J3.4, U2.2 (PA0)
PA1: J3.6, U2.3 (PA1)
PA2: J3.8, U2.4 (PA2)
PA3: J3.10, U2.5 (PA3)
PA4: J3.9, U2.6 (PA4)
PA5: J3.7, U2.7 (PA5)
PA6: J3.5, U2.8 (PA6)
PA7: J3.3, U2.9 (PA7)
PB0: J4.4, U2.10 (PB0)
PB1: J4.6, U2.11 (PB1)
PB2: J4.8, U2.12 (PB2)
PB3: J4.10, U2.13 (PB3)
PB4: J4.9, U2.14 (PB4)
PB5: J4.7, U2.15 (PB5)
PB6: J4.5, U2.16 (PB6)
PB7: J4.3, U2.17 (PB7)
PHI2: J1.PHI2, U2.25 (PHI2)
RESB: J1.RESB, U2.34 (RESB)
RWB: J1.RWB, U2.22 (RWB)
VCC: C1.1, C2.2, J1.VCC, J3.1, J4.1, U1.16 (VCC), U2.20 (VDD), U2.24 (CS1)

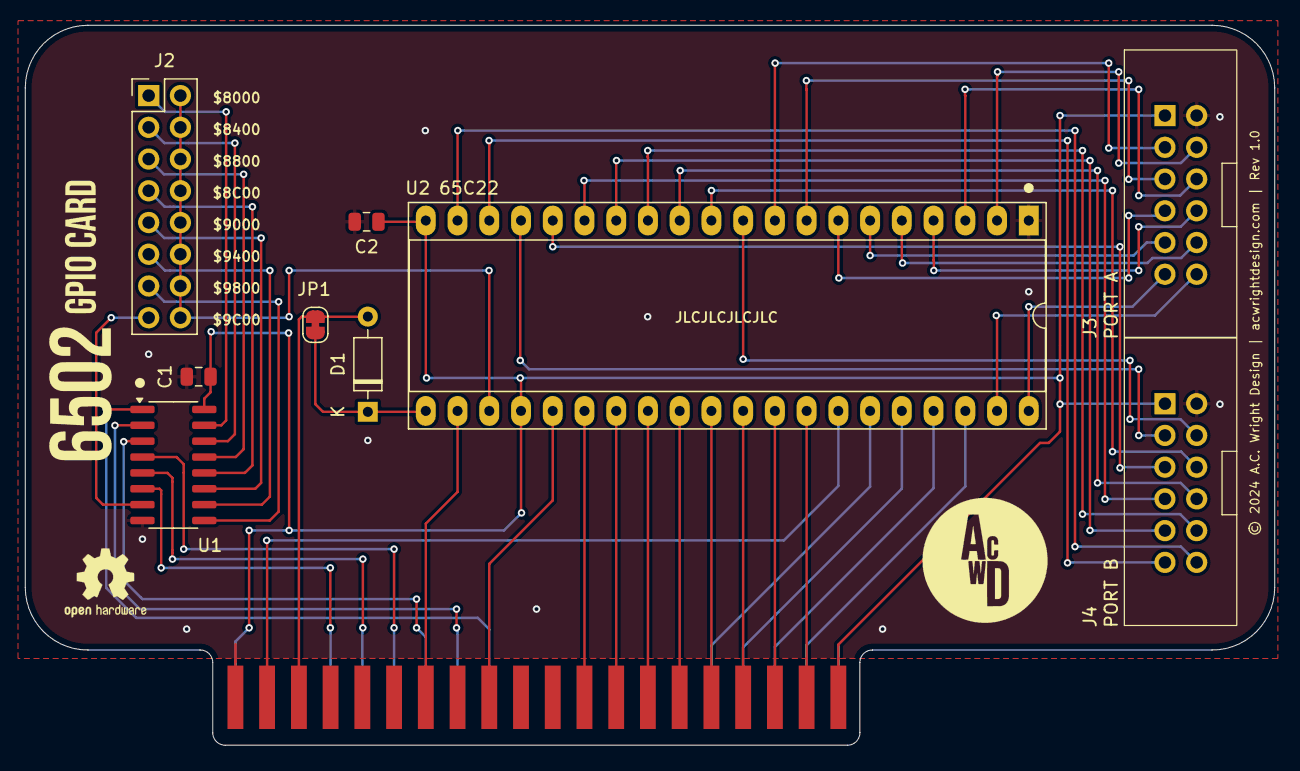
[picture p219: board GPIO Card.kicad_pcb from above]

Board: 2 copper layers, 100.0 x 57.6 mm, 10 parts (0 on the bottom side), 54 nets.
