acwright/6502/Hardware/Keypad Helper/Rev 1.0/Keypad Helper.kicad_pcb

## KiCad design Hardware/Keypad Helper/Rev 1.0/Keypad Helper.kicad_pcb (2025-10-14)

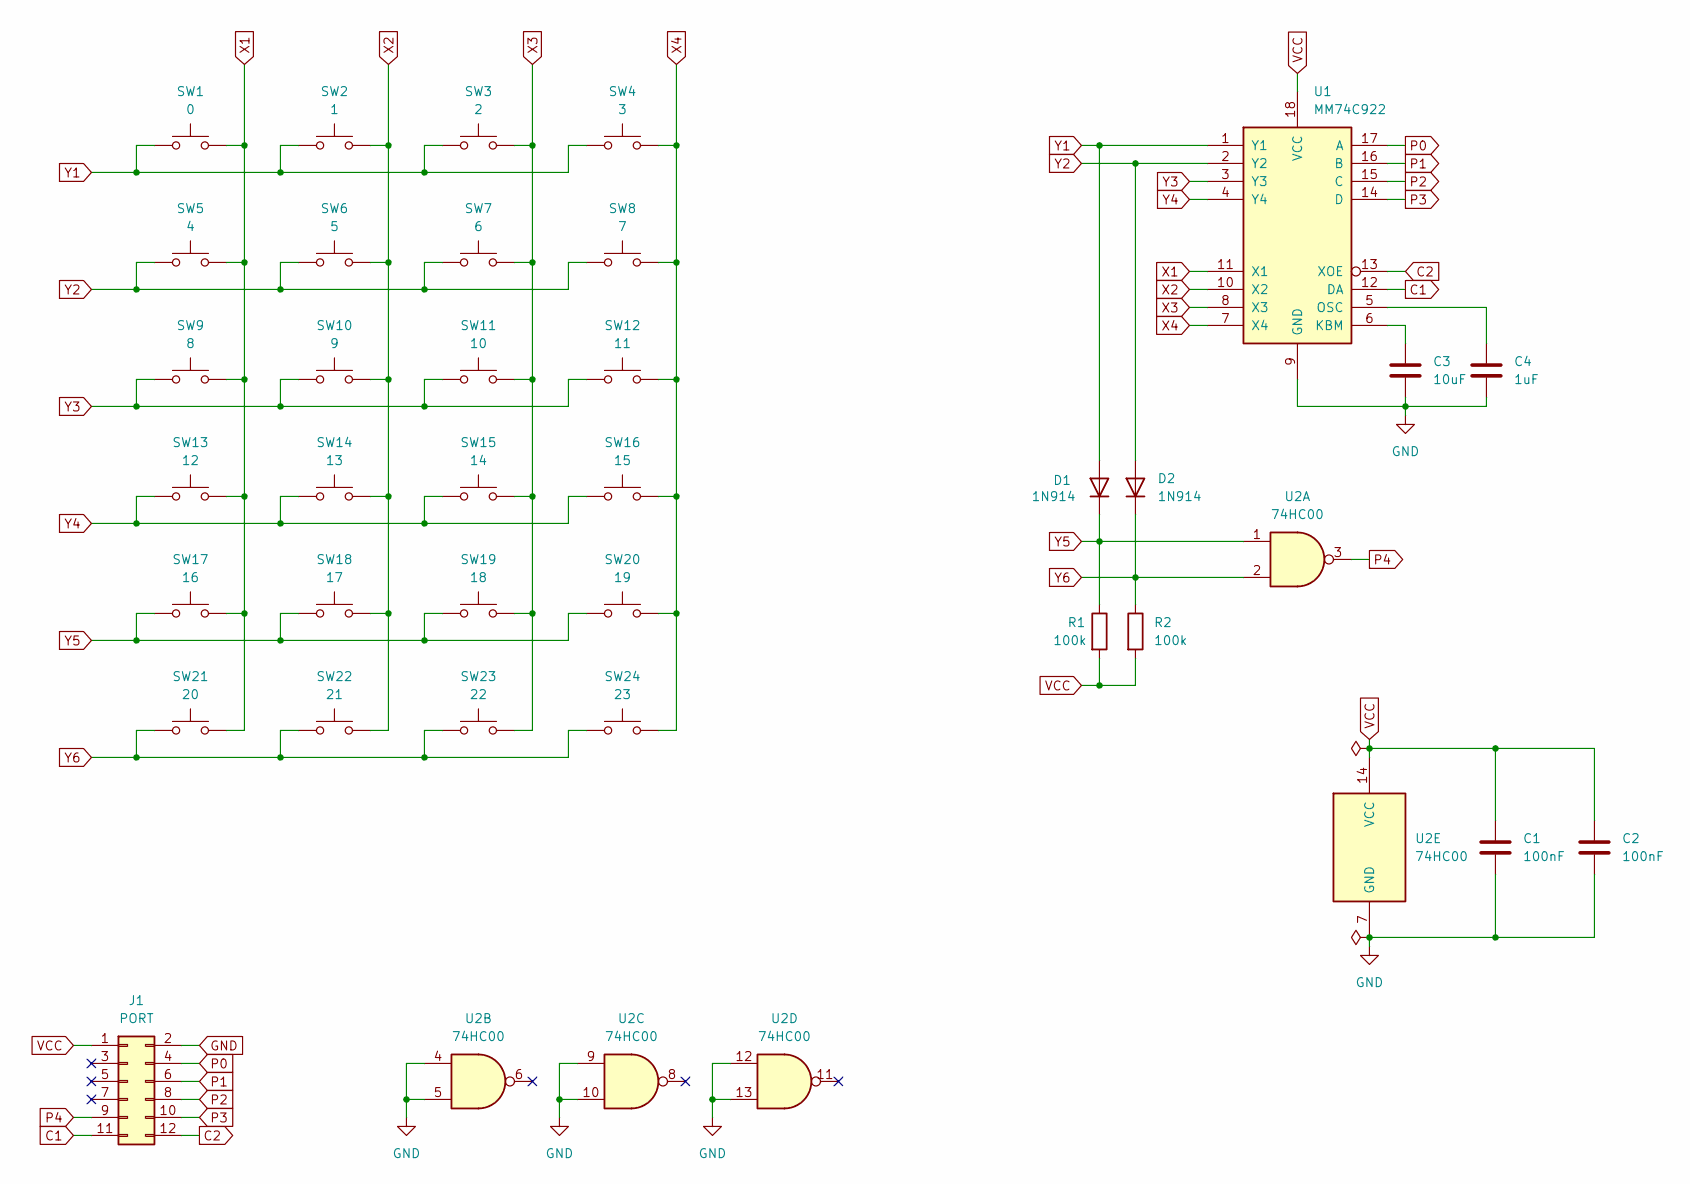
[picture p220: schematic Keypad Helper.kicad_sch, 6502 Keypad Helper]

Parts:
C1, C2: 100nF; C_Disc_D5.0mm_W2.5mm_P5.00mm
C3: 10uF; C_Disc_D5.0mm_W2.5mm_P5.00mm
C4: 1uF; C_Disc_D5.0mm_W2.5mm_P5.00mm
D1, D2: 1N914; D_DO-35_SOD27_P7.62mm_Horizontal
J1: PORT; 6502 GPIO Connector
R1, R2: 100k; R_Axial_DIN0204_L3.6mm_D1.6mm_P5.08mm_Horizontal
SW1: 0; SW_Cherry_MX_1.00u_PCB
SW2: 1; SW_Cherry_MX_1.00u_PCB
SW3: 2; SW_Cherry_MX_1.00u_PCB
SW4: 3; SW_Cherry_MX_1.00u_PCB
SW5: 4; SW_Cherry_MX_1.00u_PCB
SW6: 5; SW_Cherry_MX_1.00u_PCB
SW7: 6; SW_Cherry_MX_1.00u_PCB
SW8: 7; SW_Cherry_MX_1.00u_PCB
SW9: 8; SW_Cherry_MX_1.00u_PCB
SW10: 9; SW_Cherry_MX_1.00u_PCB
SW11: 10; SW_Cherry_MX_1.00u_PCB
SW12: 11; SW_Cherry_MX_1.00u_PCB
SW13: 12; SW_Cherry_MX_1.00u_PCB
SW14: 13; SW_Cherry_MX_1.00u_PCB
SW15: 14; SW_Cherry_MX_1.00u_PCB
SW16: 15; SW_Cherry_MX_1.00u_PCB
SW17: 16; SW_Cherry_MX_1.00u_PCB
SW18: 17; SW_Cherry_MX_1.00u_PCB
SW19: 18; SW_Cherry_MX_1.00u_PCB
SW20: 19; SW_Cherry_MX_1.00u_PCB
SW21: 20; SW_Cherry_MX_1.00u_PCB
SW22: 21; SW_Cherry_MX_1.00u_PCB
SW23: 22; SW_Cherry_MX_1.00u_PCB
SW24: 23; SW_Cherry_MX_1.00u_PCB
U1: MM74C922; DIP-18_W7.62mm_Socket_LongPads
U2: 74HC00; DIP-14_W7.62mm_Socket_LongPads

Connections:
C1: J1.11, U1.12 (DA)
C2: J1.12, U1.13 (XOE)
GND: C1.2, C2.2, C3.2, C4.2, J1.2, U1.9 (GND), U2.4, U2.5, U2.7 (GND), U2.9, U2.10, U2.12, U2.13
unnamed: C3.1, U1.6 (KBM)
unnamed: C4.1, U1.5 (OSC)
P0: J1.4, U1.17 (A)
P1: J1.6, U1.16 (B)
P2: J1.8, U1.15 (C)
P3: J1.10, U1.14 (D)
P4: J1.9, U2.3
VCC: C1.1, C2.1, J1.1, R1.2, R2.2, U1.18 (VCC), U2.14 (VCC)
X1: SW1.2, SW5.2, SW9.2, SW13.2, SW17.2, SW21.2, U1.11 (X1)
X2: SW2.2, SW6.2, SW10.2, SW14.2, SW18.2, SW22.2, U1.10 (X2)
X3: SW3.2, SW7.2, SW11.2, SW15.2, SW19.2, SW23.2, U1.8 (X3)
X4: SW4.2, SW8.2, SW12.2, SW16.2, SW20.2, SW24.2, U1.7 (X4)
Y1: D1.2 (A), SW1.1, SW2.1, SW3.1, SW4.1, U1.1 (Y1)
Y2: D2.2 (A), SW5.1, SW6.1, SW7.1, SW8.1, U1.2 (Y2)
Y3: SW9.1, SW10.1, SW11.1, SW12.1, U1.3 (Y3)
Y4: SW13.1, SW14.1, SW15.1, SW16.1, U1.4 (Y4)
Y5: D1.1 (K), R1.1, SW17.1, SW18.1, SW19.1, SW20.1, U2.1
Y6: D2.1 (K), R2.1, SW21.1, SW22.1, SW23.1, SW24.1, U2.2

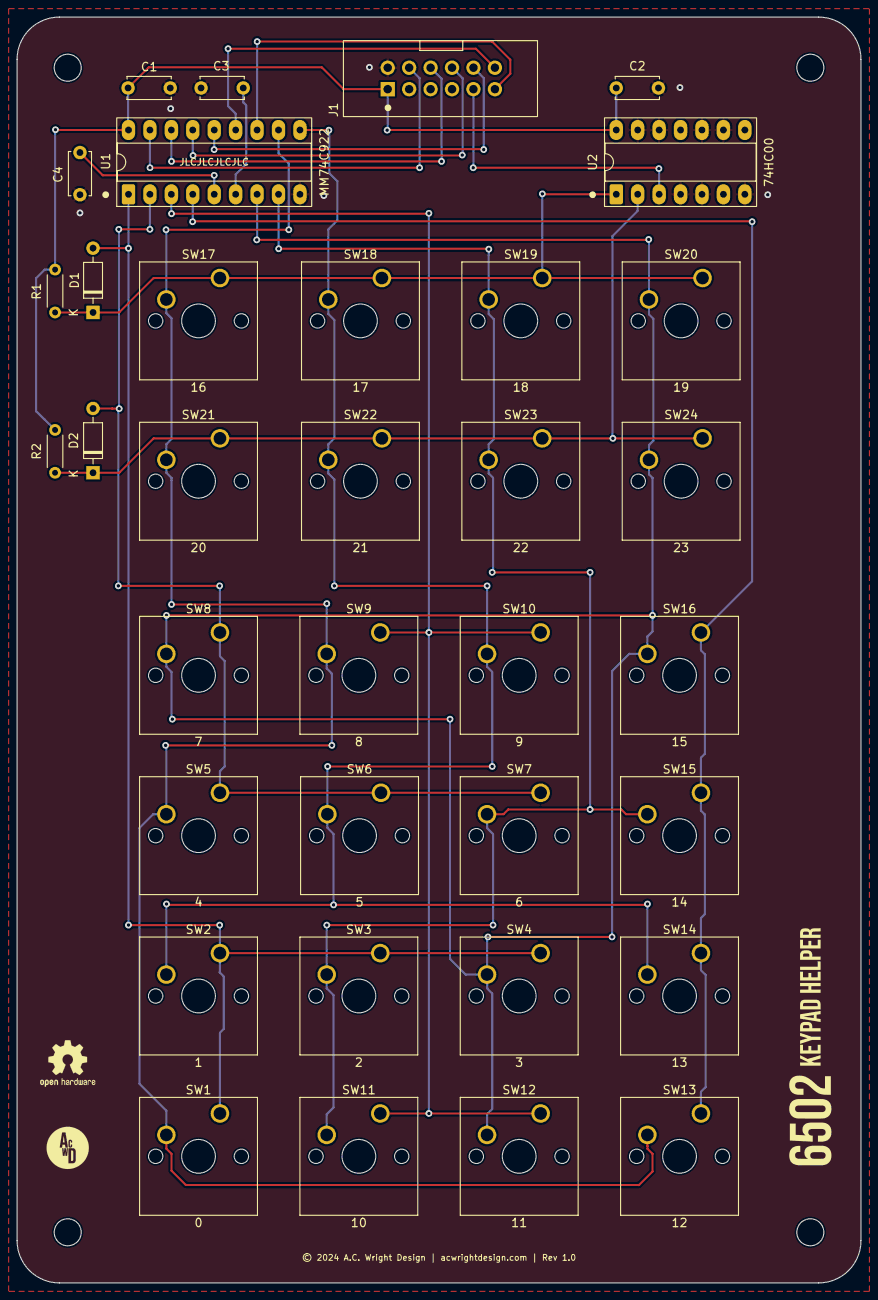
[picture p221: board Keypad Helper.kicad_pcb from above]

Board: 2 copper layers, 100.0 x 150.0 mm, 39 parts (0 on the bottom side), 21 nets.

Other parts of the board:
H1, H2, H3, H4: MountingHole; MountingHole_3.2mm_M3
