acwright/6502/Hardware/LCD Card/Rev 1.0/LCD Card.kicad_pcb

## KiCad design Hardware/LCD Card/Rev 1.0/LCD Card.kicad_pcb (2025-10-14)

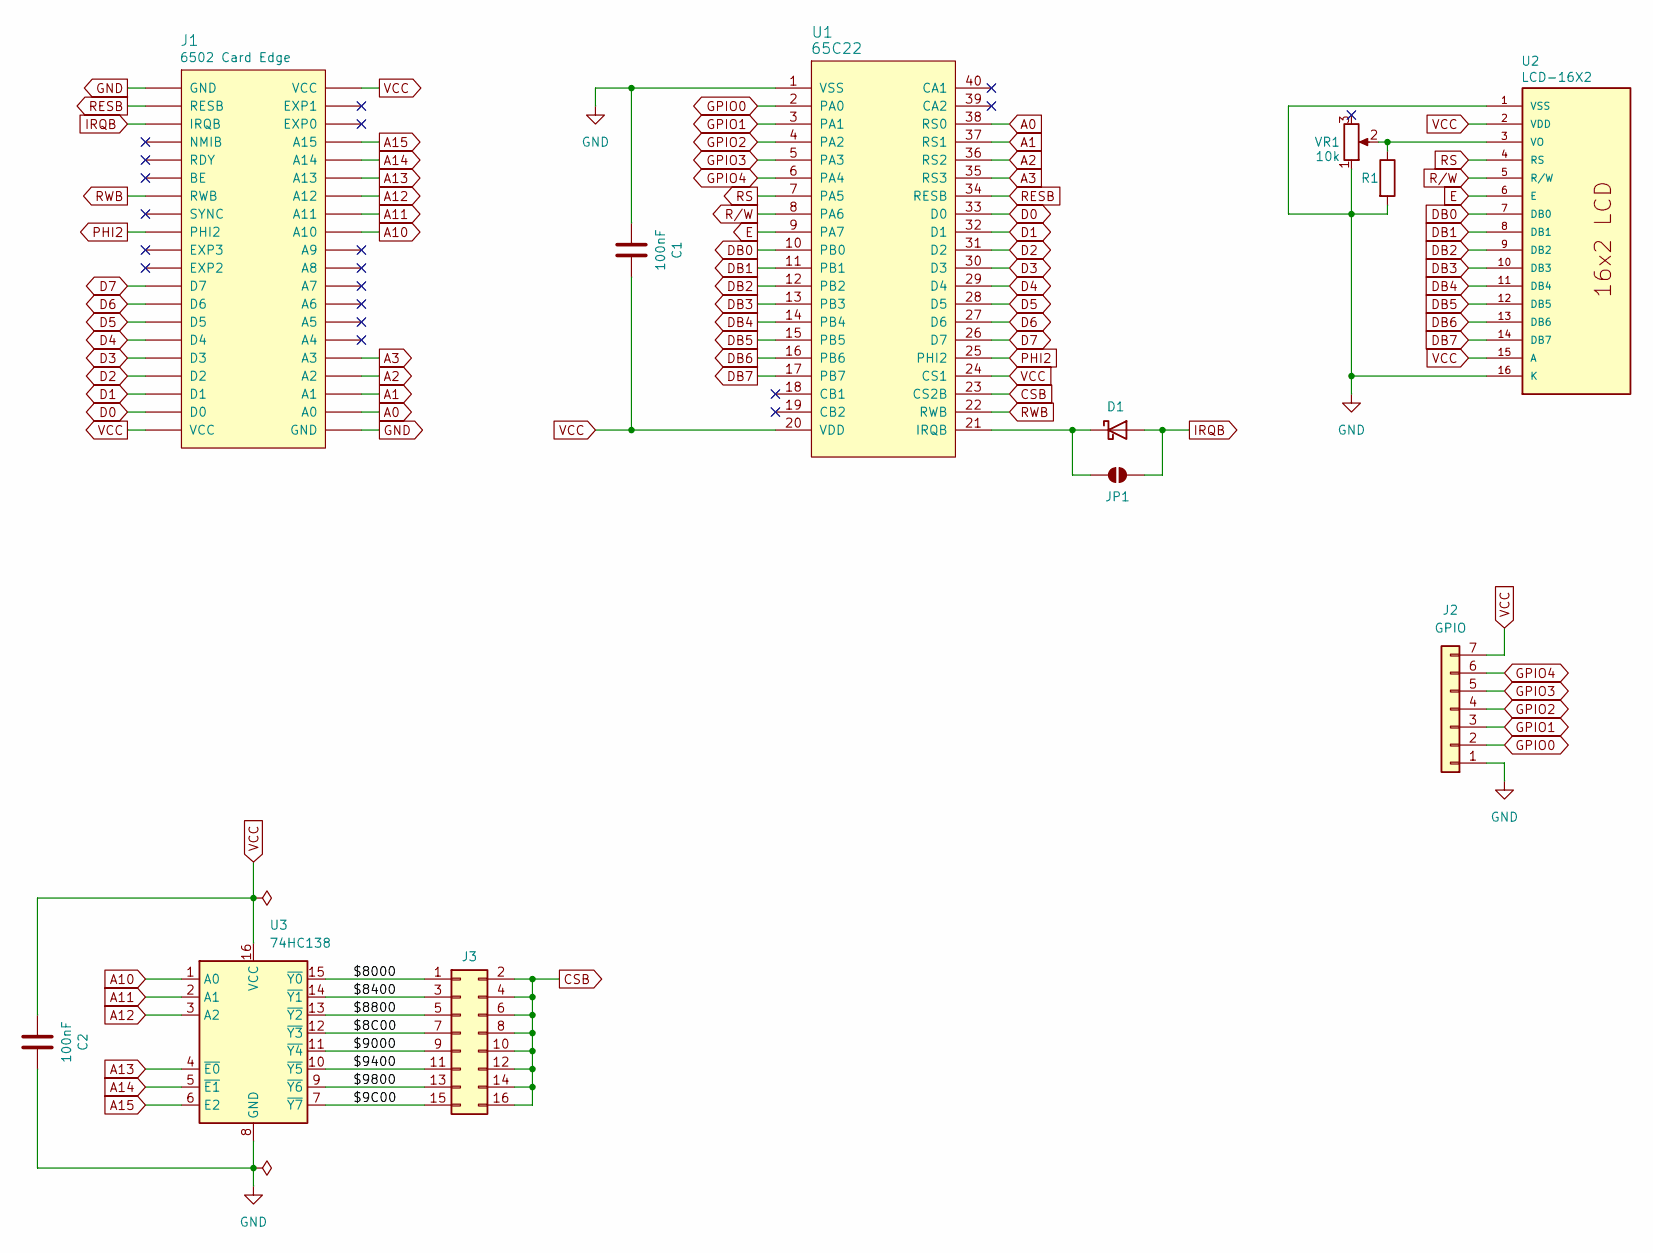
[picture p227: schematic LCD Card.kicad_sch, 6502 LCD Card]

Parts:
C1, C2: 100nF; C_0805_2012Metric; LCSC C49678
D1: D_Schottky; D_DO-35_SOD27_P7.62mm_Horizontal
J1: 6502 Card Edge
J2: GPIO; PinHeader_1x07_P2.54mm_Horizontal
J3: Conn_02x08_Odd_Even; PinHeader_2x08_P2.54mm_Vertical
JP1: SolderJumper_2_Bridged; SolderJumper-2_P1.3mm_Open_RoundedPad1.0x1.5mm
R1: R; R_Axial_DIN0204_L3.6mm_D1.6mm_P5.08mm_Horizontal
U1: 65C22; DIP-40_W15.24mm_Socket_LongPads
U2: LCD-16X2; PARTREV N/A
U3: 74HC138; SOIC-16_3.9x9.9mm_P1.27mm; LCSC C5602
VR1: 10k; 3386F-1-103LF

Connections:
/$8C00: J3.7, U3.12 (~Y3)
/$9C00: J3.15, U3.7 (~Y7)
/$8000: J3.1, U3.15 (~Y0)
/$8400: J3.3, U3.14 (~Y1)
/$8800: J3.5, U3.13 (~Y2)
/$9000: J3.9, U3.11 (~Y4)
/$9400: J3.11, U3.10 (~Y5)
/$9800: J3.13, U3.9 (~Y6)
A0: J1.A0, U1.38 (RS0)
A1: J1.A1, U1.37 (RS1)
A2: J1.A2, U1.36 (RS2)
A3: J1.A3, U1.35 (RS3)
A10: J1.A10, U3.1 (A0)
A11: J1.A11, U3.2 (A1)
A12: J1.A12, U3.3 (A2)
A13: J1.A13, U3.4 (~E0)
A14: J1.A14, U3.5 (~E1)
A15: J1.A15, U3.6 (E2)
CSB: J3.2, J3.4, J3.6, J3.8, J3.10, J3.12, J3.14, J3.16, U1.23 (CS2B)
D0: J1.D0, U1.33 (D0)
D1: J1.D1, U1.32 (D1)
D2: J1.D2, U1.31 (D2)
D3: J1.D3, U1.30 (D3)
D4: J1.D4, U1.29 (D4)
D5: J1.D5, U1.28 (D5)
D6: J1.D6, U1.27 (D6)
D7: J1.D7, U1.26 (D7)
DB0: U1.10 (PB0), U2.7 (DB0)
DB1: U1.11 (PB1), U2.8 (DB1)
DB2: U1.12 (PB2), U2.9 (DB2)
DB3: U1.13 (PB3), U2.10 (DB3)
DB4: U1.14 (PB4), U2.11 (DB4)
DB5: U1.15 (PB5), U2.12 (DB5)
DB6: U1.16 (PB6), U2.13 (DB6)
DB7: U1.17 (PB7), U2.14 (DB7)
E: U1.9 (PA7), U2.6 (E)
GND: C1.1, C2.2, J1.GND, J2.1, R1.2, U1.1 (VSS), U2.1 (VSS), U2.16 (K), U3.8 (GND), VR1.1
GPIO0: J2.2, U1.2 (PA0)
GPIO1: J2.3, U1.3 (PA1)
GPIO2: J2.4, U1.4 (PA2)
GPIO3: J2.5, U1.5 (PA3)
GPIO4: J2.6, U1.6 (PA4)
IRQB: D1.2 (A), J1.IRQB, JP1.2 (B)
unnamed: D1.1 (K), JP1.1 (A), U1.21 (IRQB)
unnamed: R1.1, U2.3 (VO), VR1.2
PHI2: J1.PHI2, U1.25 (PHI2)
RESB: J1.RESB, U1.34 (RESB)
RS: U1.7 (PA5), U2.4 (RS)
RWB: J1.RWB, U1.22 (RWB)
R/W: U1.8 (PA6), U2.5 (R/W)
VCC: C1.2, C2.1, J1.VCC, J2.7, U1.20 (VDD), U1.24 (CS1), U2.2 (VDD), U2.15 (A), U3.16 (VCC)

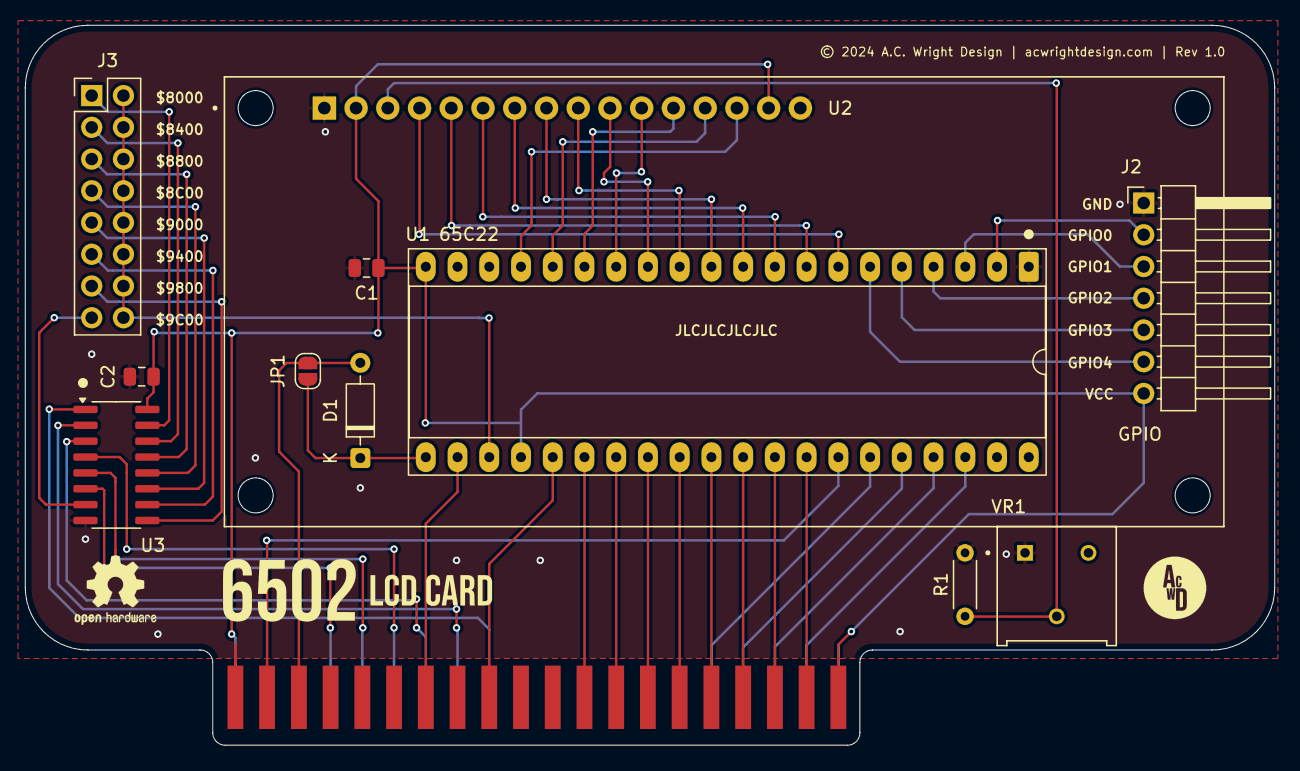
[picture p228: board LCD Card.kicad_pcb from above]

Board: 2 copper layers, 100.0 x 57.6 mm, 12 parts (0 on the bottom side), 51 nets.
