acwright/6502/Hardware/Serial Card Pro/Rev 1.0/Serial Card Pro.kicad_pcb

## KiCad design Hardware/Serial Card Pro/Rev 1.0/Serial Card Pro.kicad_pcb (2025-10-14)

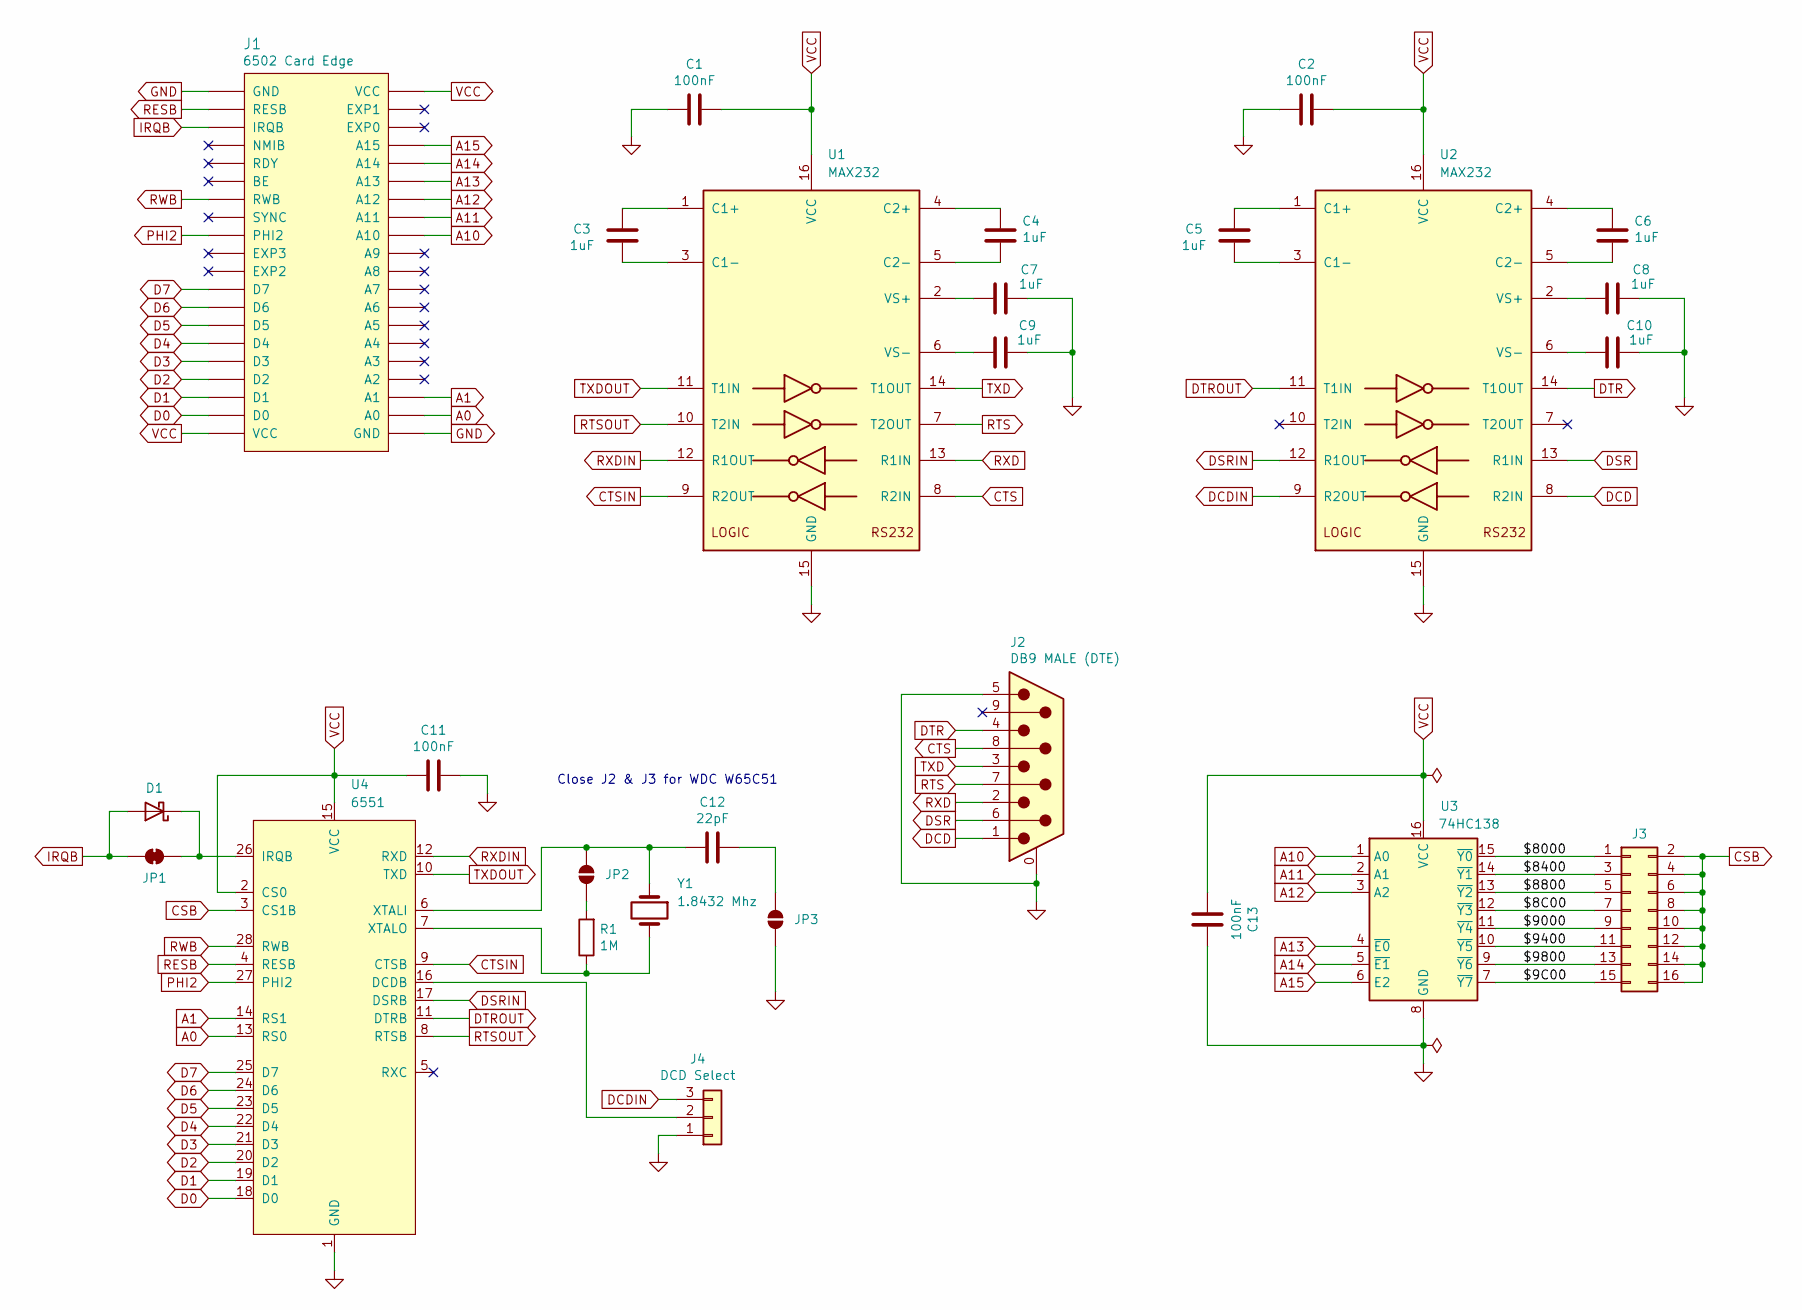
[picture p229: schematic Serial Card Pro.kicad_sch, 6502 Serial Card Pro]

Parts:
C1, C2, C11, C13: 100nF; C_0805_2012Metric; LCSC C49678
C3, C4, C5, C6, C7, C8, C9, C10: 1uF; C_0805_2012Metric; LCSC C28323
C12: 22pF; C_0805_2012Metric; LCSC C1804
D1: D_Schottky; D_DO-35_SOD27_P7.62mm_Horizontal
J1: 6502 Card Edge
J2: DB9 MALE (DTE); DSUB-9_Pins_Horizontal_P2.77x2.84mm_EdgePinOffset7.70mm_Hou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; MPN D09P33E4GX00LF; Digikey 609-1481-ND
J3: Conn_02x08_Odd_Even; PinHeader_2x08_P2.54mm_Vertical
J4: DCD Select; PinHeader_1x03_P2.54mm_Vertical
JP1: SolderJumper_2_Bridged; SolderJumper-2_P1.3mm_Bridged_RoundedPad1.0x1.5mm
JP2, JP3: SolderJumper_2_Open; SolderJumper-2_P1.3mm_Open_RoundedPad1.0x1.5mm
R1: 1M; R_0805_2012Metric; LCSC C103906
U1, U2: MAX232; MAX232D; LCSC C59824
U3: 74HC138; SOIC-16_3.9x9.9mm_P1.27mm; LCSC C5602
U4: 6551; DIP-28_W15.24mm_Socket_LongPads
Y1: 1.8432 Mhz; Crystal_HC49-U_Vertical

Connections:
/$8C00: J3.7, U3.12 (~Y3)
/$9C00: J3.15, U3.7 (~Y7)
/$8000: J3.1, U3.15 (~Y0)
/$8400: J3.3, U3.14 (~Y1)
/$8800: J3.5, U3.13 (~Y2)
/$9000: J3.9, U3.11 (~Y4)
/$9400: J3.11, U3.10 (~Y5)
/$9800: J3.13, U3.9 (~Y6)
A0: J1.A0, U4.13 (RS0)
A1: J1.A1, U4.14 (RS1)
A10: J1.A10, U3.1 (A0)
A11: J1.A11, U3.2 (A1)
A12: J1.A12, U3.3 (A2)
A13: J1.A13, U3.4 (~E0)
A14: J1.A14, U3.5 (~E1)
A15: J1.A15, U3.6 (E2)
CSB: J3.2, J3.4, J3.6, J3.8, J3.10, J3.12, J3.14, J3.16, U4.3 (CS1B)
CTS: J2.8, U1.8 (R2IN)
CTSIN: U1.9 (R2OUT), U4.9 (CTSB)
D0: J1.D0, U4.18 (D0)
D1: J1.D1, U4.19 (D1)
D2: J1.D2, U4.20 (D2)
D3: J1.D3, U4.21 (D3)
D4: J1.D4, U4.22 (D4)
D5: J1.D5, U4.23 (D5)
D6: J1.D6, U4.24 (D6)
D7: J1.D7, U4.25 (D7)
DCD: J2.1, U2.8 (R2IN)
DCDIN: J4.3, U2.9 (R2OUT)
DSR: J2.6, U2.13 (R1IN)
DSRIN: U2.12 (R1OUT), U4.17 (DSRB)
DTR: J2.4, U2.14 (T1OUT)
DTROUT: U2.11 (T1IN), U4.11 (DTRB)
GND: C1.1, C2.1, C7.2, C8.2, C9.2, C10.2, C11.2, C13.2, J1.GND, J2.0 (PAD), J2.5, J4.1, JP3.1 (A), U1.15 (GND), U2.15 (GND), U3.8 (GND), U4.1 (GND)
IRQB: D1.2 (A), J1.IRQB, JP1.1 (A)
unnamed: D1.1 (K), JP1.2 (B), U4.26 (IRQB)
unnamed: J4.2, U4.16 (DCDB)
unnamed: JP2.1 (A), R1.2
unnamed: C12.2, JP2.2 (B), U4.6 (XTALI), Y1.1
unnamed: C12.1, JP3.2 (B)
unnamed: C3.1, U1.1 (C1+)
unnamed: C3.2, U1.3 (C1-)
unnamed: C4.1, U1.4 (C2+)
unnamed: C4.2, U1.5 (C2-)
unnamed: C7.1, U1.2 (VS+)
unnamed: C9.1, U1.6 (VS-)
unnamed: C5.1, U2.1 (C1+)
unnamed: C5.2, U2.3 (C1-)
unnamed: C6.1, U2.4 (C2+)
unnamed: C6.2, U2.5 (C2-)
unnamed: C8.1, U2.2 (VS+)
unnamed: C10.1, U2.6 (VS-)
unnamed: R1.1, U4.7 (XTALO), Y1.2
PHI2: J1.PHI2, U4.27 (PHI2)
RESB: J1.RESB, U4.4 (RESB)
RTS: J2.7, U1.7 (T2OUT)
RTSOUT: U1.10 (T2IN), U4.8 (RTSB)
RWB: J1.RWB, U4.28 (RWB)
RXD: J2.2, U1.13 (R1IN)
RXDIN: U1.12 (R1OUT), U4.12 (RXD)
TXD: J2.3, U1.14 (T1OUT)
TXDOUT: U1.11 (T1IN), U4.10 (TXD)
VCC: C1.2, C2.2, C11.1, C13.1, J1.VCC, U1.16 (VCC), U2.16 (VCC), U3.16 (VCC), U4.2 (CS0), U4.15 (VCC)

Notes on the sheet:
Close J2 & J3 for WDC W65C51

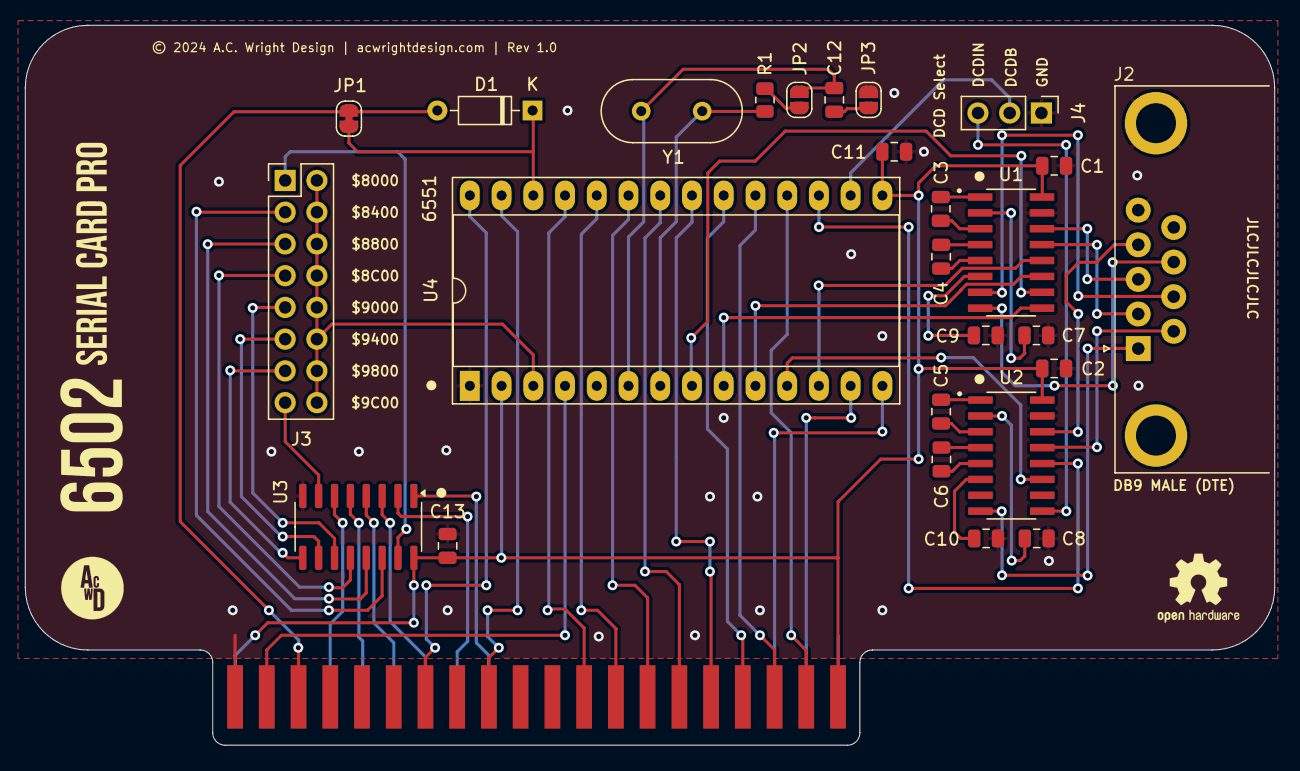
[picture p230: board Serial Card Pro.kicad_pcb from above]

Board: 2 copper layers, 100.0 x 57.6 mm, 27 parts (0 on the bottom side), 63 nets.
