acwright/6502/Hardware/Backplane/Rev 1.0/Backplane.kicad_pcb

## KiCad design Hardware/Backplane/Rev 1.0/Backplane.kicad_pcb (2025-10-14)

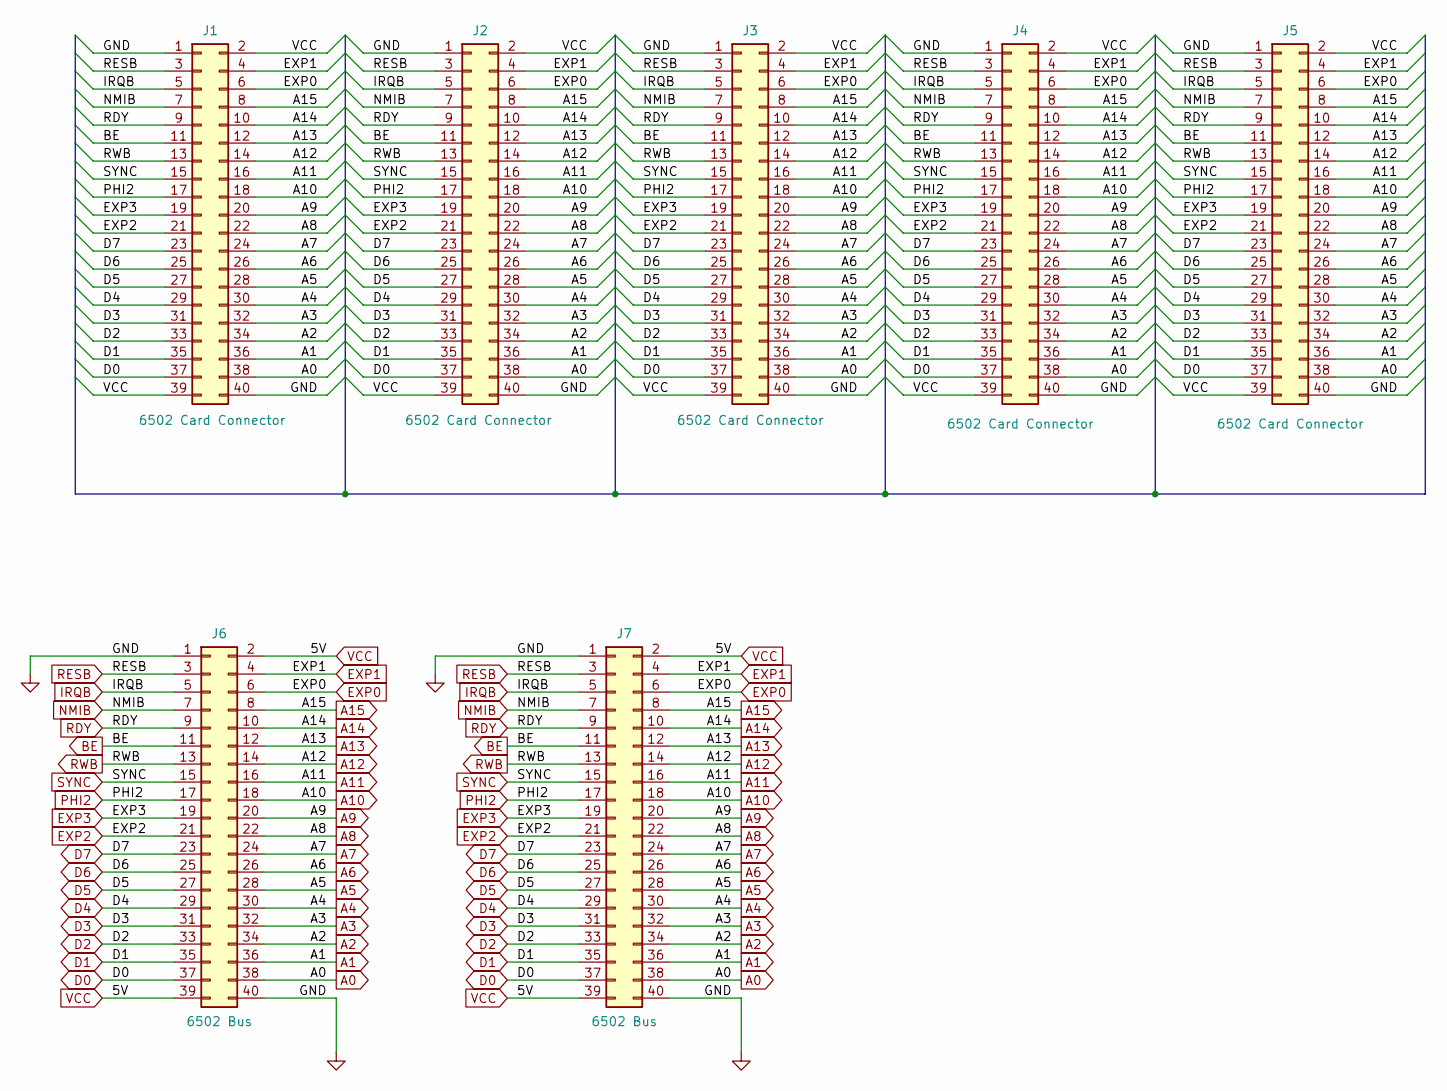
[picture p231: schematic Backplane.kicad_sch, 6502 Backplane]

Parts:
J1, J2, J3, J4, J5: 6502 Card Connector; RHDR40W82P485X254_2X20_5740X93; Mouser 571-5-5530843-4
J6, J7: 6502 Bus; 6502 Bus Connector; Digikey 732-5401-ND

Connections:
A0: J1.38, J2.38, J3.38, J4.38, J5.38, J6.38, J7.38
A1: J1.36, J2.36, J3.36, J4.36, J5.36, J6.36, J7.36
A2: J1.34, J2.34, J3.34, J4.34, J5.34, J6.34, J7.34
A3: J1.32, J2.32, J3.32, J4.32, J5.32, J6.32, J7.32
A4: J1.30, J2.30, J3.30, J4.30, J5.30, J6.30, J7.30
A5: J1.28, J2.28, J3.28, J4.28, J5.28, J6.28, J7.28
A6: J1.26, J2.26, J3.26, J4.26, J5.26, J6.26, J7.26
A7: J1.24, J2.24, J3.24, J4.24, J5.24, J6.24, J7.24
A8: J1.22, J2.22, J3.22, J4.22, J5.22, J6.22, J7.22
A9: J1.20, J2.20, J3.20, J4.20, J5.20, J6.20, J7.20
A10: J1.18, J2.18, J3.18, J4.18, J5.18, J6.18, J7.18
A11: J1.16, J2.16, J3.16, J4.16, J5.16, J6.16, J7.16
A12: J1.14, J2.14, J3.14, J4.14, J5.14, J6.14, J7.14
A13: J1.12, J2.12, J3.12, J4.12, J5.12, J6.12, J7.12
A14: J1.10, J2.10, J3.10, J4.10, J5.10, J6.10, J7.10
A15: J1.8, J2.8, J3.8, J4.8, J5.8, J6.8, J7.8
BE: J1.11, J2.11, J3.11, J4.11, J5.11, J6.11, J7.11
D0: J1.37, J2.37, J3.37, J4.37, J5.37, J6.37, J7.37
D1: J1.35, J2.35, J3.35, J4.35, J5.35, J6.35, J7.35
D2: J1.33, J2.33, J3.33, J4.33, J5.33, J6.33, J7.33
D3: J1.31, J2.31, J3.31, J4.31, J5.31, J6.31, J7.31
D4: J1.29, J2.29, J3.29, J4.29, J5.29, J6.29, J7.29
D5: J1.27, J2.27, J3.27, J4.27, J5.27, J6.27, J7.27
D6: J1.25, J2.25, J3.25, J4.25, J5.25, J6.25, J7.25
D7: J1.23, J2.23, J3.23, J4.23, J5.23, J6.23, J7.23
EXP0: J1.6, J2.6, J3.6, J4.6, J5.6, J6.6, J7.6
EXP1: J1.4, J2.4, J3.4, J4.4, J5.4, J6.4, J7.4
EXP2: J1.21, J2.21, J3.21, J4.21, J5.21, J6.21, J7.21
EXP3: J1.19, J2.19, J3.19, J4.19, J5.19, J6.19, J7.19
GND: J1.1, J1.40, J2.1, J2.40, J3.1, J3.40, J4.1, J4.40, J5.1, J5.40, J6.1, J6.40, J7.1, J7.40
IRQB: J1.5, J2.5, J3.5, J4.5, J5.5, J6.5, J7.5
NMIB: J1.7, J2.7, J3.7, J4.7, J5.7, J6.7, J7.7
PHI2: J1.17, J2.17, J3.17, J4.17, J5.17, J6.17, J7.17
RDY: J1.9, J2.9, J3.9, J4.9, J5.9, J6.9, J7.9
RESB: J1.3, J2.3, J3.3, J4.3, J5.3, J6.3, J7.3
RWB: J1.13, J2.13, J3.13, J4.13, J5.13, J6.13, J7.13
SYNC: J1.15, J2.15, J3.15, J4.15, J5.15, J6.15, J7.15
VCC: J1.2, J1.39, J2.2, J2.39, J3.2, J3.39, J4.2, J4.39, J5.2, J5.39, J6.2, J6.39, J7.2, J7.39

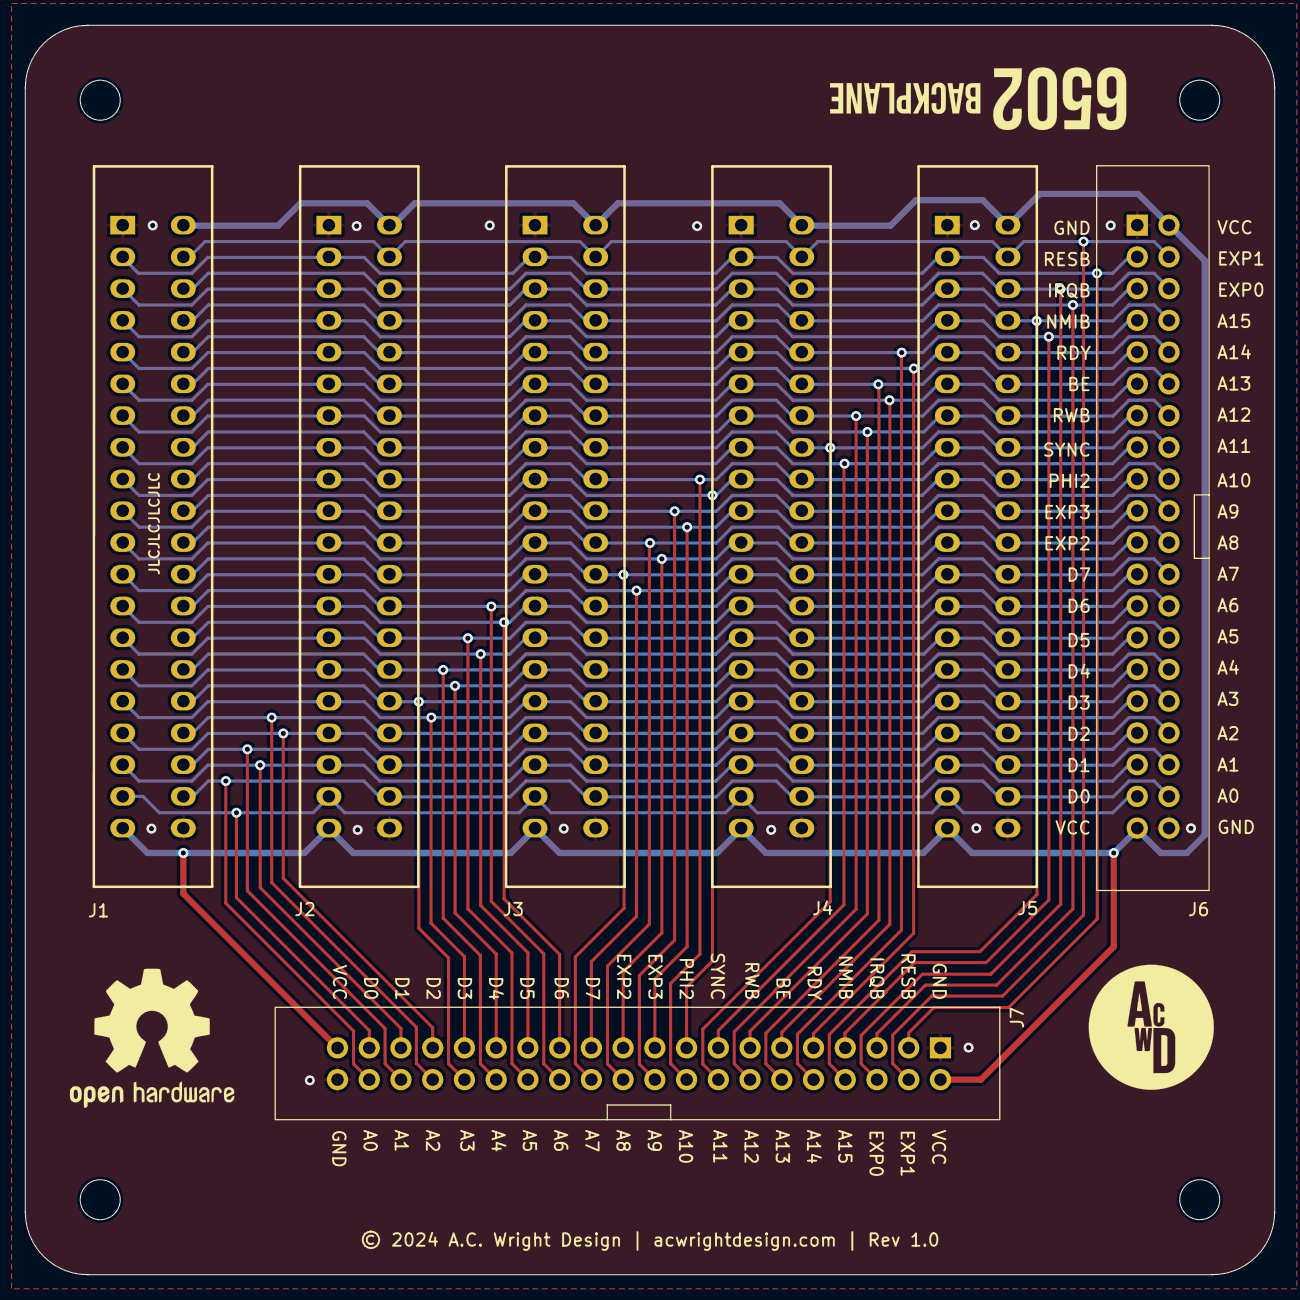
[picture p232: board Backplane.kicad_pcb from above]

Board: 2 copper layers, 100.0 x 100.0 mm, 11 parts (0 on the bottom side), 38 nets.

Other parts of the board:
H1, H2, H3, H4: MountingHole; MountingHole_3.2mm_M3
