acwright/6502/Hardware/Blinkenlights Card/Rev 1.0/Blinkenlights Card.kicad_sch

## KiCad design Hardware/Blinkenlights Card/Rev 1.0/Blinkenlights Card.kicad_sch (2025-09-06)

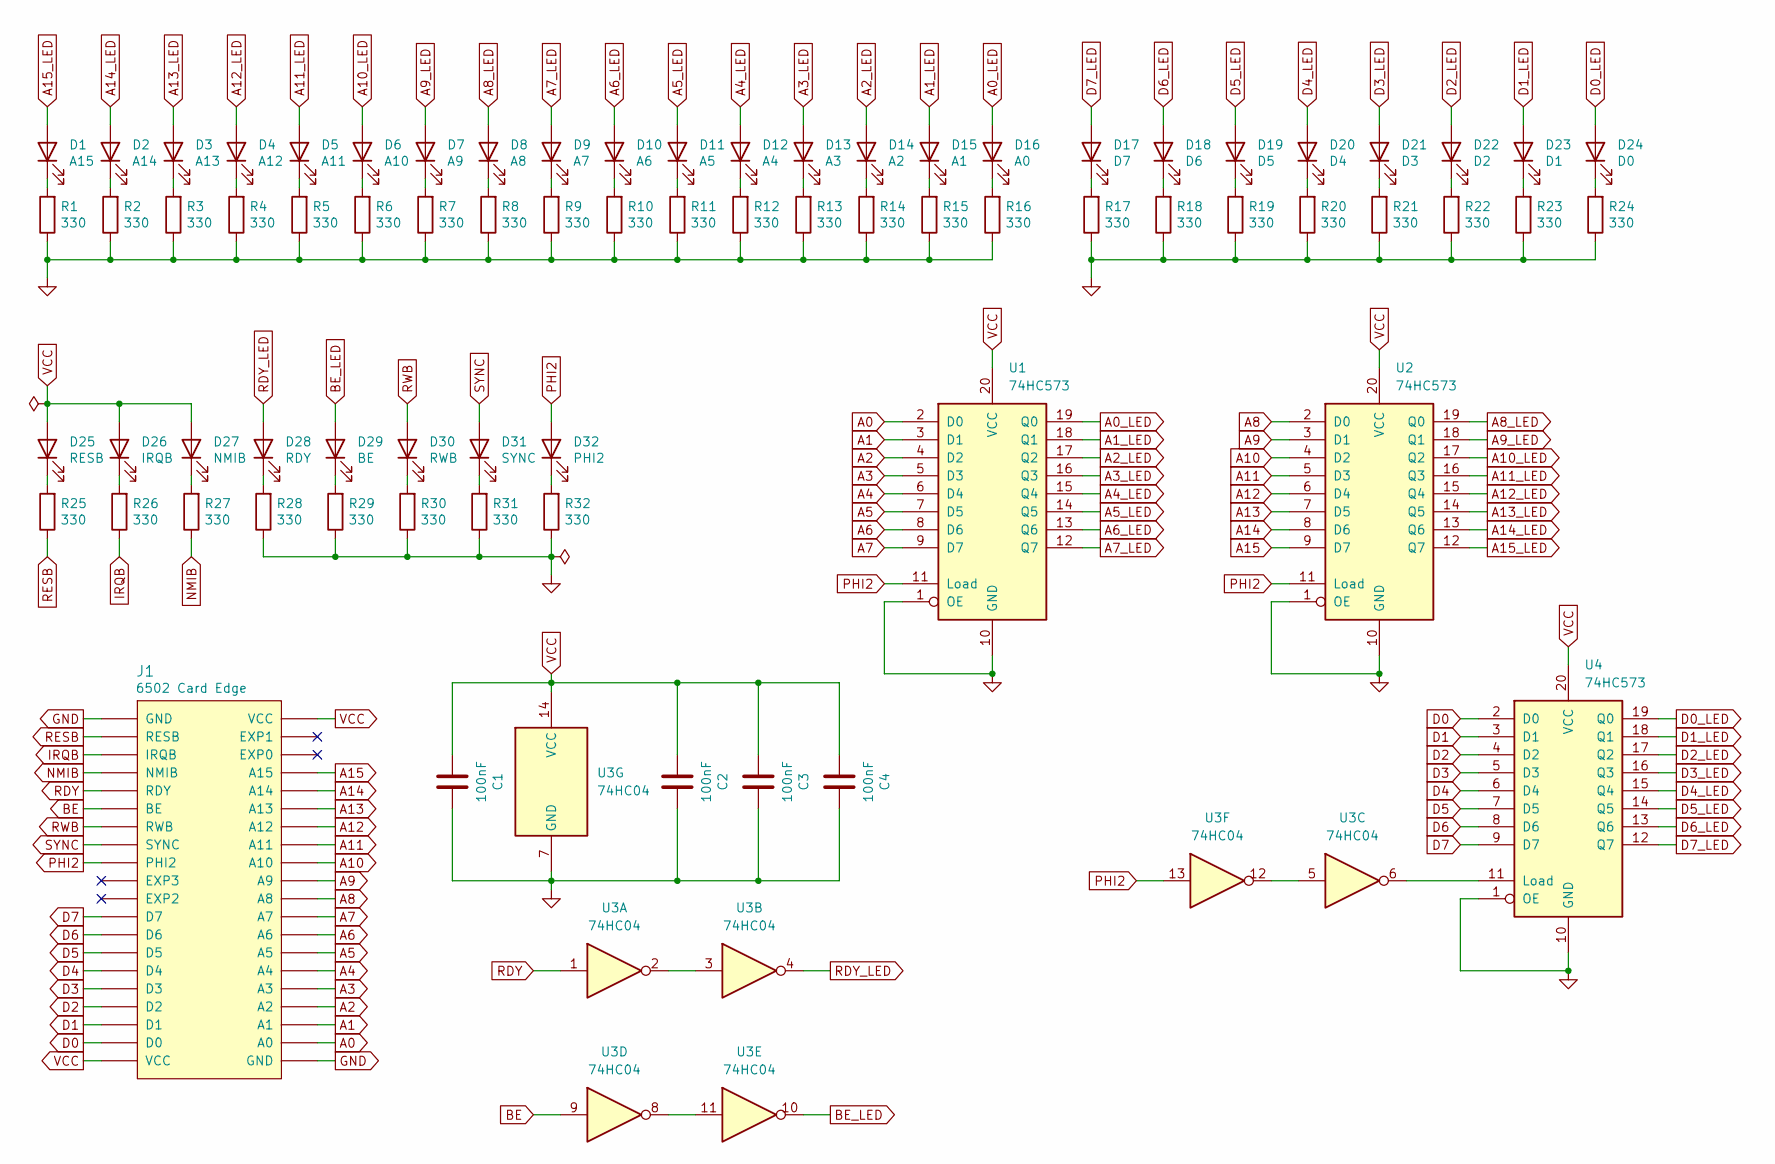
[picture p233: schematic Blinkenlights Card.kicad_sch]

Parts:
C1, C2, C3, C4: 100nF; C_0805_2012Metric; LCSC C49678
D1: A15; LED_0805_2012Metric; LCSC C2297
D2: A14; LED_0805_2012Metric; LCSC C2297
D3: A13; LED_0805_2012Metric; LCSC C2297
D4: A12; LED_0805_2012Metric; LCSC C2297
D5: A11; LED_0805_2012Metric; LCSC C2297
D6: A10; LED_0805_2012Metric; LCSC C2297
D7: A9; LED_0805_2012Metric; LCSC C2297
D8: A8; LED_0805_2012Metric; LCSC C2297
D9: A7; LED_0805_2012Metric; LCSC C2297
D10: A6; LED_0805_2012Metric; LCSC C2297
D11: A5; LED_0805_2012Metric; LCSC C2297
D12: A4; LED_0805_2012Metric; LCSC C2297
D13: A3; LED_0805_2012Metric; LCSC C2297
D14: A2; LED_0805_2012Metric; LCSC C2297
D15: A1; LED_0805_2012Metric; LCSC C2297
D16: A0; LED_0805_2012Metric; LCSC C2297
D17: D7; LED_0805_2012Metric; LCSC C2297
D18: D6; LED_0805_2012Metric; LCSC C2297
D19: D5; LED_0805_2012Metric; LCSC C2297
D20: D4; LED_0805_2012Metric; LCSC C2297
D21: D3; LED_0805_2012Metric; LCSC C2297
D22: D2; LED_0805_2012Metric; LCSC C2297
D23: D1; LED_0805_2012Metric; LCSC C2297
D24: D0; LED_0805_2012Metric; LCSC C2297
D25: RESB; LED_0805_2012Metric; LCSC C2297
D26: IRQB; LED_0805_2012Metric; LCSC C2295
D27: NMIB; LED_0805_2012Metric; LCSC C2295
D28: RDY; LED_0805_2012Metric; LCSC C2296
D29: BE; LED_0805_2012Metric; LCSC C2296
D30: RWB; LED_0805_2012Metric; LCSC C2296
D31: SYNC; LED_0805_2012Metric; LCSC C2293
D32: PHI2; LED_0805_2012Metric; LCSC C2293
J1: 6502 Card Edge
R1, R2, R3, R4, R5, R6, R7, R8, R9, R10, R11, R12, R13, R14, R15, R16, R17, R18, R19, R20, R21, R22, R23, R24, R25, R26, R27, R28, R29, R30, R31, R32: 330; R_0805_2012Metric; LCSC C17630
U1, U2, U4: 74HC573; SOIC-20W_7.5x12.8mm_P1.27mm; LCSC C5608
U3: 74HC04; SOIC-14_3.9x8.7mm_P1.27mm; LCSC C5590

Connections:
A0: J1.A0, U1.2 (D0)
A0_LED: D16.2 (A), U1.19 (Q0)
A1: J1.A1, U1.3 (D1)
A1_LED: D15.2 (A), U1.18 (Q1)
A2: J1.A2, U1.4 (D2)
A2_LED: D14.2 (A), U1.17 (Q2)
A3: J1.A3, U1.5 (D3)
A3_LED: D13.2 (A), U1.16 (Q3)
A4: J1.A4, U1.6 (D4)
A4_LED: D12.2 (A), U1.15 (Q4)
A5: J1.A5, U1.7 (D5)
A5_LED: D11.2 (A), U1.14 (Q5)
A6: J1.A6, U1.8 (D6)
A6_LED: D10.2 (A), U1.13 (Q6)
A7: J1.A7, U1.9 (D7)
A7_LED: D9.2 (A), U1.12 (Q7)
A8: J1.A8, U2.2 (D0)
A8_LED: D8.2 (A), U2.19 (Q0)
A9: J1.A9, U2.3 (D1)
A9_LED: D7.2 (A), U2.18 (Q1)
A10: J1.A10, U2.4 (D2)
A10_LED: D6.2 (A), U2.17 (Q2)
A11: J1.A11, U2.5 (D3)
A11_LED: D5.2 (A), U2.16 (Q3)
A12: J1.A12, U2.6 (D4)
A12_LED: D4.2 (A), U2.15 (Q4)
A13: J1.A13, U2.7 (D5)
A13_LED: D3.2 (A), U2.14 (Q5)
A14: J1.A14, U2.8 (D6)
A14_LED: D2.2 (A), U2.13 (Q6)
A15: J1.A15, U2.9 (D7)
A15_LED: D1.2 (A), U2.12 (Q7)
BE: J1.BE, U3.9
BE_LED: D29.2 (A), U3.10
D0: J1.D0, U4.2 (D0)
D0_LED: D24.2 (A), U4.19 (Q0)
D1: J1.D1, U4.3 (D1)
D1_LED: D23.2 (A), U4.18 (Q1)
D2: J1.D2, U4.4 (D2)
D2_LED: D22.2 (A), U4.17 (Q2)
D3: J1.D3, U4.5 (D3)
D3_LED: D21.2 (A), U4.16 (Q3)
D4: J1.D4, U4.6 (D4)
D4_LED: D20.2 (A), U4.15 (Q4)
D5: J1.D5, U4.7 (D5)
D5_LED: D19.2 (A), U4.14 (Q5)
D6: J1.D6, U4.8 (D6)
D6_LED: D18.2 (A), U4.13 (Q6)
D7: J1.D7, U4.9 (D7)
D7_LED: D17.2 (A), U4.12 (Q7)
GND: C1.2, C2.2, C3.2, C4.2, J1.GND, R1.1, R2.1, R3.1, R4.1, R5.1, R6.1, R7.1, R8.1, R9.1, R10.1, R11.1, R12.1, R13.1, R14.1, R15.1, R16.1, R17.1, R18.1, R19.1, R20.1, R21.1, R22.1, R23.1, R24.1, R28.1, R29.1, R30.1, R31.1, R32.1, U1.1 (OE), U1.10 (GND), U2.1 (OE), U2.10 (GND), U3.7 (GND), U4.1 (OE), U4.10 (GND)
IRQB: J1.IRQB, R26.1
NMIB: J1.NMIB, R27.1
unnamed: D1.1 (K), R1.2
unnamed: D2.1 (K), R2.2
unnamed: D3.1 (K), R3.2
unnamed: D4.1 (K), R4.2
unnamed: D5.1 (K), R5.2
unnamed: D6.1 (K), R6.2
unnamed: D7.1 (K), R7.2
unnamed: D8.1 (K), R8.2
unnamed: D9.1 (K), R9.2
unnamed: D10.1 (K), R10.2
unnamed: D11.1 (K), R11.2
unnamed: D12.1 (K), R12.2
unnamed: D13.1 (K), R13.2
unnamed: D14.1 (K), R14.2
unnamed: D15.1 (K), R15.2
unnamed: D16.1 (K), R16.2
unnamed: D17.1 (K), R17.2
unnamed: D18.1 (K), R18.2
unnamed: D19.1 (K), R19.2
unnamed: D20.1 (K), R20.2
unnamed: D21.1 (K), R21.2
unnamed: D22.1 (K), R22.2
unnamed: D23.1 (K), R23.2
unnamed: D24.1 (K), R24.2
unnamed: D25.1 (K), R25.2
unnamed: D26.1 (K), R26.2
unnamed: D27.1 (K), R27.2
unnamed: D28.1 (K), R28.2
unnamed: D29.1 (K), R29.2
unnamed: D30.1 (K), R30.2
unnamed: D31.1 (K), R31.2
unnamed: D32.1 (K), R32.2
unnamed: U3.2, U3.3
unnamed: U3.6, U4.11 (Load)
unnamed: U3.8, U3.11
unnamed: U3.5, U3.12
PHI2: D32.2 (A), J1.PHI2, U1.11 (Load), U2.11 (Load), U3.13
RDY: J1.RDY, U3.1
RDY_LED: D28.2 (A), U3.4
RESB: J1.RESB, R25.1
RWB: D30.2 (A), J1.RWB
SYNC: D31.2 (A), J1.SYNC
VCC: C1.1, C2.1, C3.1, C4.1, D25.2 (A), D26.2 (A), D27.2 (A), J1.VCC, U1.20 (VCC), U2.20 (VCC), U3.14 (VCC), U4.20 (VCC)
