acwright/6502/Hardware/Main Board/Rev 1.0/Main Board.kicad_sch

## KiCad design Hardware/Main Board/Rev 1.0/Main Board.kicad_sch (2026-02-01)

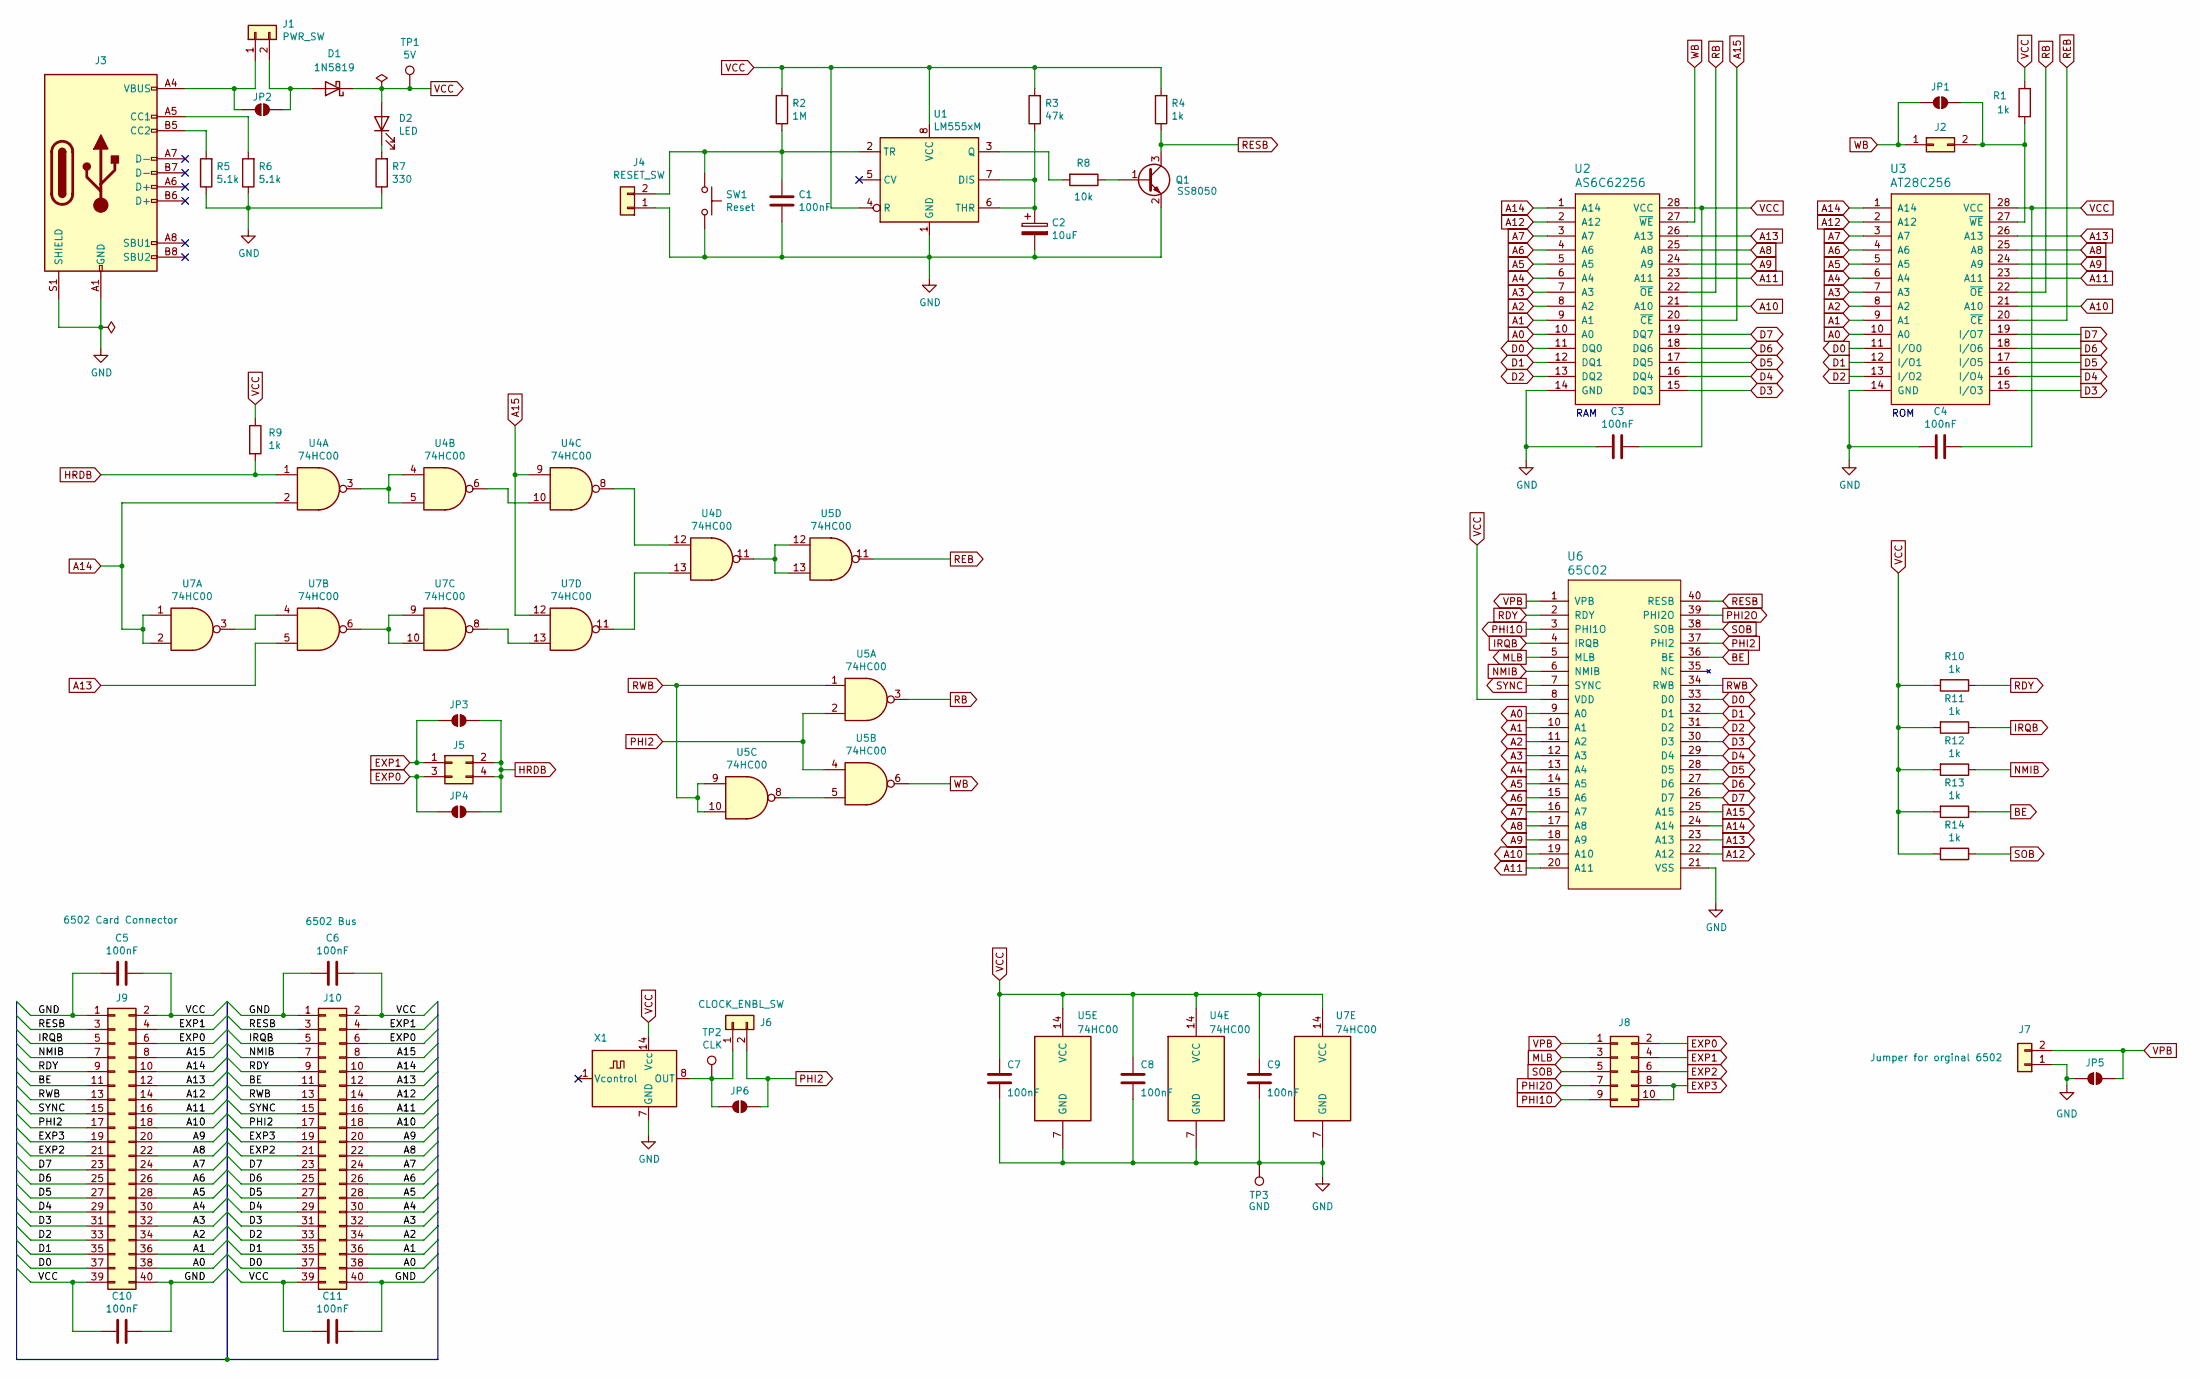
[picture p235: schematic Main Board.kicad_sch]

Parts:
C1, C3, C4, C5, C6, C7, C8, C9, C10, C11: 100nF; C_0805_2012Metric; LCSC C49678
C2: 10uF; C_1206_3216Metric; LCSC C7171
D1: 1N5819; D_SOD-323F; LCSC C191023
D2: LED; LED_0805_2012Metric; LCSC C2297
J1: PWR_SW; JST_XH_B2B-XH-A_1x02_P2.50mm_Vertical; Digikey 455-2247-ND
J2: Conn_02x01; PinHeader_1x02_P2.54mm_Vertical
J3: USB_C_Receptacle_USB2.0; USB_C_Receptacle_HRO_TYPE-C-31-M-12; LCSC C2988369
J4: RESET_SW; JST_XH_B2B-XH-A_1x02_P2.50mm_Vertical; Digikey 455-2247-ND
J5: Conn_02x02_Odd_Even; PinHeader_2x02_P2.54mm_Vertical
J6: CLOCK_ENBL_SW; JST_XH_B2B-XH-A_1x02_P2.50mm_Vertical; Digikey 455-2247-ND
J7: Conn_01x02; PinHeader_1x02_P2.54mm_Vertical
J8: Conn_02x05_Odd_Even; PinHeader_2x05_P2.54mm_Vertical
J9: 6502 Card Connector; RHDR40W82P485X254_2X20_5740X93; Mouser 571-5-5530843-4
J10: 6502 Bus; 6502 Bus Connector
JP1, JP2, JP3, JP4, JP5, JP6: SolderJumper_2_Open; SolderJumper-2_P1.3mm_Open_RoundedPad1.0x1.5mm
Q1: SS8050; SOT-23; LCSC C2150
R1, R4, R9, R10, R11, R12, R13, R14: 1k; R_0805_2012Metric; LCSC C17513
R2: 1M; R_0805_2012Metric; LCSC C17514
R3: 47k; R_0805_2012Metric; LCSC C17713
R5, R6: 5.1k; R_0805_2012Metric; LCSC C27834
R7: 330; R_0805_2012Metric; LCSC C17630
R8: 10k; R_0805_2012Metric; LCSC C17414
SW1: Reset; SW_TS-1187A-B-A-B; LCSC C318884
TP1: 5V; TestPoint_Pad_1.0x1.0mm
TP2: CLK; TestPoint_Pad_1.0x1.0mm
TP3: GND; TestPoint_Pad_1.0x1.0mm
U1: LM555xM; SOIC-8_3.9x4.9mm_P1.27mm; LCSC C7593
U2: AS6C62256; DIP-28_W15.24mm_Socket_LongPads
U3: AT28C256; DIP_Socket-28_W11.9_W12.7_W15.24_W17.78_W18.5_3M_228-1277-0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
U4, U5, U7: 74HC00; SOIC-14_3.9x8.7mm_P1.27mm; LCSC C5586
U6: 65C02; DIP-40_W15.24mm_Socket_LongPads
X1: OCXO-14; Oscillator_DIP-14

Connections:
A0: J9.38, J10.38, U2.10 (A0), U3.10 (A0), U6.9 (A0)
A1: J9.36, J10.36, U2.9 (A1), U3.9 (A1), U6.10 (A1)
A2: J9.34, J10.34, U2.8 (A2), U3.8 (A2), U6.11 (A2)
A3: J9.32, J10.32, U2.7 (A3), U3.7 (A3), U6.12 (A3)
A4: J9.30, J10.30, U2.6 (A4), U3.6 (A4), U6.13 (A4)
A5: J9.28, J10.28, U2.5 (A5), U3.5 (A5), U6.14 (A5)
A6: J9.26, J10.26, U2.4 (A6), U3.4 (A6), U6.15 (A6)
A7: J9.24, J10.24, U2.3 (A7), U3.3 (A7), U6.16 (A7)
A8: J9.22, J10.22, U2.25 (A8), U3.25 (A8), U6.17 (A8)
A9: J9.20, J10.20, U2.24 (A9), U3.24 (A9), U6.18 (A9)
A10: J9.18, J10.18, U2.21 (A10), U3.21 (A10), U6.19 (A10)
A11: J9.16, J10.16, U2.23 (A11), U3.23 (A11), U6.20 (A11)
A12: J9.14, J10.14, U2.2 (A12), U3.2 (A12), U6.22 (A12)
A13: J9.12, J10.12, U2.26 (A13), U3.26 (A13), U6.23 (A13), U7.5
A14: J9.10, J10.10, U2.1 (A14), U3.1 (A14), U4.2, U6.24 (A14), U7.1, U7.2
A15: J9.8, J10.8, U2.20 (~CE), U4.9, U6.25 (A15), U7.12
BE: J9.11, J10.11, R13.1, U6.36 (BE)
D0: J9.37, J10.37, U2.11 (DQ0), U3.11 (I/O0), U6.33 (D0)
D1: J9.35, J10.35, U2.12 (DQ1), U3.12 (I/O1), U6.32 (D1)
D2: J9.33, J10.33, U2.13 (DQ2), U3.13 (I/O2), U6.31 (D2)
D3: J9.31, J10.31, U2.15 (DQ3), U3.15 (I/O3), U6.30 (D3)
D4: J9.29, J10.29, U2.16 (DQ4), U3.16 (I/O4), U6.29 (D4)
D5: J9.27, J10.27, U2.17 (DQ5), U3.17 (I/O5), U6.28 (D5)
D6: J9.25, J10.25, U2.18 (DQ6), U3.18 (I/O6), U6.27 (D6)
D7: J9.23, J10.23, U2.19 (DQ7), U3.19 (I/O7), U6.26 (D7)
EXP0: J5.3, J8.2, J9.6, J10.6, JP4.1 (A)
EXP1: J5.1, J8.4, J9.4, J10.4, JP3.1 (A)
EXP2: J8.6, J9.21, J10.21
EXP3: J8.8, J8.10, J9.19, J10.19
GND: C1.2, C2.2, C3.2, C4.2, C5.2, C6.2, C7.2, C8.2, C9.2, C10.1, C11.1, J3.A1 (GND), J3.A12 (GND), J3.B1 (GND), J3.B12 (GND), J3.S1 (SHIELD), J4.1, J7.1, J9.1, J9.40, J10.1, J10.40, JP5.1 (A), Q1.2 (E), R5.1, R6.1, R7.1, SW1.2, TP3.1, U1.1 (GND), U2.14 (GND), U3.14 (GND), U4.7 (GND), U5.7 (GND), U6.21 (VSS), U7.7 (GND), X1.7 (GND)
HRDB: J5.2, J5.4, JP3.2 (B), JP4.2 (B), R9.2, U4.1
IRQB: J9.5, J10.5, R11.1, U6.4 (IRQB)
MLB: J8.3, U6.5 (MLB)
NMIB: J9.7, J10.7, R12.1, U6.6 (NMIB)
unnamed: C1.1, J4.2, R2.1, SW1.1, U1.2 (TR)
unnamed: C2.1, R3.1, U1.6 (THR), U1.7 (DIS)
unnamed: D1.2 (A), J1.2, JP2.2 (B)
unnamed: D2.1 (K), R7.2
unnamed: J1.1, J3.A4 (VBUS), J3.A9 (VBUS), J3.B4 (VBUS), J3.B9 (VBUS), JP2.1 (A)
unnamed: J2.2, JP1.2 (B), R1.2, U3.27 (~WE)
unnamed: J3.A5 (CC1), R6.2
unnamed: J3.B5 (CC2), R5.2
unnamed: J6.1, JP6.1 (A), TP2.1, X1.8 (OUT)
unnamed: Q1.1 (B), R8.1
unnamed: R8.2, U1.3 (Q)
unnamed: U4.3, U4.4, U4.5
unnamed: U4.6, U4.10
unnamed: U4.11, U5.12, U5.13
unnamed: U4.8, U4.12
unnamed: U4.13, U7.11
unnamed: U5.5, U5.8
unnamed: U7.3, U7.4
unnamed: U7.6, U7.9, U7.10
unnamed: U7.8, U7.13
PHI1O: J8.9, U6.3 (PHI1O)
PHI2: J6.2, J9.17, J10.17, JP6.2 (B), U5.2, U5.4, U6.37 (PHI2)
PHI2O: J8.7, U6.39 (PHI2O)
RB: U2.22 (~OE), U3.22 (~OE), U5.3
RDY: J9.9, J10.9, R10.1, U6.2 (RDY)
REB: U3.20 (~CE), U5.11
RESB: J9.3, J10.3, Q1.3 (C), R4.1, U6.40 (RESB)
RWB: J9.13, J10.13, U5.1, U5.9, U5.10, U6.34 (RWB)
SOB: J8.5, R14.1, U6.38 (SOB)
SYNC: J9.15, J10.15, U6.7 (SYNC)
VCC: C3.1, C4.1, C5.1, C6.1, C7.1, C8.1, C9.1, C10.2, C11.2, D1.1 (K), D2.2 (A), J9.2, J9.39, J10.2, J10.39, R1.1, R2.2, R3.2, R4.2, R9.1, R10.2, R11.2, R12.2, R13.2, R14.2, TP1.1, U1.4 (R), U1.8 (VCC), U2.28 (VCC), U3.28 (VCC), U4.14 (VCC), U5.14 (VCC), U6.8 (VDD), U7.14 (VCC), X1.14 (Vcc)
VPB: J7.2, J8.1, JP5.2 (B), U6.1 (VPB)
WB: J2.1, JP1.1 (A), U2.27 (~WE), U5.6

Notes on the sheet:
ROM
RAM
