acwright/6502/Hardware/Storage Card/Rev 1.0/Storage Card.kicad_sch

## KiCad design Hardware/Storage Card/Rev 1.0/Storage Card.kicad_sch (2025-09-29)

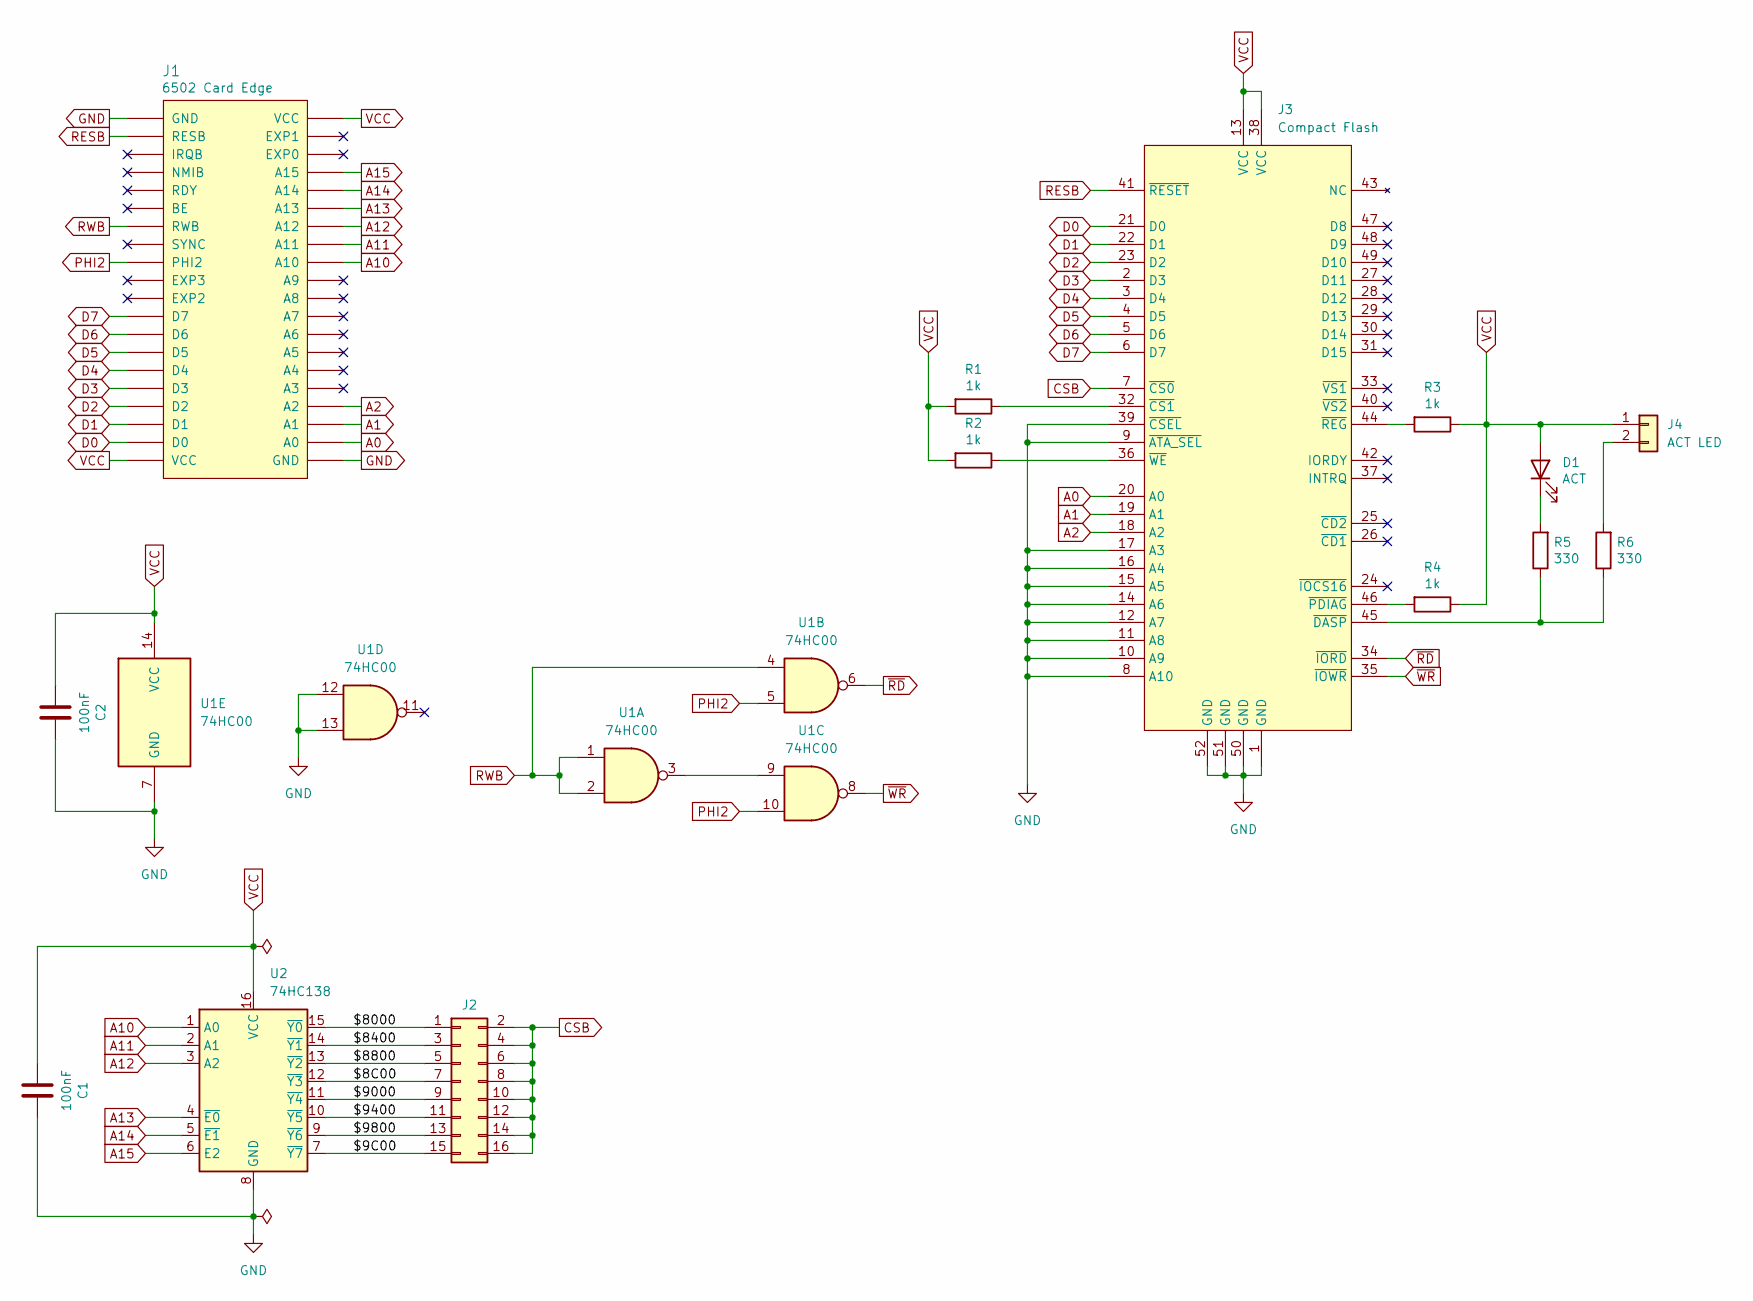
[picture p238: schematic Storage Card.kicad_sch]

Parts:
C1, C2: 100nF; C_0805_2012Metric; LCSC C49678
D1: ACT; LED_0805_2012Metric; LCSC C2297
J1: 6502 Card Edge
J2: Conn_02x08_Odd_Even; PinHeader_2x08_P2.54mm_Vertical
J3: Compact Flash; SD-SMD_CFH-L3C1LBL01MN0; LCSC C444350
J4: ACT LED; JST_XH_B2B-XH-A_1x02_P2.50mm_Vertical
R1, R2, R3, R4: 1k; R_0805_2012Metric; LCSC C17513
R5, R6: 330; R_0805_2012Metric; LCSC C17630
U1: 74HC00; SOIC-14_3.9x8.7mm_P1.27mm; LCSC C5586
U2: 74HC138; SOIC-16_3.9x9.9mm_P1.27mm; LCSC C5602

Connections:
$8C00: J2.7, U2.12 (~Y3)
$9C00: J2.15, U2.7 (~Y7)
$8000: J2.1, U2.15 (~Y0)
$8400: J2.3, U2.14 (~Y1)
$8800: J2.5, U2.13 (~Y2)
$9000: J2.9, U2.11 (~Y4)
$9400: J2.11, U2.10 (~Y5)
$9800: J2.13, U2.9 (~Y6)
A0: J1.A0, J3.20 (A0)
A1: J1.A1, J3.19 (A1)
A2: J1.A2, J3.18 (A2)
A10: J1.A10, U2.1 (A0)
A11: J1.A11, U2.2 (A1)
A12: J1.A12, U2.3 (A2)
A13: J1.A13, U2.4 (~E0)
A14: J1.A14, U2.5 (~E1)
A15: J1.A15, U2.6 (E2)
CSB: J2.2, J2.4, J2.6, J2.8, J2.10, J2.12, J2.14, J2.16, J3.7 (~CS0)
D0: J1.D0, J3.21 (D0)
D1: J1.D1, J3.22 (D1)
D2: J1.D2, J3.23 (D2)
D3: J1.D3, J3.2 (D3)
D4: J1.D4, J3.3 (D4)
D5: J1.D5, J3.4 (D5)
D6: J1.D6, J3.5 (D6)
D7: J1.D7, J3.6 (D7)
GND: C1.2, C2.2, J1.GND, J3.1 (GND), J3.8 (A10), J3.9 (~ATA_SEL), J3.10 (A9), J3.11 (A8), J3.12 (A7), J3.14 (A6), J3.15 (A5), J3.16 (A4), J3.17 (A3), J3.39 (~CSEL), J3.50 (GND), J3.51 (GND), J3.52 (GND), U1.7 (GND), U1.12, U1.13, U2.8 (GND)
unnamed: D1.1 (K), R5.2
unnamed: J3.32 (~CS1), R1.1
unnamed: J3.36 (~WE), R2.1
unnamed: J3.44 (~REG), R3.2
unnamed: J3.45 (~DASP), R5.1, R6.1
unnamed: J3.46 (~PDIAG), R4.2
unnamed: J4.2, R6.2
unnamed: U1.3, U1.9
PHI2: J1.PHI2, U1.5, U1.10
RESB: J1.RESB, J3.41 (~RESET)
RWB: J1.RWB, U1.1, U1.2, U1.4
VCC: C1.1, C2.1, D1.2 (A), J1.VCC, J3.13 (VCC), J3.38 (VCC), J4.1, R1.2, R2.2, R3.1, R4.1, U1.14 (VCC), U2.16 (VCC)
~RD: J3.34 (~IORD), U1.6
~WR: J3.35 (~IOWR), U1.8
