acwright/6502/Firmware/DB1 Emulator/src/rtc.cpp

#include "rtc.h"

namespace RTC {

  void begin() {
    setSyncProvider(syncTime);
  }

  void update() { /* Do nothing... */ }

  byte read(byte reg) {
    time_t time = now();

    switch(reg) {
    case RTC_SEC:
      return byte(second(time));
    case RTC_MIN:
      return byte(minute(time));
    case RTC_HR:
      return byte(hour(time));
    case RTC_DAY:
      return byte(day(time));
    case RTC_MON:
      return byte(month(time));
    case RTC_YR:
      return byte(year(time) - 1970); // Offset from 1970 (0-99)
    default:
      return 0;
    }
  }

  void write(byte reg, byte data) { /* Do nothing... RTC registers are read-only. */ }

  String formattedDateTime() {
    String time;

    time.append(month());
    time.append("/");
    time.append(day());
    time.append("/");
    time.append(year());
    time.append(" ");
    time.append(hour());
    time.append(":");
    time.append(minute() < 10 ? "0": "");
    time.append(minute());
    time.append(":");
    time.append(second() < 10 ? "0": "");
    time.append(second());

    return time;
  }

  time_t syncTime() {
    return Teensy3Clock.get();
  }

}
